chiangr/bingbong/firmware/bingbong_pcb/_bg95_pinout.png

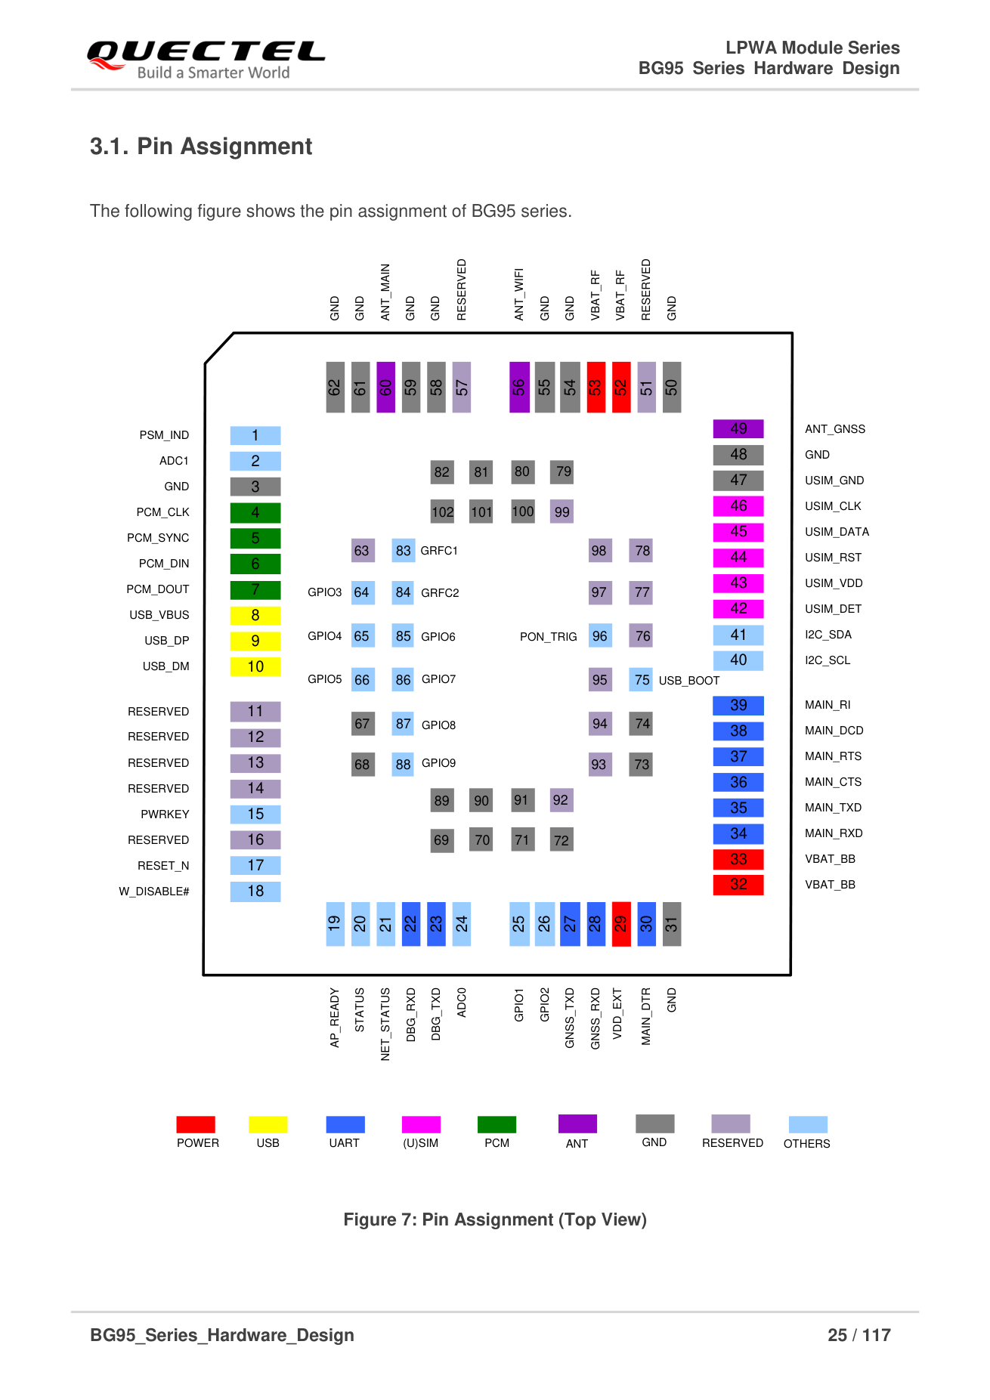
firmware/bingbong_pcb/_bg95_pinout.png
