chiangr/bingbong/firmware/bingbong_pcb/_dfe_land.png

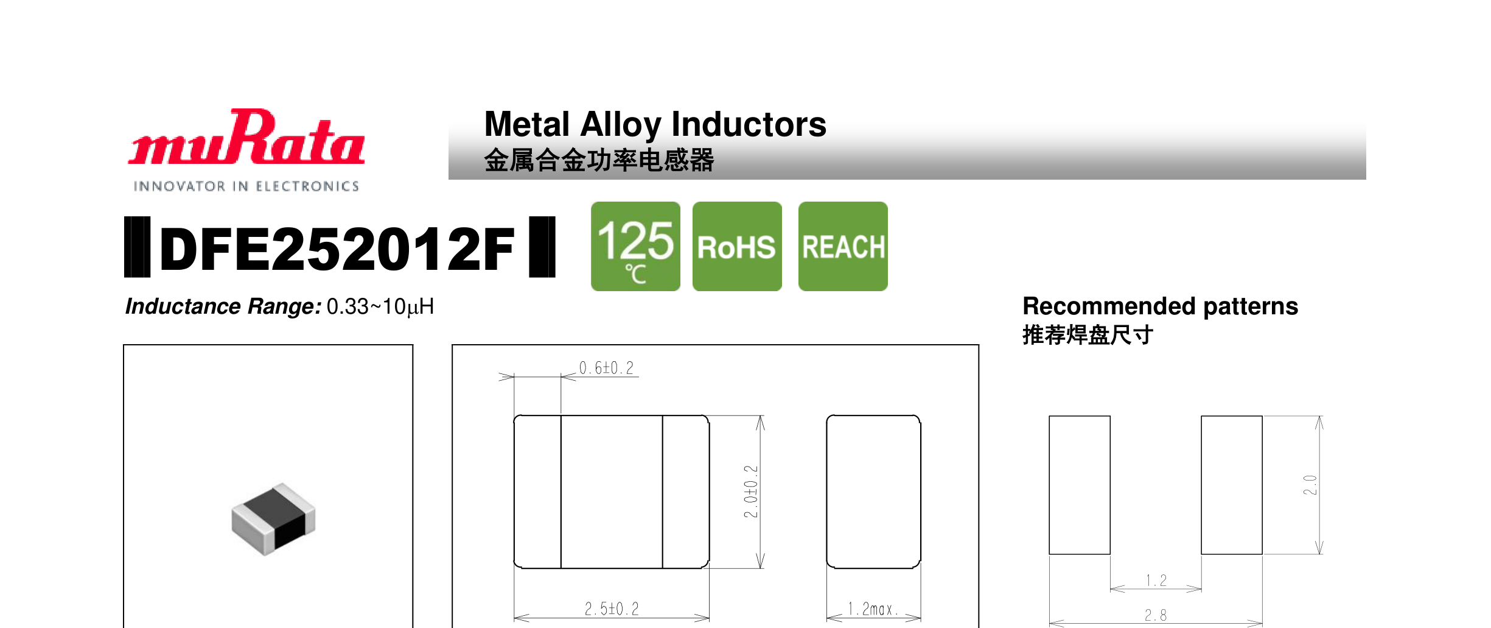
firmware/bingbong_pcb/_dfe_land.png
