chiangr/bingbong/firmware/bingbong_pcb/_esp_land.png

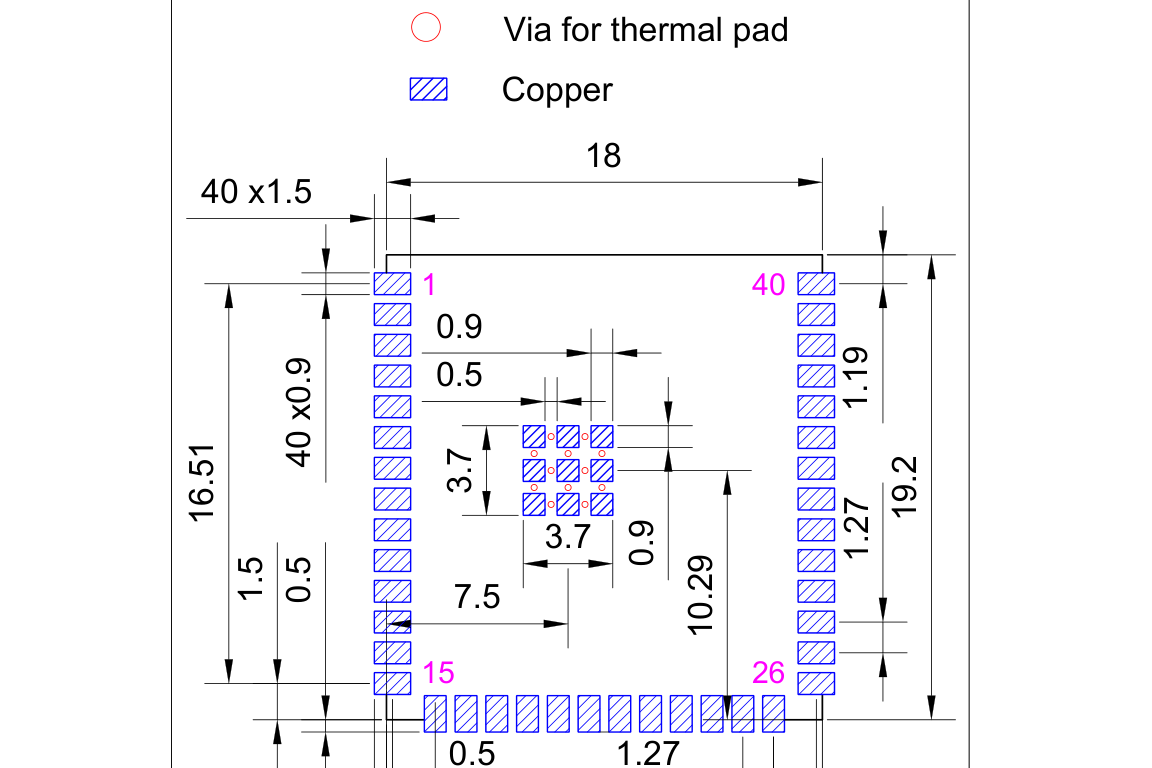
firmware/bingbong_pcb/_esp_land.png
