chiangr/bingbong/firmware/bingbong_pcb/_mech/a35s-07.png

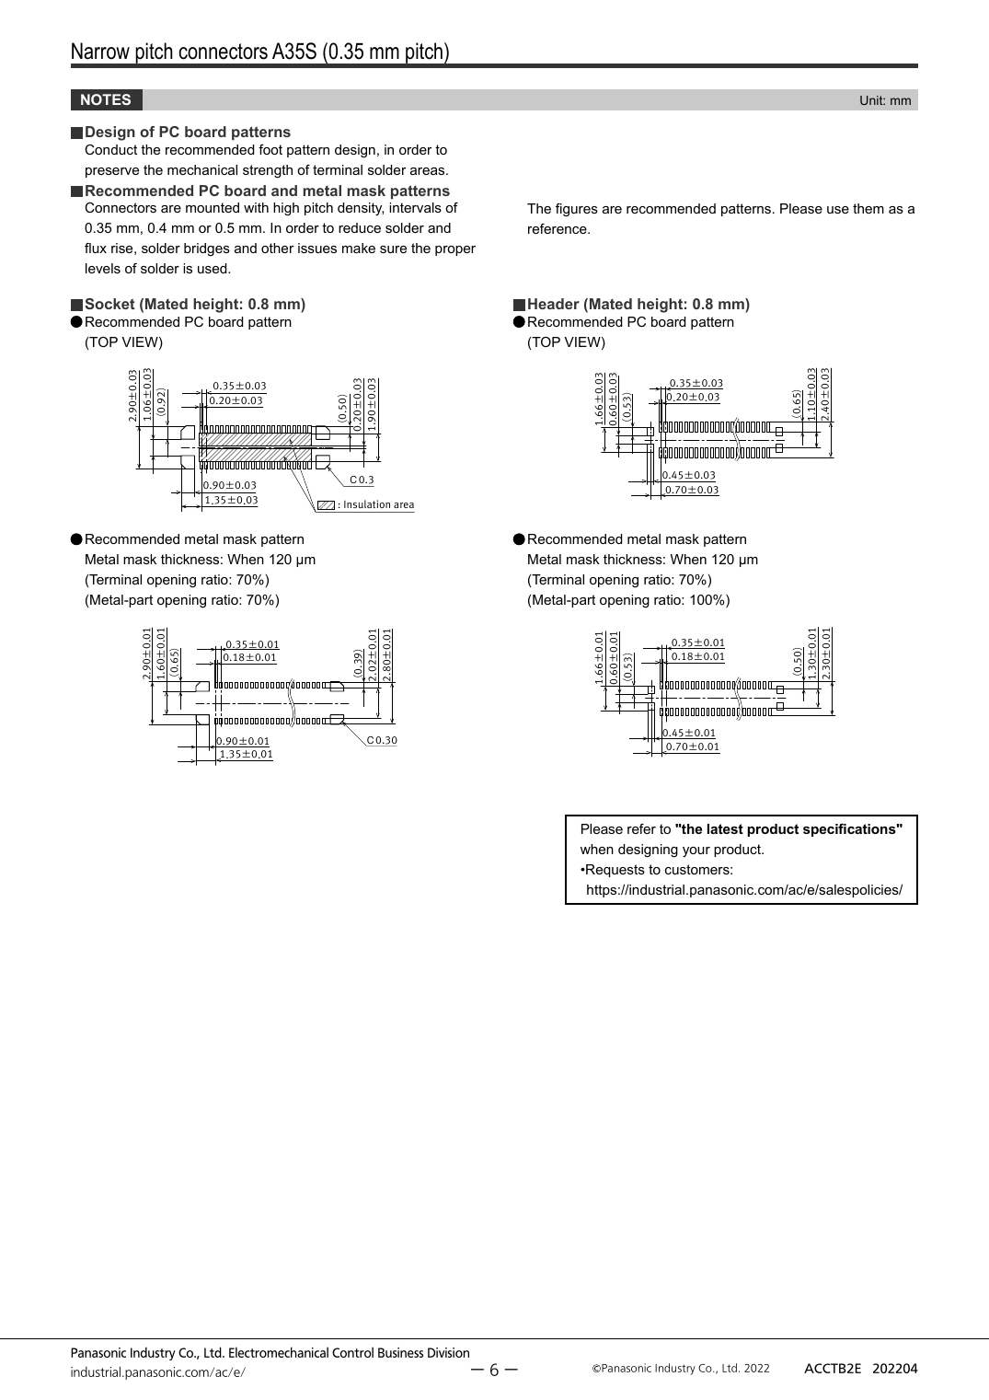
firmware/bingbong_pcb/_mech/a35s-07.png
