chiangr/bingbong/firmware/bingbong_pcb/_mech/bm28-04.png

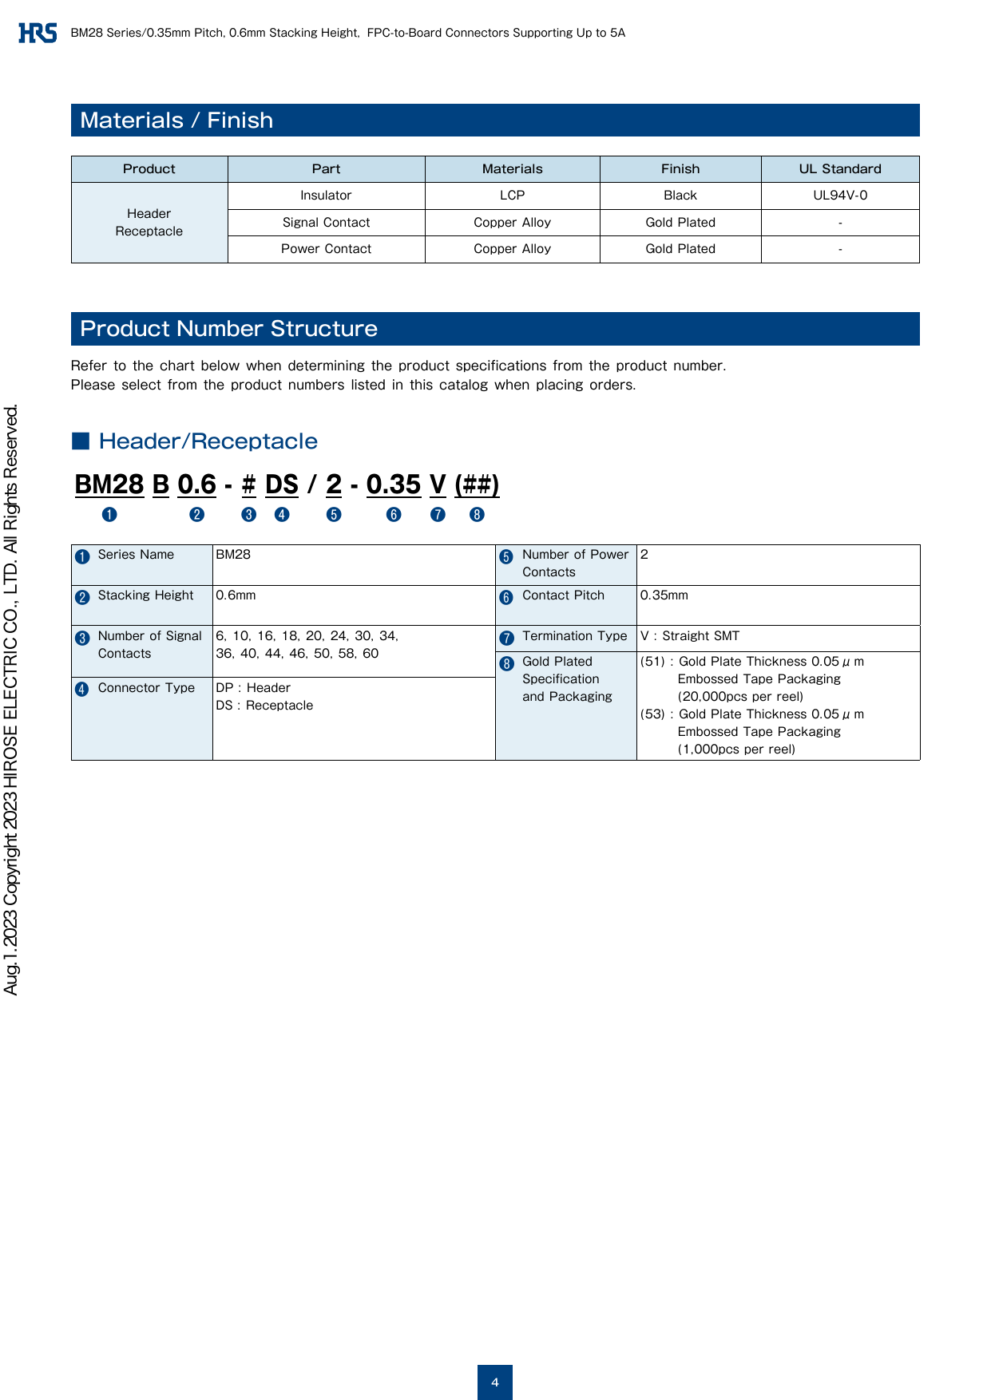
firmware/bingbong_pcb/_mech/bm28-04.png
