chiangr/bingbong/firmware/bingbong_pcb/_mech/bm28-05.png

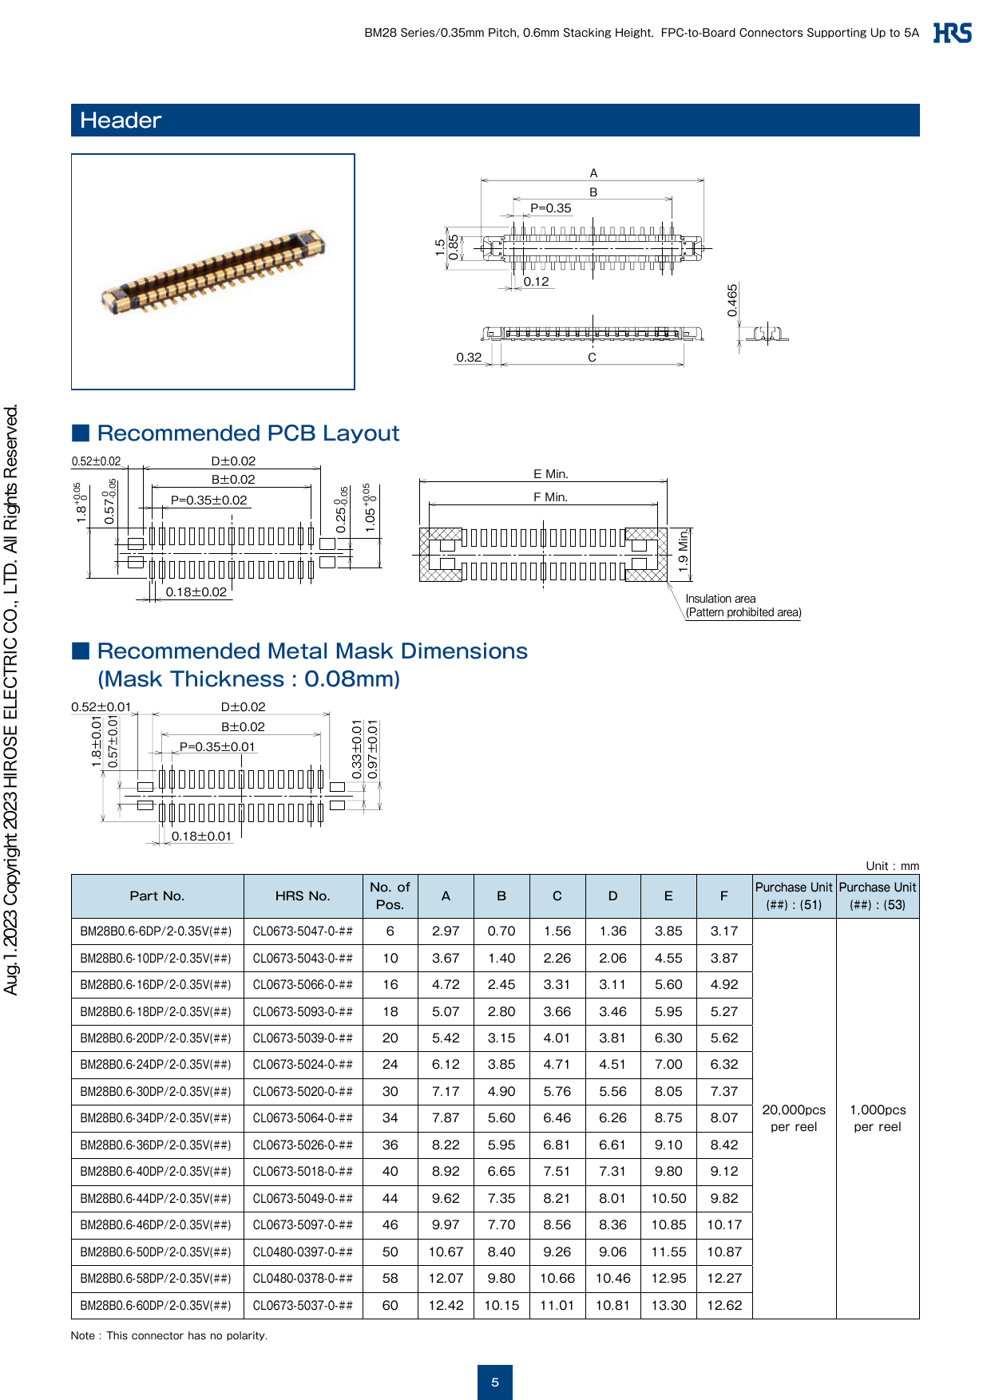
firmware/bingbong_pcb/_mech/bm28-05.png
