chiangr/bingbong/firmware/bingbong_pcb/_mech/ck/p4-4.png

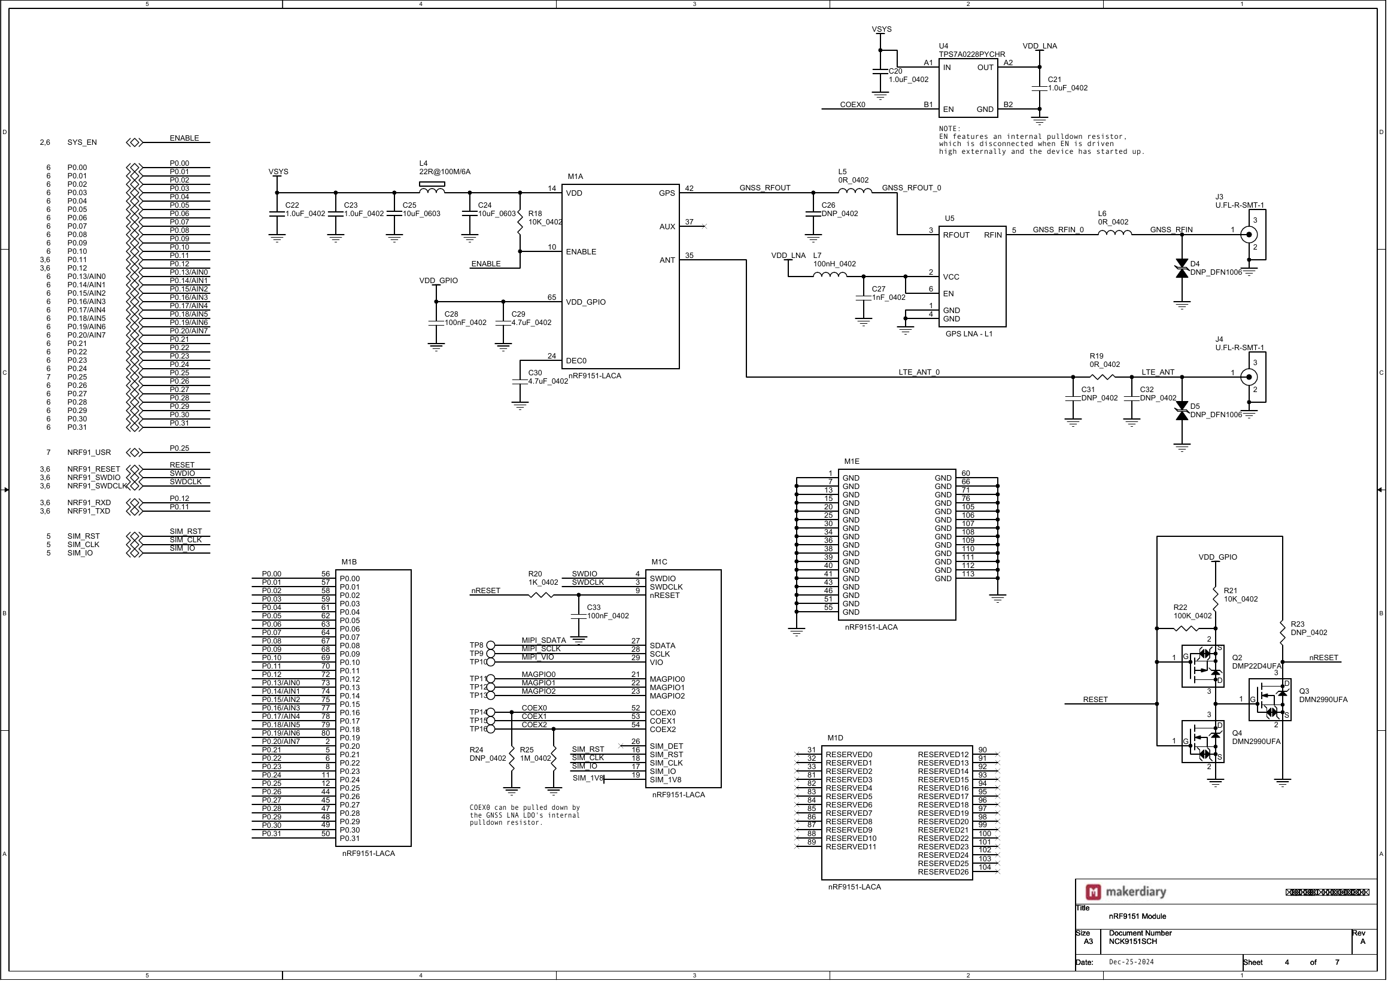
firmware/bingbong_pcb/_mech/ck/p4-4.png
