chiangr/bingbong/firmware/bingbong_pcb/_mech/etsi-mff2-16.png

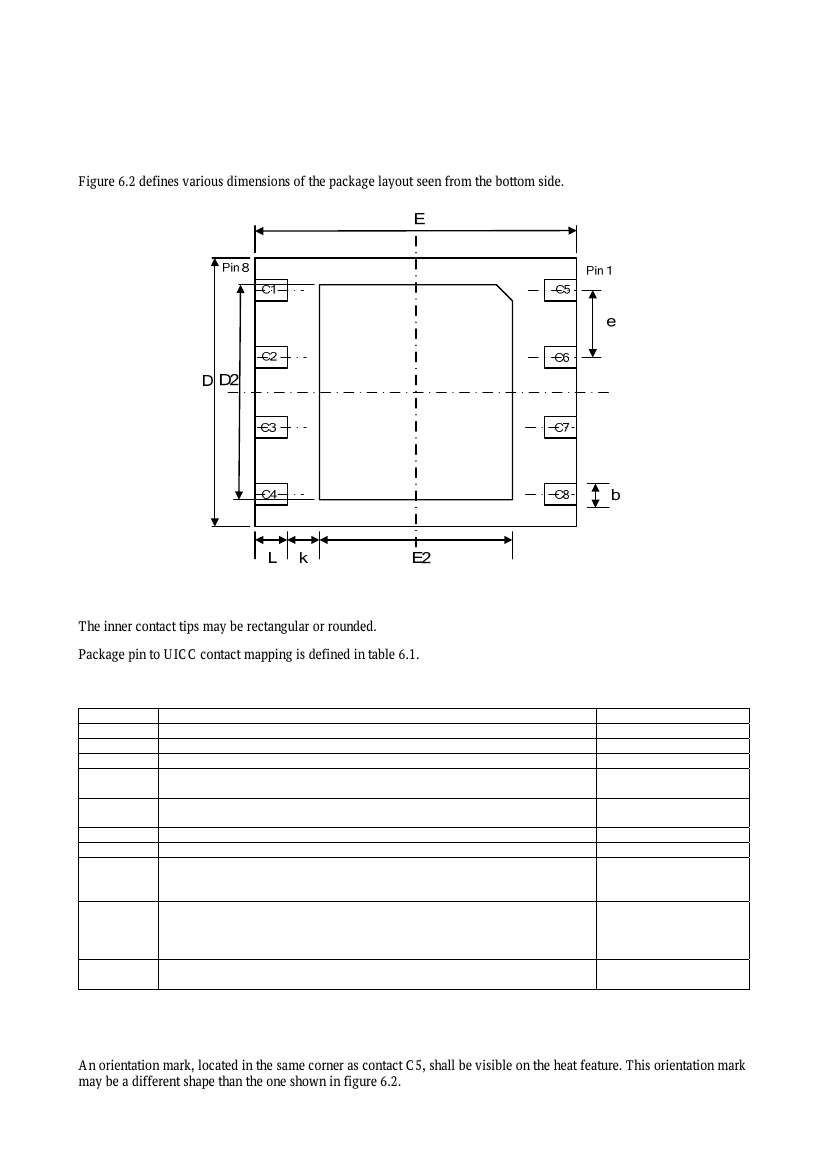
firmware/bingbong_pcb/_mech/etsi-mff2-16.png
