chiangr/bingbong/firmware/bingbong_pcb/_mech/etsi-mff2-19.png

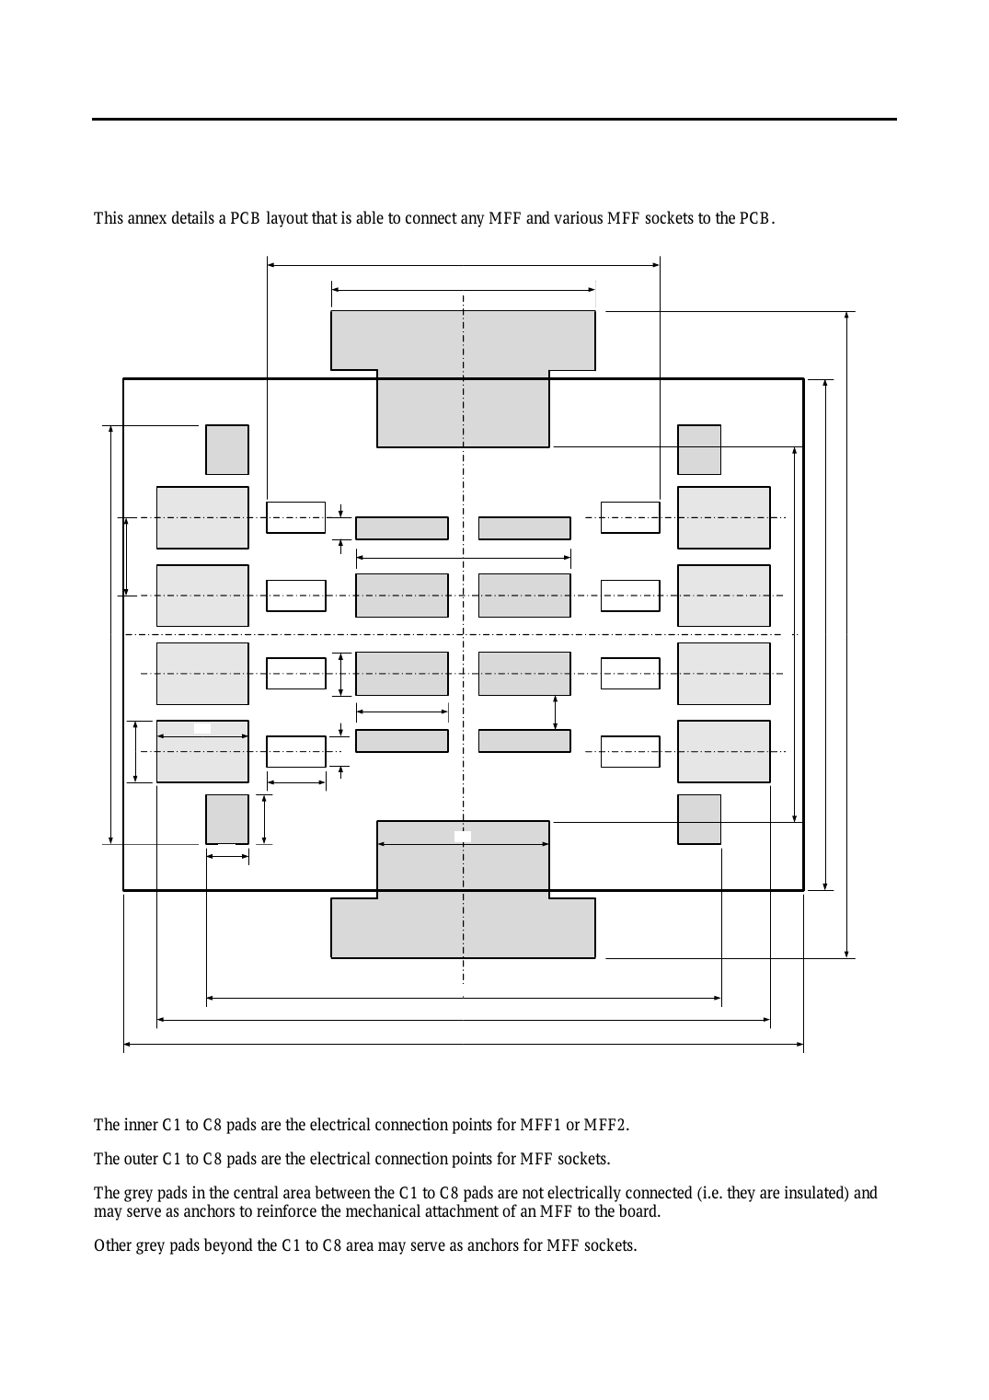
firmware/bingbong_pcb/_mech/etsi-mff2-19.png
