chiangr/bingbong/firmware/bingbong_pcb/_mech/fp/bq-51.png

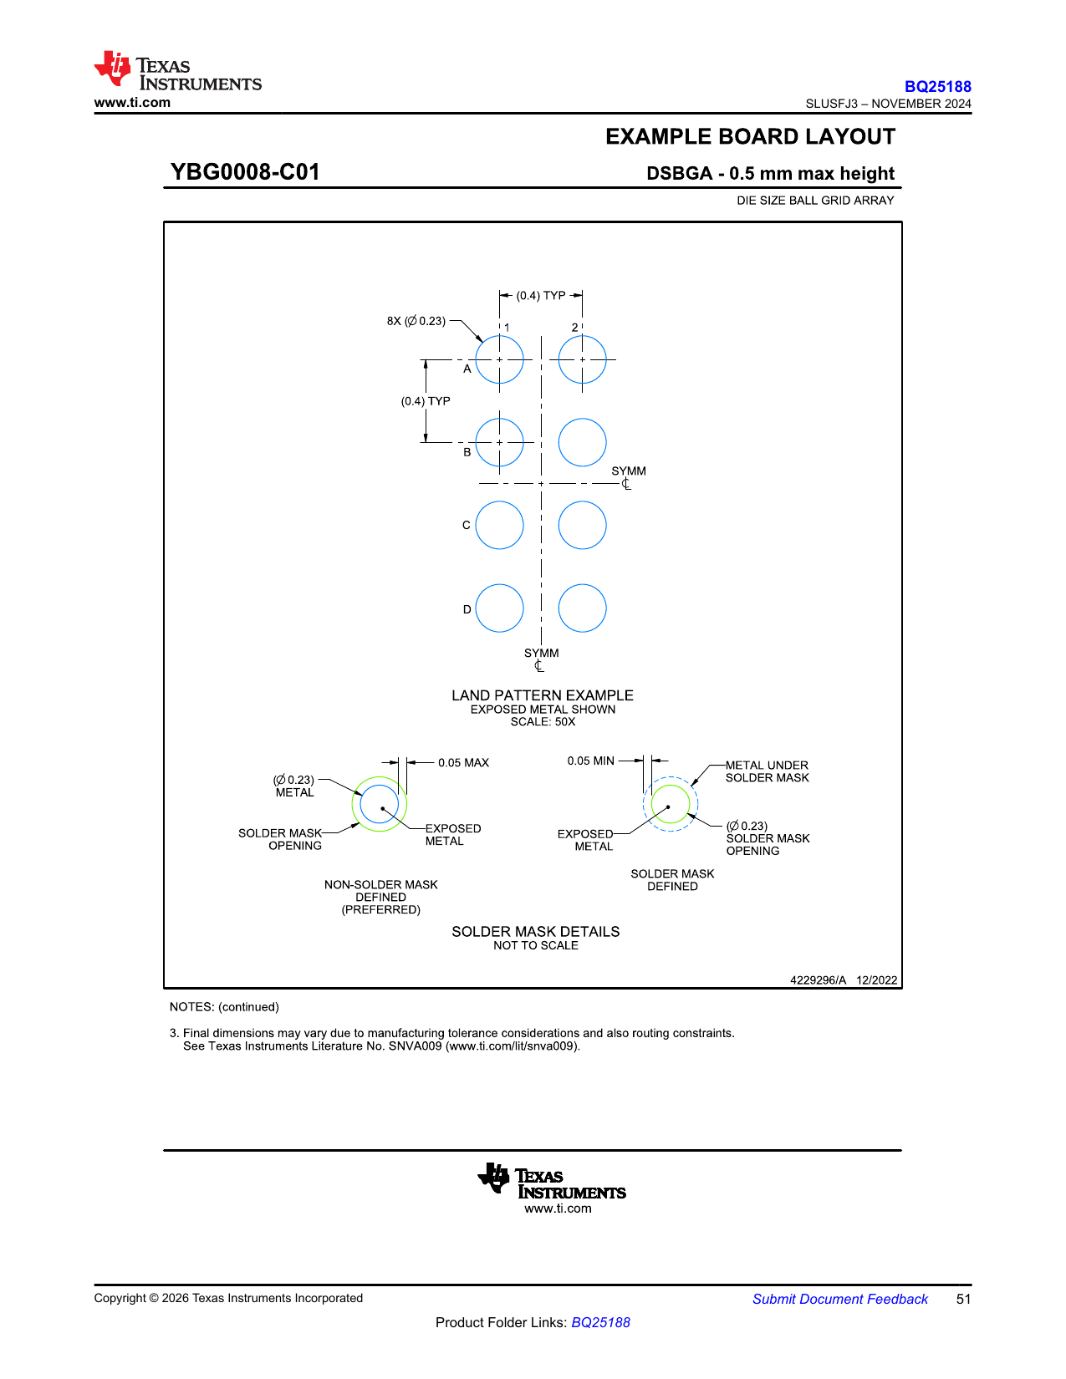
firmware/bingbong_pcb/_mech/fp/bq-51.png
