chiangr/bingbong/firmware/bingbong_pcb/_mech/fp/bq-52.png

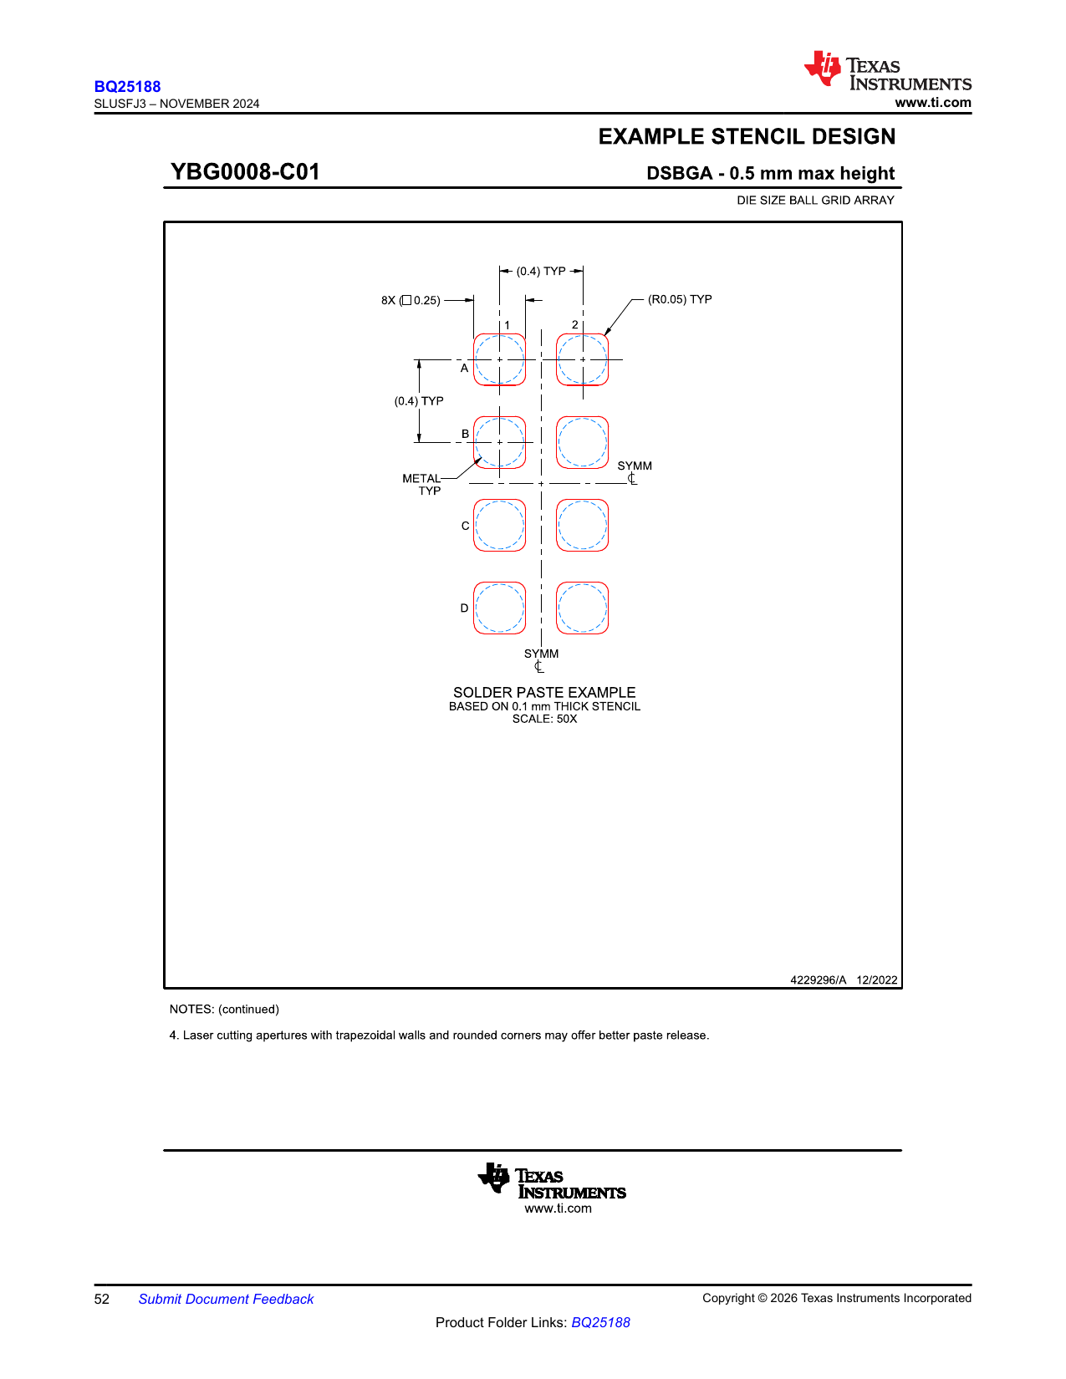
firmware/bingbong_pcb/_mech/fp/bq-52.png
