chiangr/bingbong/firmware/bingbong_pcb/_mech/fp/dmr-35.png

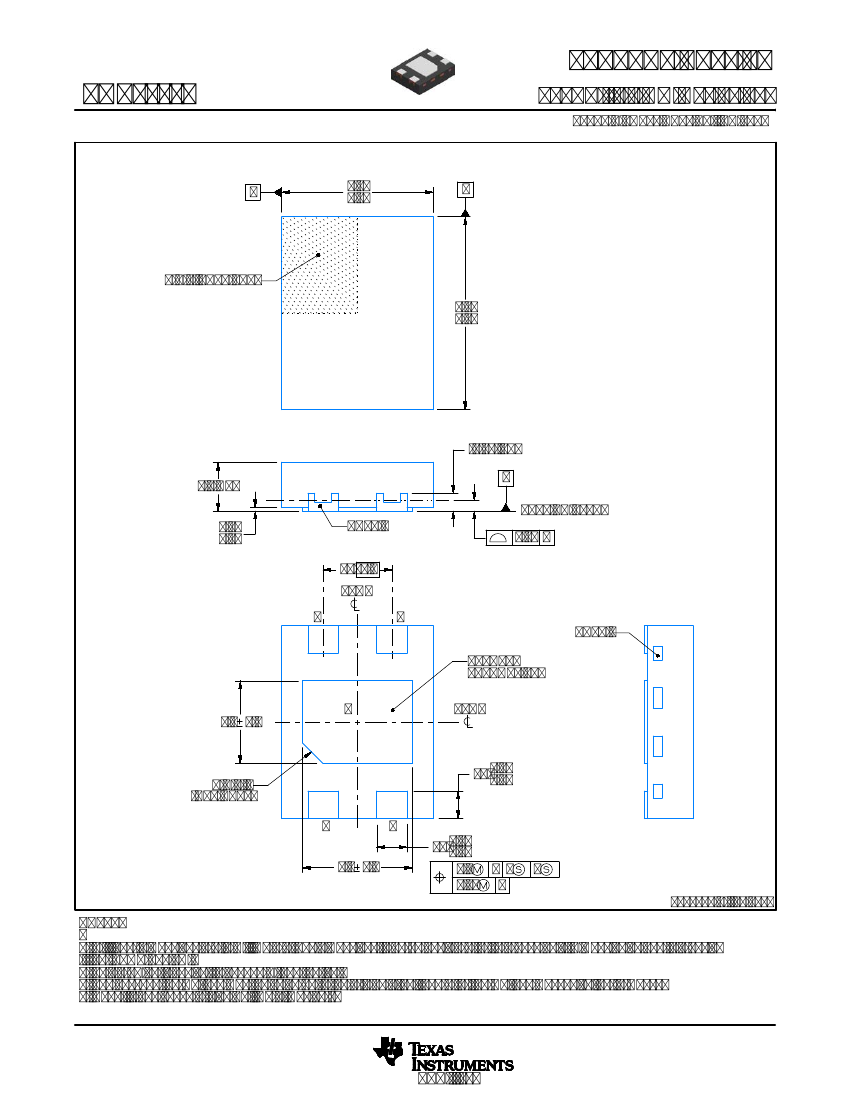
firmware/bingbong_pcb/_mech/fp/dmr-35.png
