chiangr/bingbong/firmware/bingbong_pcb/_mech/fp/dmr-38.png

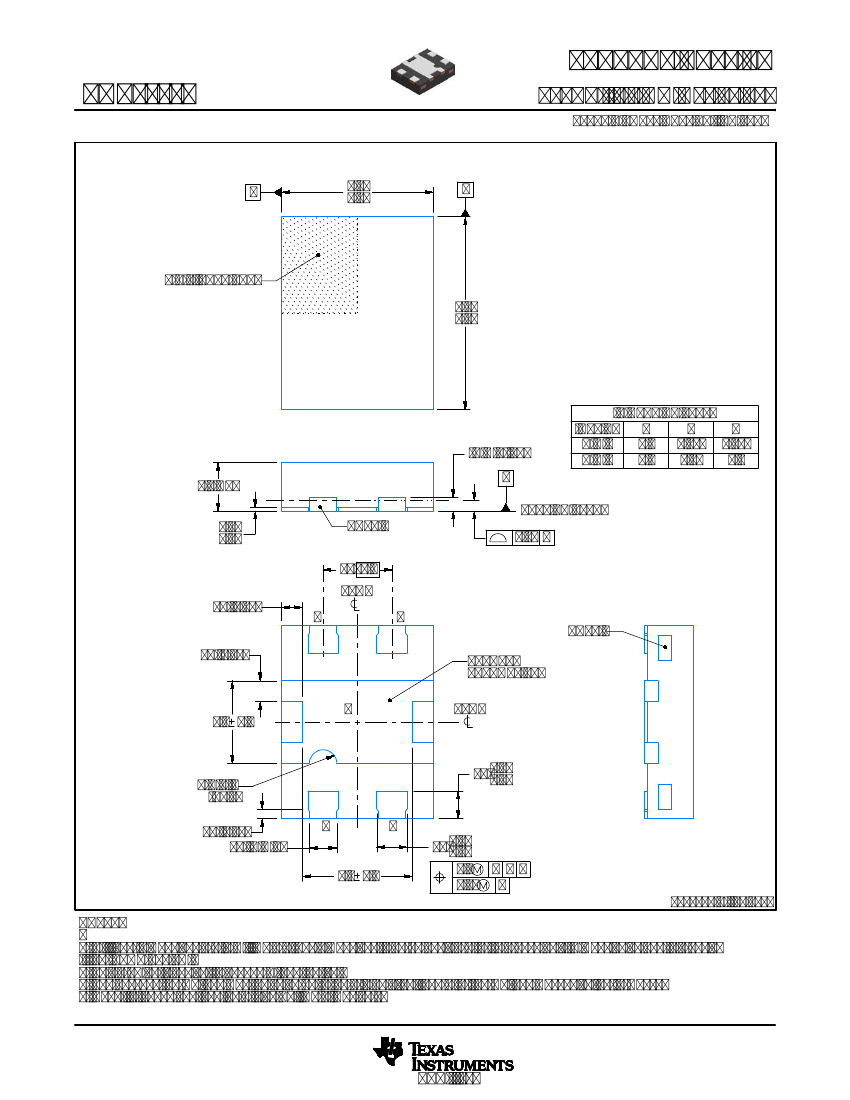
firmware/bingbong_pcb/_mech/fp/dmr-38.png
