chiangr/bingbong/firmware/bingbong_pcb/_mech/fp/dmr-40.png

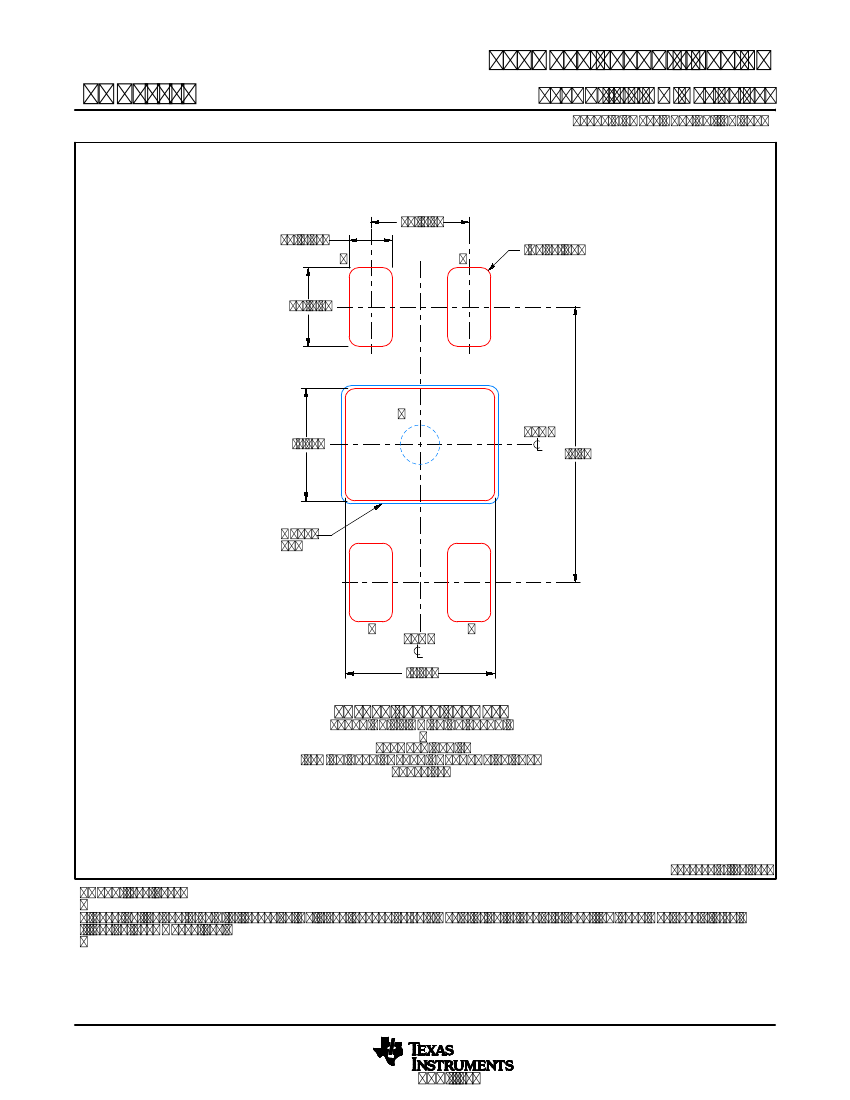
firmware/bingbong_pcb/_mech/fp/dmr-40.png
