chiangr/bingbong/firmware/bingbong_pcb/_mech/fp/dmr-41.png

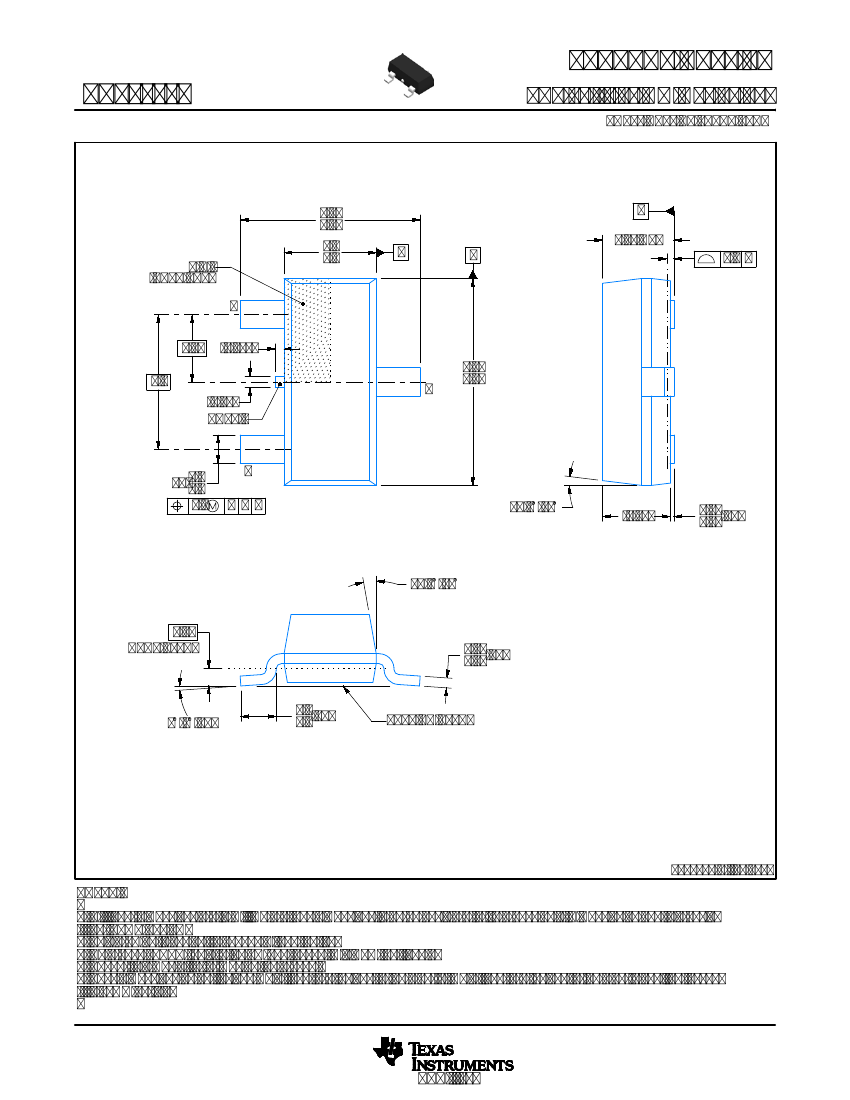
firmware/bingbong_pcb/_mech/fp/dmr-41.png
