chiangr/bingbong/firmware/bingbong_pcb/_mech/fp/drv-72.png

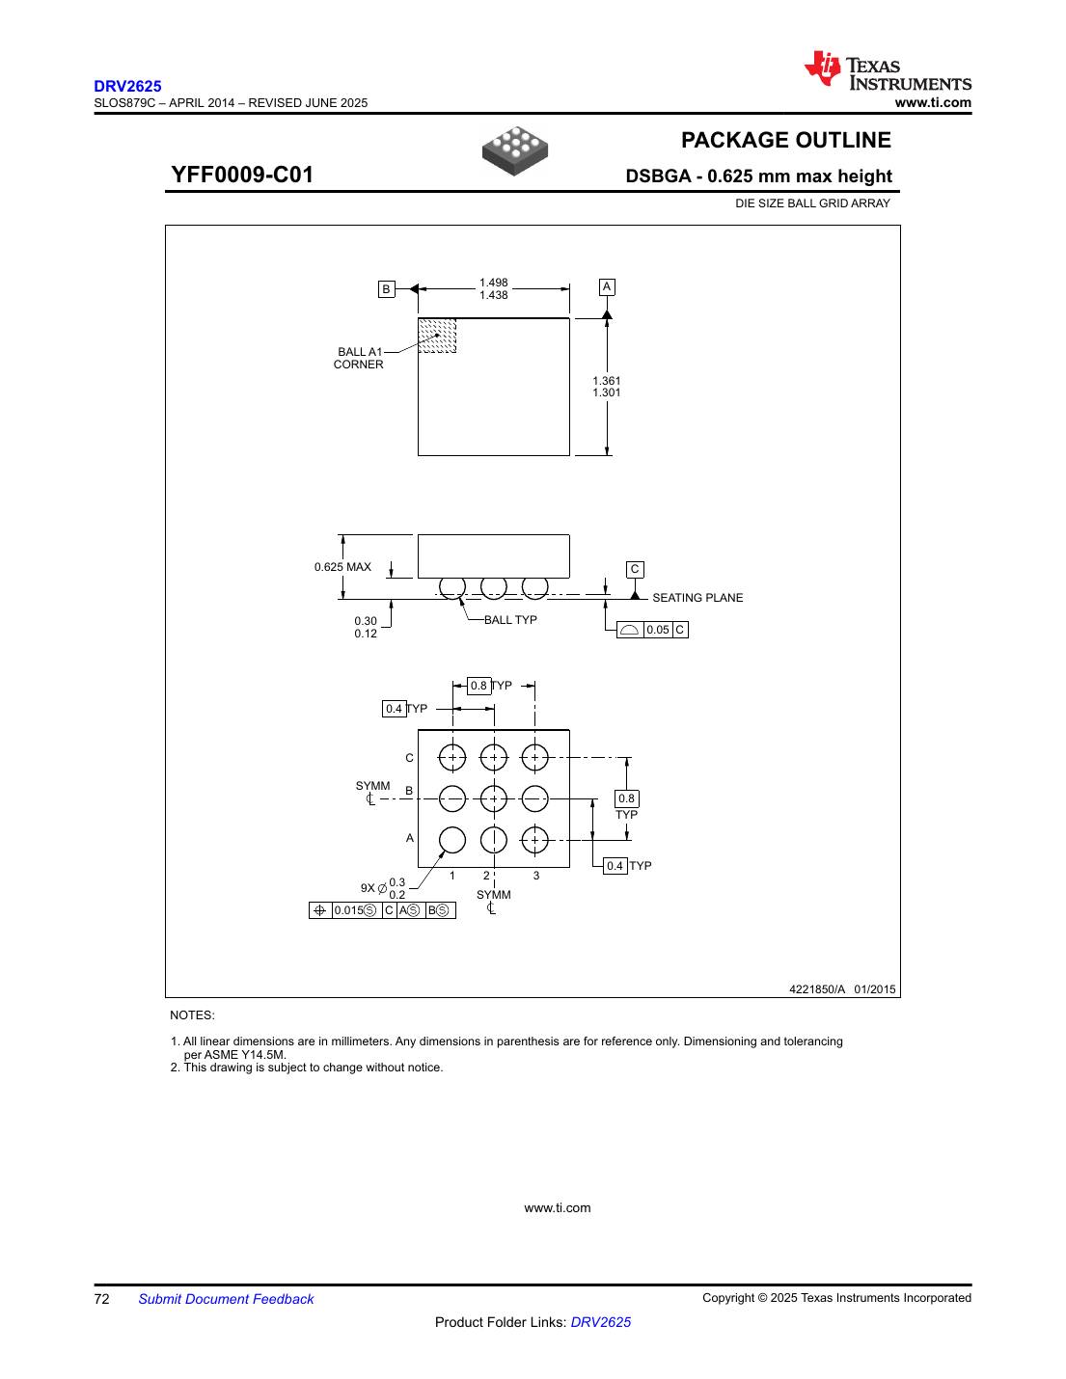
firmware/bingbong_pcb/_mech/fp/drv-72.png
