chiangr/bingbong/firmware/bingbong_pcb/_mech/fp/drv-73.png

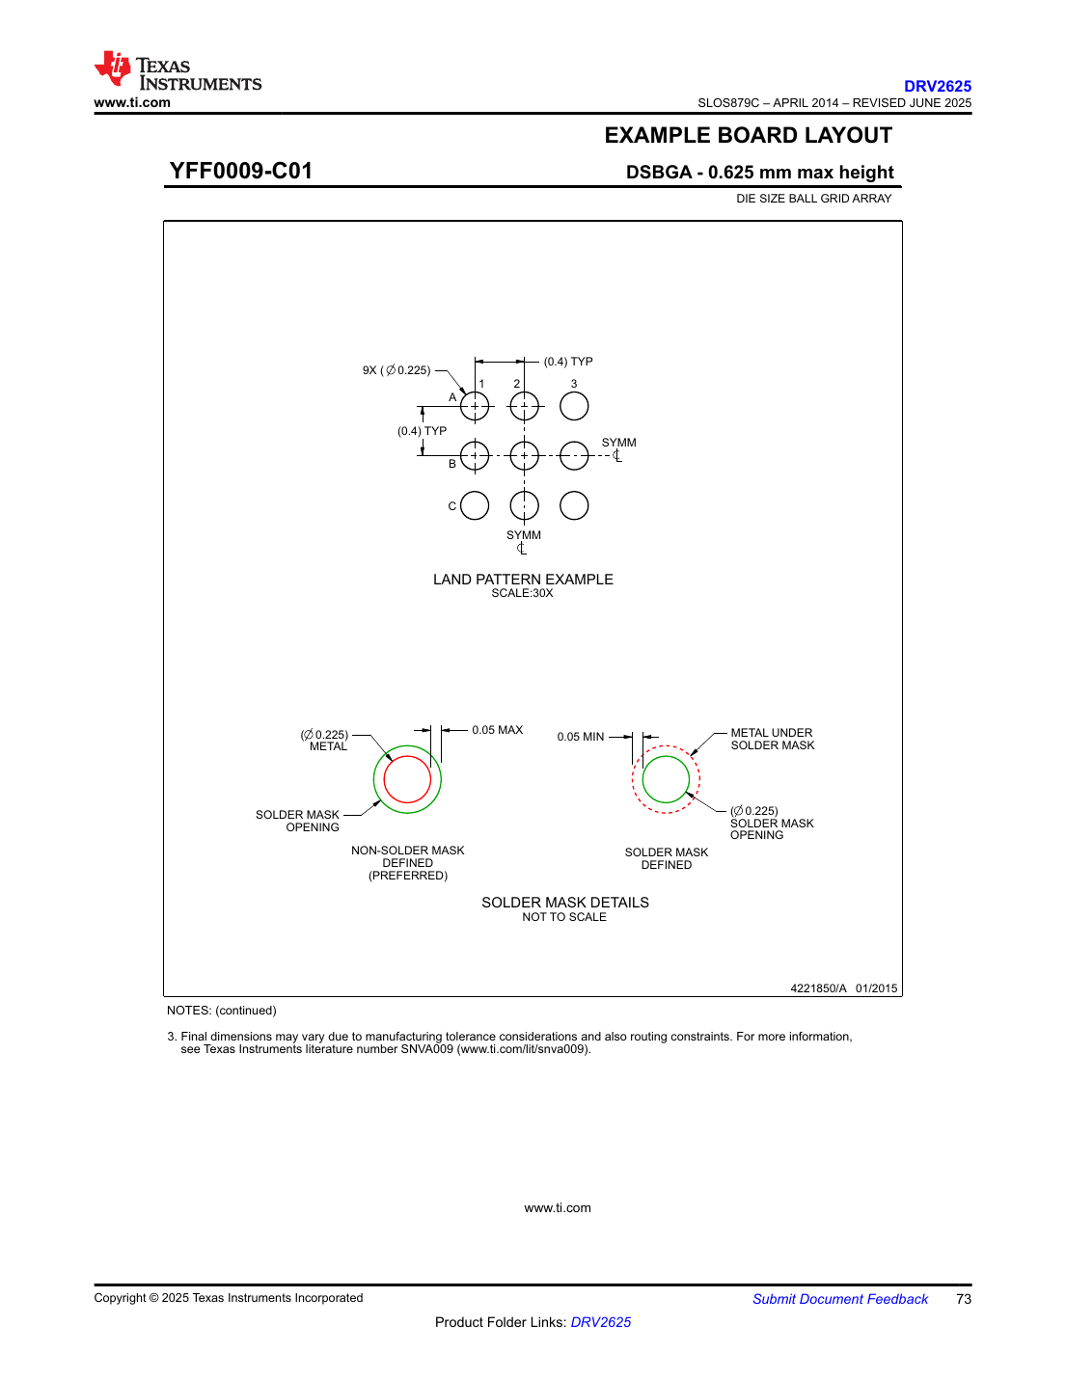
firmware/bingbong_pcb/_mech/fp/drv-73.png
