chiangr/bingbong/firmware/bingbong_pcb/_mech/fp/dya-24.png

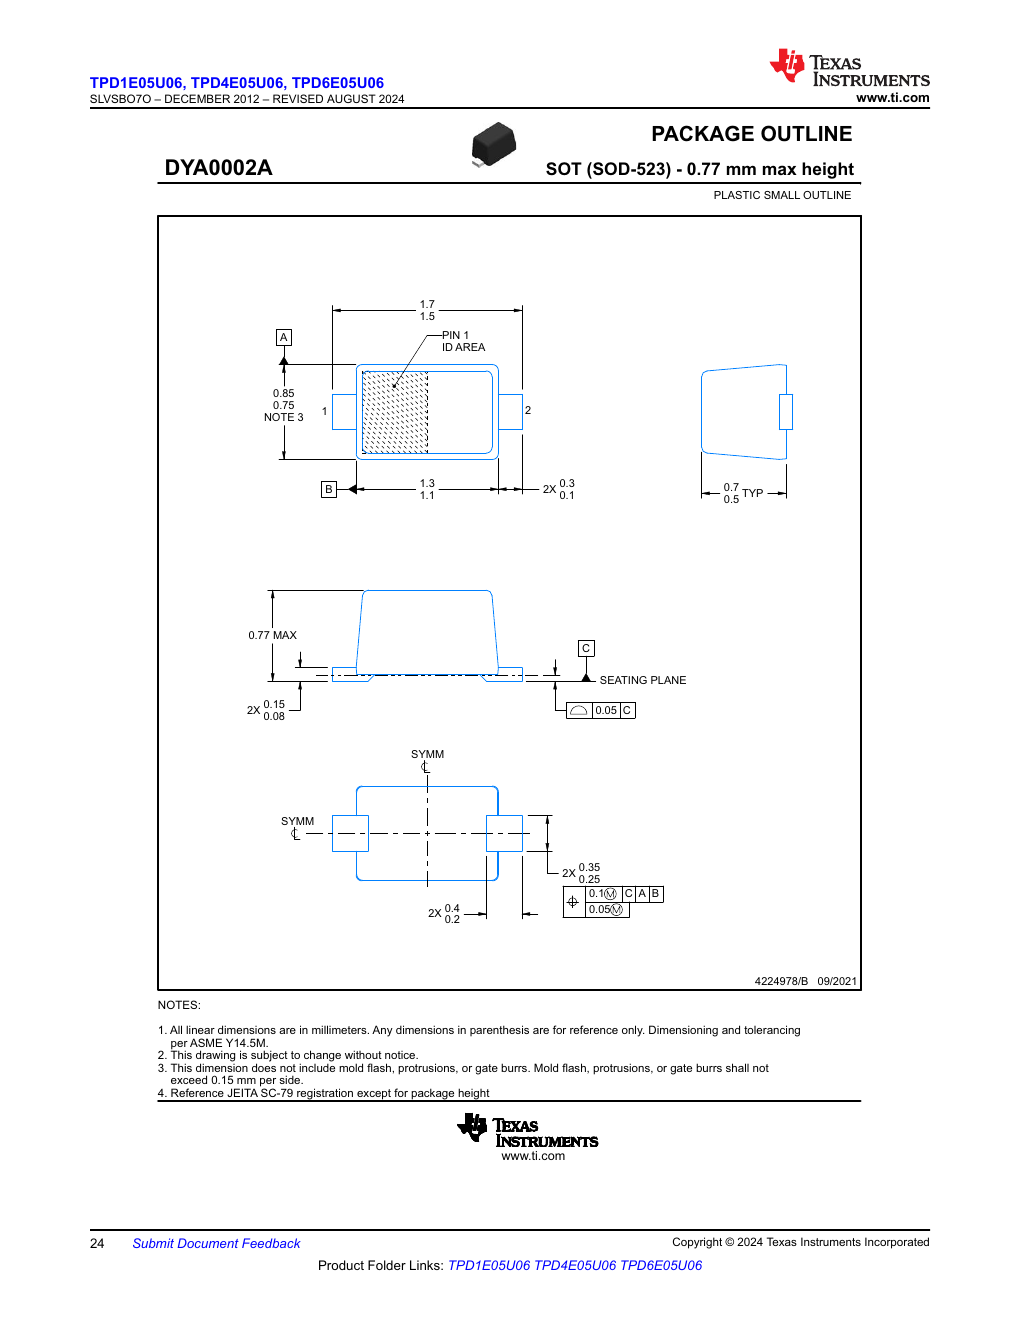
firmware/bingbong_pcb/_mech/fp/dya-24.png
