chiangr/bingbong/firmware/bingbong_pcb/_mech/fp/q/as_ball.png

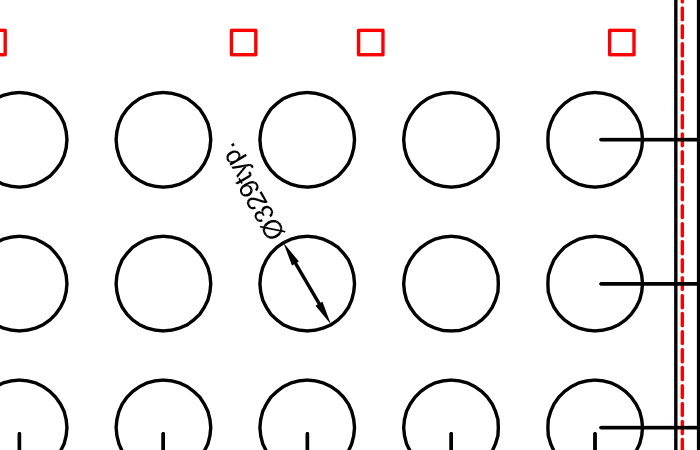
firmware/bingbong_pcb/_mech/fp/q/as_ball.png
