chiangr/bingbong/firmware/bingbong_pcb/_mech/fp/q/as_side.png

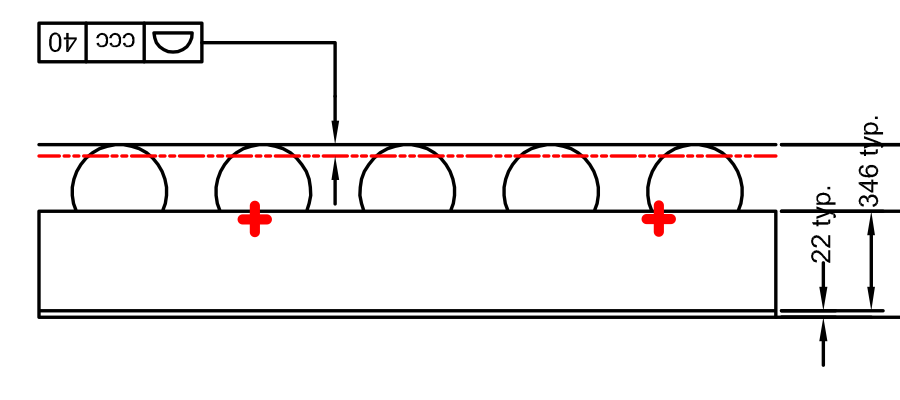
firmware/bingbong_pcb/_mech/fp/q/as_side.png
