chiangr/bingbong/firmware/bingbong_pcb/_mech/fp/q/drv5032_p36.pdf.png

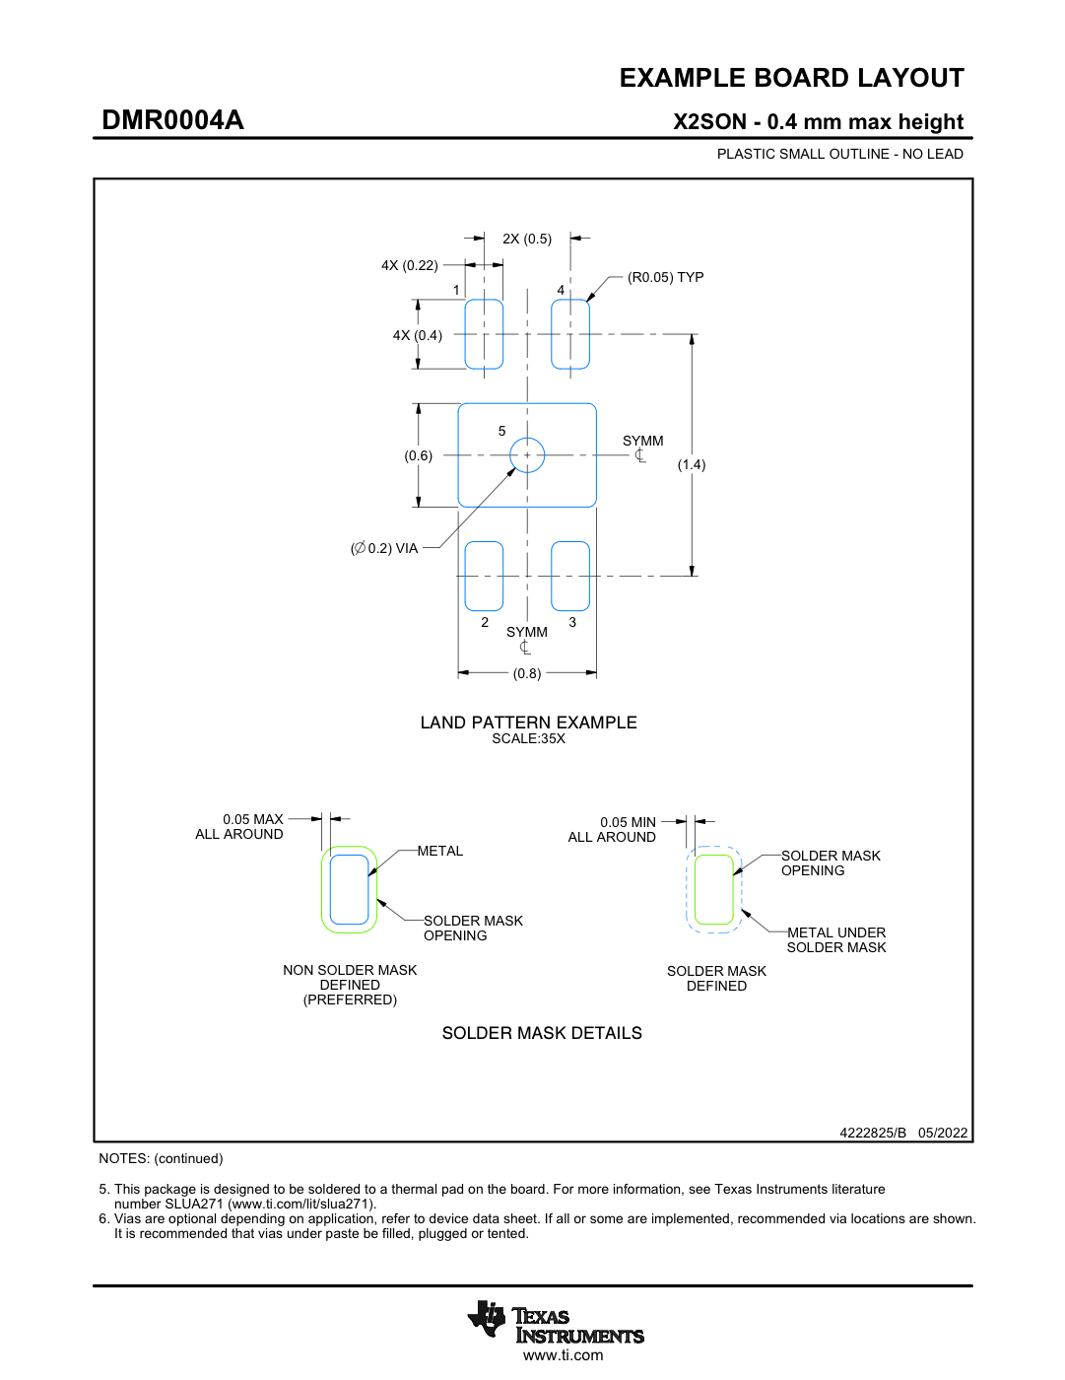
firmware/bingbong_pcb/_mech/fp/q/drv5032_p36.pdf.png
