chiangr/bingbong/firmware/bingbong_pcb/_mech/fp/q/mt_p33.pdf.png

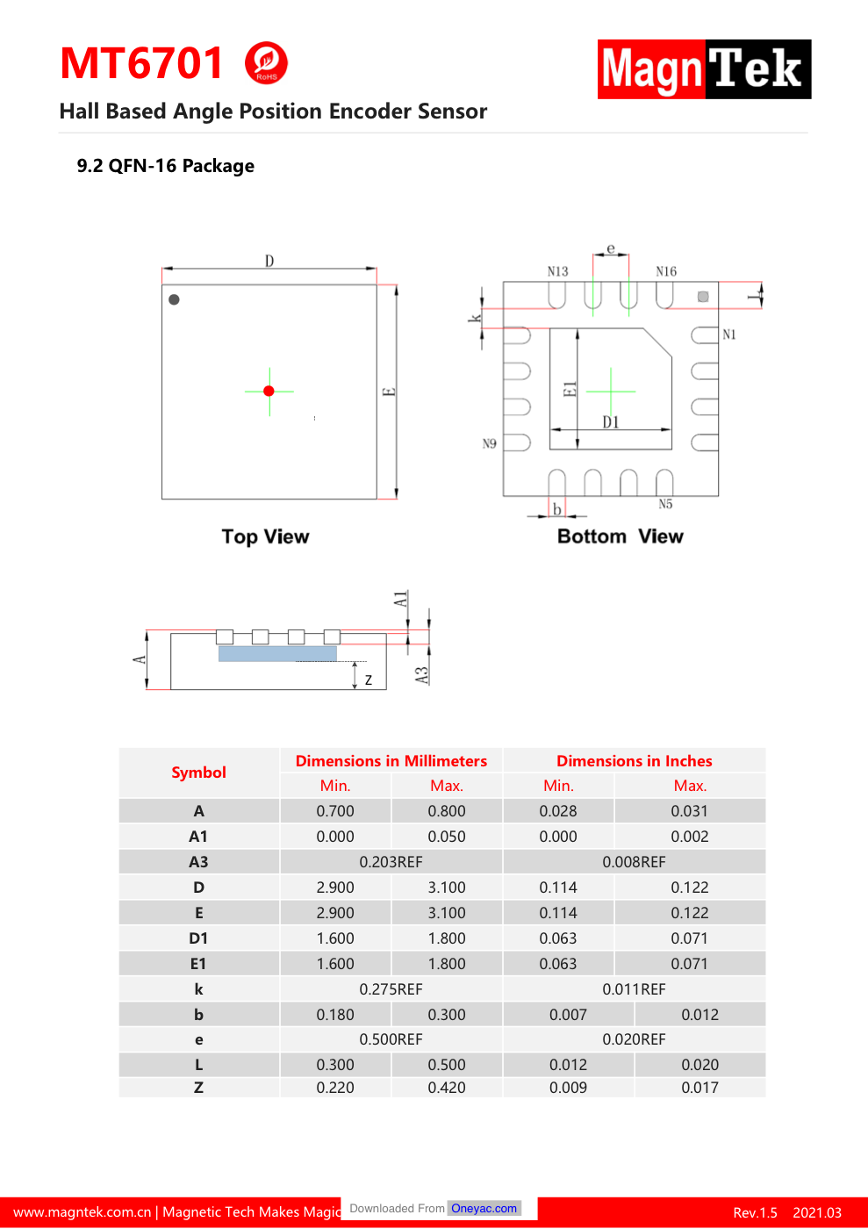
firmware/bingbong_pcb/_mech/fp/q/mt_p33.pdf.png
