chiangr/bingbong/firmware/bingbong_pcb/_mech/fp/q/mx_p81.pdf.png

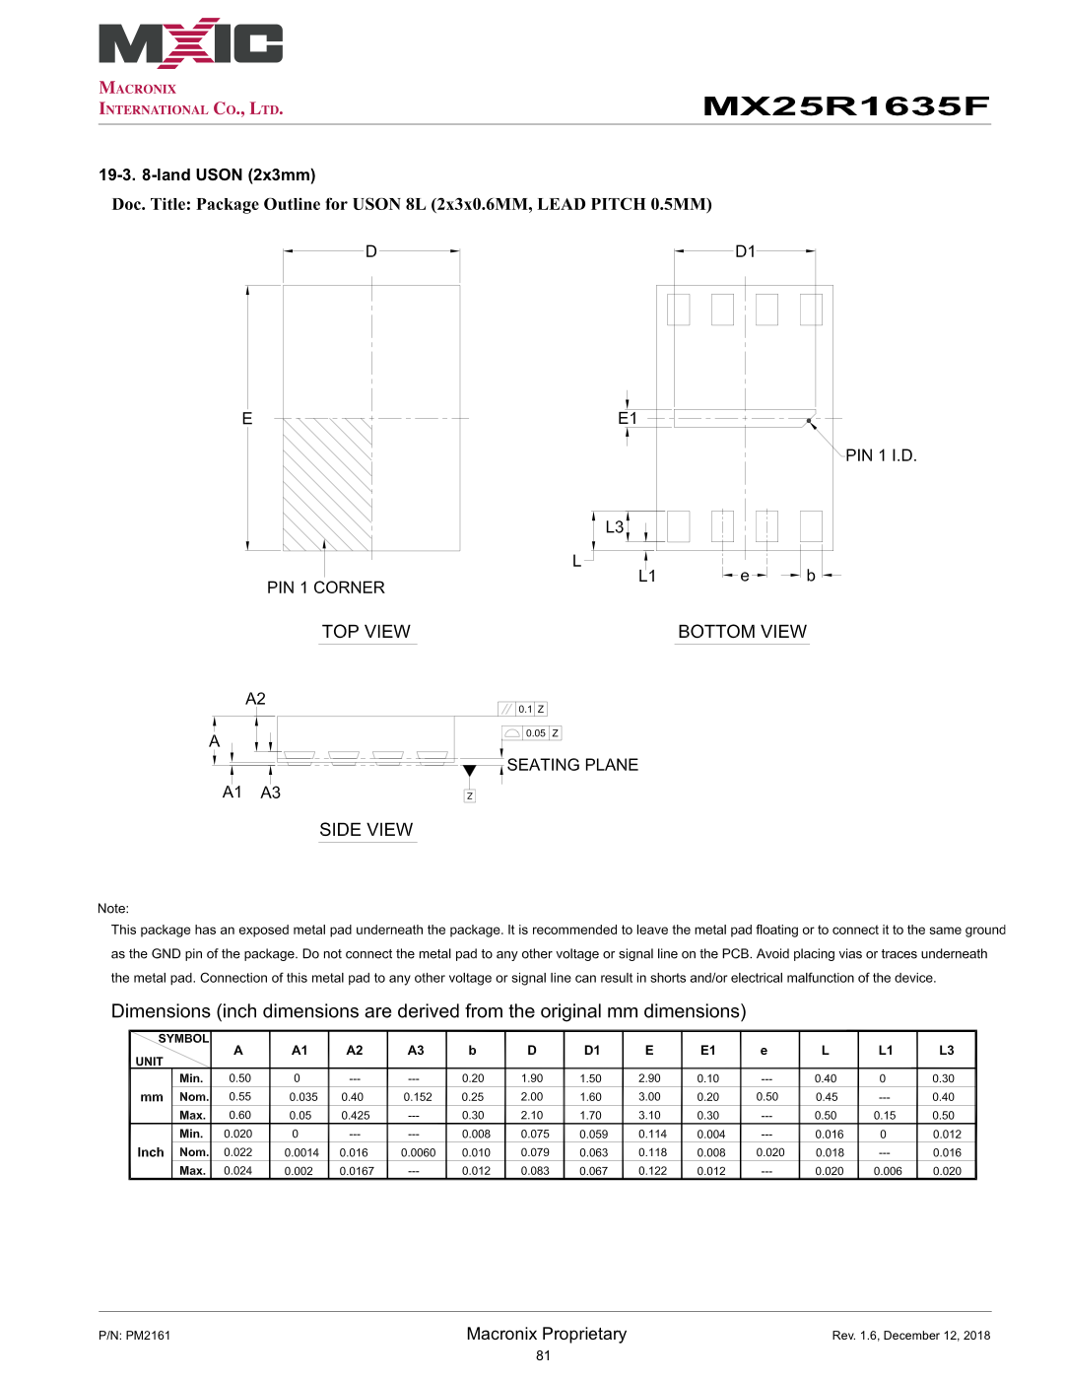
firmware/bingbong_pcb/_mech/fp/q/mx_p81.pdf.png
