chiangr/bingbong/firmware/bingbong_pcb/_mech/fp/q/w25_p67.pdf.png

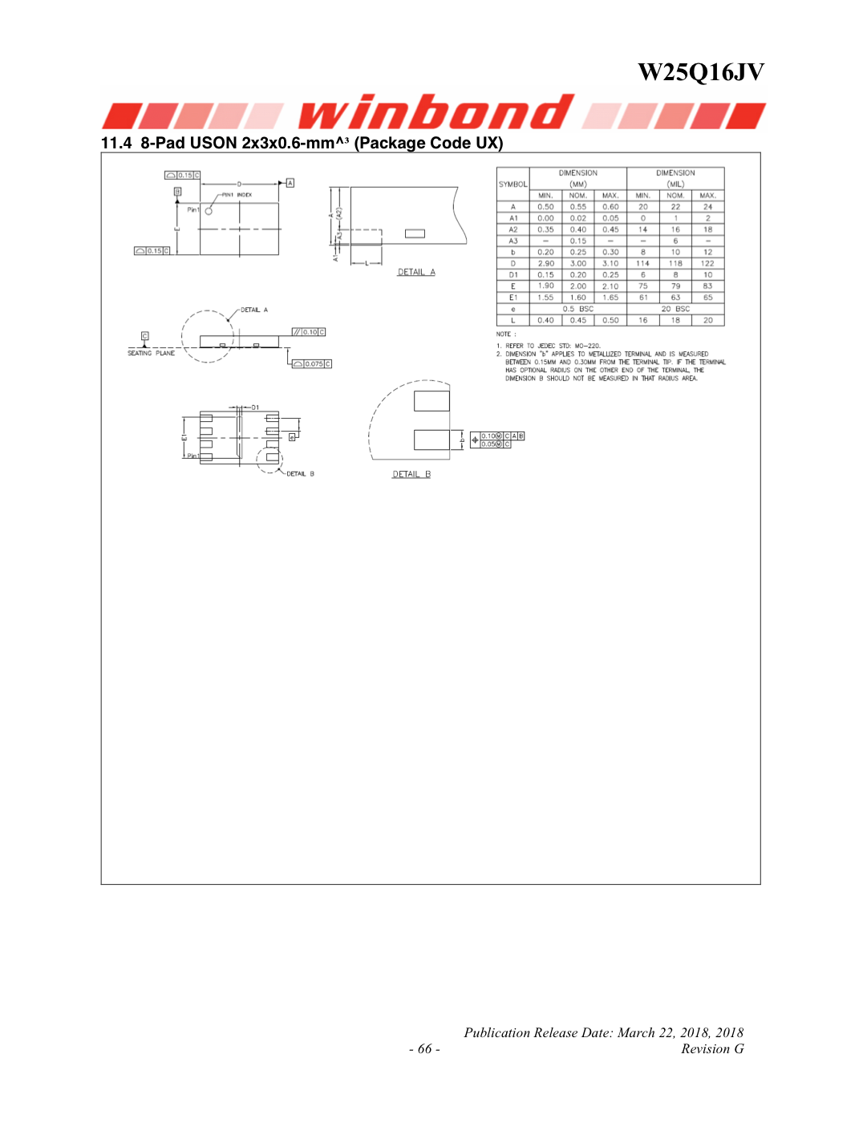
firmware/bingbong_pcb/_mech/fp/q/w25_p67.pdf.png
