chiangr/bingbong/firmware/bingbong_pcb/_mech/fp/t16-24.png

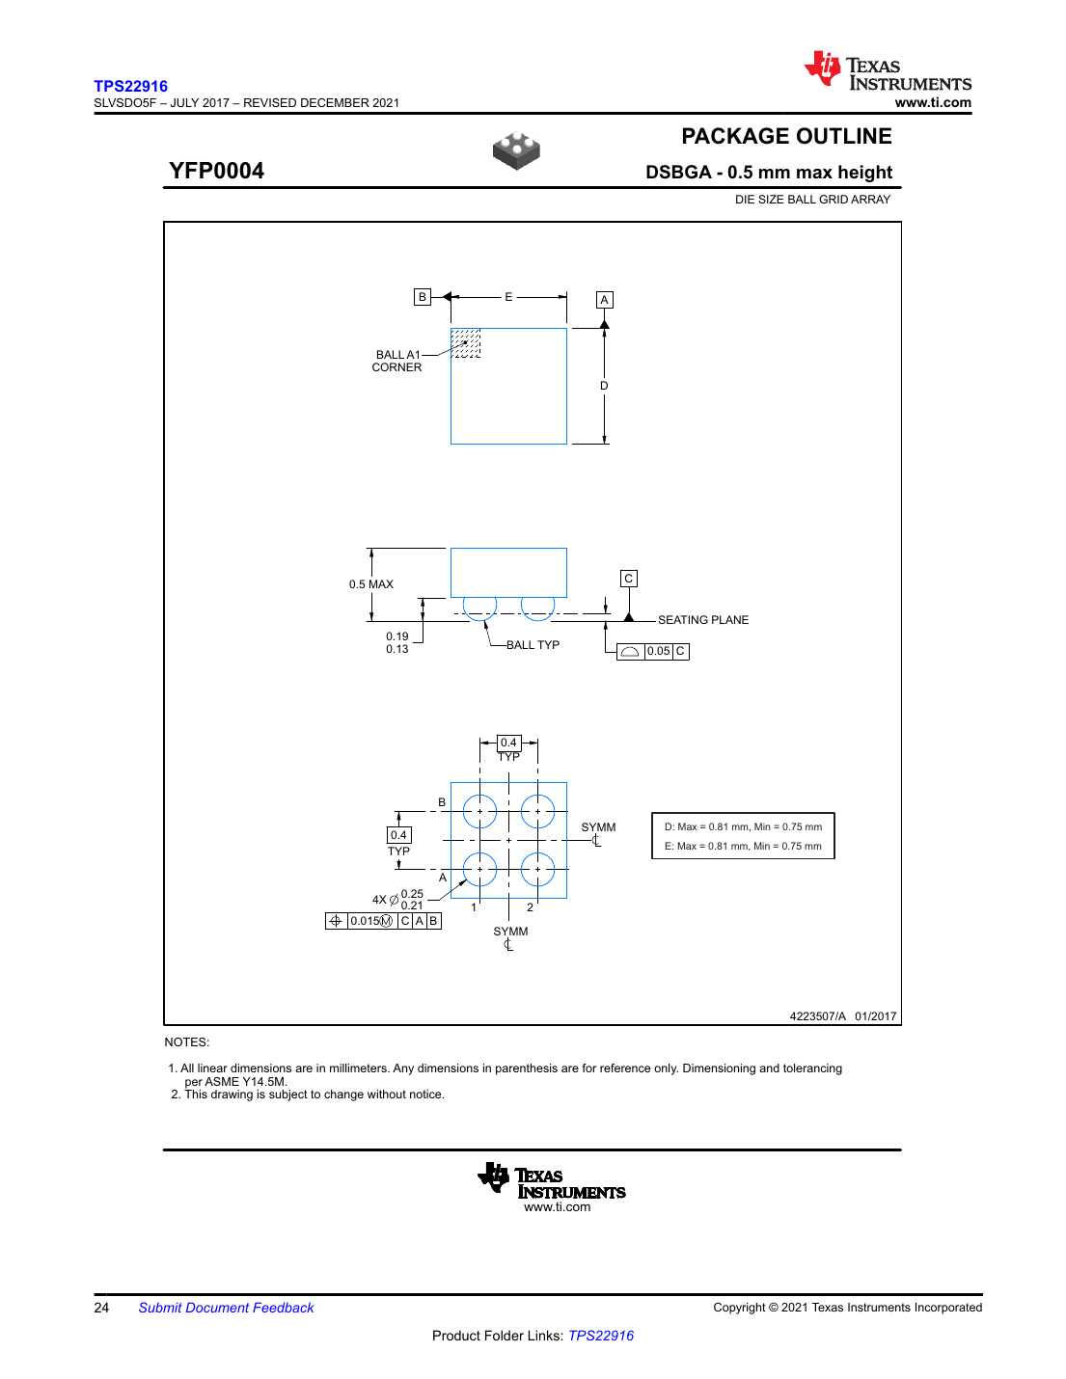
firmware/bingbong_pcb/_mech/fp/t16-24.png
