chiangr/bingbong/firmware/bingbong_pcb/_mech/fp/t16s-26.png

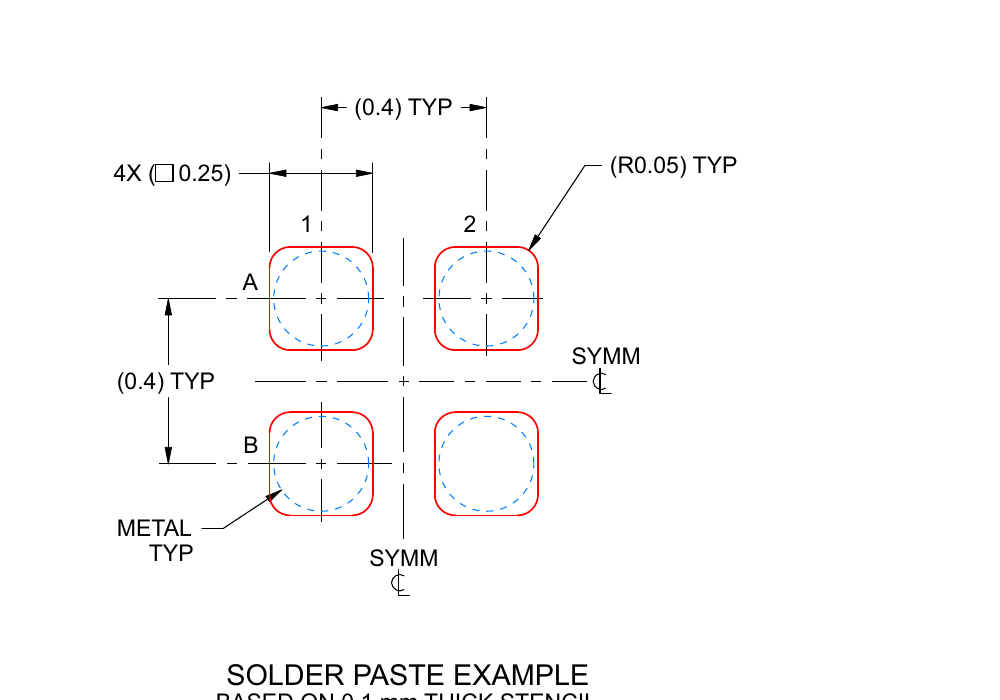
firmware/bingbong_pcb/_mech/fp/t16s-26.png
