chiangr/bingbong/firmware/bingbong_pcb/_mech/fp/tpd-32.png

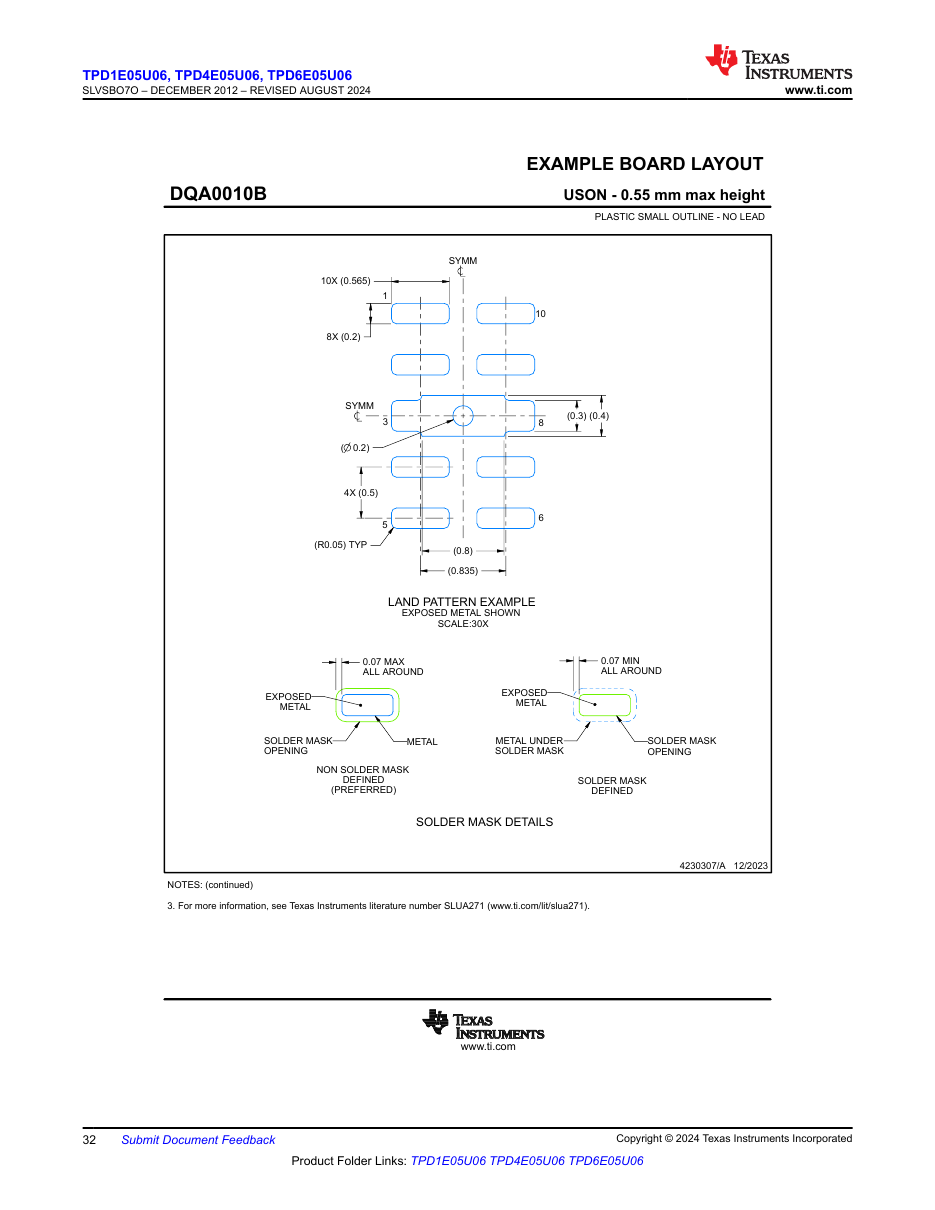
firmware/bingbong_pcb/_mech/fp/tpd-32.png
