chiangr/bingbong/firmware/bingbong_pcb/_mech/fp/tps62840-36.png

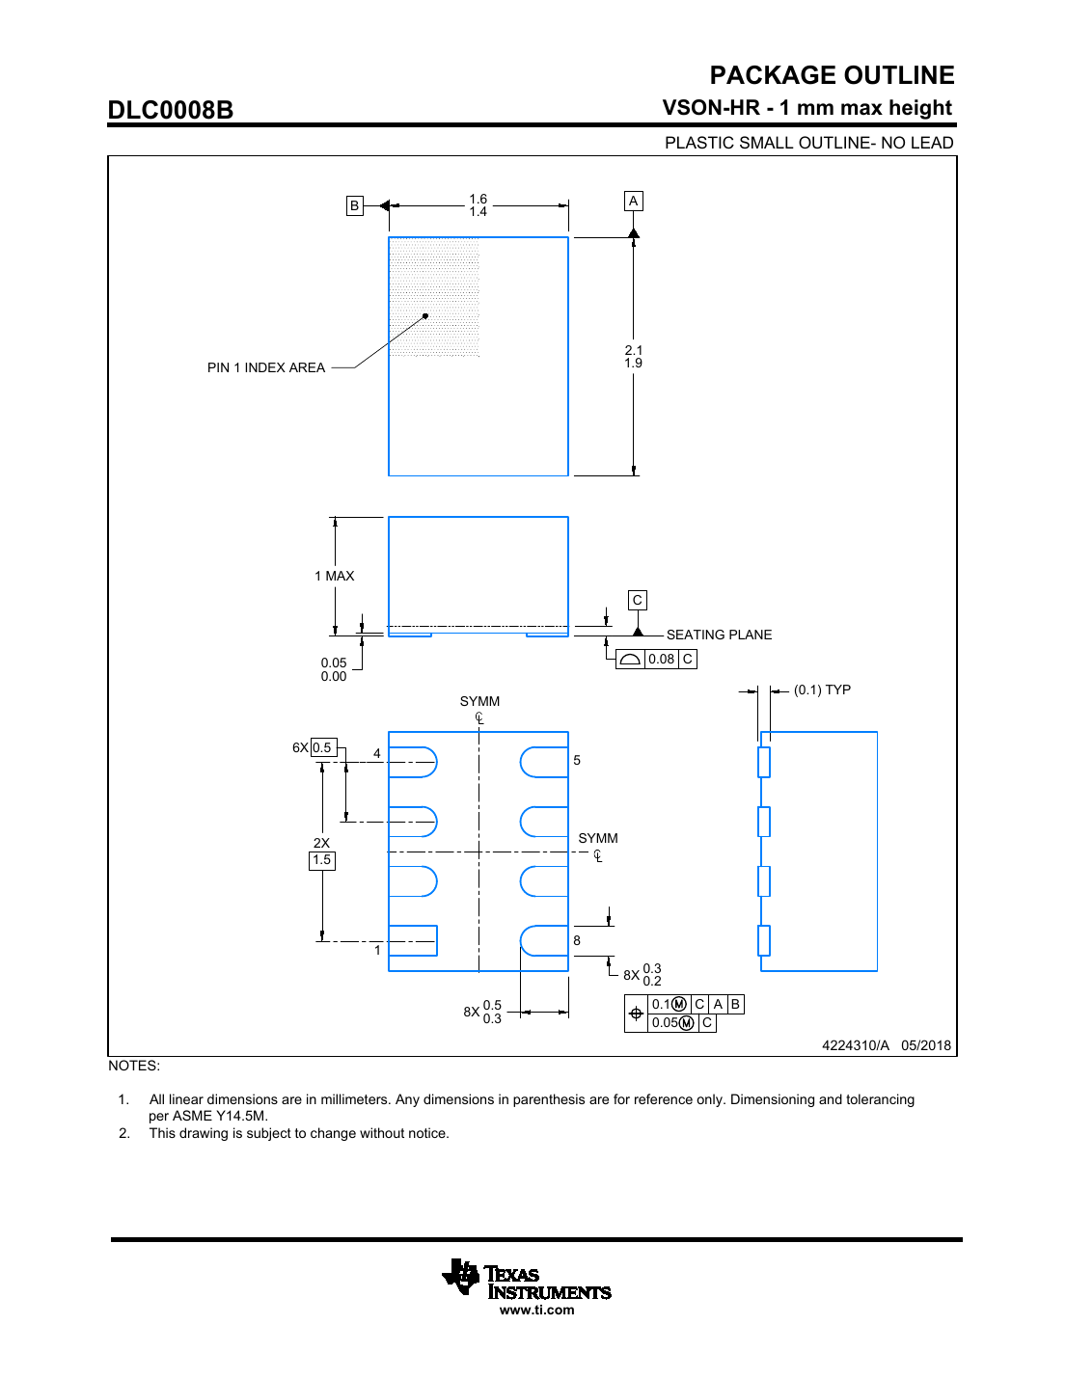
firmware/bingbong_pcb/_mech/fp/tps62840-36.png
