chiangr/bingbong/firmware/bingbong_pcb/_mech/harwin_S7131-45R_DRG-02327.png

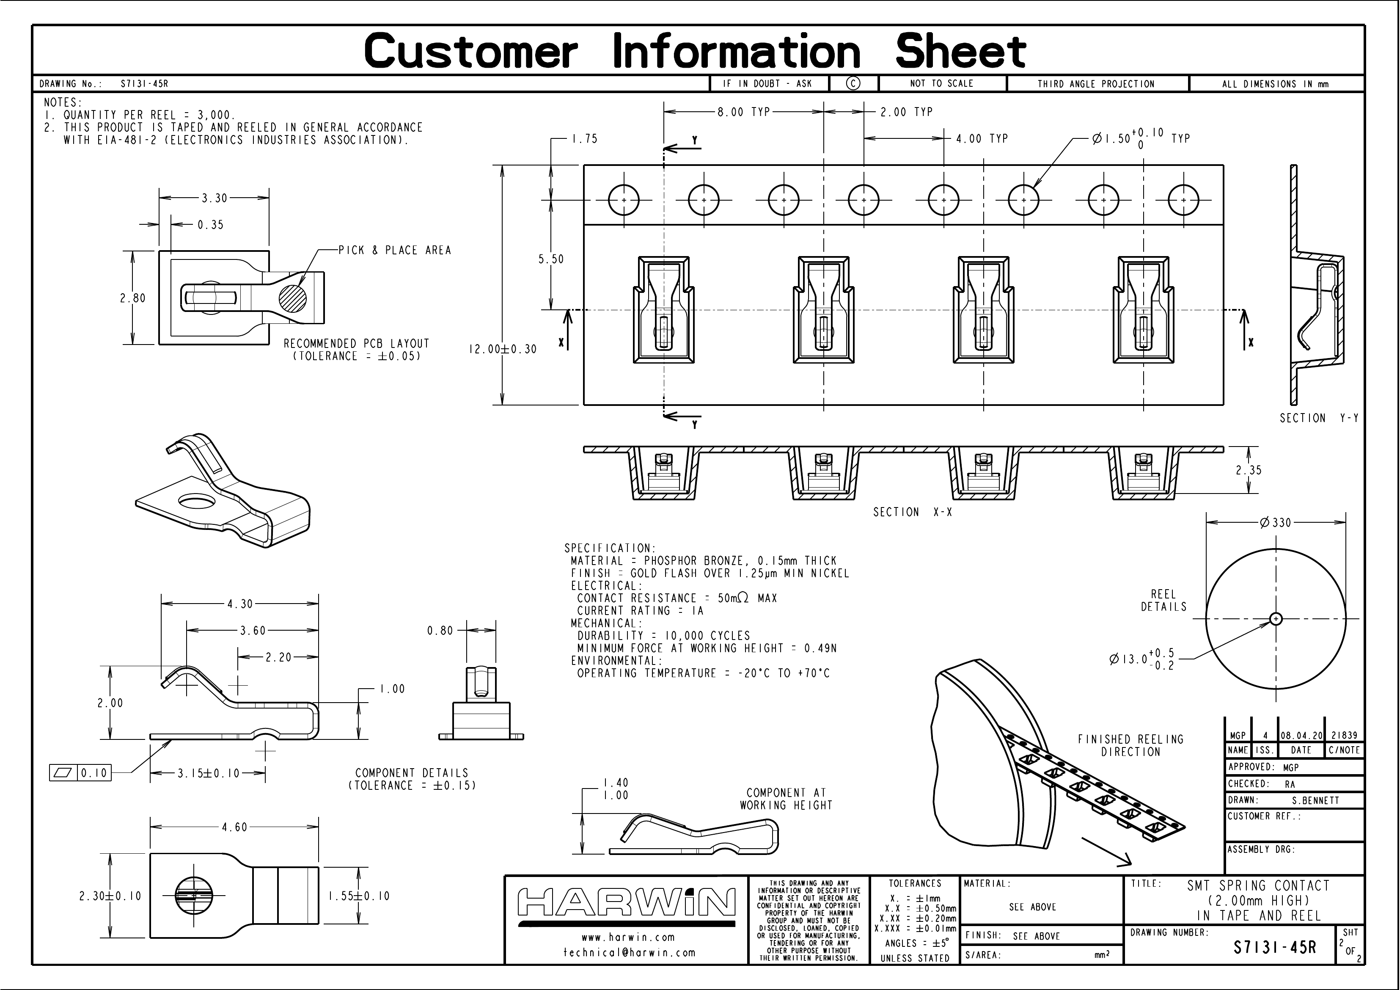
firmware/bingbong_pcb/_mech/harwin_S7131-45R_DRG-02327.png
