chiangr/bingbong/firmware/bingbong_pcb/_mech/harwin_S7141-45R_DRG-02328.png

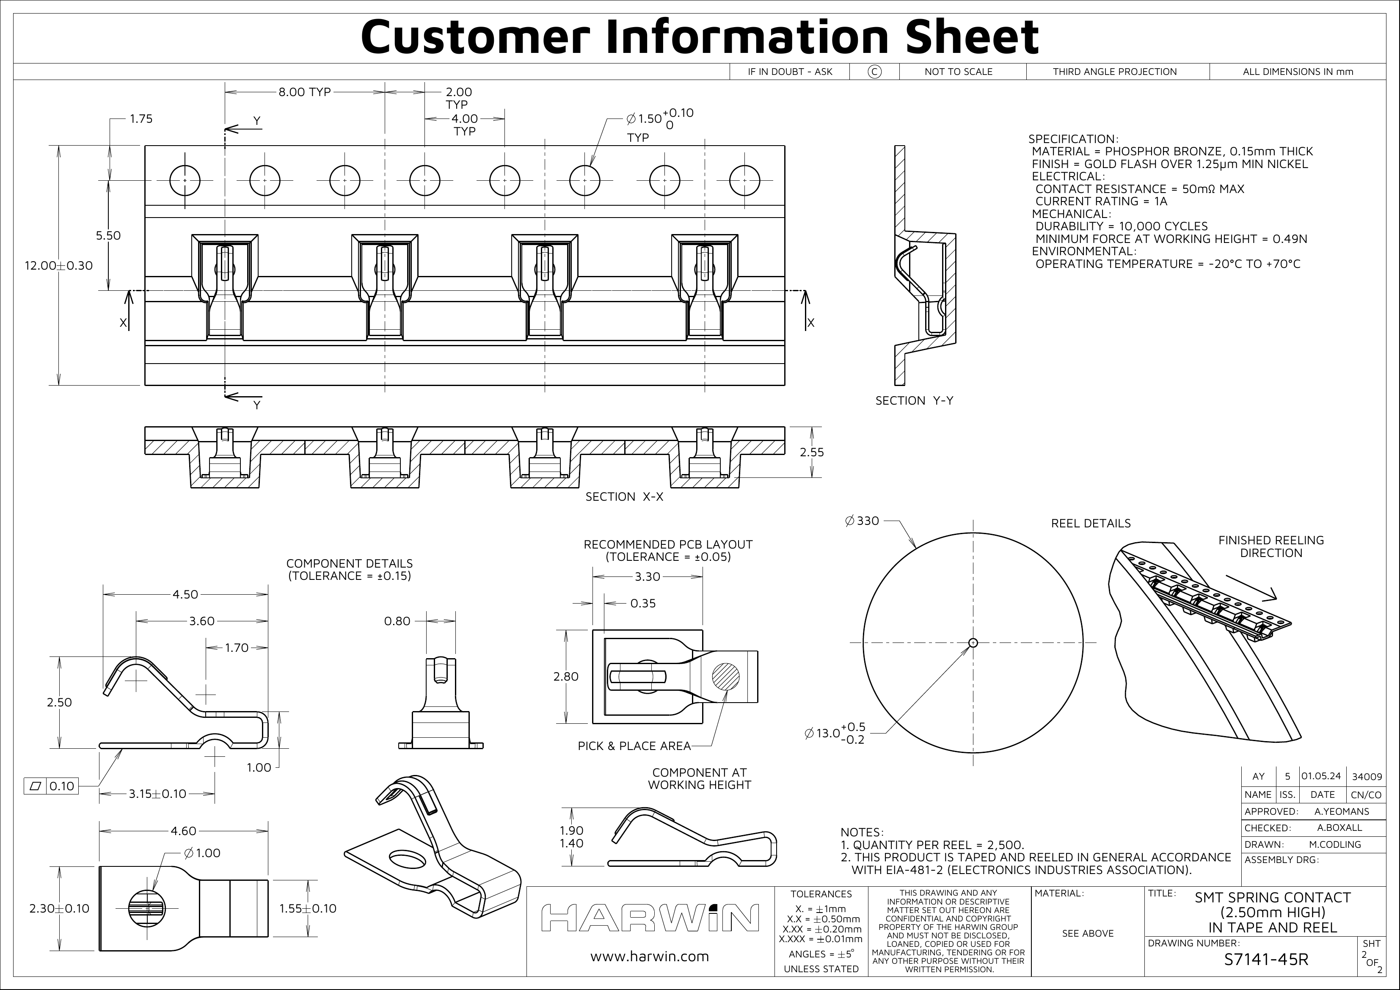
firmware/bingbong_pcb/_mech/harwin_S7141-45R_DRG-02328.png
