chiangr/bingbong/firmware/bingbong_pcb/_mech/iqs-06.png

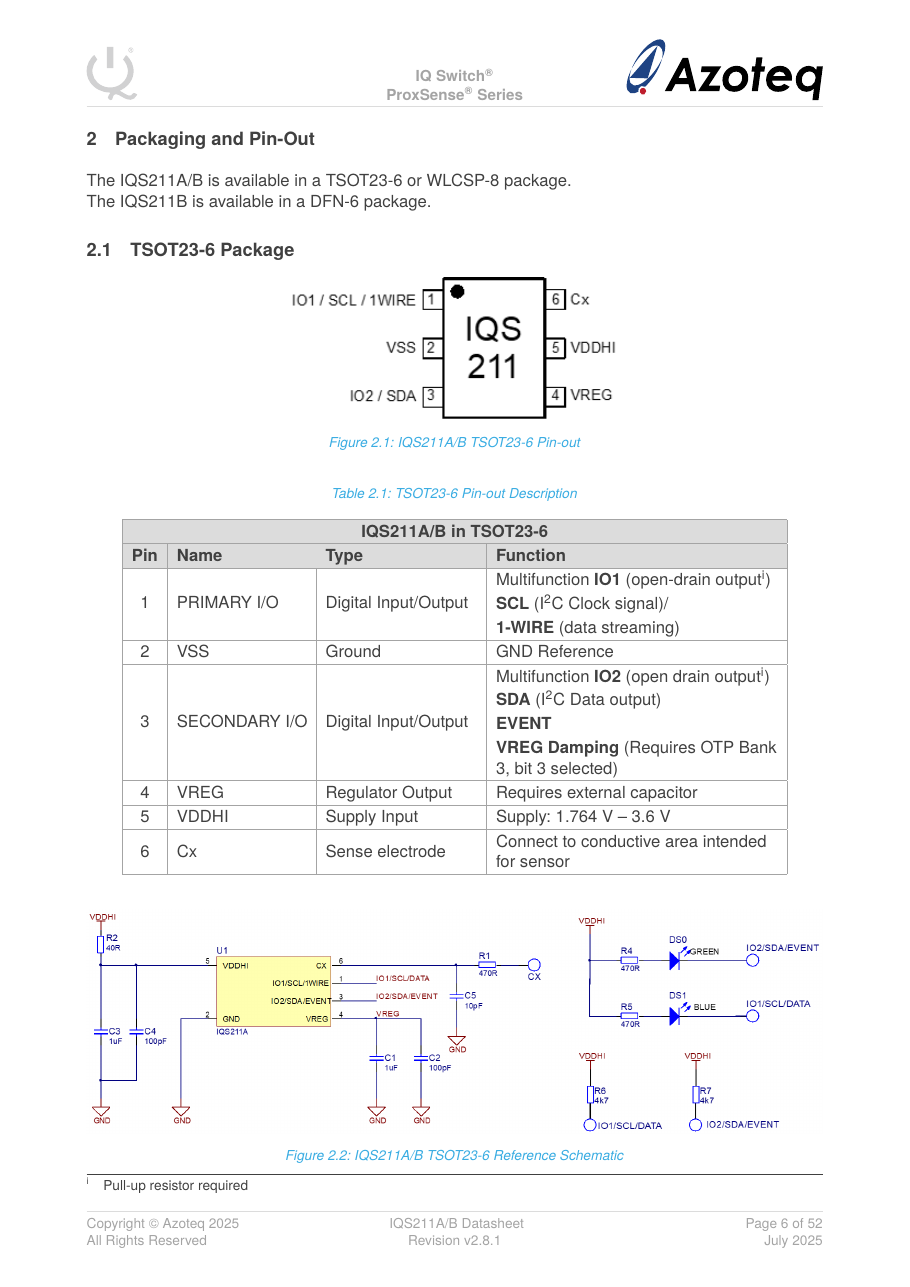
firmware/bingbong_pcb/_mech/iqs-06.png
