chiangr/bingbong/firmware/bingbong_pcb/_mech/iqs-07.png

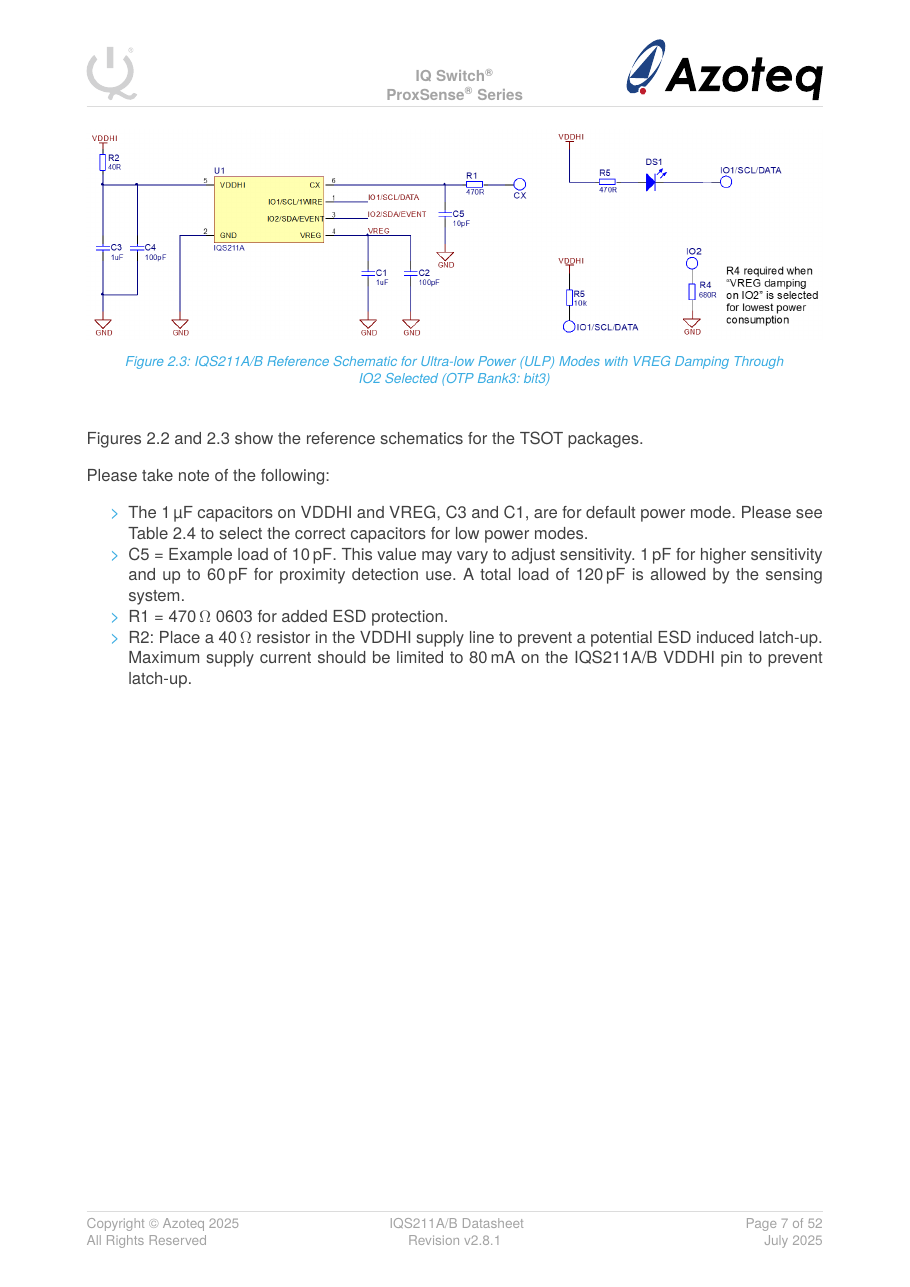
firmware/bingbong_pcb/_mech/iqs-07.png
