chiangr/bingbong/firmware/bingbong_pcb/_mech/mm-1.png

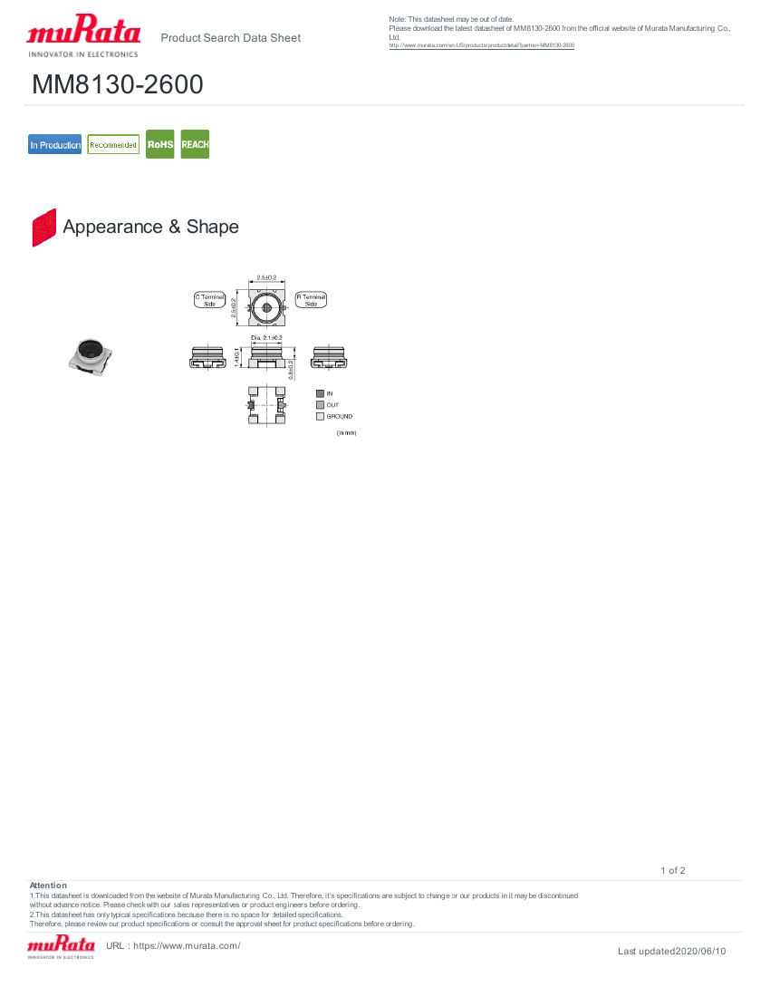
firmware/bingbong_pcb/_mech/mm-1.png
