chiangr/bingbong/firmware/bingbong_pcb/_mech/mm-2.png

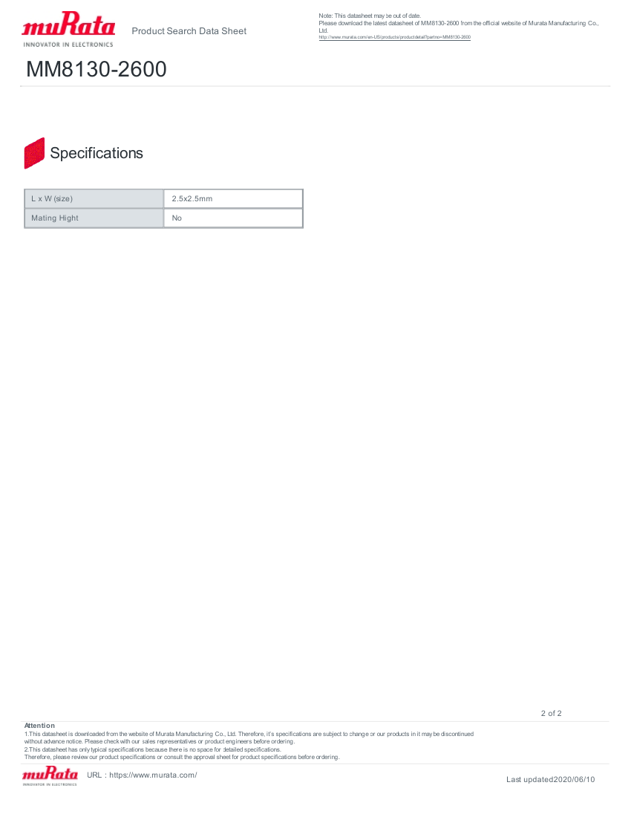
firmware/bingbong_pcb/_mech/mm-2.png
