chiangr/bingbong/firmware/bingbong_pcb/_mech/mtfig-18.png

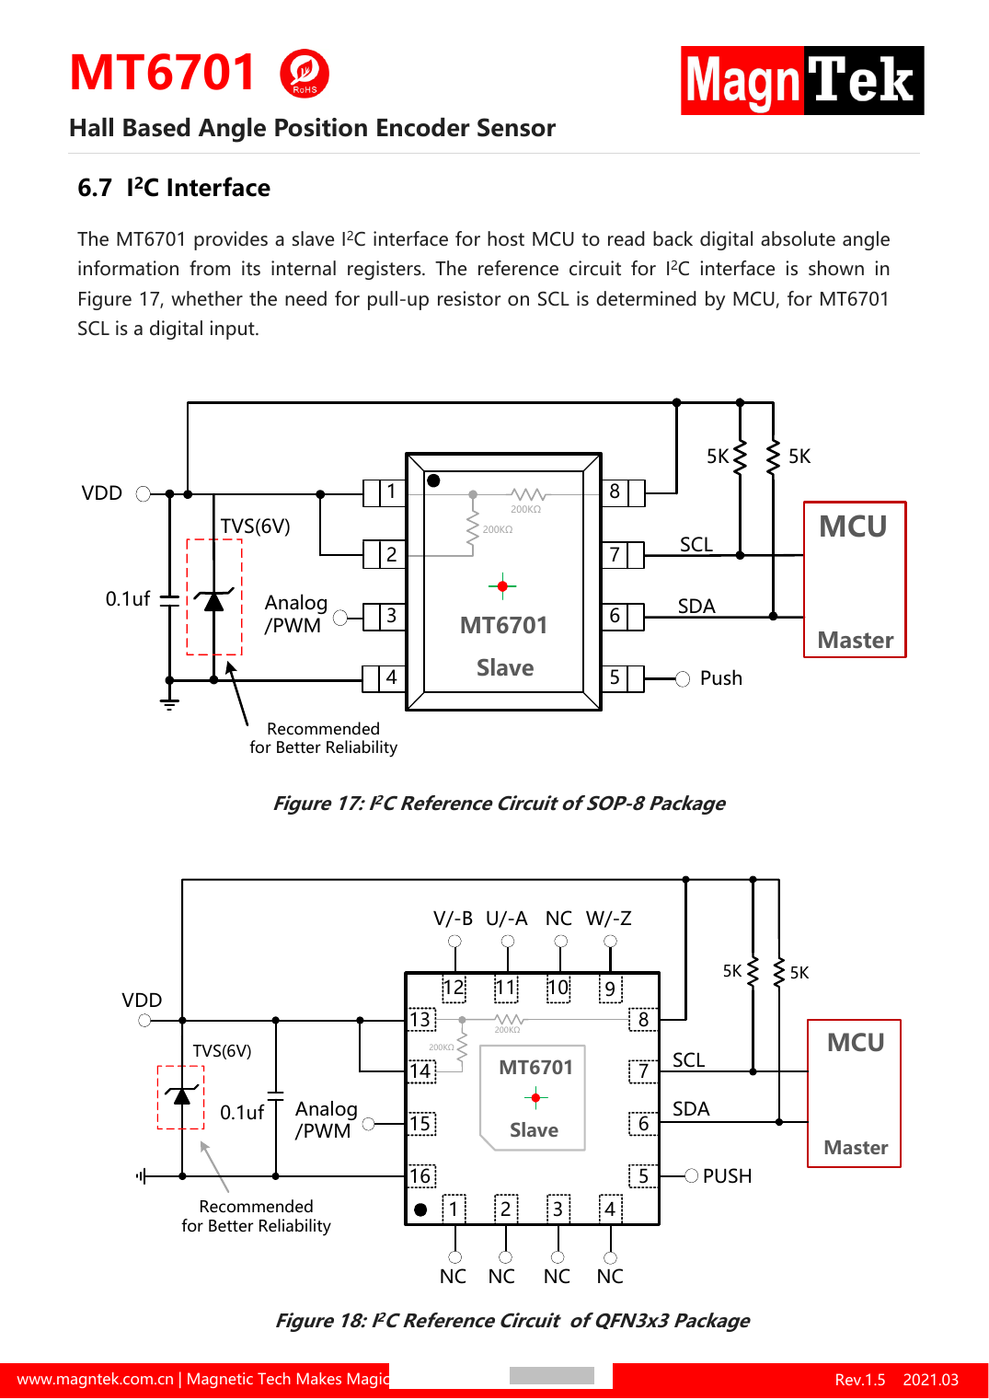
firmware/bingbong_pcb/_mech/mtfig-18.png
