chiangr/bingbong/firmware/bingbong_pcb/_mech/mtp-04.png

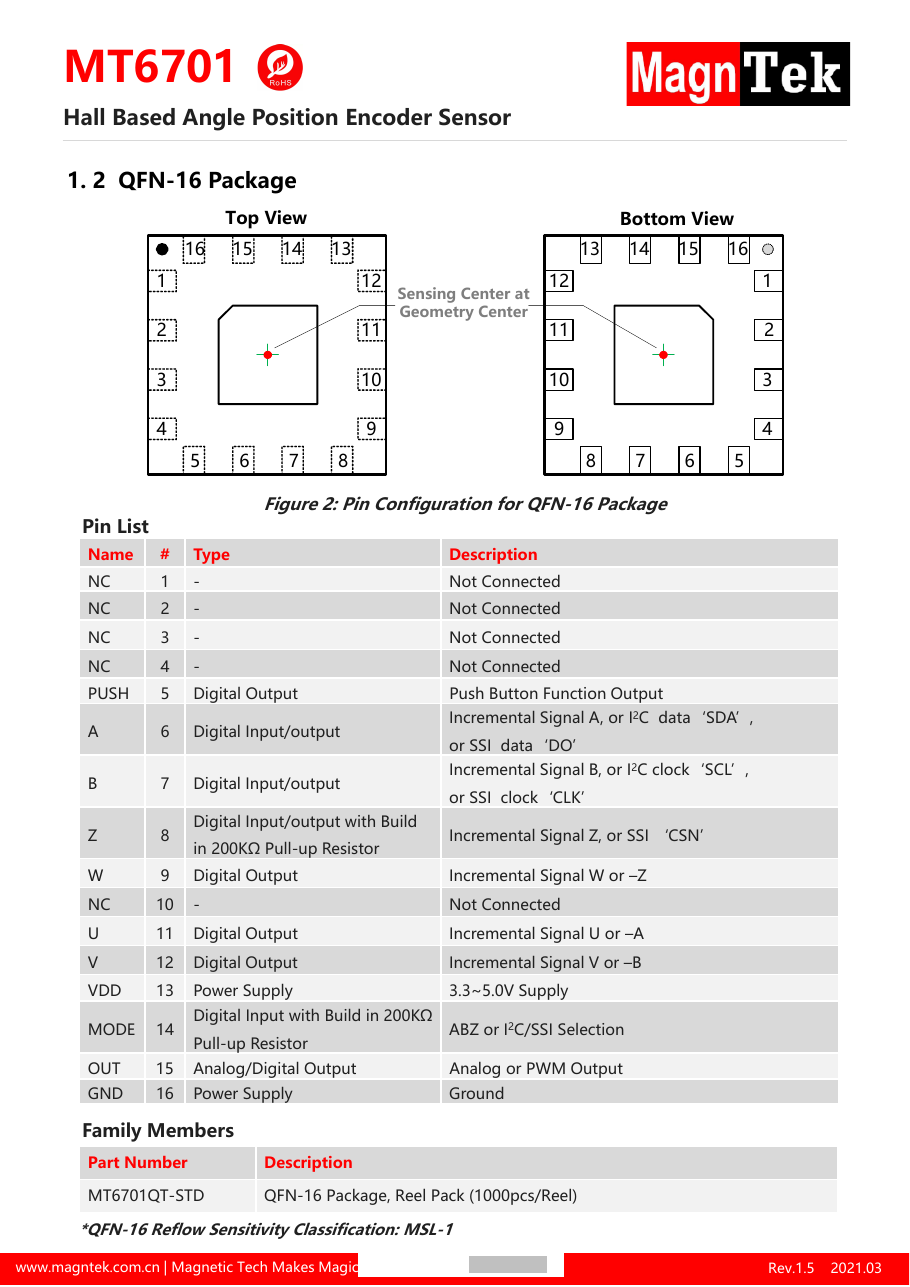
firmware/bingbong_pcb/_mech/mtp-04.png
