chiangr/bingbong/firmware/bingbong_pcb/_mech/murata_MM8130_O30E_p7_outline.png

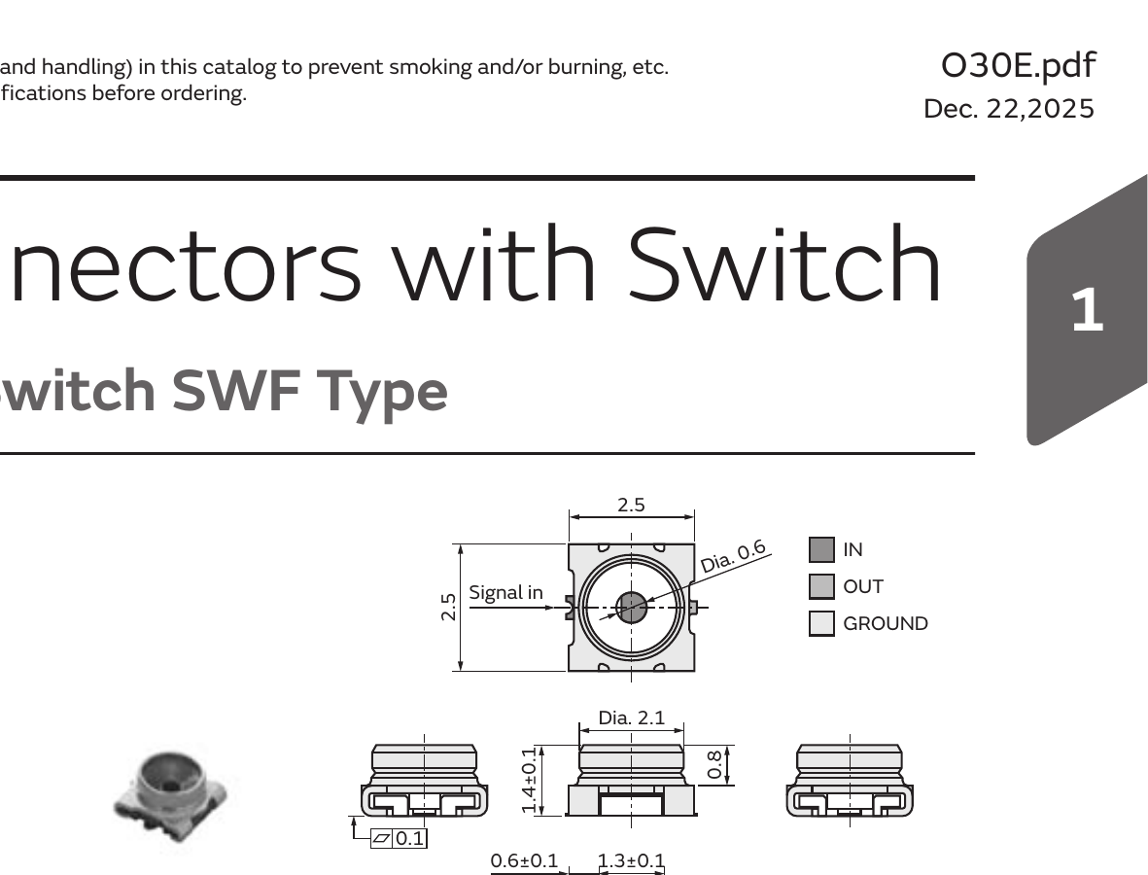
firmware/bingbong_pcb/_mech/murata_MM8130_O30E_p7_outline.png
