chiangr/bingbong/firmware/bingbong_pcb/_mech/mx-08.png

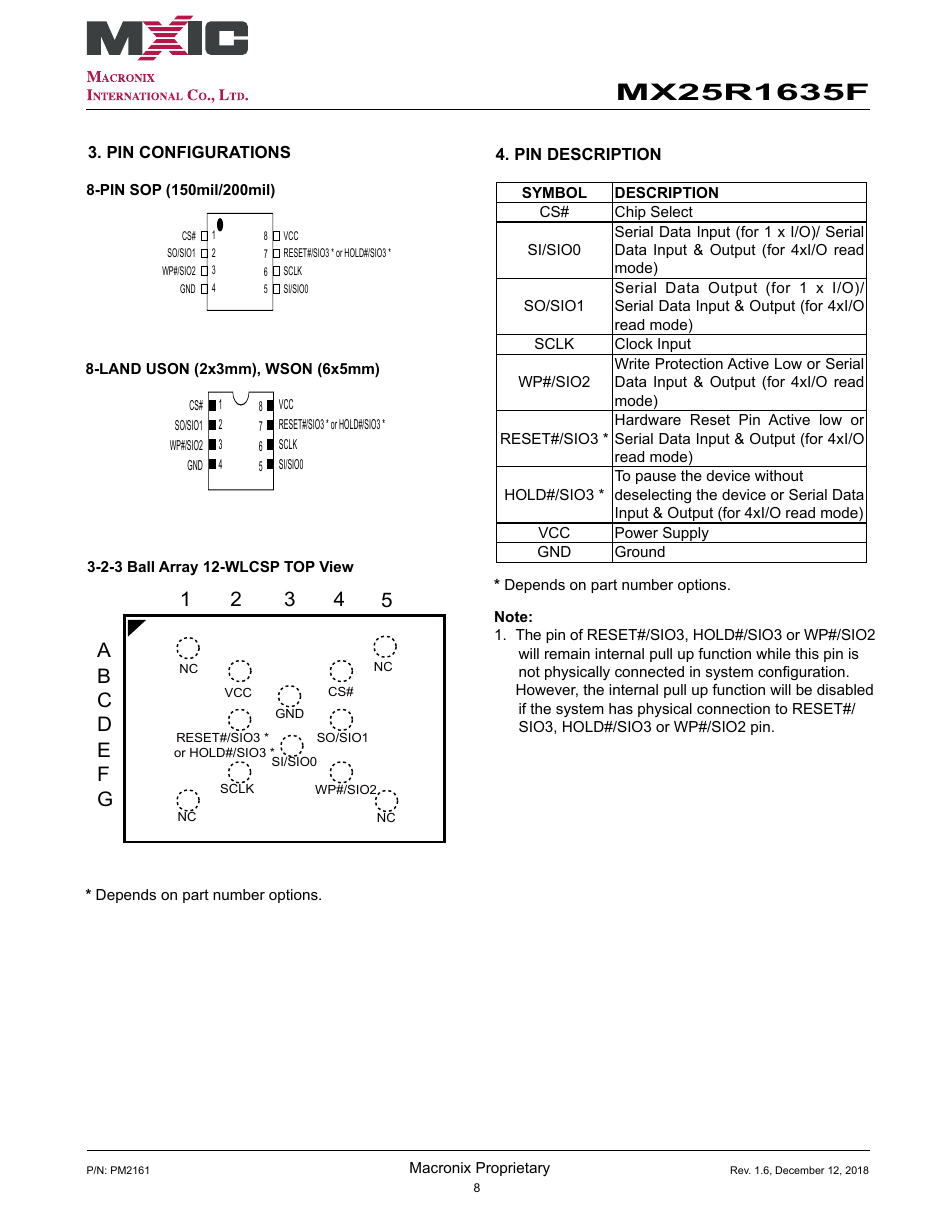
firmware/bingbong_pcb/_mech/mx-08.png
