chiangr/bingbong/firmware/bingbong_pcb/_mech/nrf9151_ps_screens/7.png

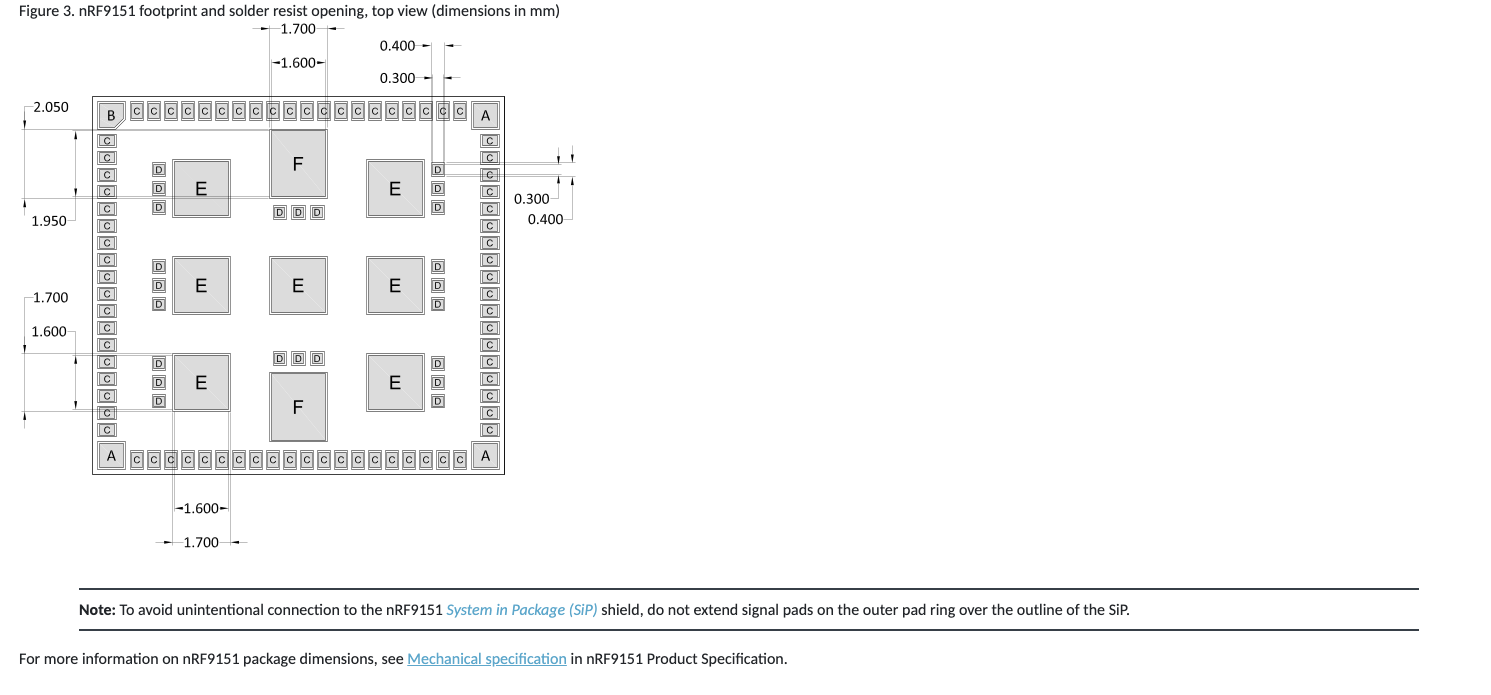
firmware/bingbong_pcb/_mech/nrf9151_ps_screens/7.png
