chiangr/bingbong/firmware/bingbong_pcb/_mech/viot-mff2-4.png

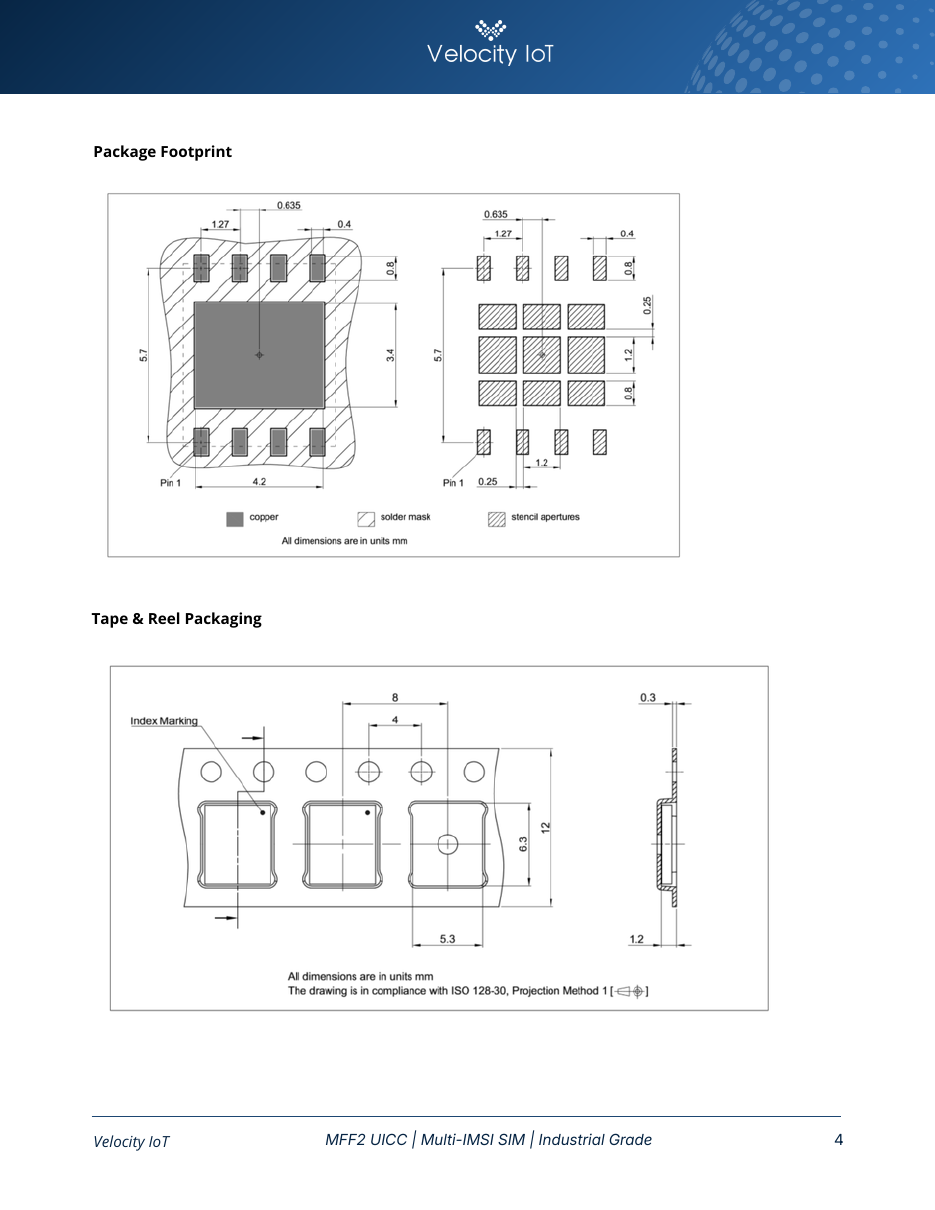
firmware/bingbong_pcb/_mech/viot-mff2-4.png
