chiangr/bingbong/firmware/bingbong_pcb/_mech/wurth_WE-SECF_331031271520_p1.png

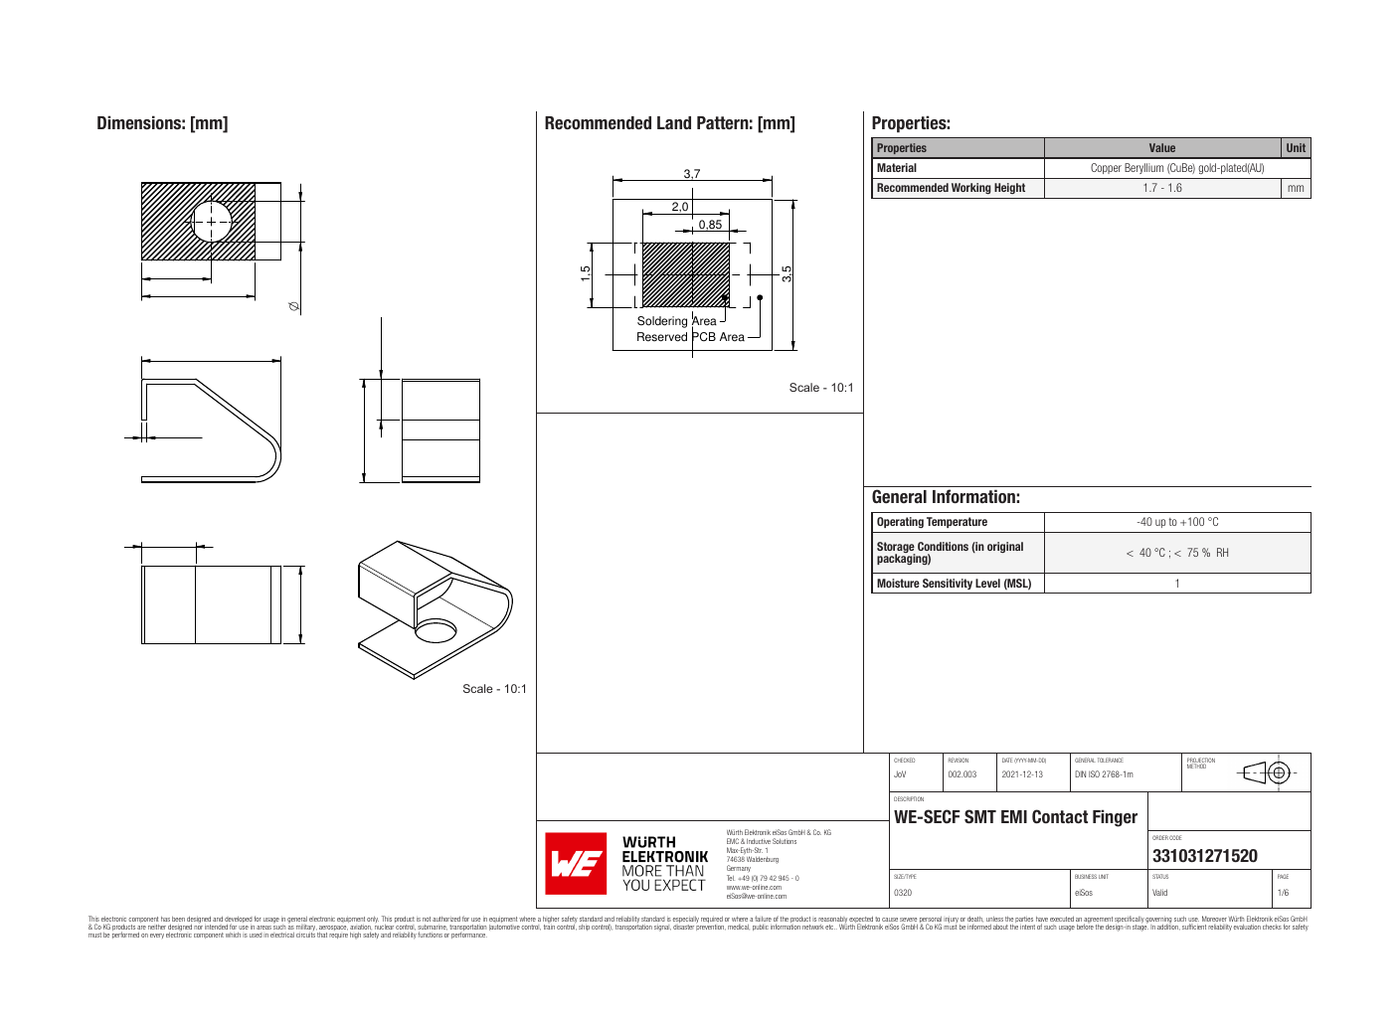
firmware/bingbong_pcb/_mech/wurth_WE-SECF_331031271520_p1.png
