chiangr/bingbong/firmware/bingbong_pcb/_ts04_mech2.png

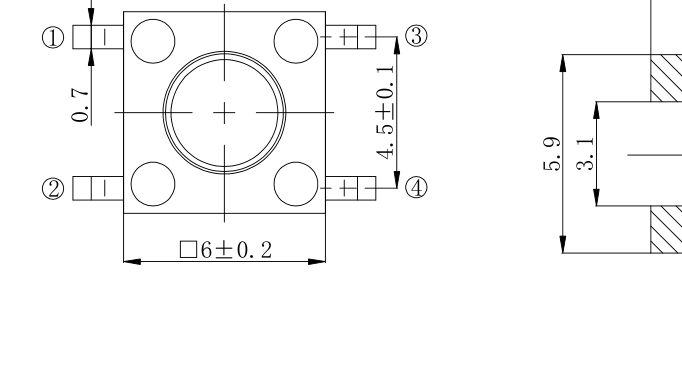
firmware/bingbong_pcb/_ts04_mech2.png
