chiangr/bingbong/firmware/bingbong_pcb/_ts04_pcb2.png

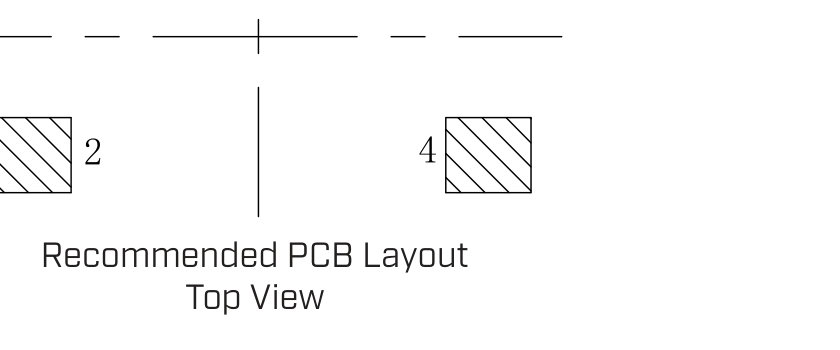
firmware/bingbong_pcb/_ts04_pcb2.png
