chiangr/bingbong/firmware/bingbong_pcb/_ts04_pcb3.png

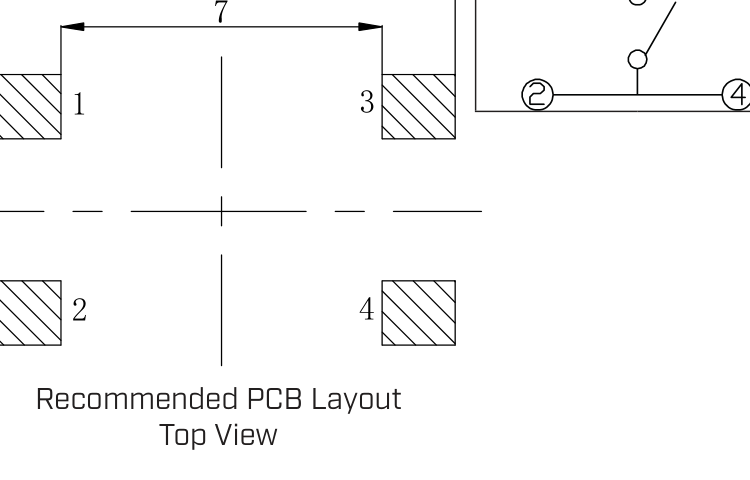
firmware/bingbong_pcb/_ts04_pcb3.png
