chiangr/bingbong/firmware/bingbong_pcb/_ts04_pcb.png

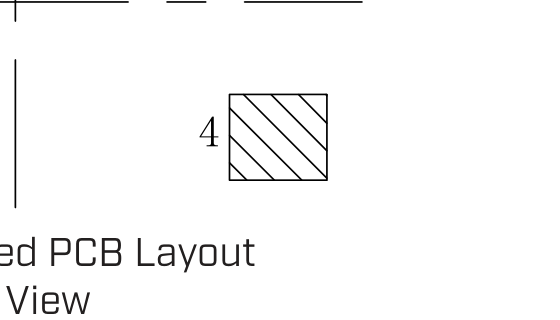
firmware/bingbong_pcb/_ts04_pcb.png
