chiangr/bingbong/firmware/bingbong_pcb/_ts04_sch2.png

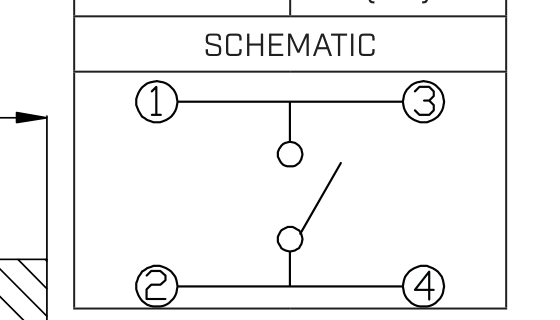
firmware/bingbong_pcb/_ts04_sch2.png
