chiangr/bingbong/firmware/bingbong_pcb/_ts04_sch.png

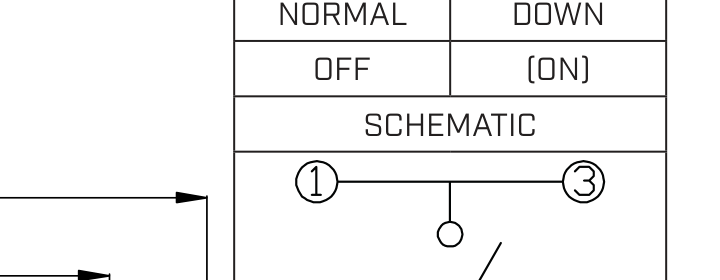
firmware/bingbong_pcb/_ts04_sch.png
