chiangr/bingbong/site/qa/assembly/overview-390.png

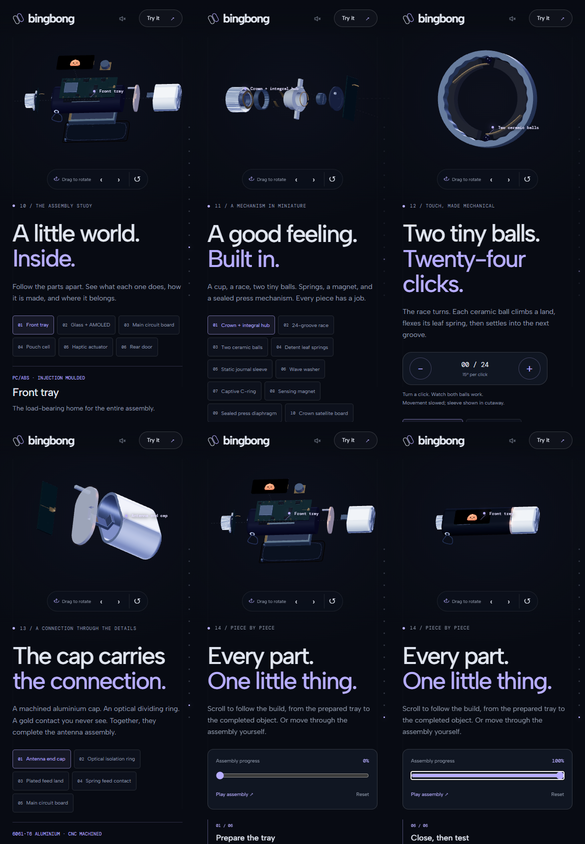
site/qa/assembly/overview-390.png
