chiangr/bingbong/site/qa/assembly/overview-1440.png

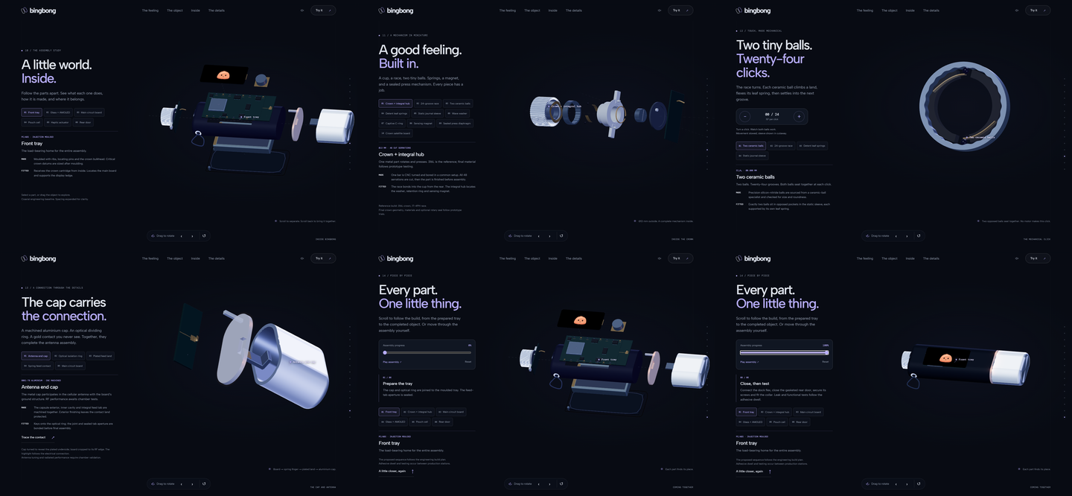
site/qa/assembly/overview-1440.png
