chiangr/bingbong/site/qa/redesign/390-boop.png

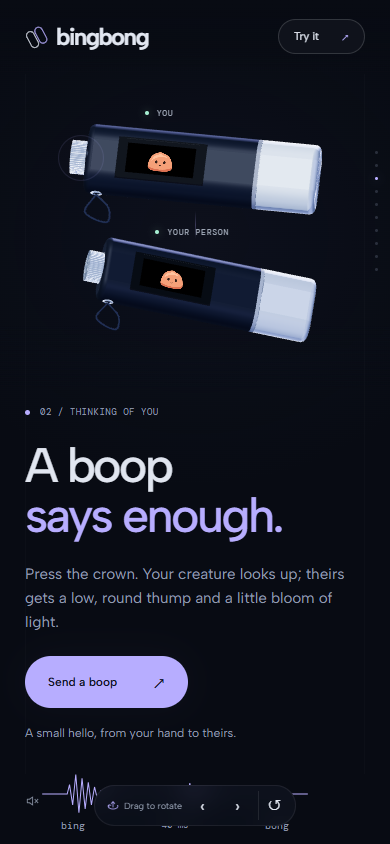
site/qa/redesign/390-boop.png
