chiangr/bingbong/site/qa/redesign/390-creature.png

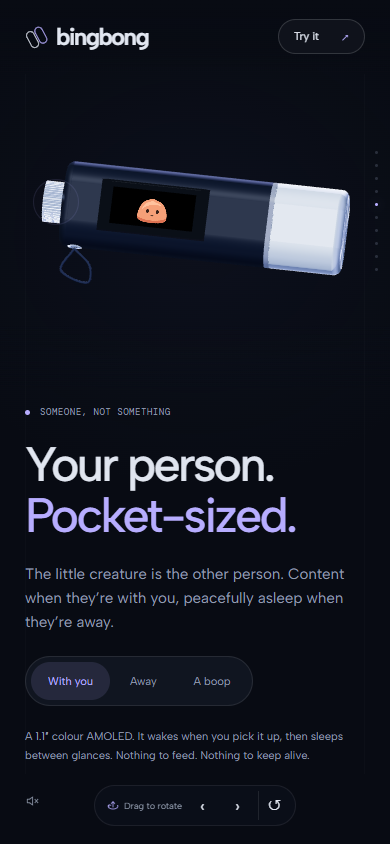
site/qa/redesign/390-creature.png
