chiangr/bingbong/site/qa/redesign/390-details.png

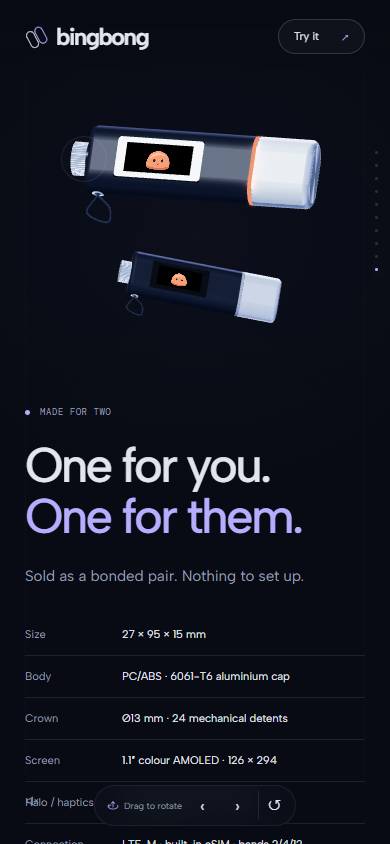
site/qa/redesign/390-details.png
