chiangr/bingbong/site/qa/redesign/390-halo.png

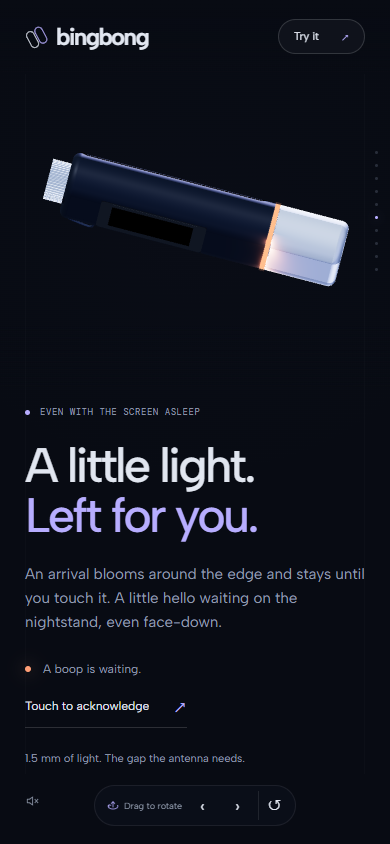
site/qa/redesign/390-halo.png
