chiangr/bingbong/site/qa/redesign/390-hello.png

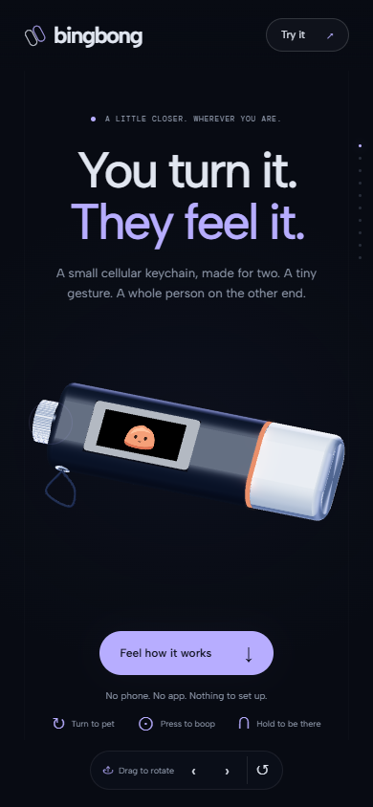
site/qa/redesign/390-hello.png
