chiangr/bingbong/site/qa/redesign/390-hold.png

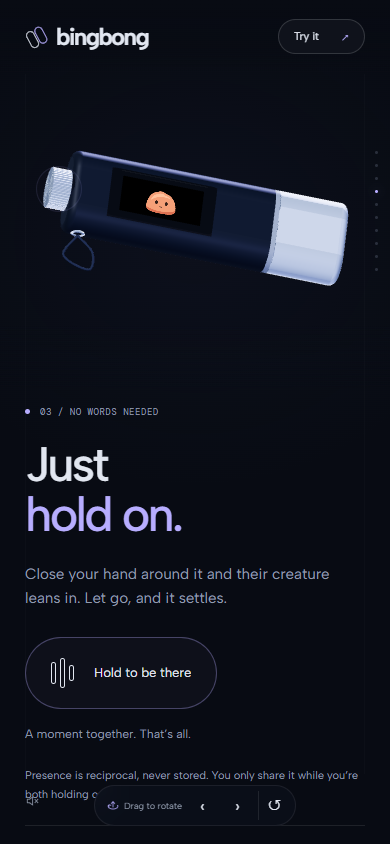
site/qa/redesign/390-hold.png
