chiangr/bingbong/site/qa/redesign/390-object.png

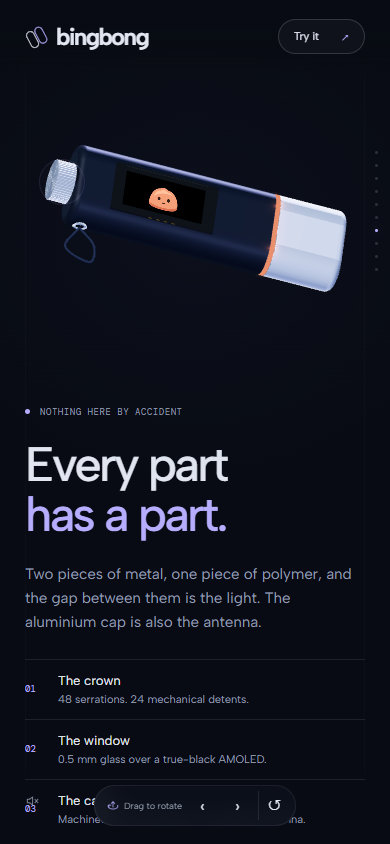
site/qa/redesign/390-object.png
