chiangr/bingbong/site/qa/redesign/390-pet.png

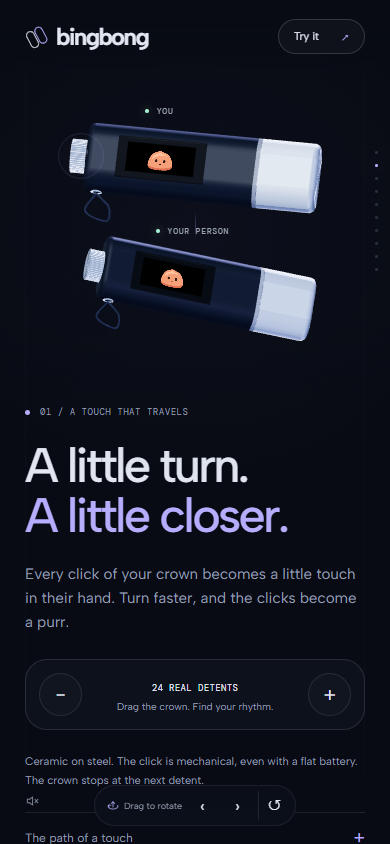
site/qa/redesign/390-pet.png
