chiangr/bingbong/site/qa/redesign/390-quiet.png

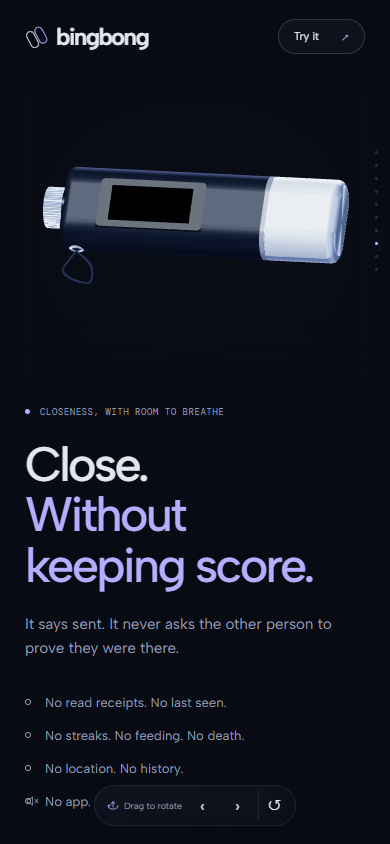
site/qa/redesign/390-quiet.png
