chiangr/bingbong/site/qa/redesign/390-size.png

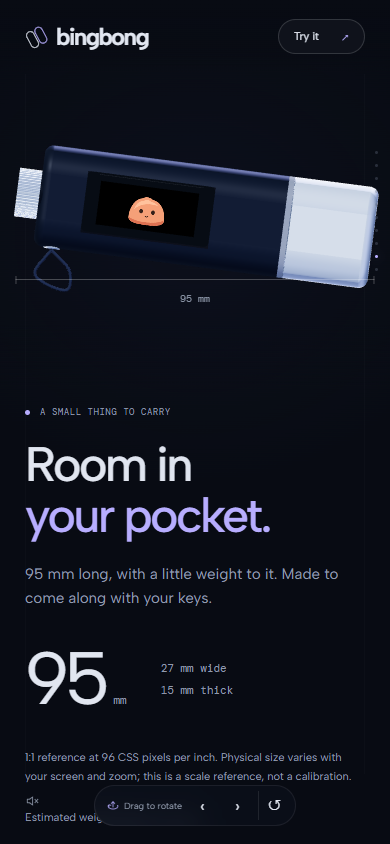
site/qa/redesign/390-size.png
