chiangr/bingbong/site/qa/redesign/820-creature.png

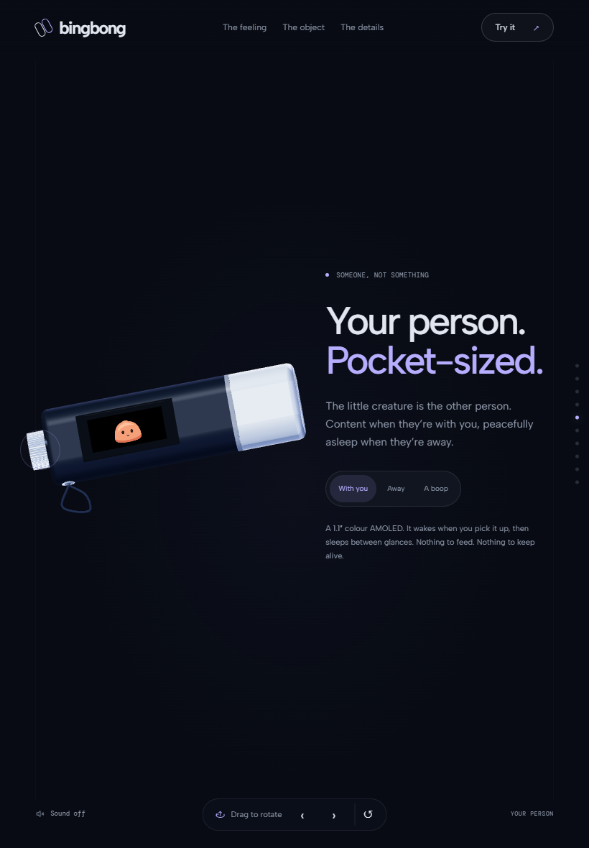
site/qa/redesign/820-creature.png
