chiangr/bingbong/site/qa/redesign/820-details.png

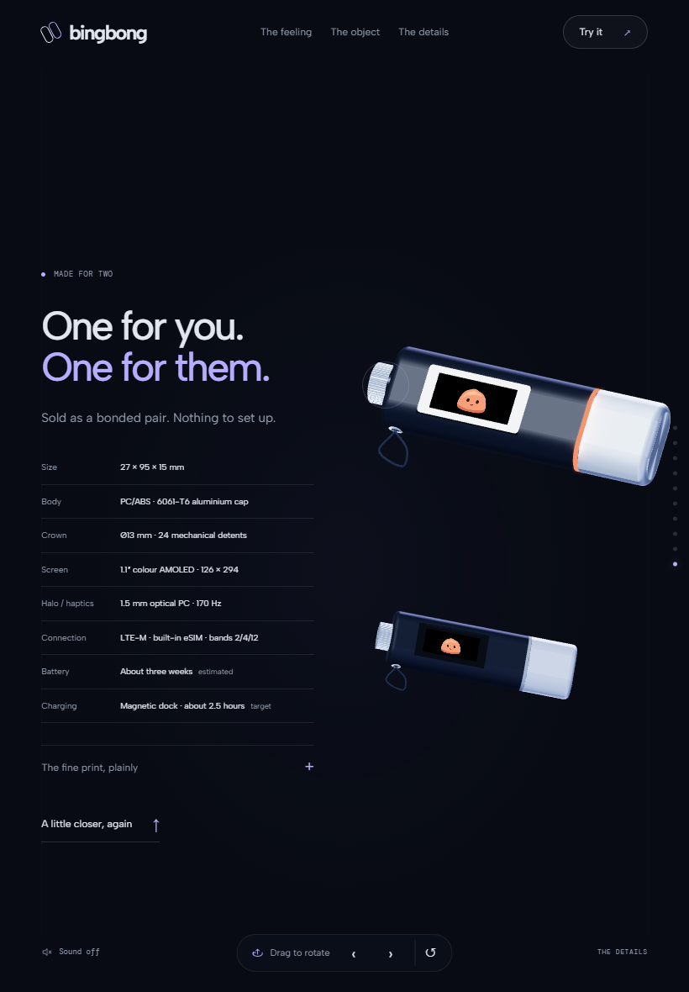
site/qa/redesign/820-details.png
