chiangr/bingbong/site/qa/redesign/820-halo.png

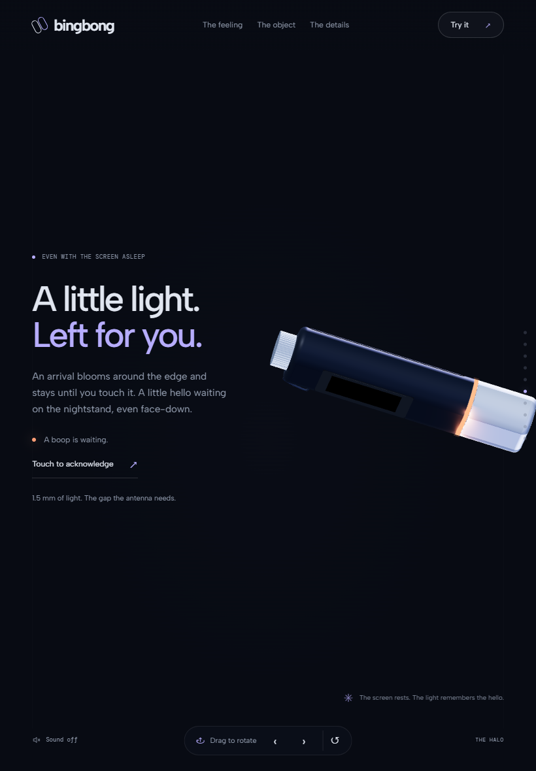
site/qa/redesign/820-halo.png
