chiangr/bingbong/site/qa/redesign/820-hello.png

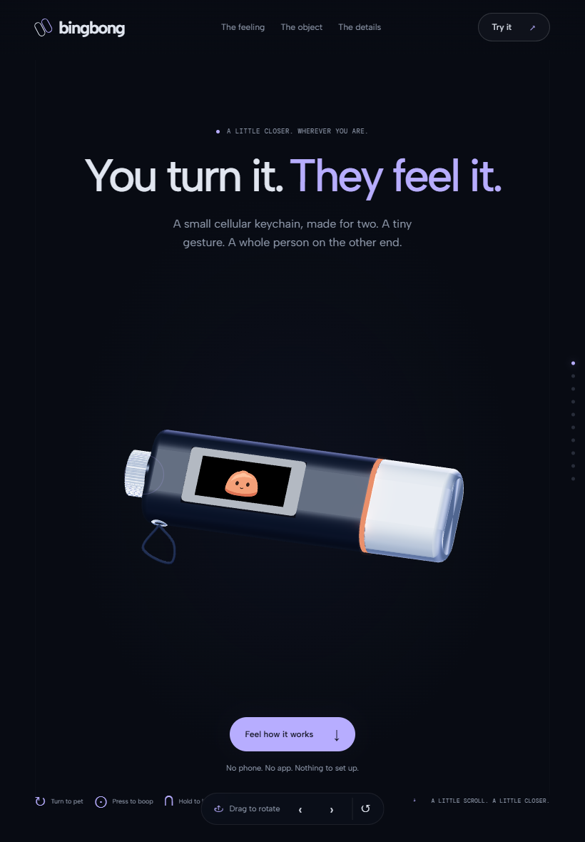
site/qa/redesign/820-hello.png
