chiangr/bingbong/site/qa/redesign/820-hold.png

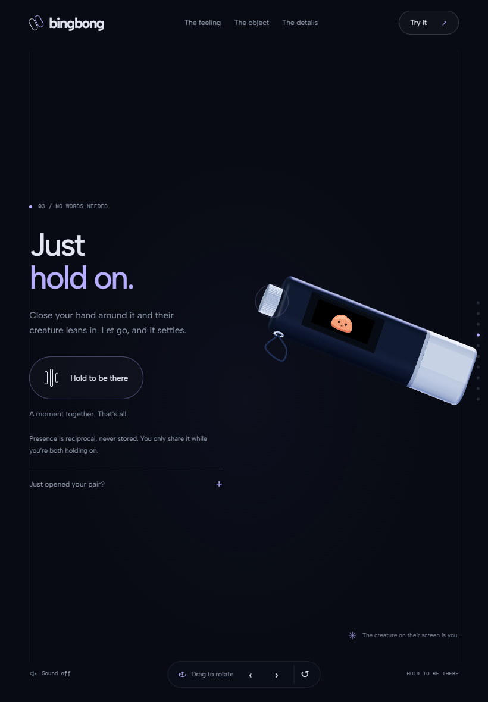
site/qa/redesign/820-hold.png
