chiangr/bingbong/site/qa/redesign/820-object.png

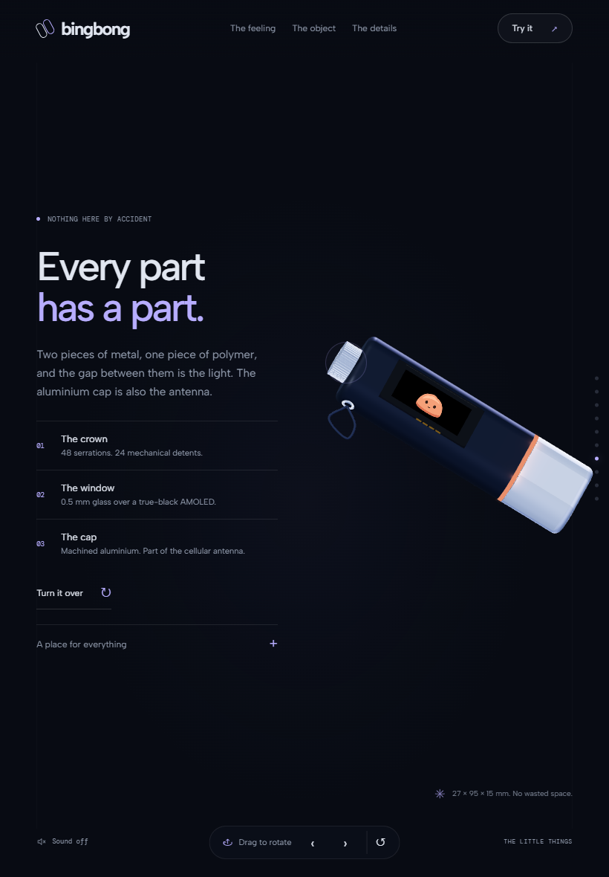
site/qa/redesign/820-object.png
