chiangr/bingbong/site/qa/redesign/820-quiet.png

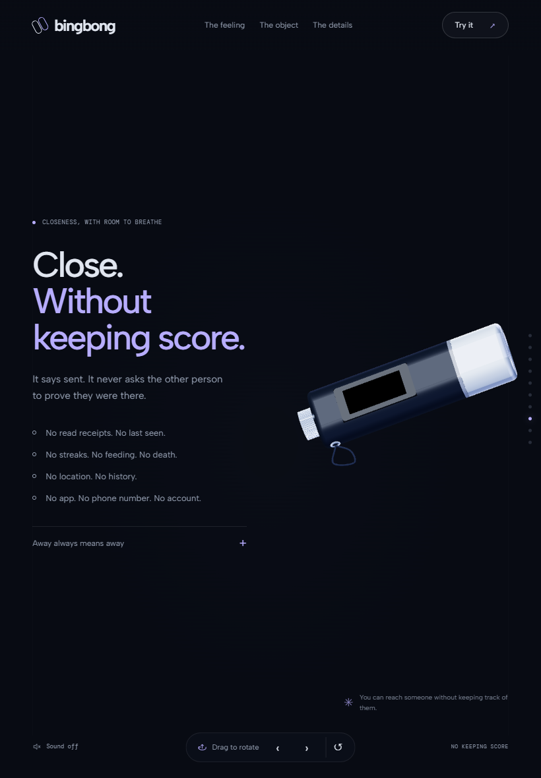
site/qa/redesign/820-quiet.png
