chiangr/bingbong/site/qa/redesign/820-size.png

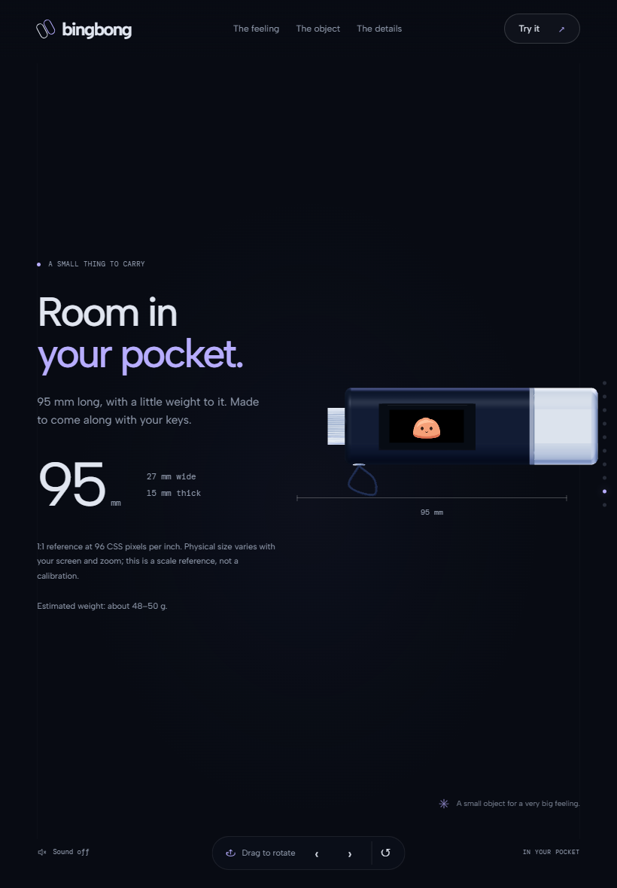
site/qa/redesign/820-size.png
