chiangr/bingbong/site/qa/redesign/1440-boop.png

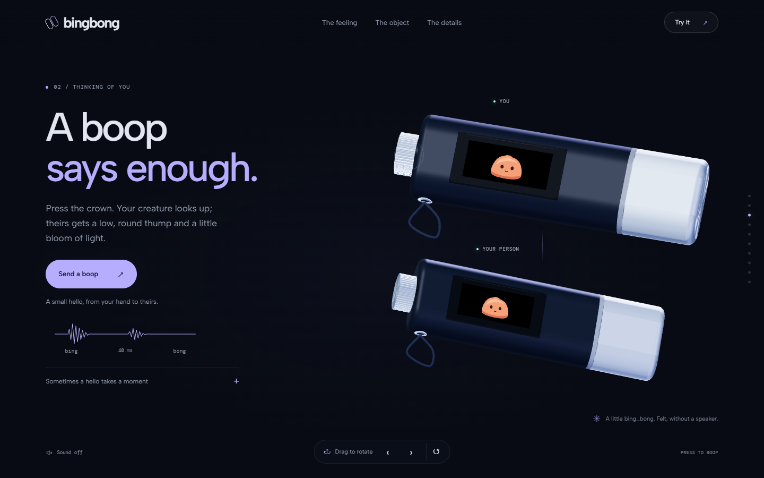
site/qa/redesign/1440-boop.png
