chiangr/bingbong/site/qa/redesign/1440-creature.png

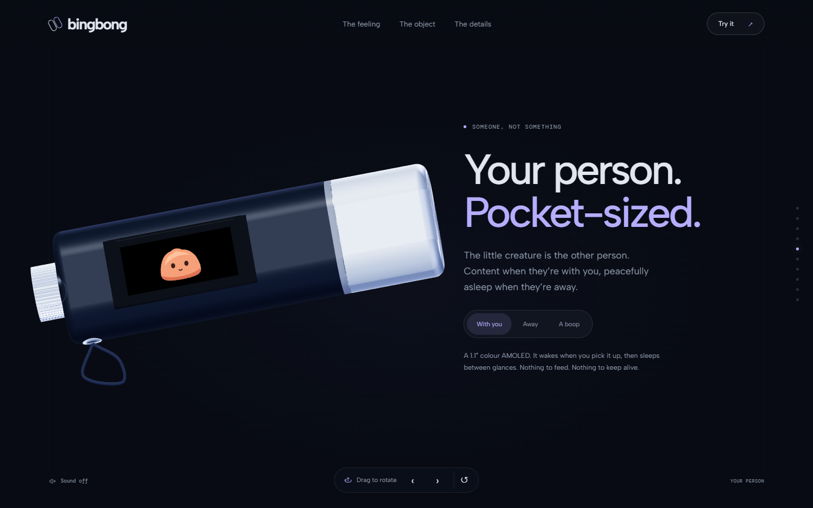
site/qa/redesign/1440-creature.png
