chiangr/bingbong/site/qa/redesign/1440-details.png

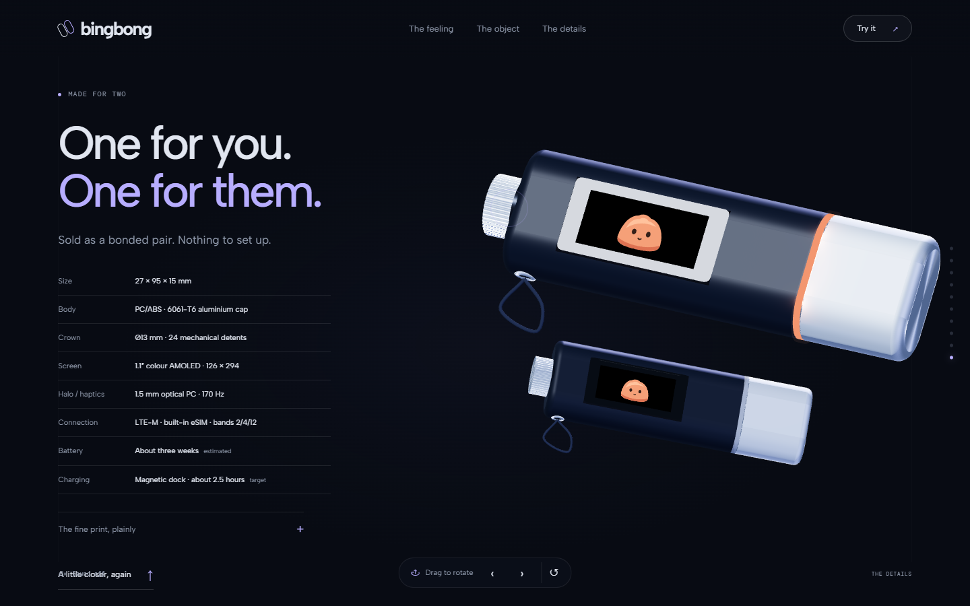
site/qa/redesign/1440-details.png
