chiangr/bingbong/site/qa/redesign/1440-halo.png

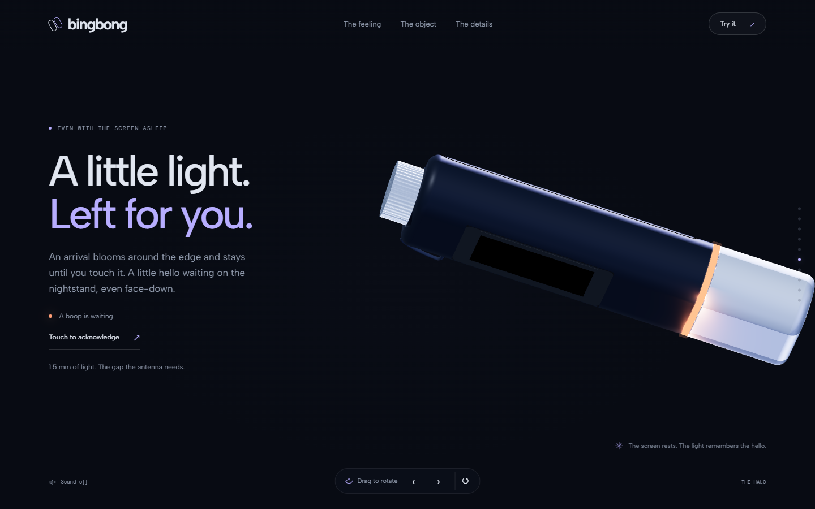
site/qa/redesign/1440-halo.png
