chiangr/bingbong/site/qa/redesign/1440-hello.png

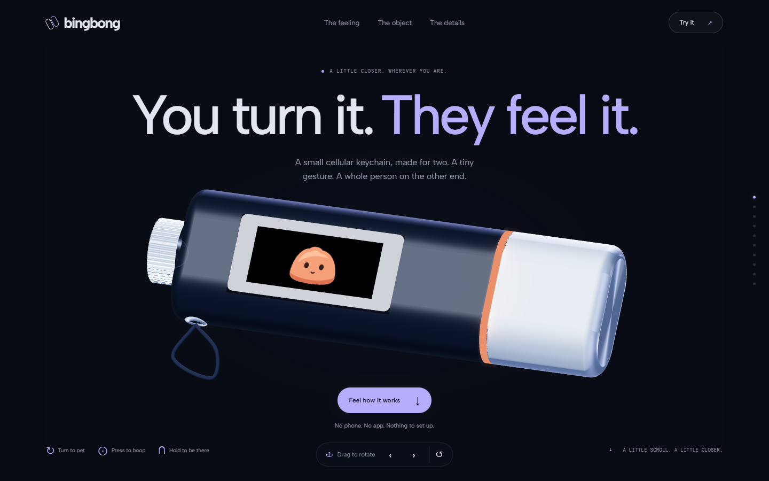
site/qa/redesign/1440-hello.png
