chiangr/bingbong/site/qa/redesign/1440-hold.png

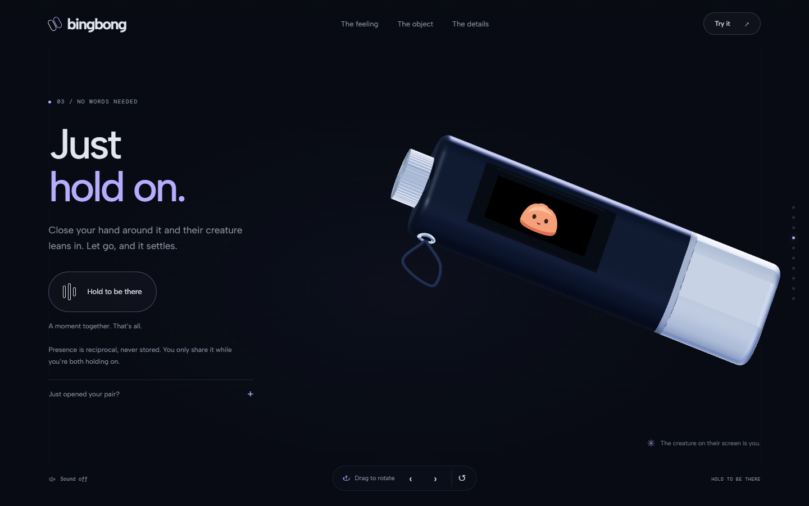
site/qa/redesign/1440-hold.png
