chiangr/bingbong/site/qa/redesign/1440-object.png

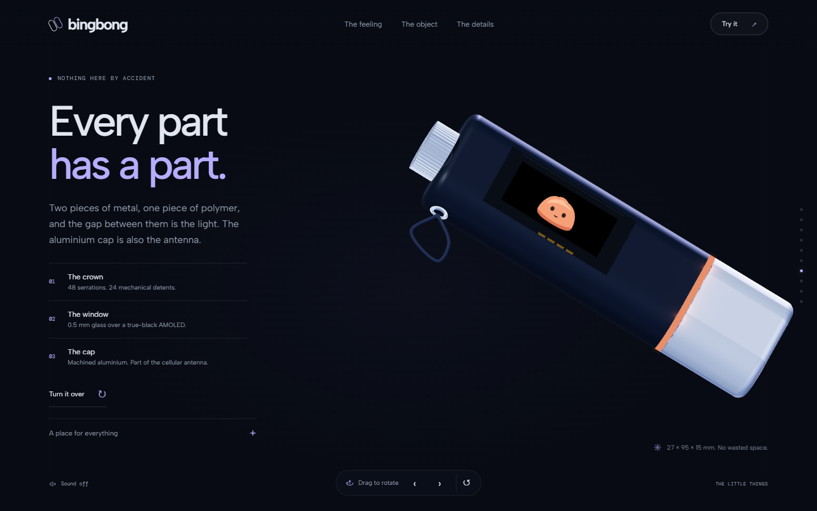
site/qa/redesign/1440-object.png
