chiangr/bingbong/site/qa/redesign/1440-pet.png

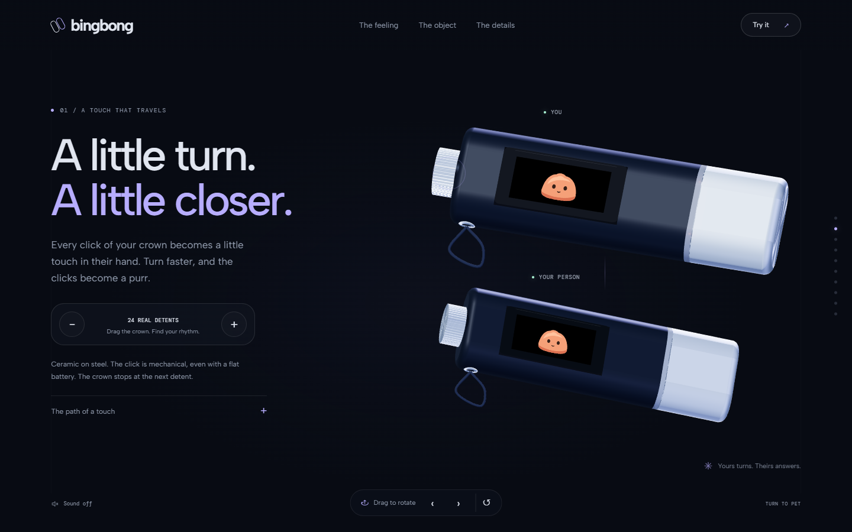
site/qa/redesign/1440-pet.png
