chiangr/bingbong/site/qa/redesign/1440-quiet.png

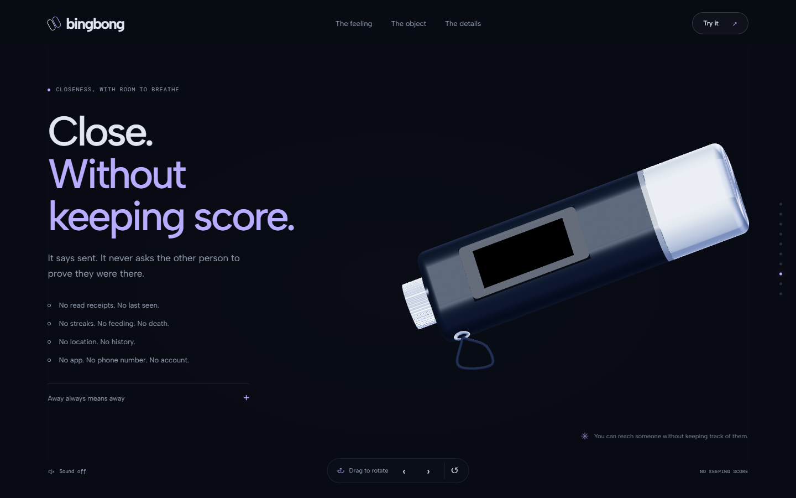
site/qa/redesign/1440-quiet.png
