chiangr/bingbong/site/qa/redesign/1440-size.png

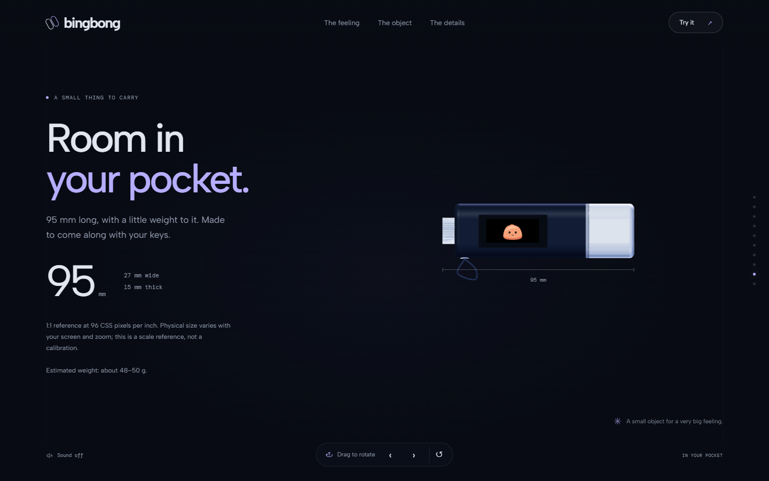
site/qa/redesign/1440-size.png
