chiangr/bingbong/site/qa/redesign/context-recovered.png

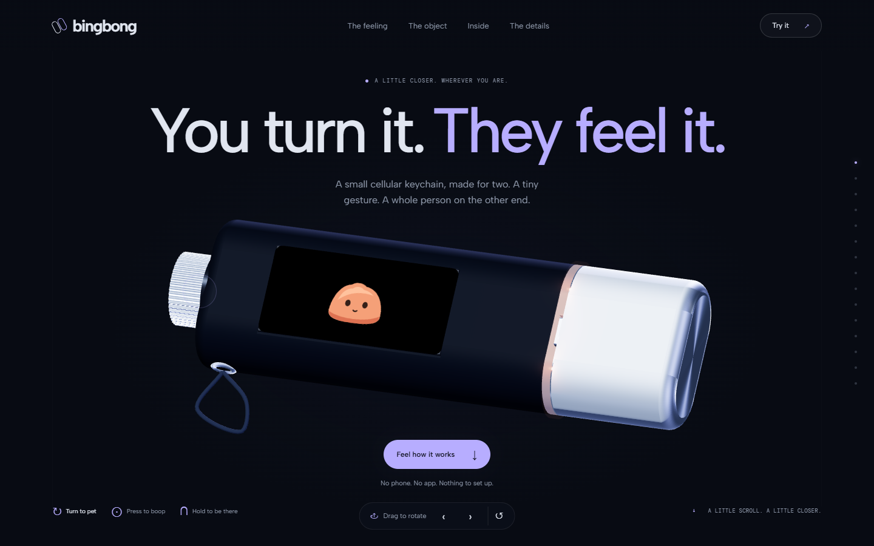
site/qa/redesign/context-recovered.png
