chiangr/bingbong/site/qa/redesign/overview-390.png

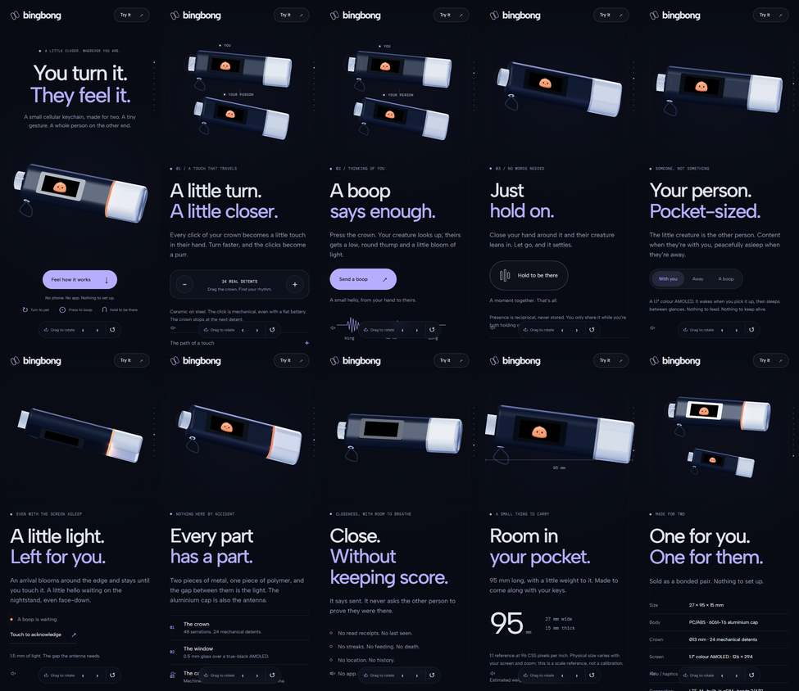
site/qa/redesign/overview-390.png
