chiangr/bingbong/site/qa/redesign/overview-820.png

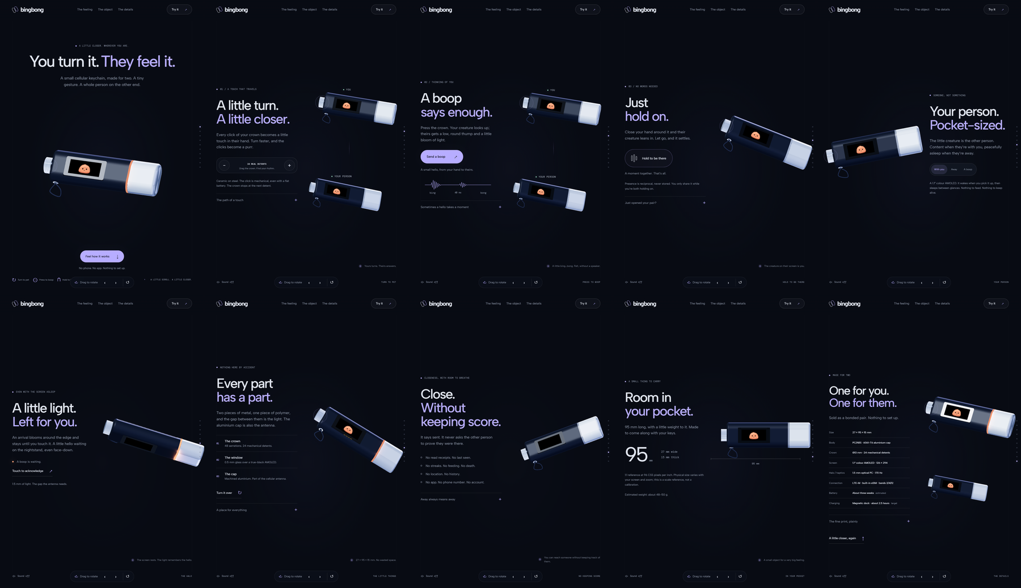
site/qa/redesign/overview-820.png
