chiangr/bingbong/site/qa/redesign/overview-1440.png

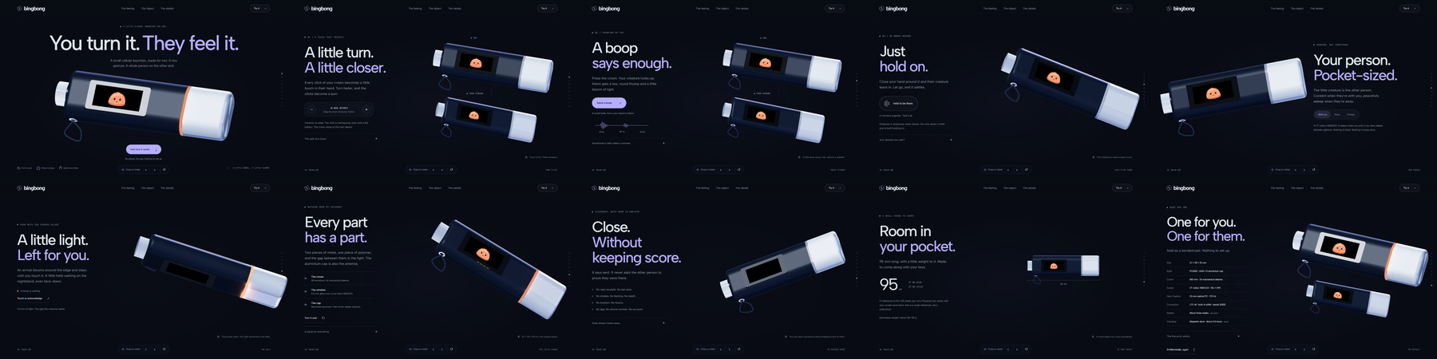
site/qa/redesign/overview-1440.png
