chiangr/bingbong/site/qa/redesign/reviewer/boop-1440.png

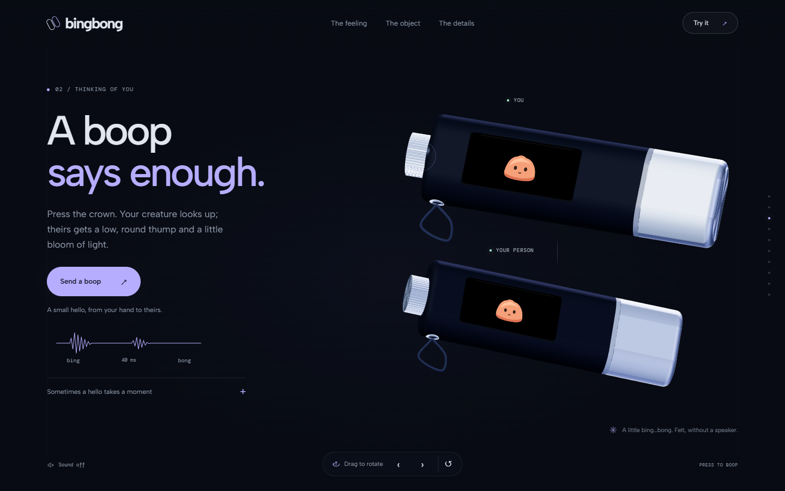
site/qa/redesign/reviewer/boop-1440.png
