chiangr/bingbong/site/qa/redesign/reviewer/boop-1920.png

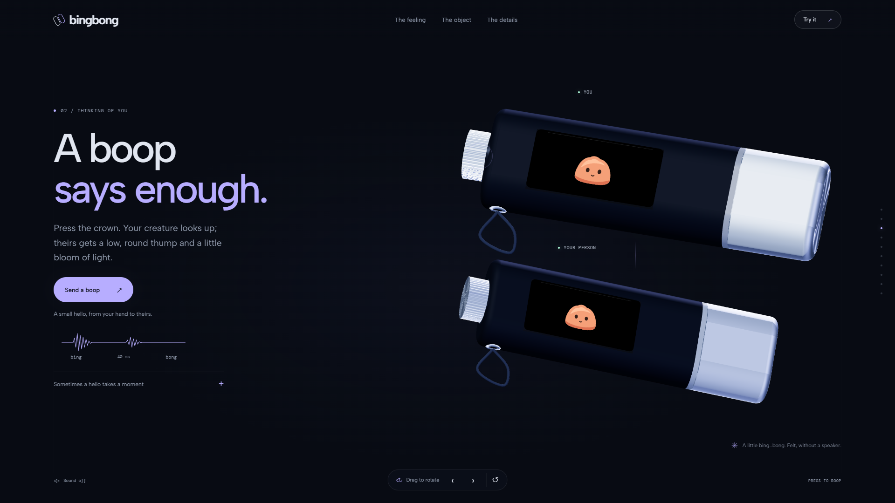
site/qa/redesign/reviewer/boop-1920.png
