chiangr/bingbong/site/qa/redesign/reviewer/creature-1920.png

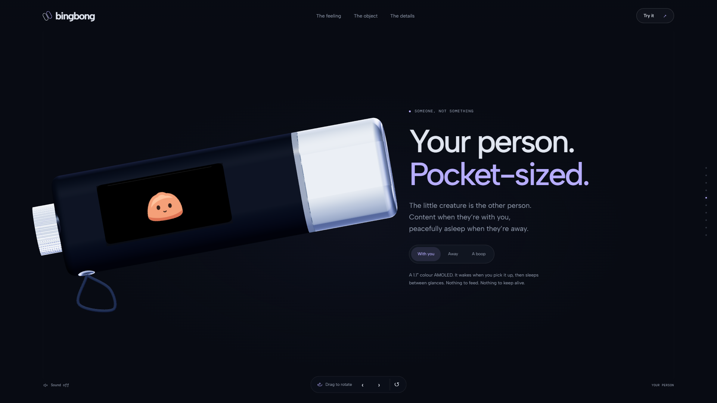
site/qa/redesign/reviewer/creature-1920.png
