chiangr/bingbong/site/qa/redesign/reviewer/details-390.png

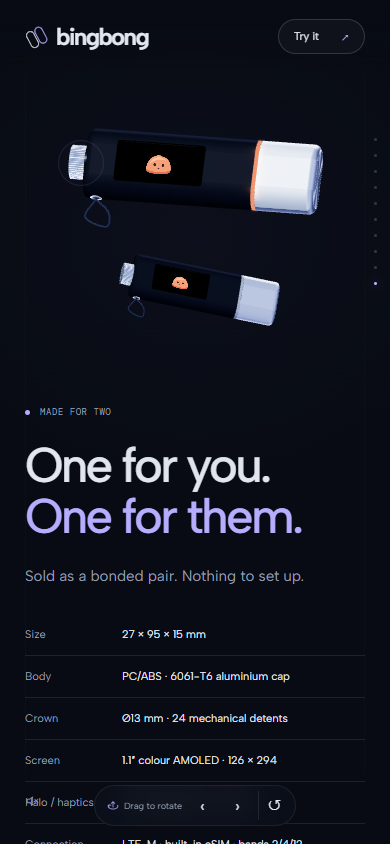
site/qa/redesign/reviewer/details-390.png
