chiangr/bingbong/site/qa/redesign/reviewer/details-1440.png

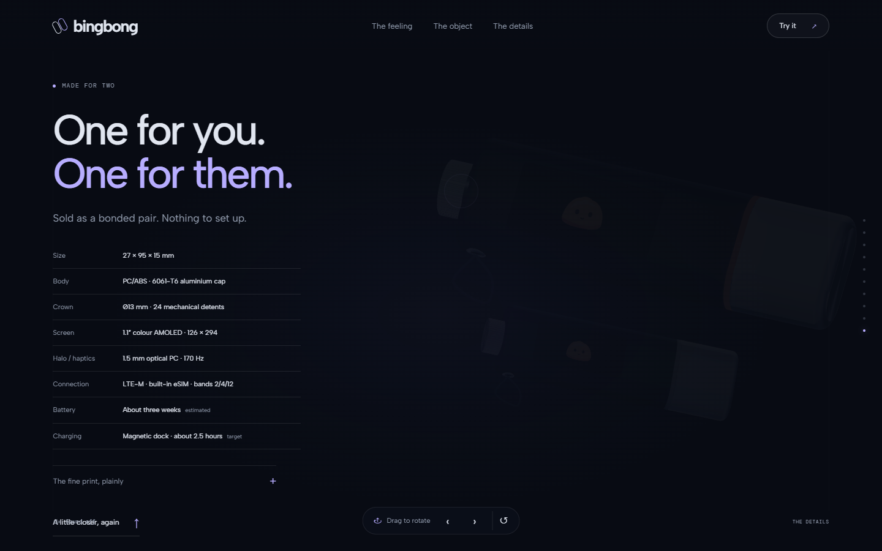
site/qa/redesign/reviewer/details-1440.png
