chiangr/bingbong/site/qa/redesign/reviewer/details-1920.png

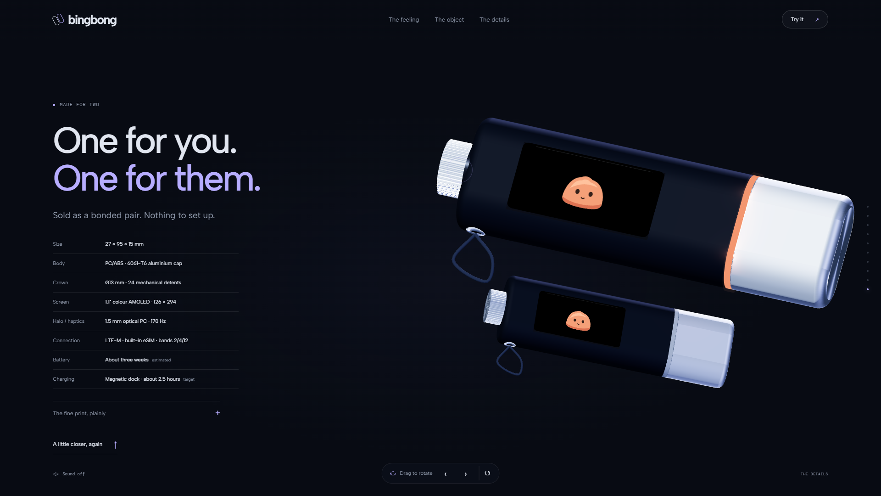
site/qa/redesign/reviewer/details-1920.png
