chiangr/bingbong/site/qa/redesign/reviewer/details-settled-1440.png

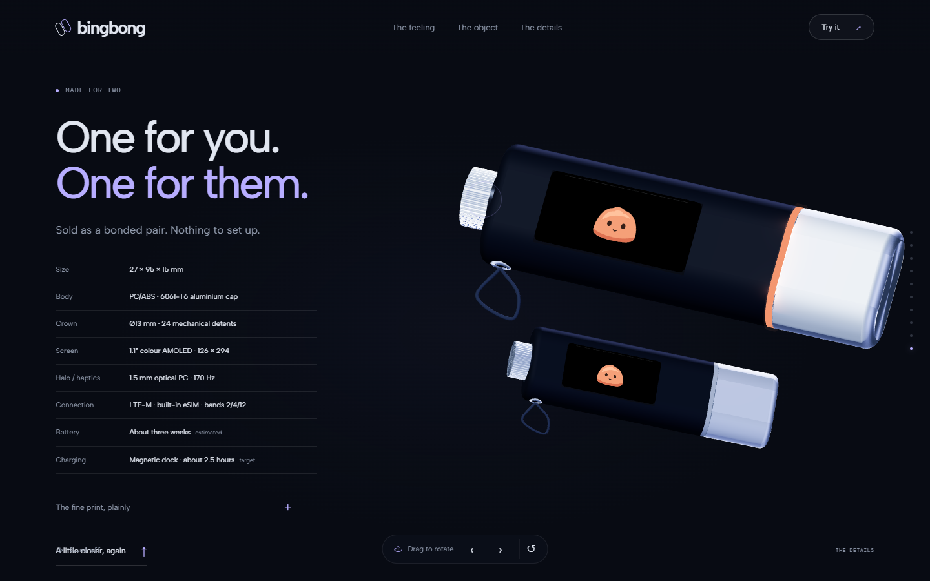
site/qa/redesign/reviewer/details-settled-1440.png
