chiangr/bingbong/site/qa/redesign/reviewer/fixed-boop-390.png

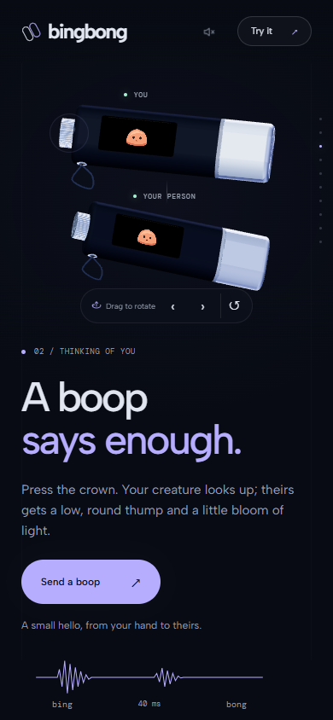
site/qa/redesign/reviewer/fixed-boop-390.png
