chiangr/bingbong/site/qa/redesign/reviewer/halo-390.png

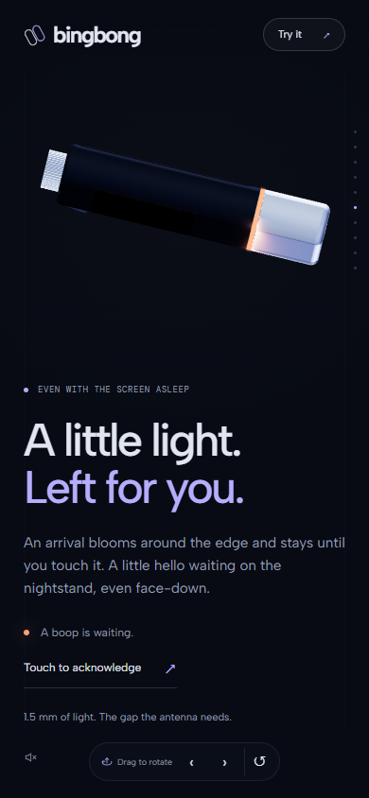
site/qa/redesign/reviewer/halo-390.png
