chiangr/bingbong/site/qa/redesign/reviewer/halo-820.png

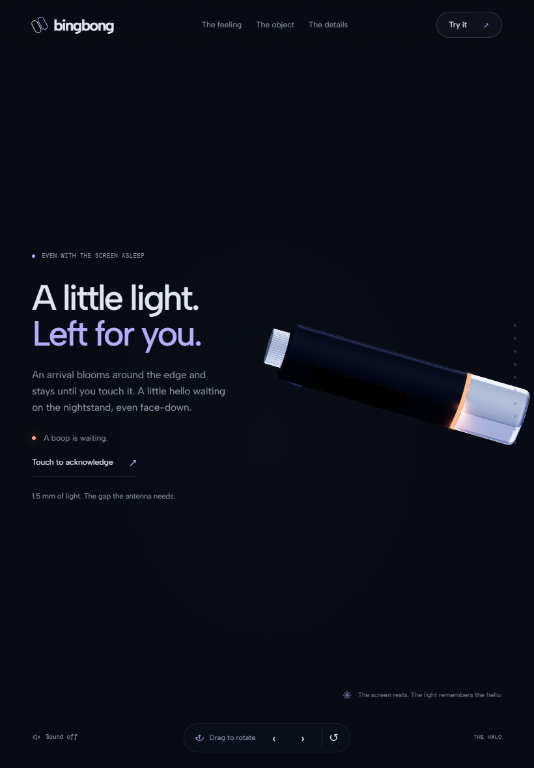
site/qa/redesign/reviewer/halo-820.png
