chiangr/bingbong/site/qa/redesign/reviewer/halo-1440.png

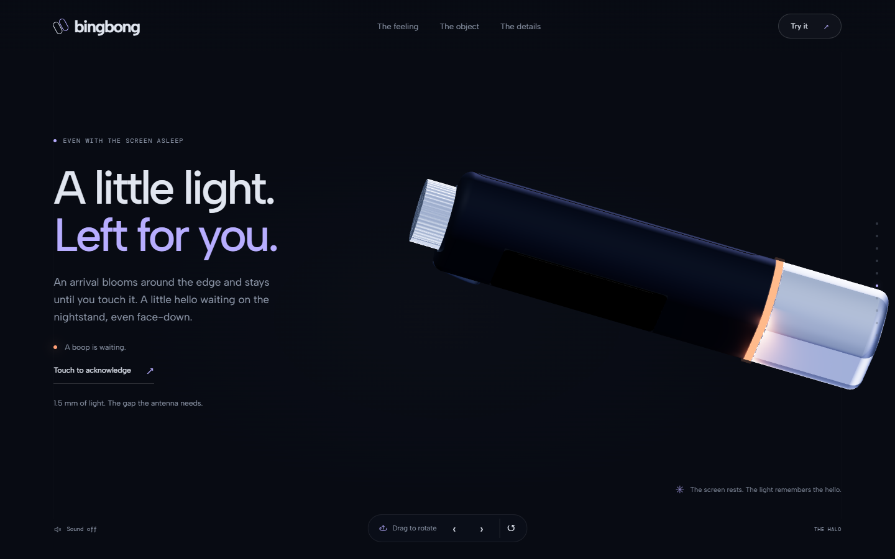
site/qa/redesign/reviewer/halo-1440.png
