chiangr/bingbong/site/qa/redesign/reviewer/halo-1920.png

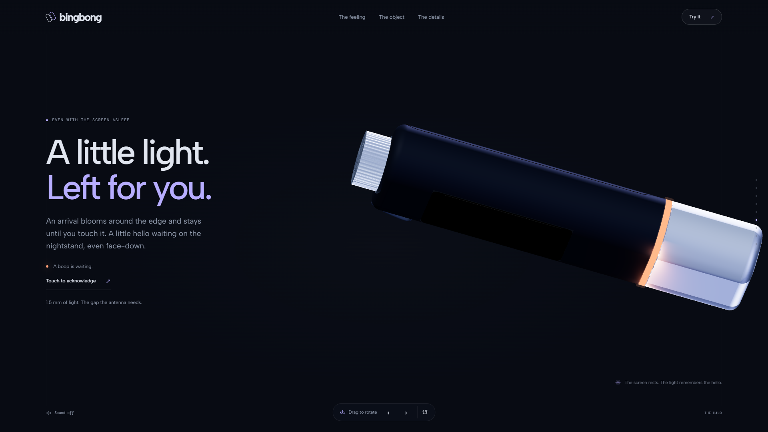
site/qa/redesign/reviewer/halo-1920.png
