chiangr/bingbong/site/qa/redesign/reviewer/hello-1920.png

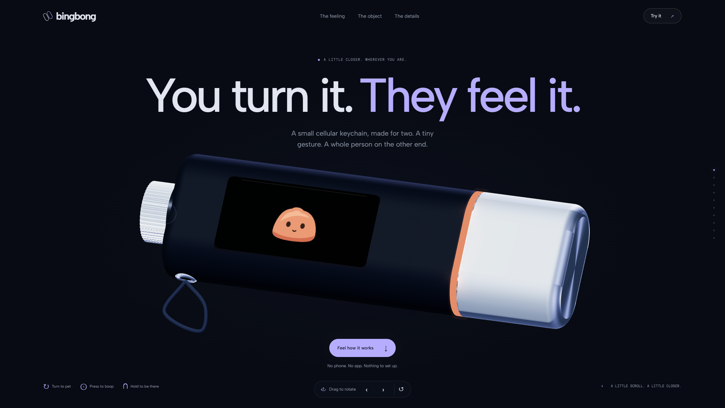
site/qa/redesign/reviewer/hello-1920.png
