chiangr/bingbong/site/qa/redesign/reviewer/hold-820.png

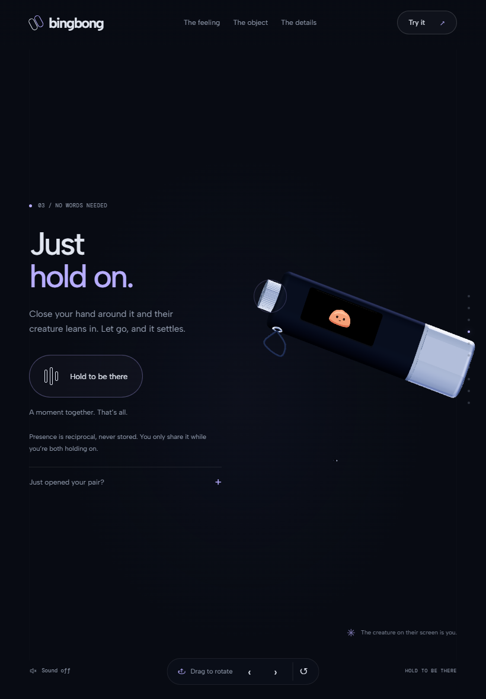
site/qa/redesign/reviewer/hold-820.png
