chiangr/bingbong/site/qa/redesign/reviewer/hold-1920.png

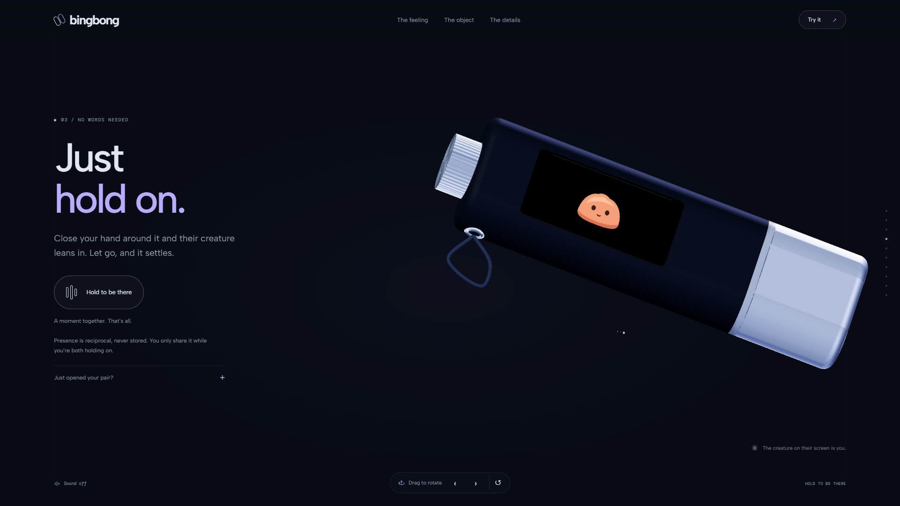
site/qa/redesign/reviewer/hold-1920.png
