chiangr/bingbong/site/qa/redesign/reviewer/object-1440.png

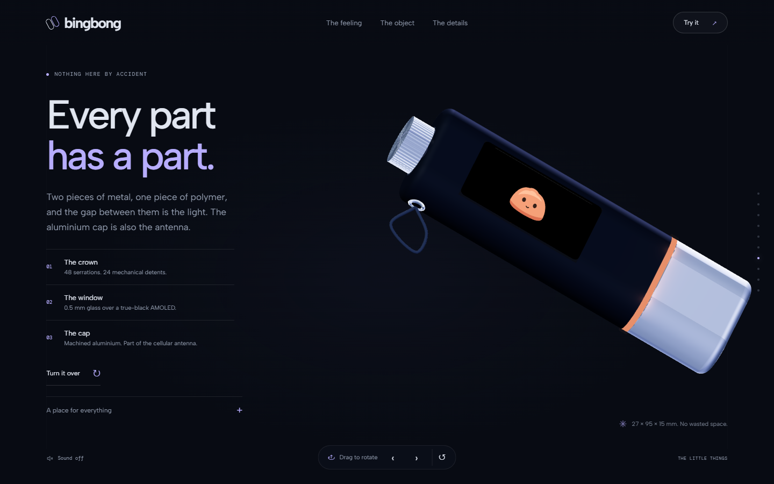
site/qa/redesign/reviewer/object-1440.png
