chiangr/bingbong/site/qa/redesign/reviewer/object-1920.png

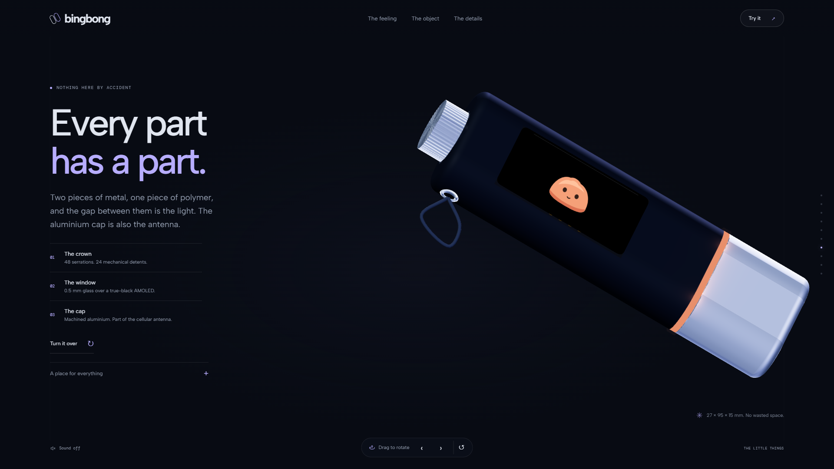
site/qa/redesign/reviewer/object-1920.png
