chiangr/bingbong/site/qa/redesign/reviewer/pet-390.png

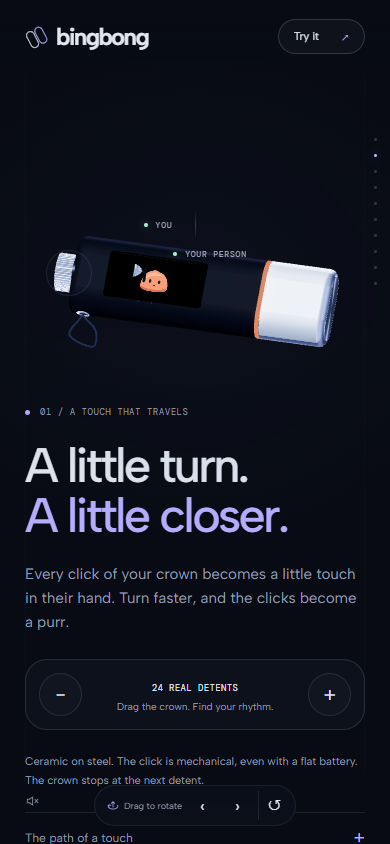
site/qa/redesign/reviewer/pet-390.png
