chiangr/bingbong/site/qa/redesign/reviewer/pet-820.png

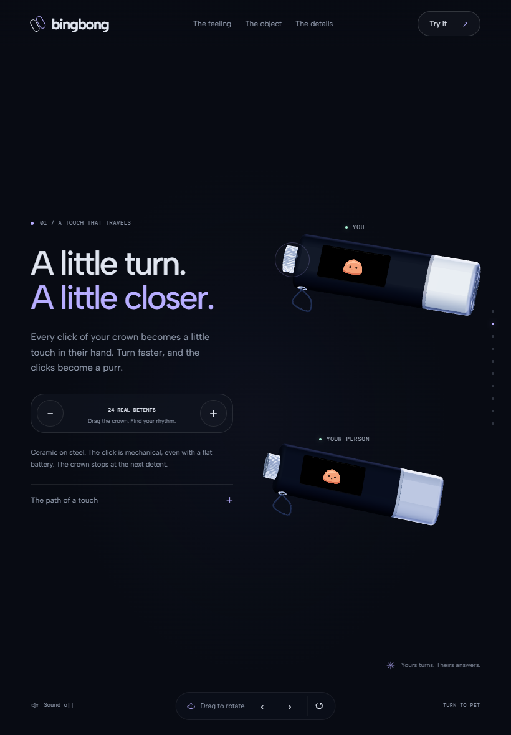
site/qa/redesign/reviewer/pet-820.png
