chiangr/bingbong/site/qa/redesign/reviewer/pet-1440.png

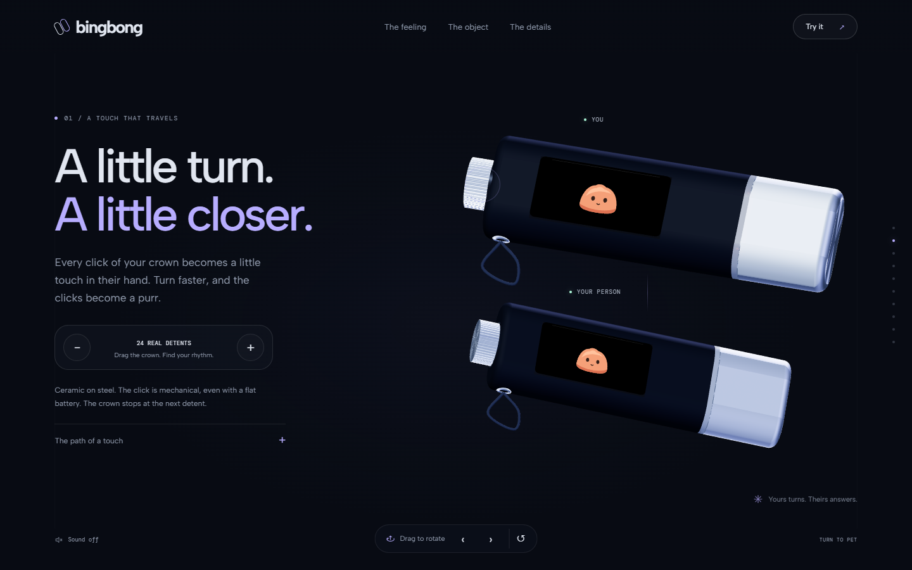
site/qa/redesign/reviewer/pet-1440.png
