chiangr/bingbong/site/qa/redesign/reviewer/pet-1920.png

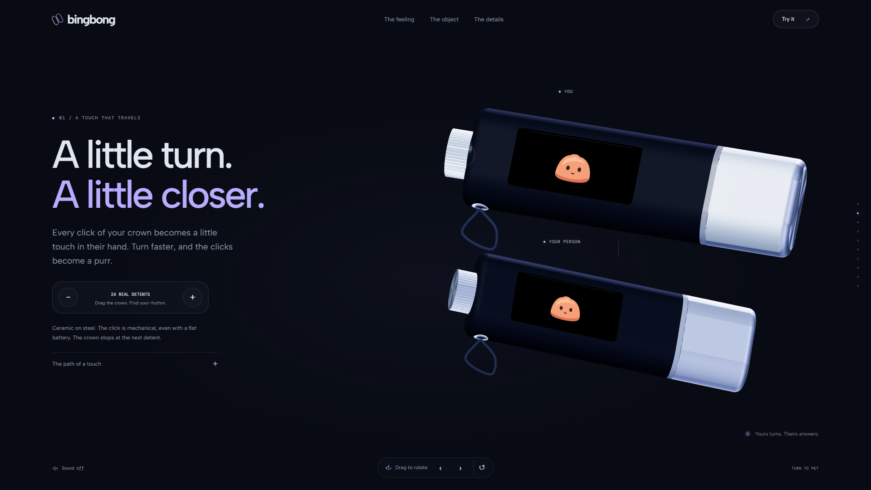
site/qa/redesign/reviewer/pet-1920.png
