chiangr/bingbong/site/qa/redesign/reviewer/quiet-820.png

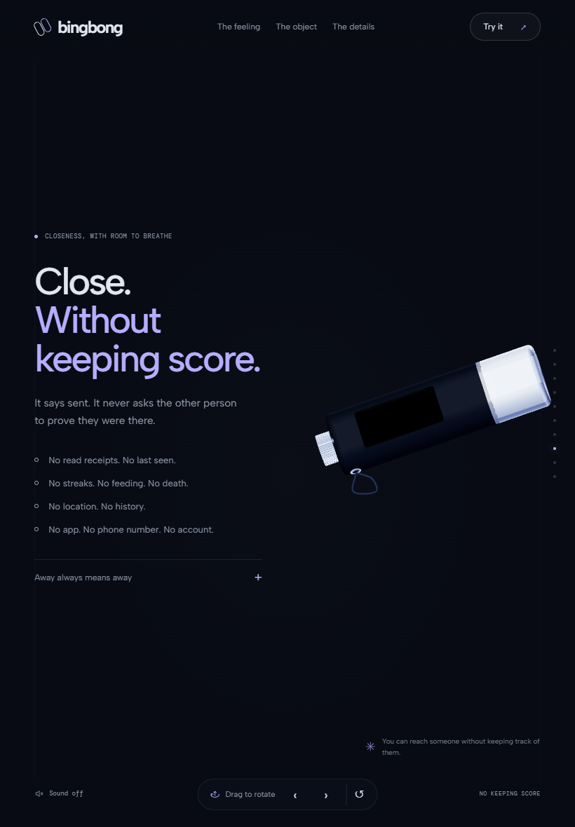
site/qa/redesign/reviewer/quiet-820.png
