chiangr/bingbong/site/qa/redesign/reviewer/quiet-1440.png

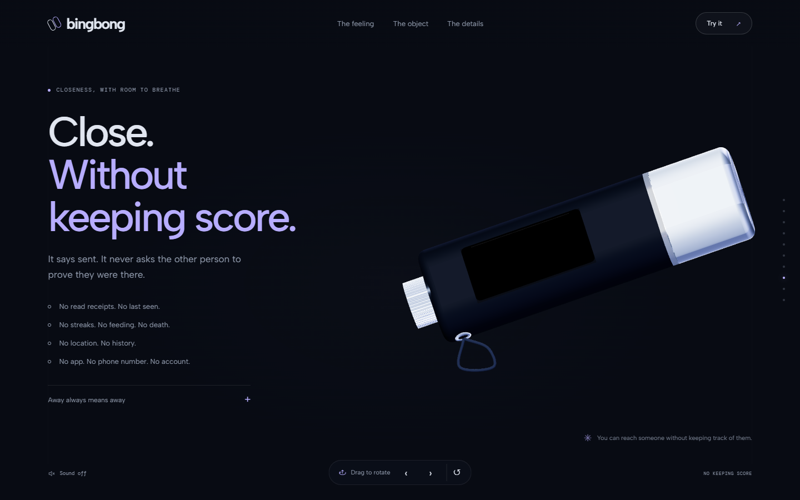
site/qa/redesign/reviewer/quiet-1440.png
