chiangr/bingbong/site/qa/redesign/reviewer/quiet-1920.png

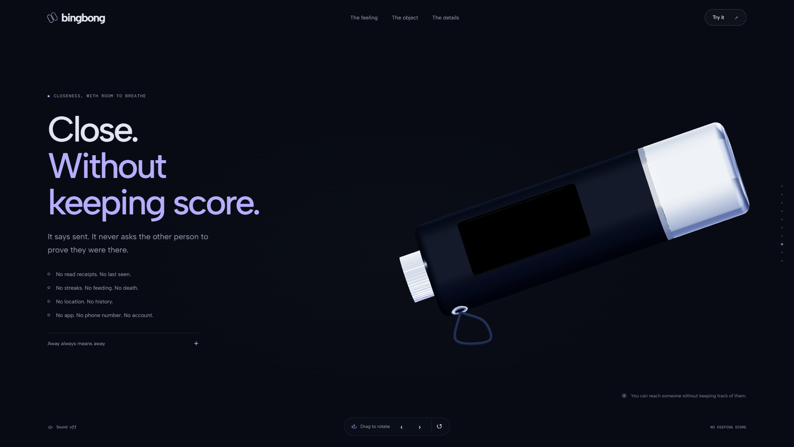
site/qa/redesign/reviewer/quiet-1920.png
