chiangr/bingbong/site/qa/redesign/reviewer/size-1920.png

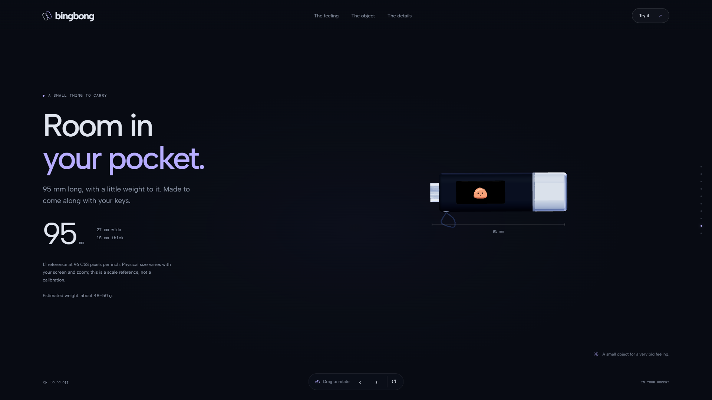
site/qa/redesign/reviewer/size-1920.png
