chiangr/bingbong/site/qa/references/active-theory-390.png

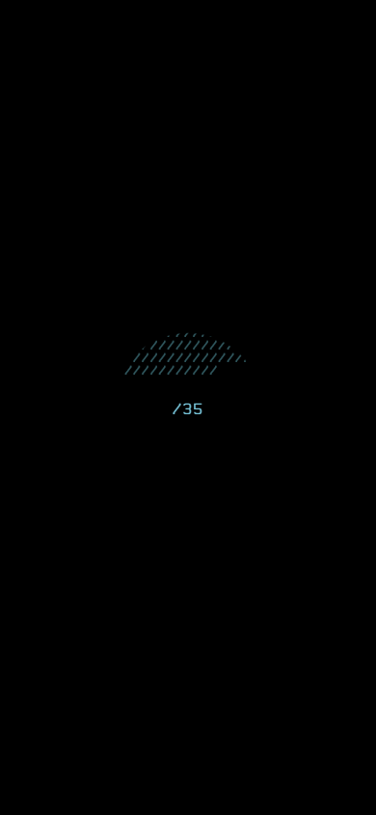
site/qa/references/active-theory-390.png
