chiangr/bingbong/site/qa/scroll/overview-390.png

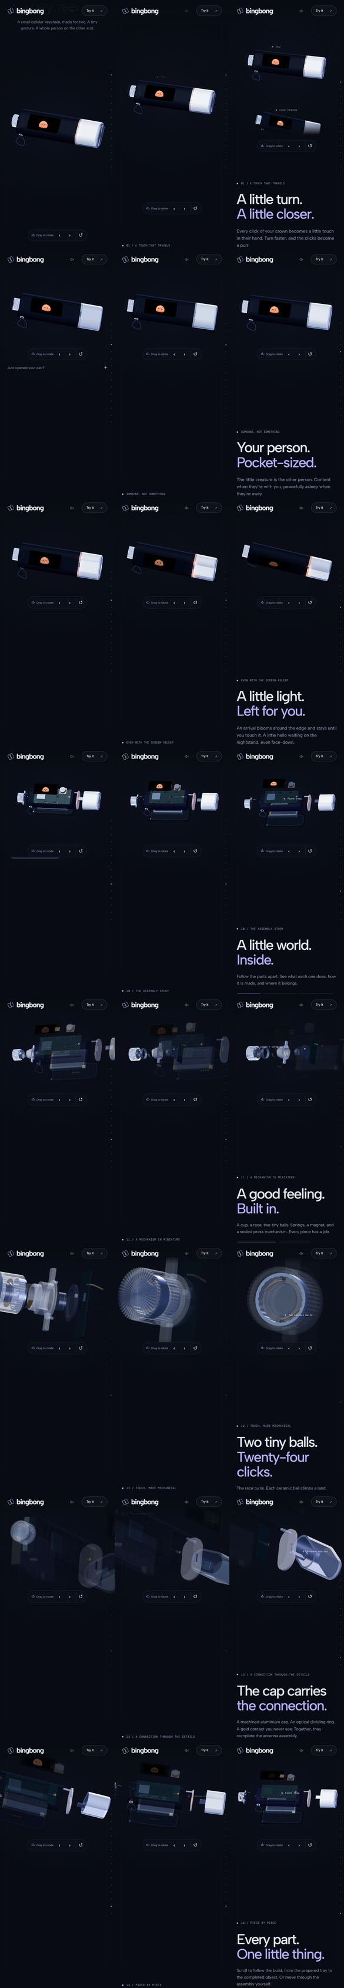
site/qa/scroll/overview-390.png
