chiangr/bingbong/site/qa/scroll/overview-1440.png

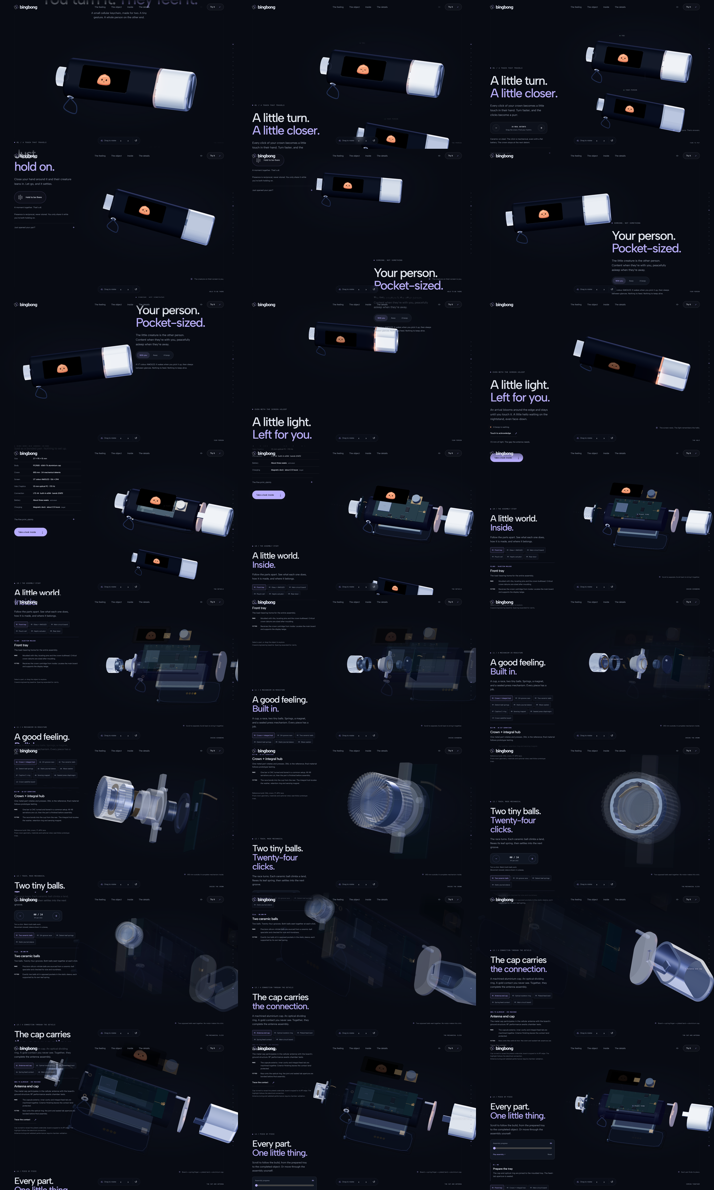
site/qa/scroll/overview-1440.png
