chiangr/bingbong/bom-scratch/fh12_p4.png

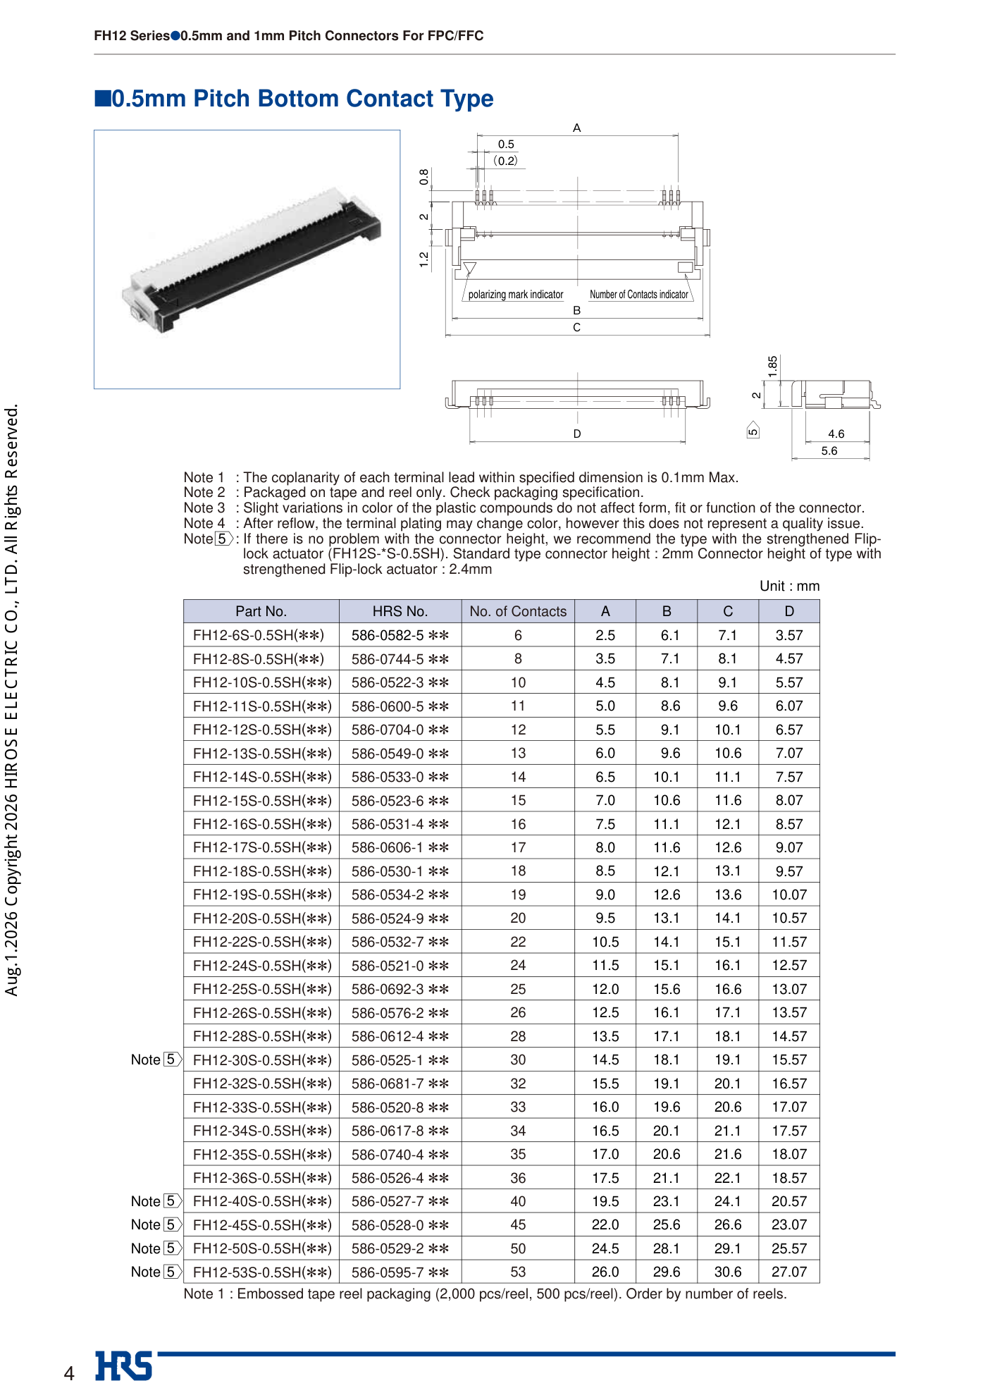
bom-scratch/fh12_p4.png
