chiangr/bingbong/bom-scratch/fh12_p6.png

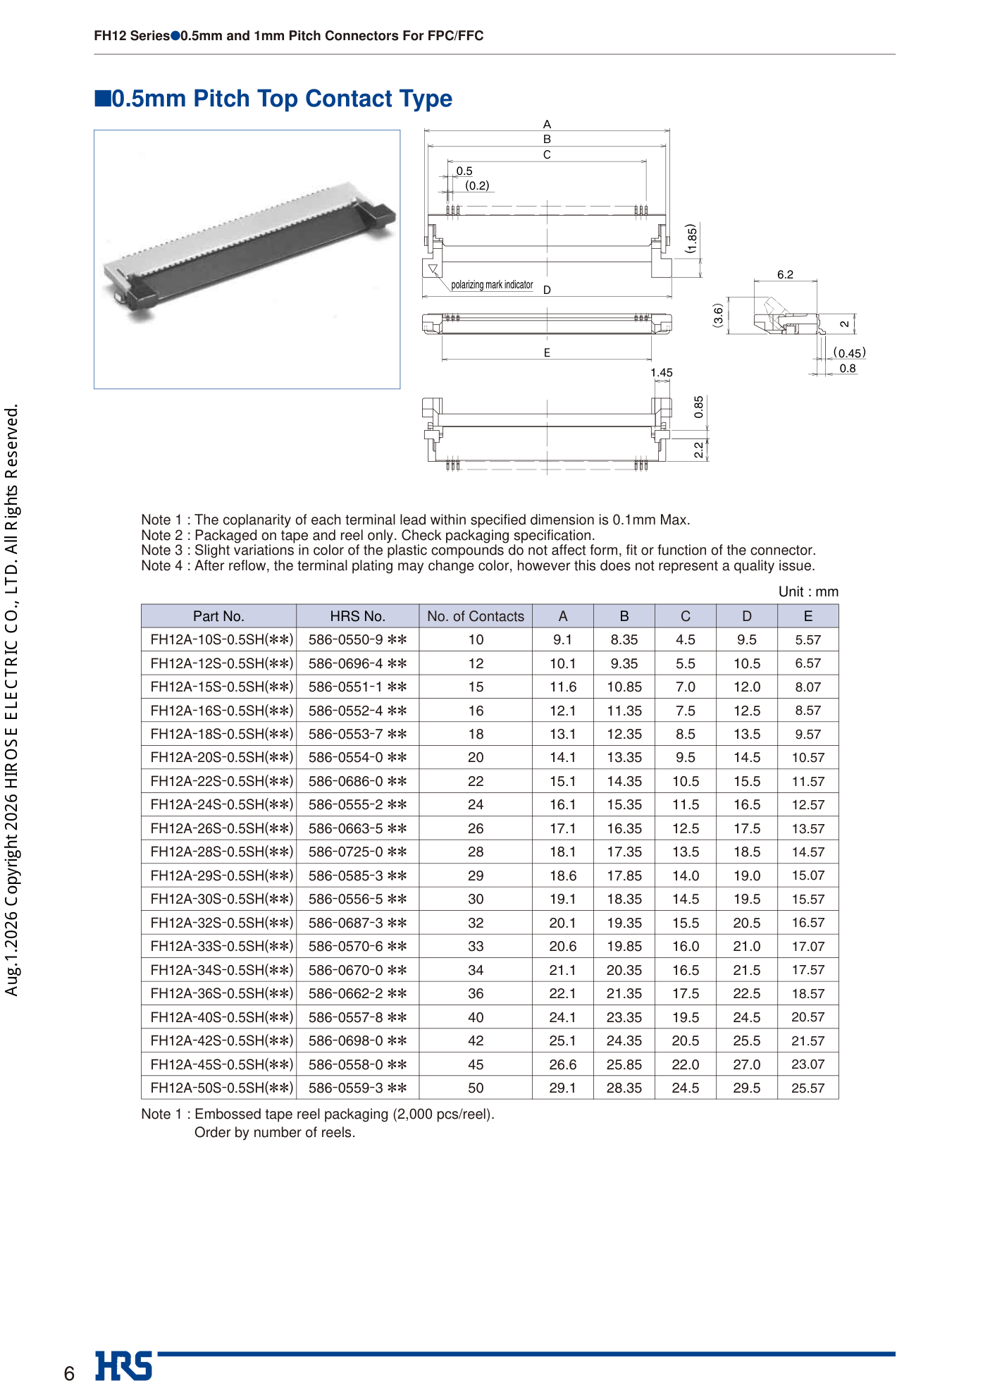
bom-scratch/fh12_p6.png
