chiangr/bingbong/bom-scratch/ntc_pg.png

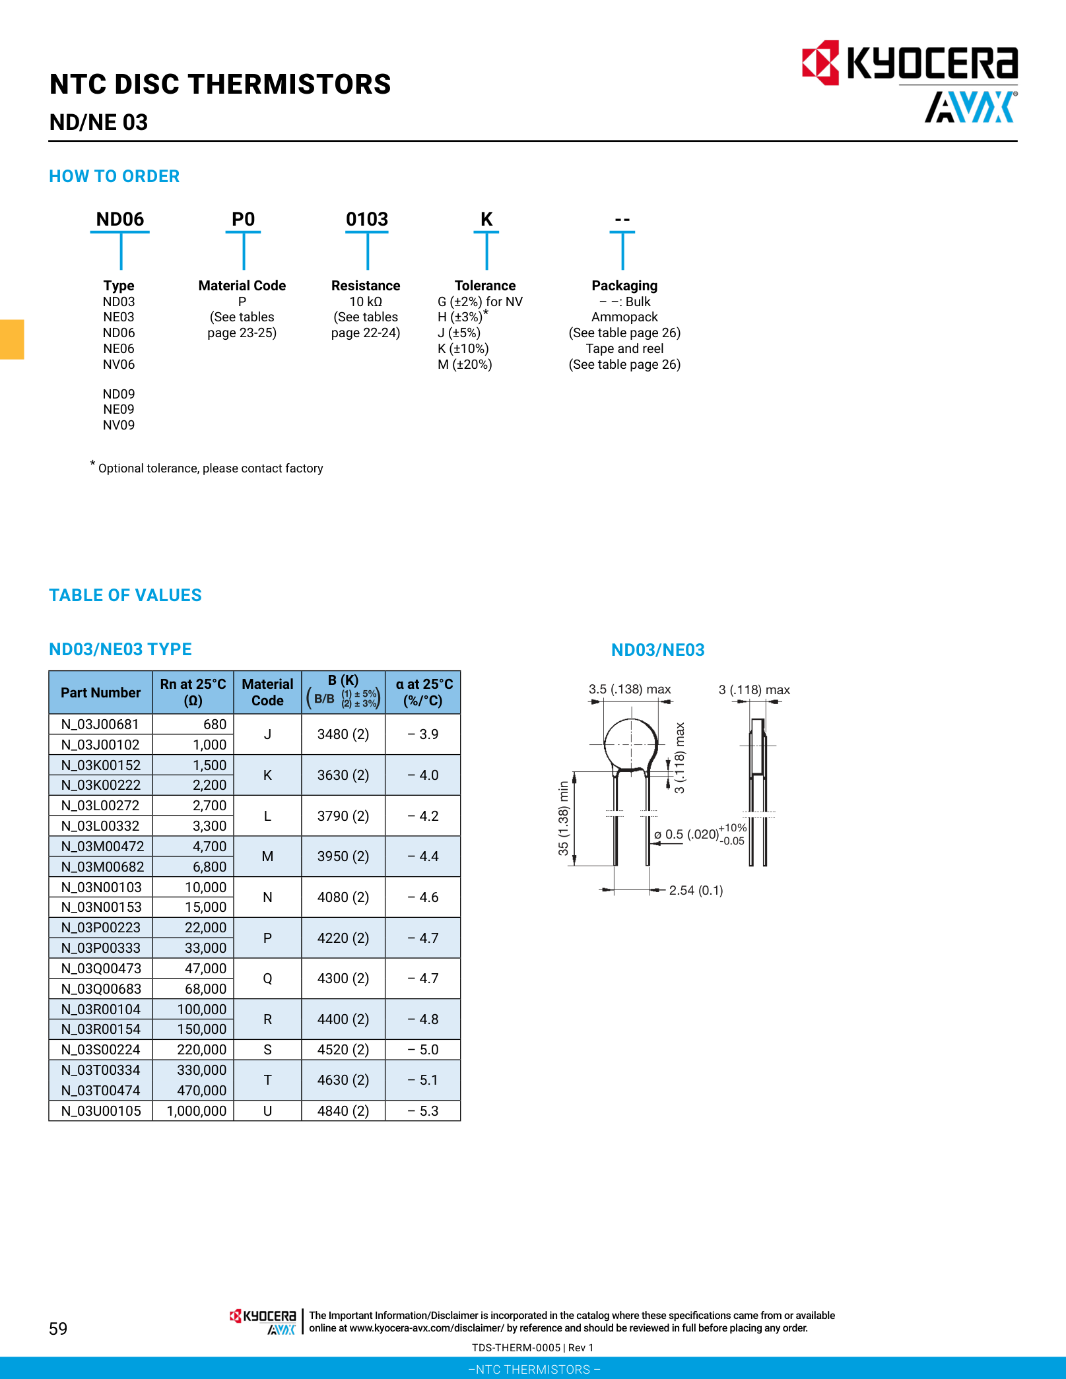
bom-scratch/ntc_pg.png
