chiangr/bingbong/bom-scratch/sim_p1.png

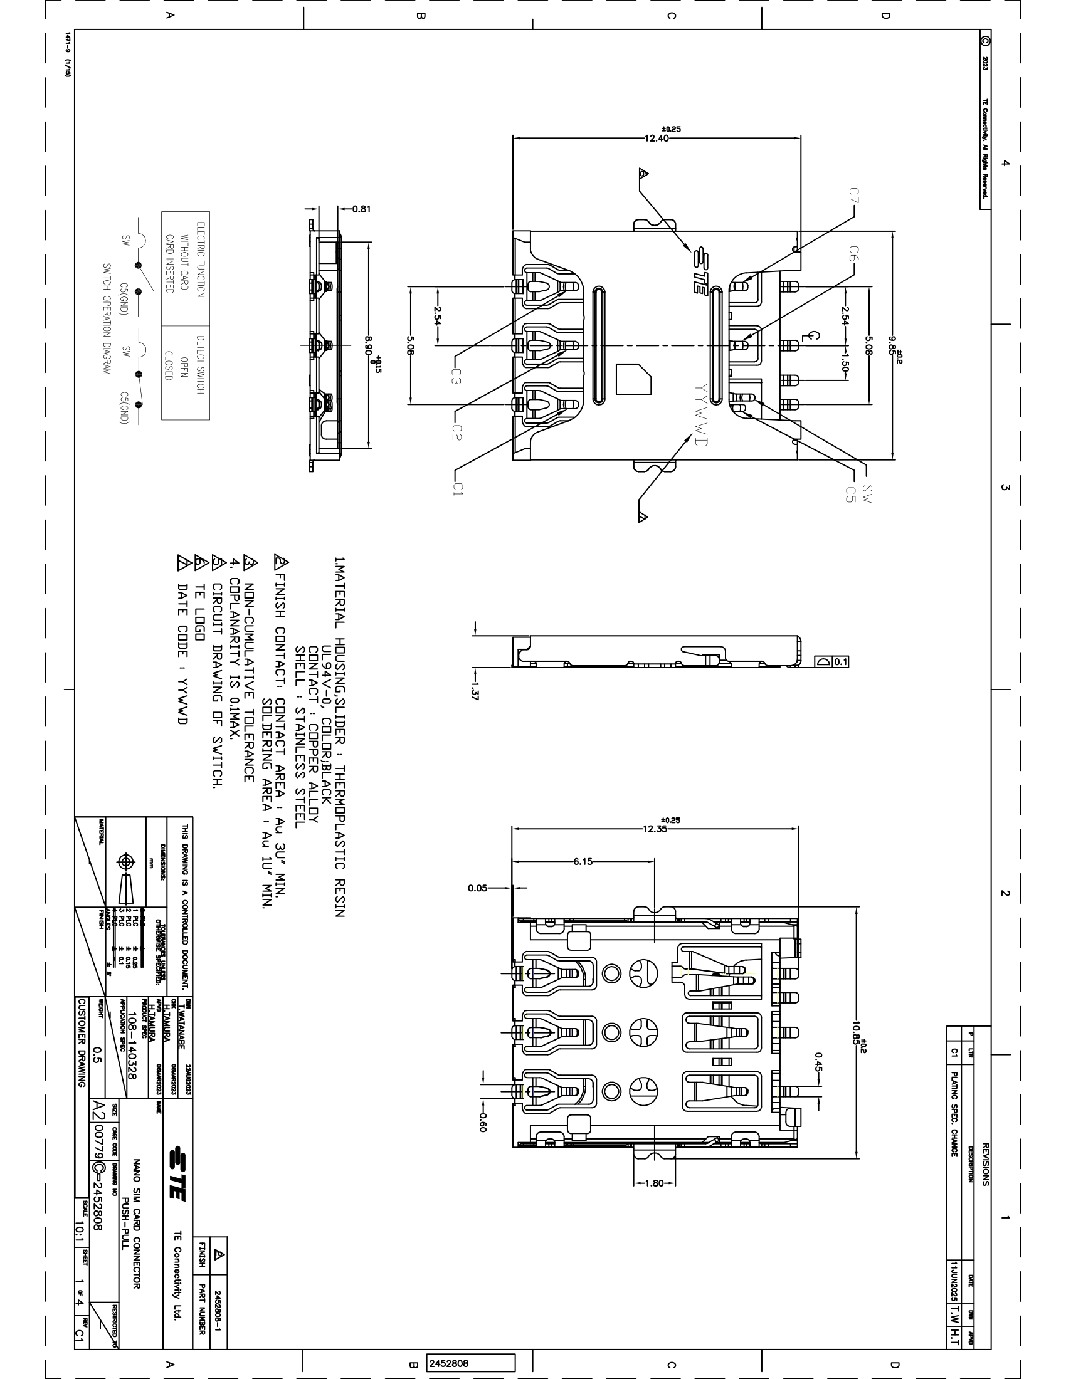
bom-scratch/sim_p1.png
