chiangr/bingbong/bom-scratch/sim_p2.png

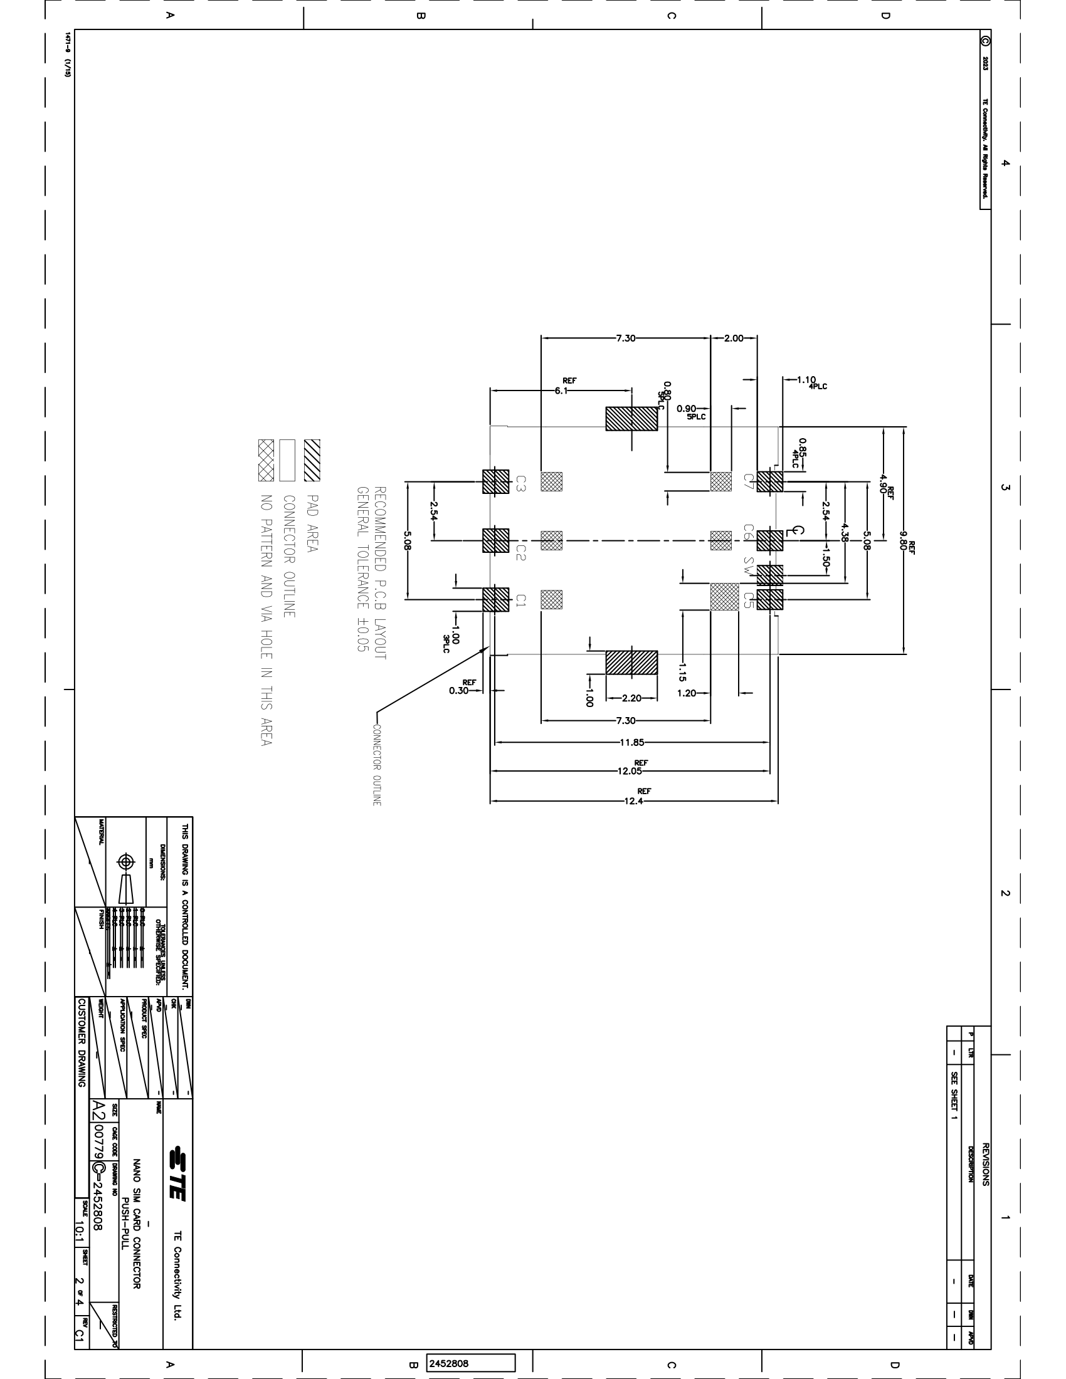
bom-scratch/sim_p2.png
