chiangr/bingbong/bom-scratch/sim_p3.png

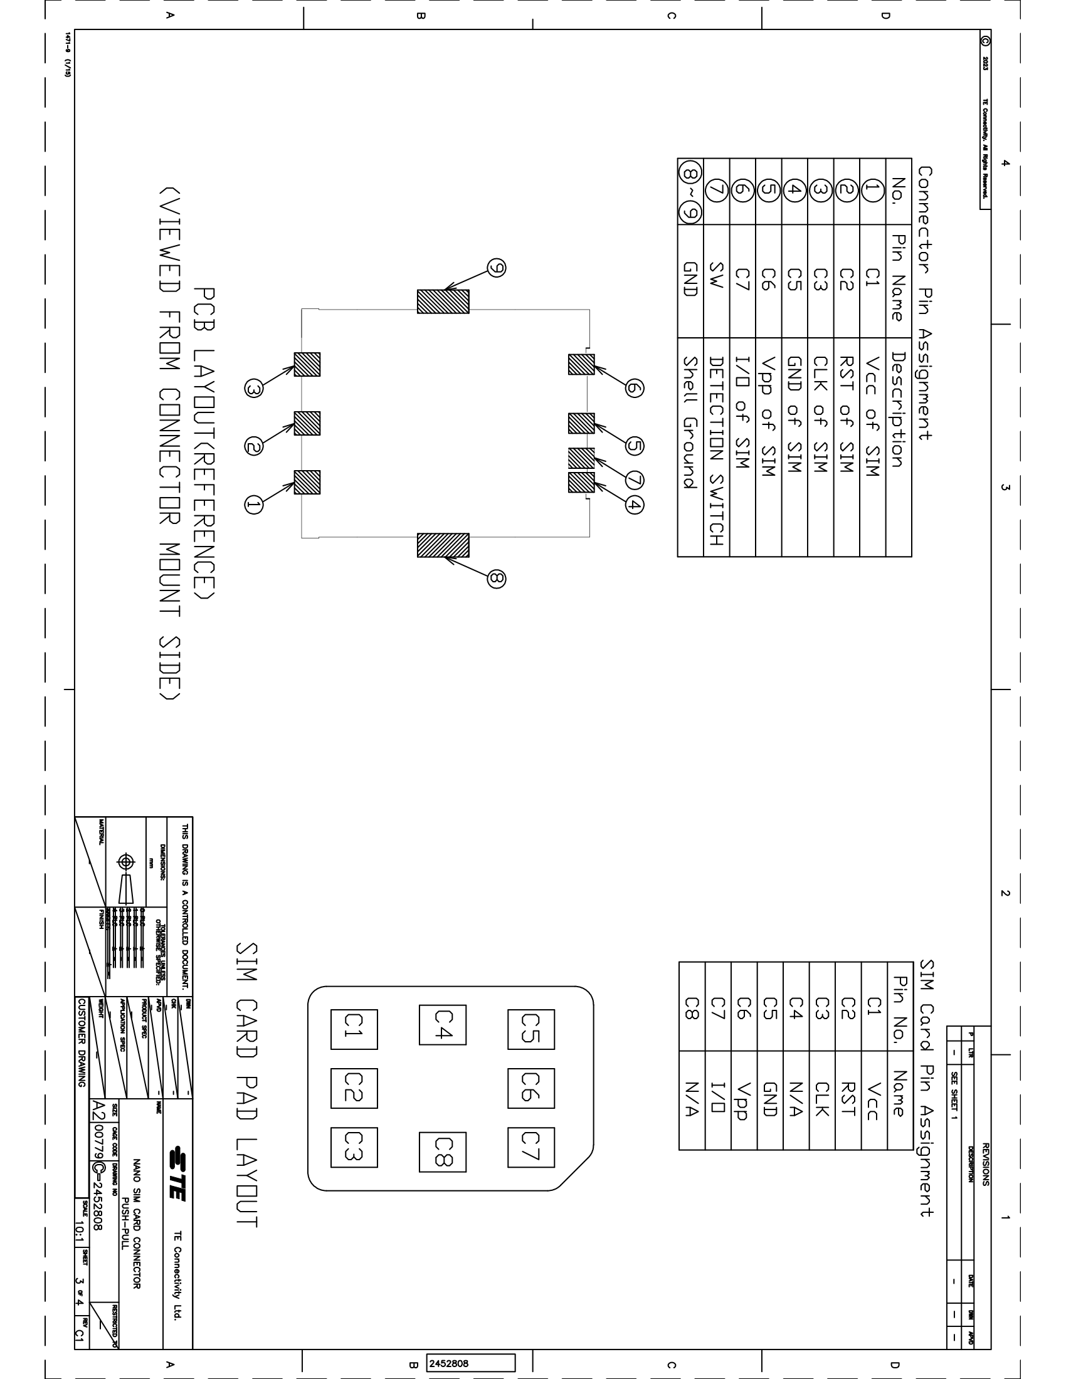
bom-scratch/sim_p3.png
