chiangr/bingbong/bom-scratch/sim_p4.png

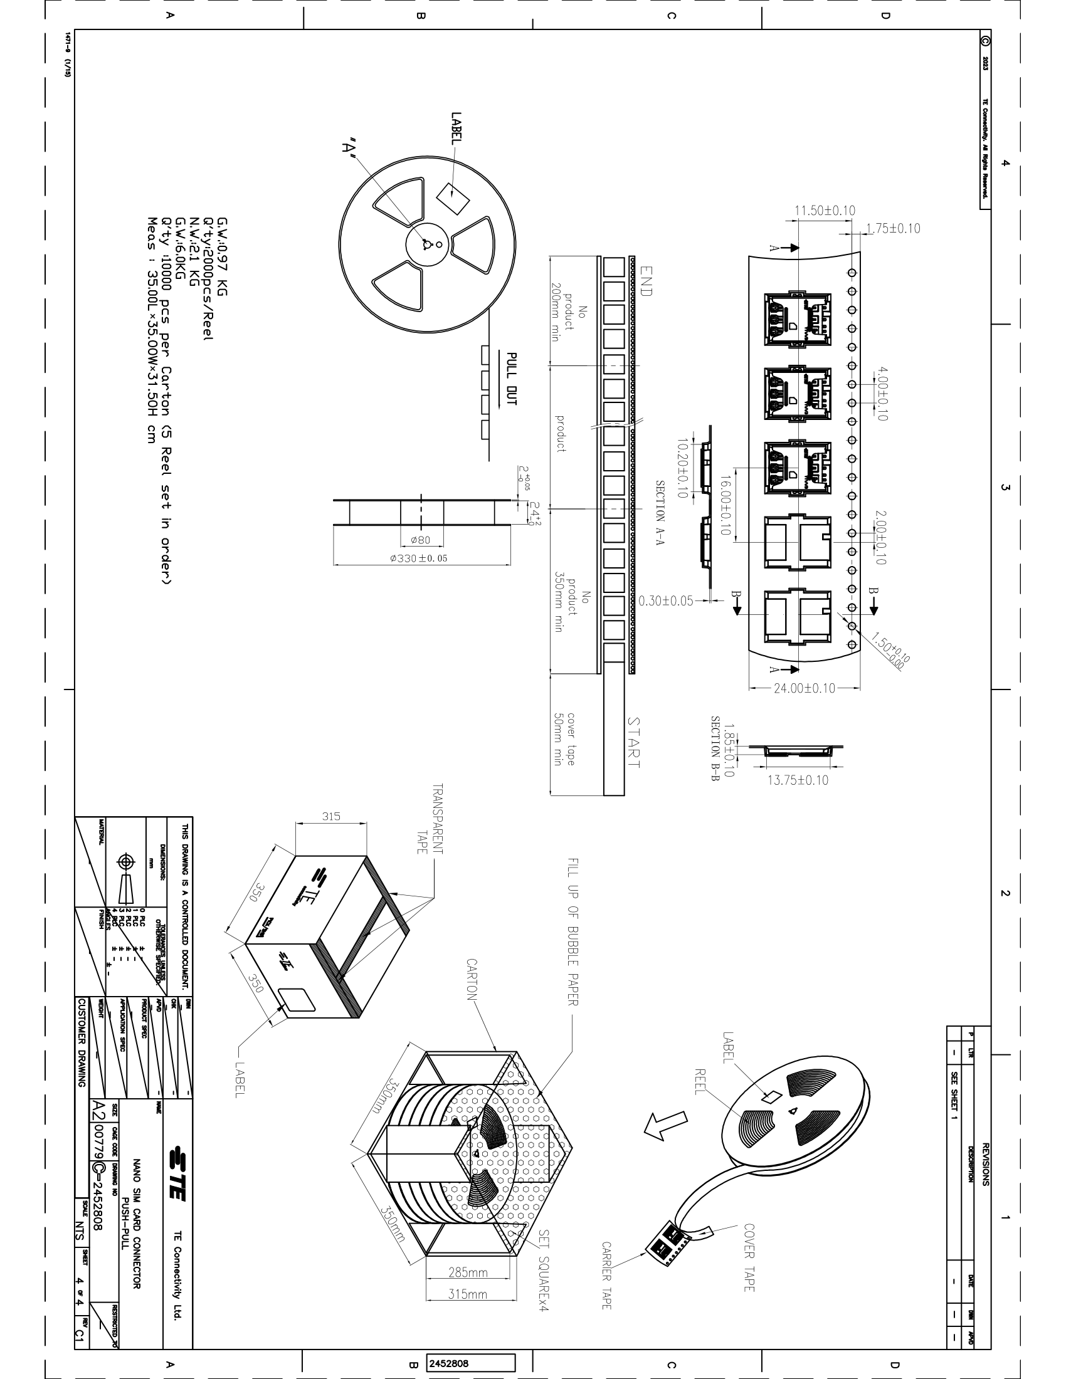
bom-scratch/sim_p4.png
