chiangr/bingbong/site/qa/rf/deep/390-component.png

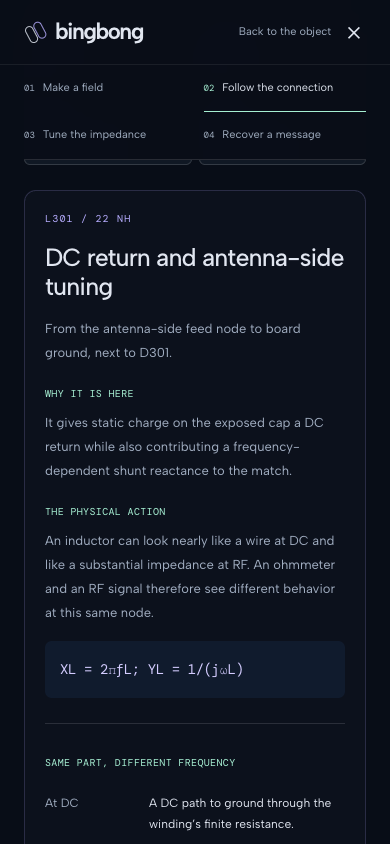
site/qa/rf/deep/390-component.png
