chiangr/bingbong/site/qa/assembly/390-antenna.png

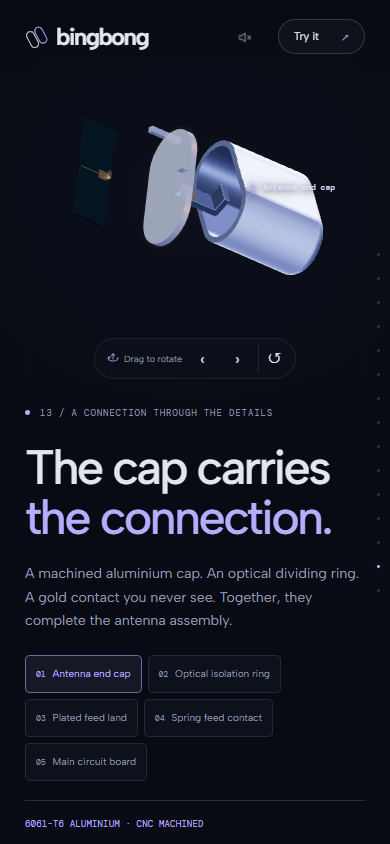
site/qa/assembly/390-antenna.png
