chiangr/bingbong/site/qa/assembly/390-assembled.png

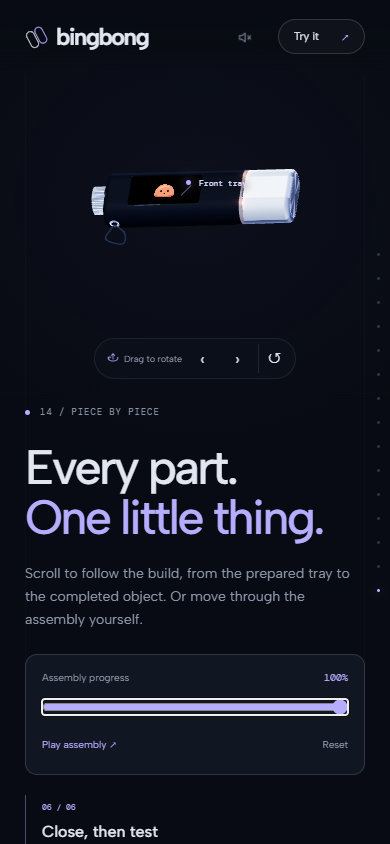
site/qa/assembly/390-assembled.png
