chiangr/bingbong/site/qa/assembly/390-assembly.png

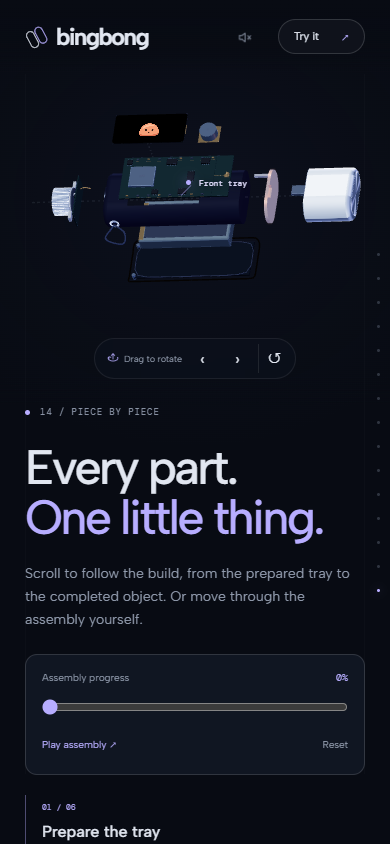
site/qa/assembly/390-assembly.png
