chiangr/bingbong/site/qa/assembly/390-crown.png

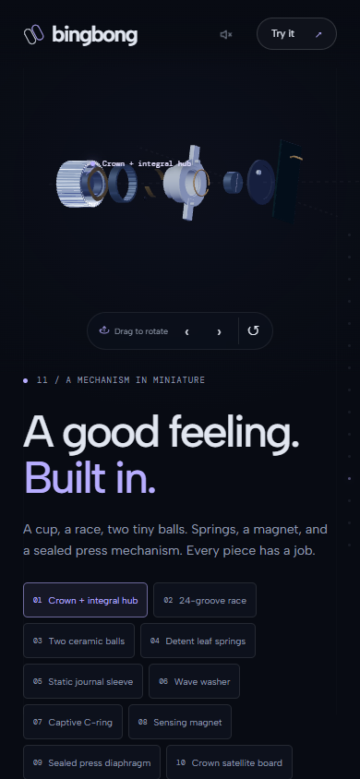
site/qa/assembly/390-crown.png
