chiangr/bingbong/site/qa/assembly/390-detents.png

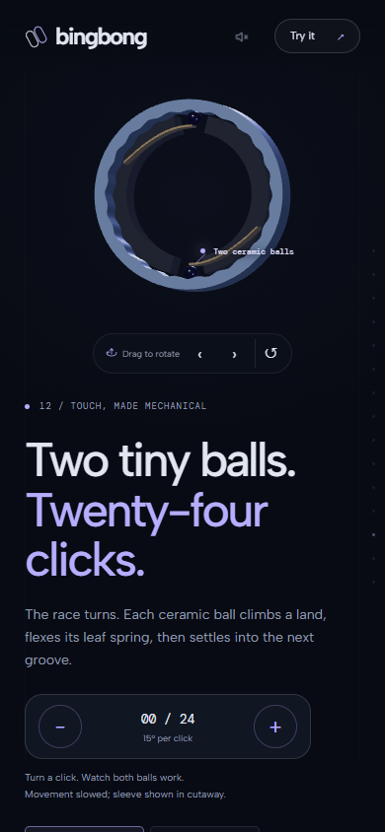
site/qa/assembly/390-detents.png
