chiangr/bingbong/site/qa/assembly/390-hello.png

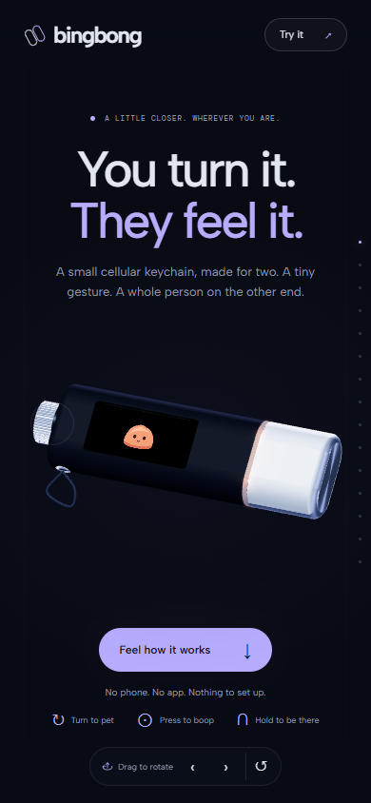
site/qa/assembly/390-hello.png
