chiangr/bingbong/site/qa/assembly/390-inside.png

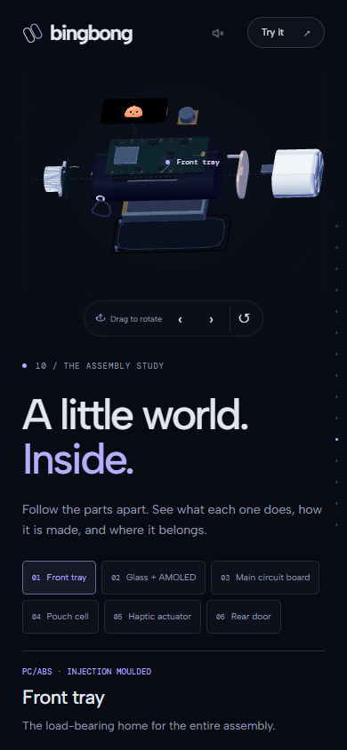
site/qa/assembly/390-inside.png
