chiangr/bingbong/site/qa/assembly/1440-antenna.png

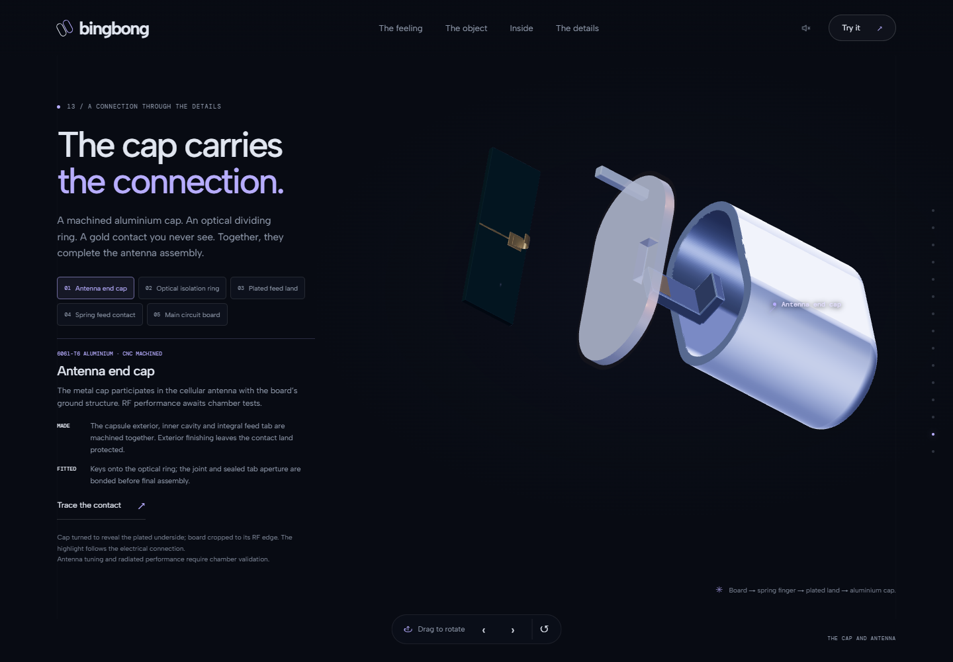
site/qa/assembly/1440-antenna.png
