chiangr/bingbong/site/qa/assembly/1440-assembled.png

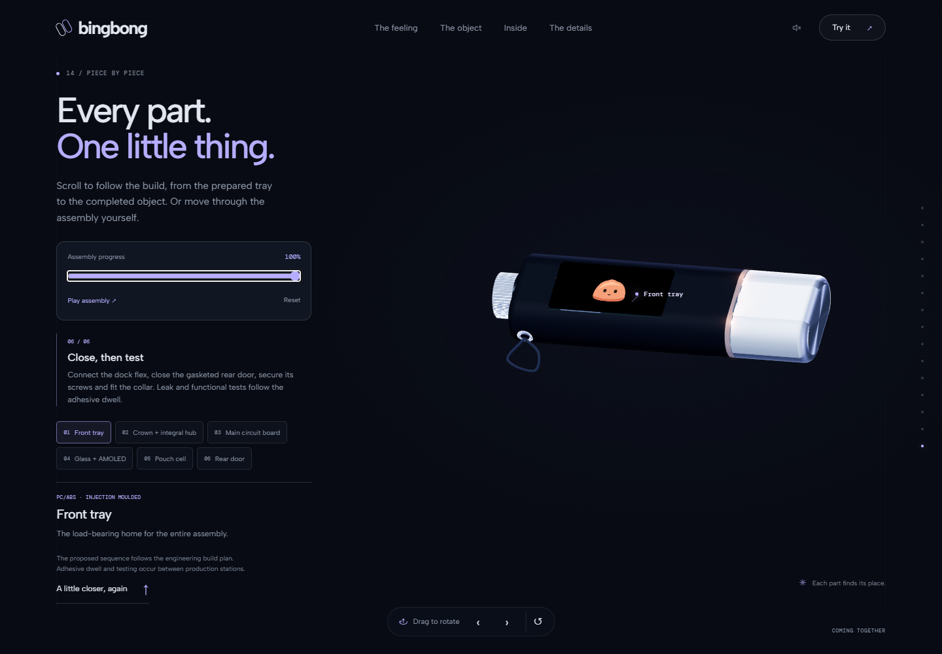
site/qa/assembly/1440-assembled.png
