chiangr/bingbong/site/qa/assembly/1440-assembly.png

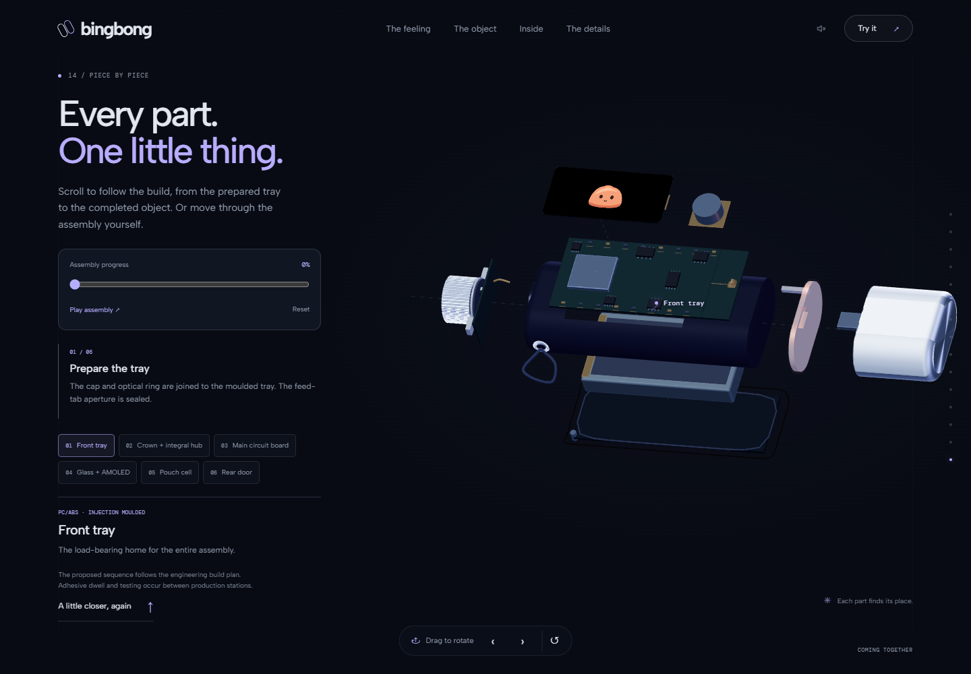
site/qa/assembly/1440-assembly.png
