chiangr/bingbong/site/qa/assembly/1440-crown.png

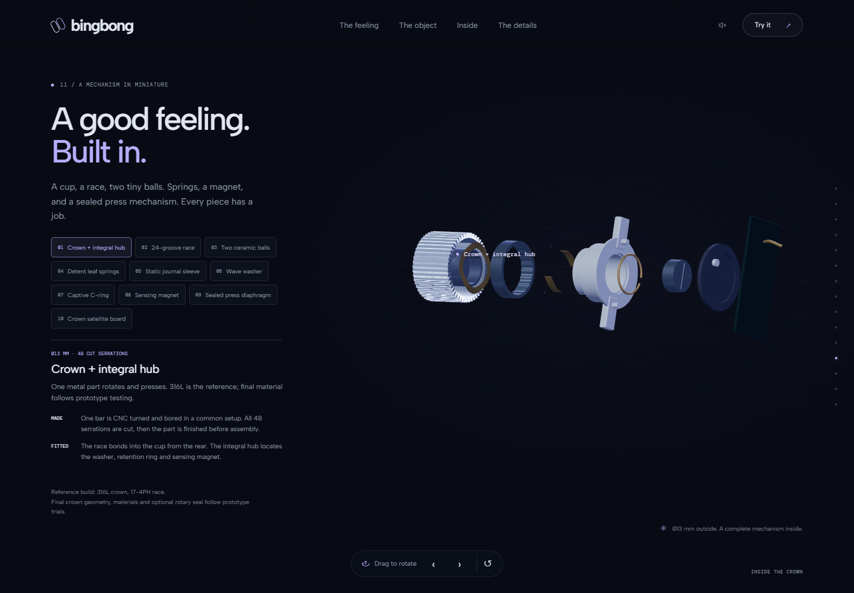
site/qa/assembly/1440-crown.png
