chiangr/bingbong/site/qa/assembly/1440-detents.png

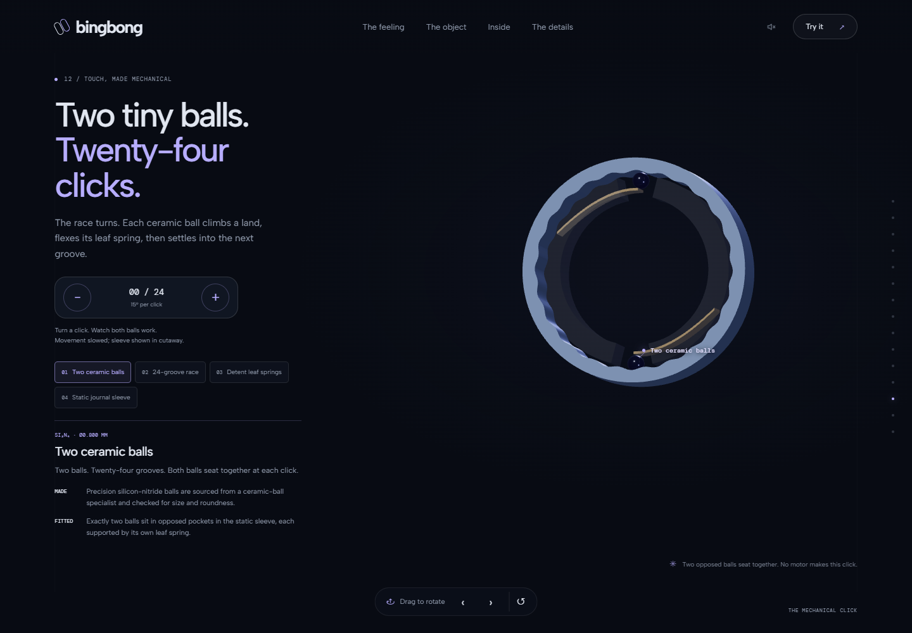
site/qa/assembly/1440-detents.png
