chiangr/bingbong/site/qa/assembly/1440-inside.png

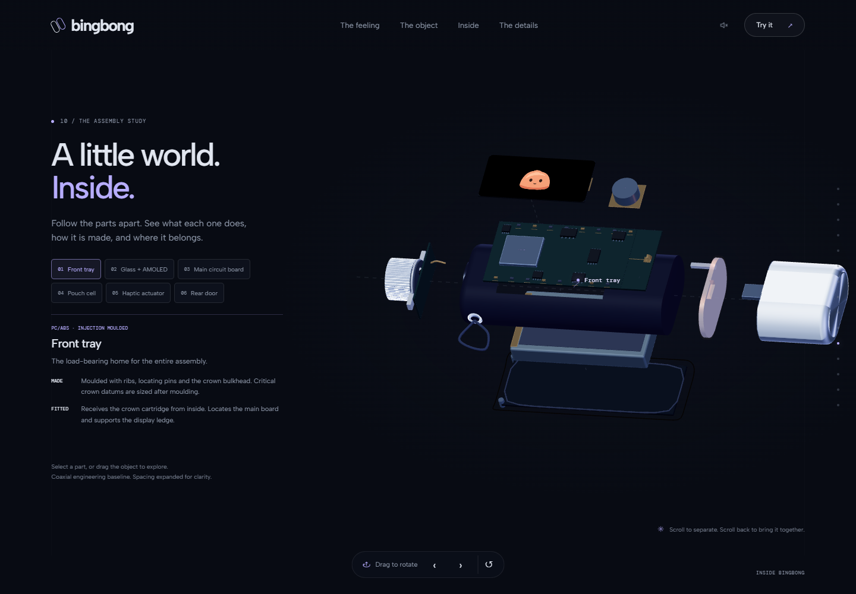
site/qa/assembly/1440-inside.png
