chiangr/bingbong/site/qa/assembly/reviewer-390-antenna-scroll400.png

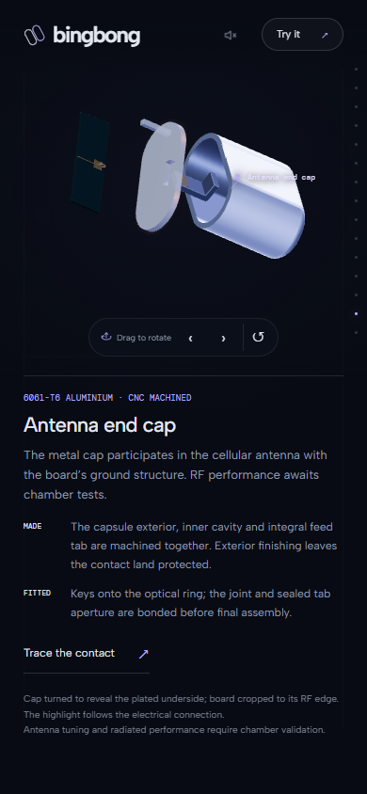
site/qa/assembly/reviewer-390-antenna-scroll400.png
