chiangr/bingbong/site/qa/assembly/reviewer-390-assembly-scroll500.png

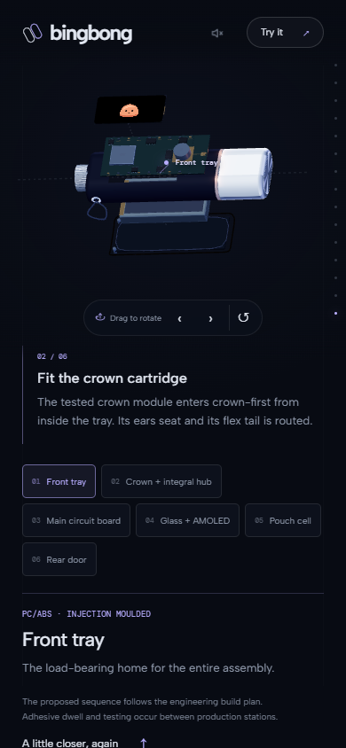
site/qa/assembly/reviewer-390-assembly-scroll500.png
