chiangr/bingbong/site/qa/assembly/reviewer-390-crown-scroll500.png

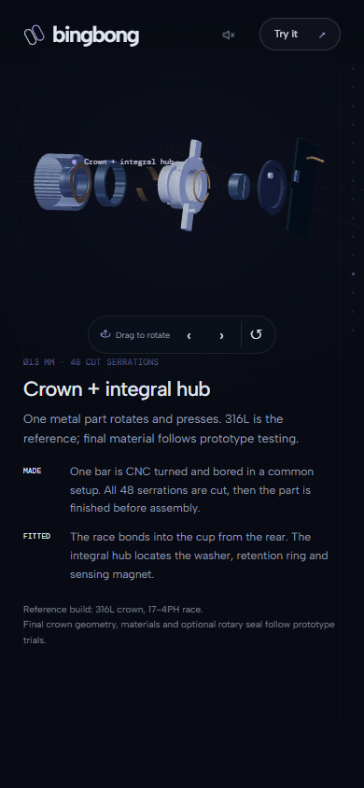
site/qa/assembly/reviewer-390-crown-scroll500.png
