chiangr/bingbong/site/qa/assembly/reviewer-390-detents-scroll390.png

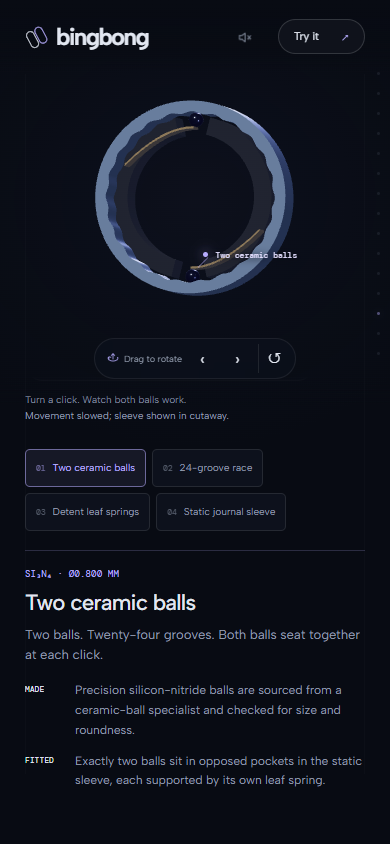
site/qa/assembly/reviewer-390-detents-scroll390.png
