chiangr/bingbong/site/qa/assembly/reviewer-390-inside.png

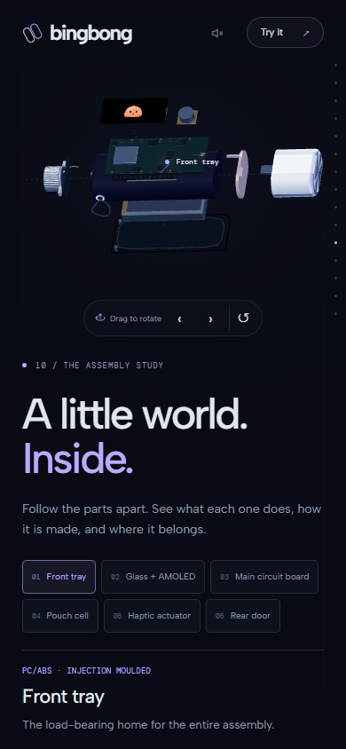
site/qa/assembly/reviewer-390-inside.png
