chiangr/bingbong/site/qa/assembly/reviewer-820-antenna.png

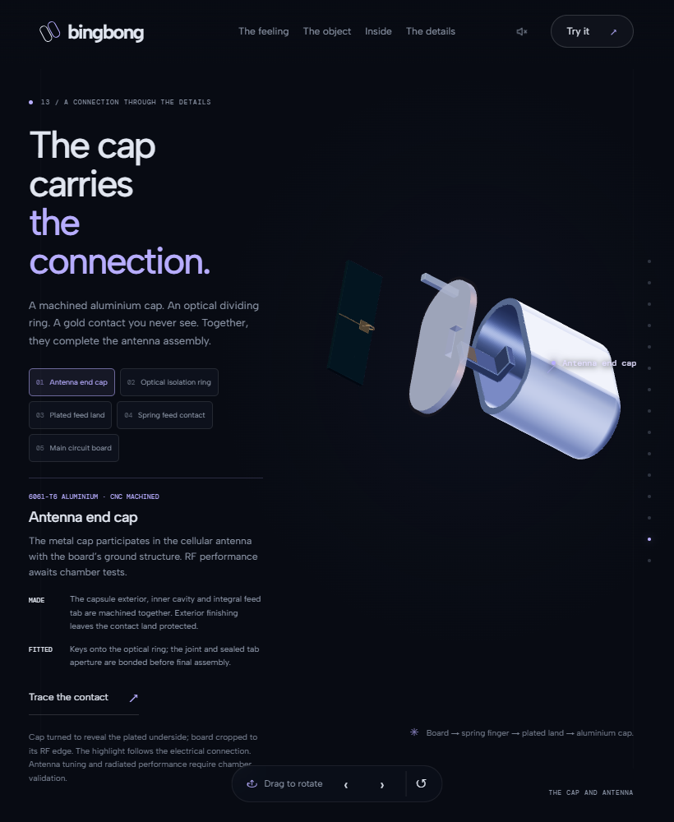
site/qa/assembly/reviewer-820-antenna.png
