chiangr/bingbong/site/qa/assembly/reviewer-820-assembly.png

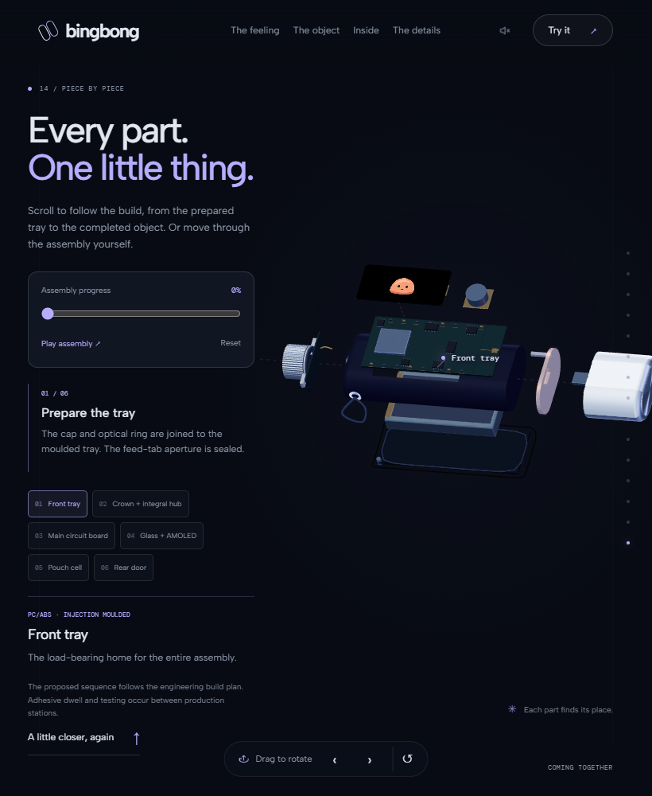
site/qa/assembly/reviewer-820-assembly.png
