chiangr/bingbong/site/qa/assembly/reviewer-820-crown.png

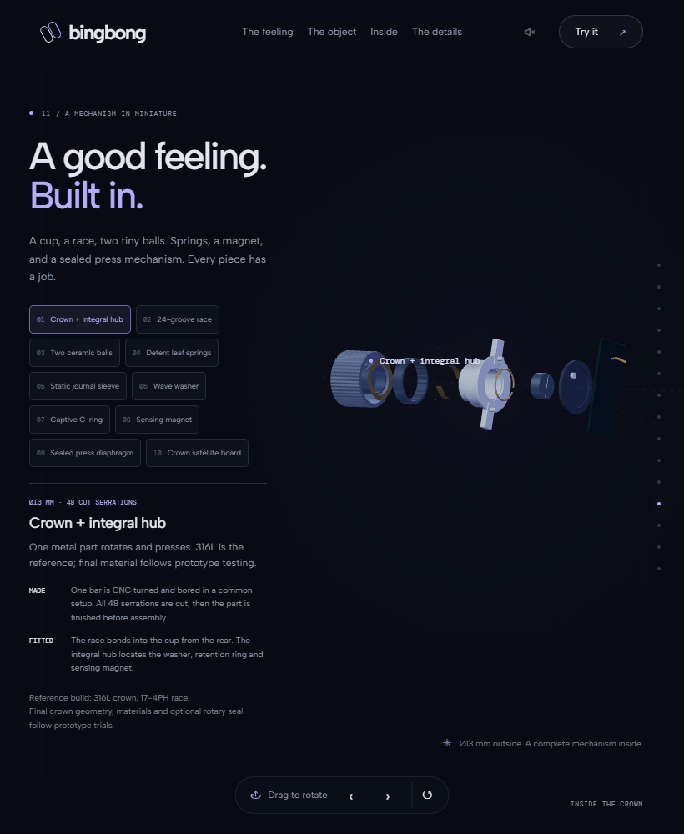
site/qa/assembly/reviewer-820-crown.png
