chiangr/bingbong/site/qa/assembly/reviewer-820-detents.png

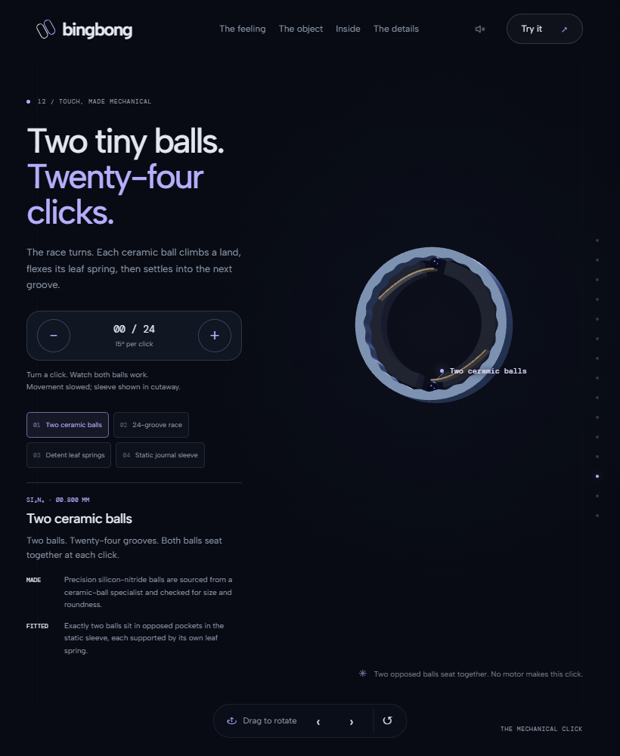
site/qa/assembly/reviewer-820-detents.png
