chiangr/bingbong/site/qa/assembly/reviewer-820-inside.png

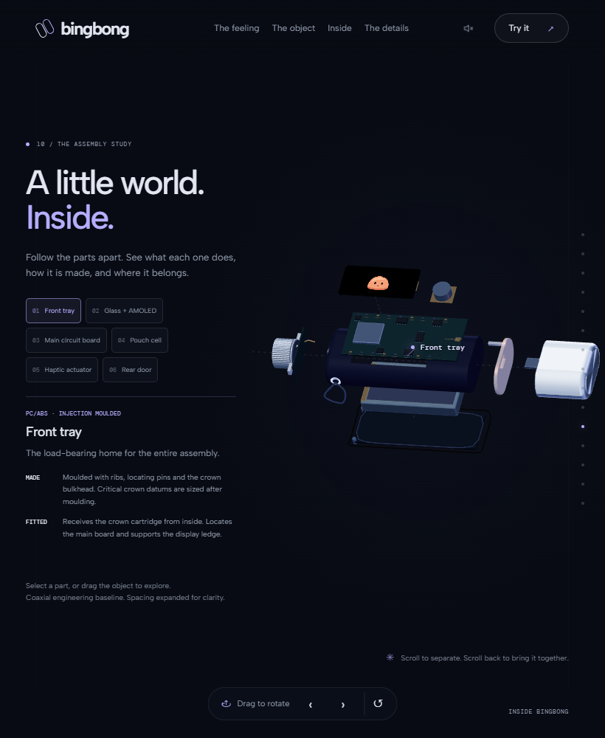
site/qa/assembly/reviewer-820-inside.png
