chiangr/bingbong/site/qa/assembly/reviewer-1440-assembly.png

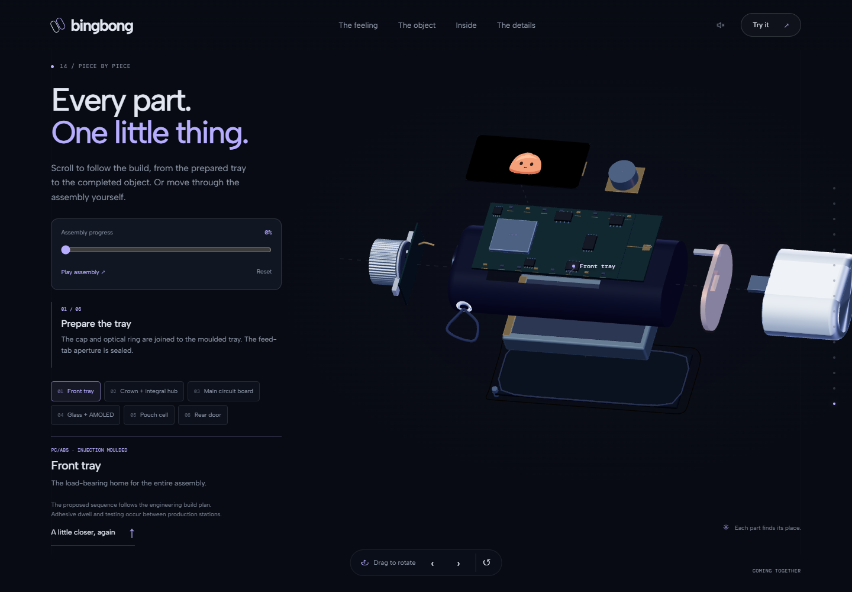
site/qa/assembly/reviewer-1440-assembly.png
