chiangr/bingbong/site/qa/assembly/reviewer-1920-antenna.png

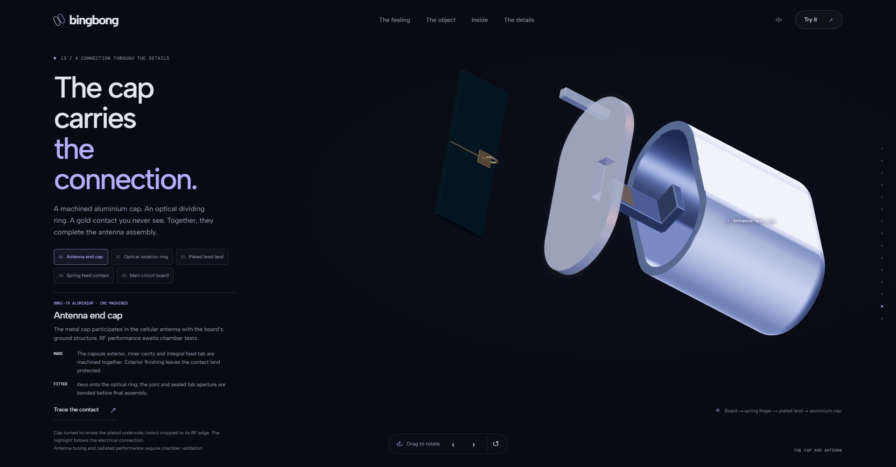
site/qa/assembly/reviewer-1920-antenna.png
