chiangr/bingbong/site/qa/assembly/reviewer-1920-assembly.png

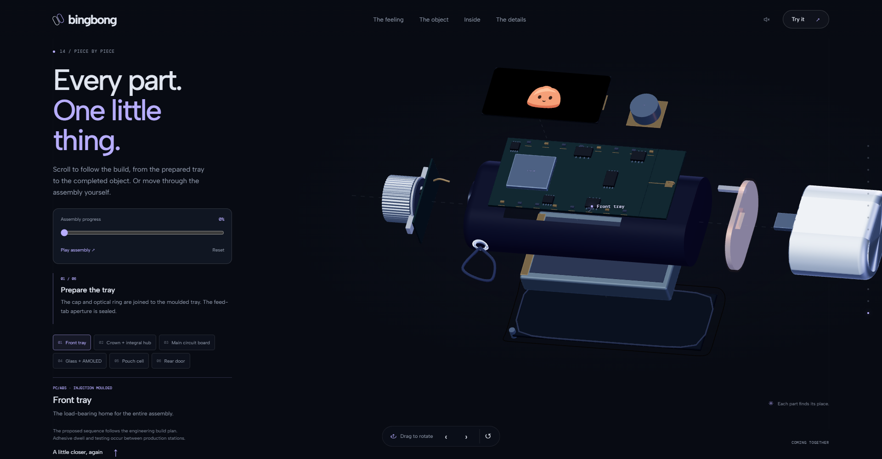
site/qa/assembly/reviewer-1920-assembly.png
