chiangr/bingbong/site/qa/assembly/reviewer-1920-crown.png

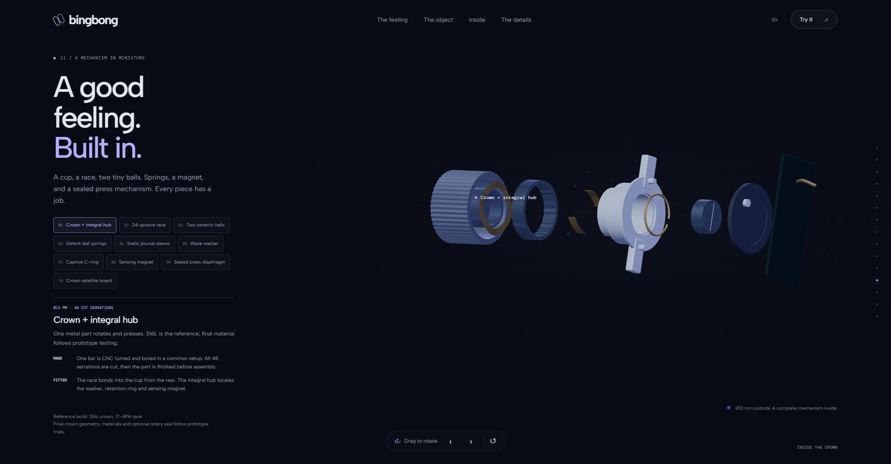
site/qa/assembly/reviewer-1920-crown.png
