chiangr/bingbong/site/qa/assembly/reviewer-1920-detents.png

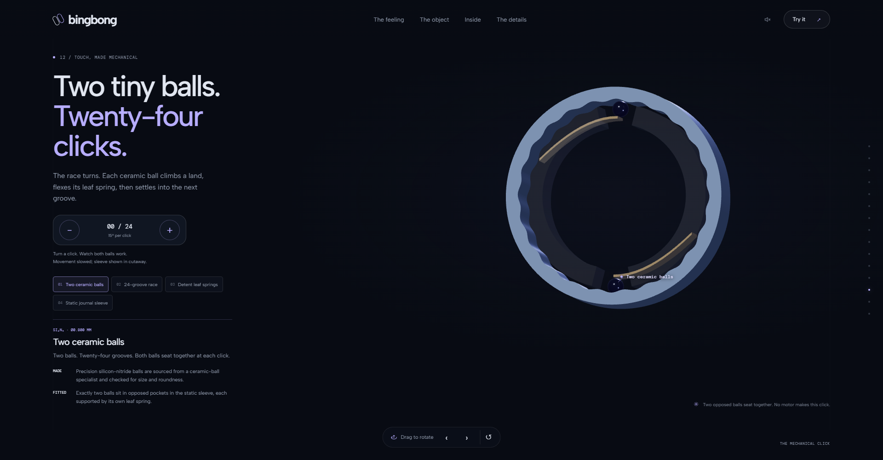
site/qa/assembly/reviewer-1920-detents.png
