chiangr/bingbong/site/qa/assembly/reviewer-1920-inside.png

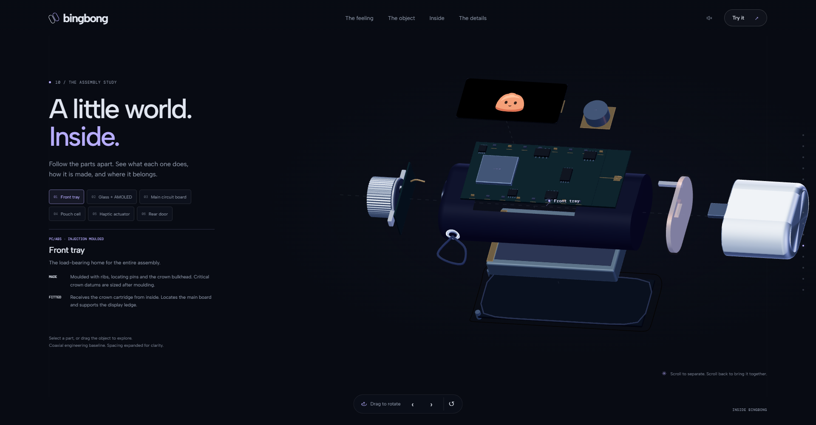
site/qa/assembly/reviewer-1920-inside.png
