chiangr/bingbong/site/qa/assembly/reviewer-recheck-390-500.png

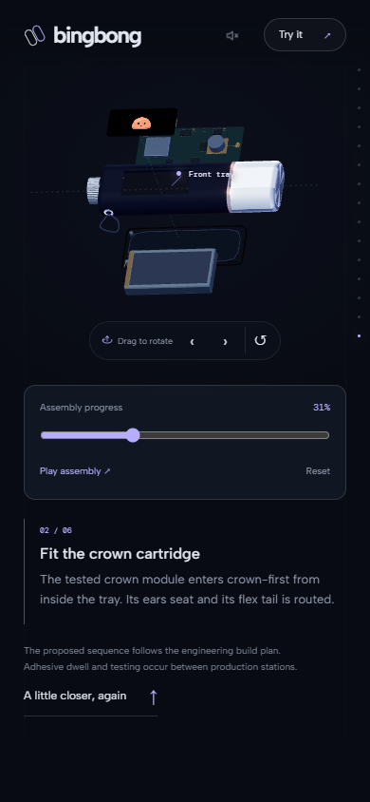
site/qa/assembly/reviewer-recheck-390-500.png
