chiangr/bingbong/site/qa/assembly/reviewer-recheck-390-end.png

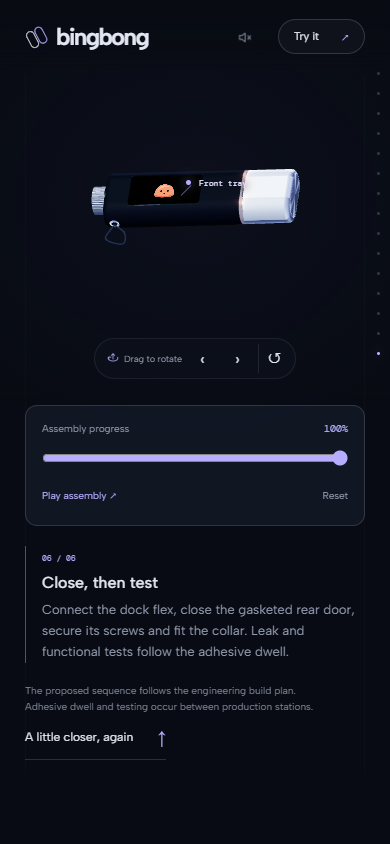
site/qa/assembly/reviewer-recheck-390-end.png
