chiangr/bingbong/site/qa/assembly/reviewer-recheck-1920-assembly.png

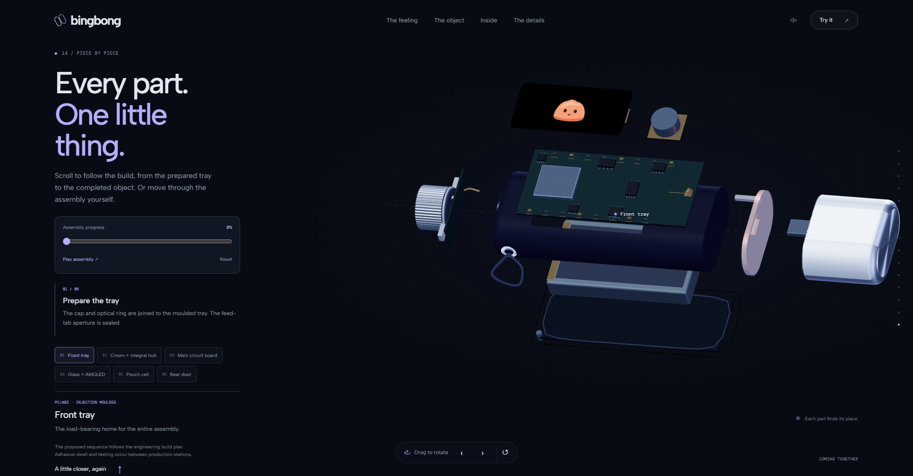
site/qa/assembly/reviewer-recheck-1920-assembly.png
