chiangr/bingbong/site/qa/scroll/390-assembly-0.5.png

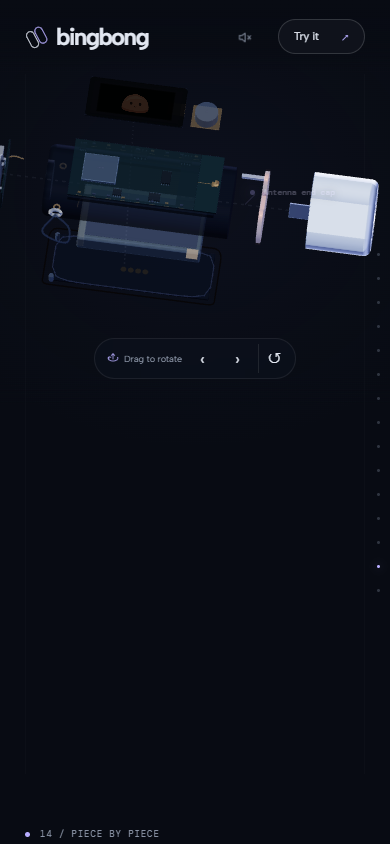
site/qa/scroll/390-assembly-0.5.png
