chiangr/bingbong/site/qa/scroll/390-assembly-0.25.png

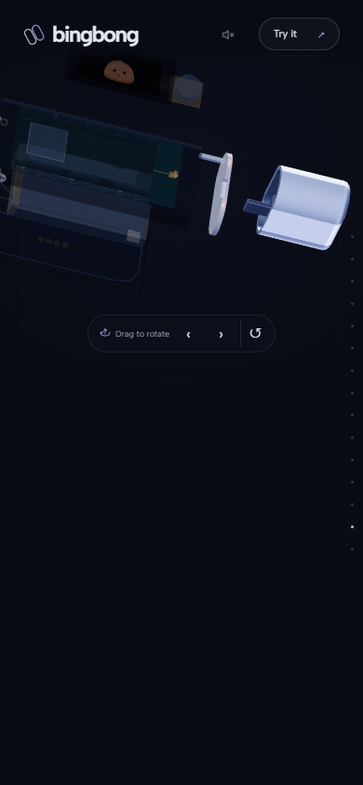
site/qa/scroll/390-assembly-0.25.png
