chiangr/bingbong/site/qa/scroll/390-assembly-0.75.png

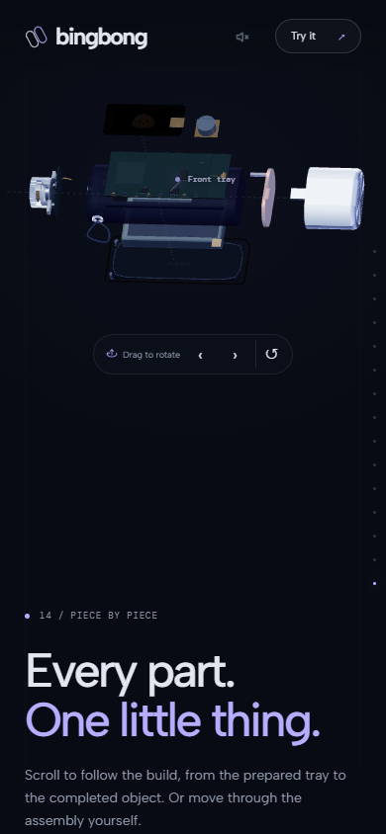
site/qa/scroll/390-assembly-0.75.png
