chiangr/bingbong/site/qa/scroll/1440-assembly-0.5.png

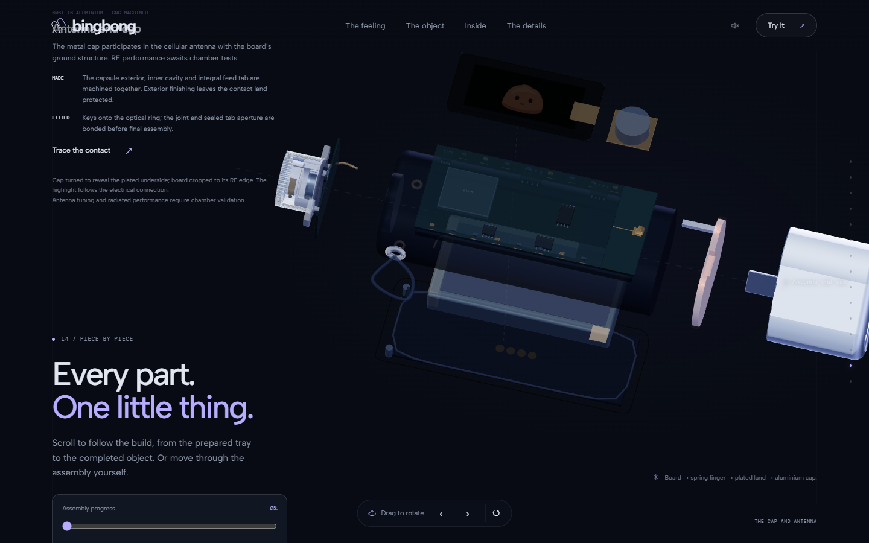
site/qa/scroll/1440-assembly-0.5.png
