chiangr/bingbong/site/qa/scroll/1440-assembly-0.25.png

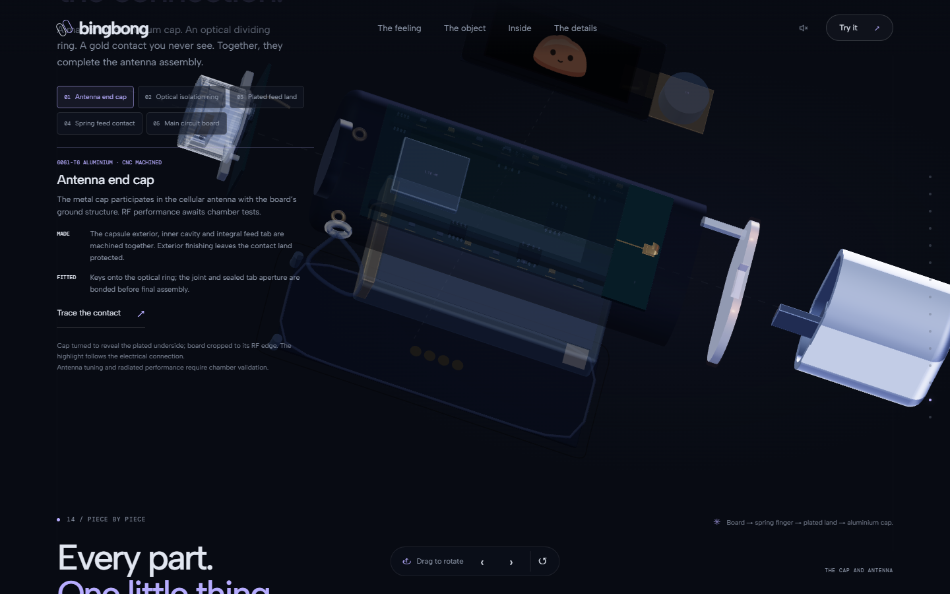
site/qa/scroll/1440-assembly-0.25.png
