chiangr/bingbong/site/qa/first-paint-mobile.png

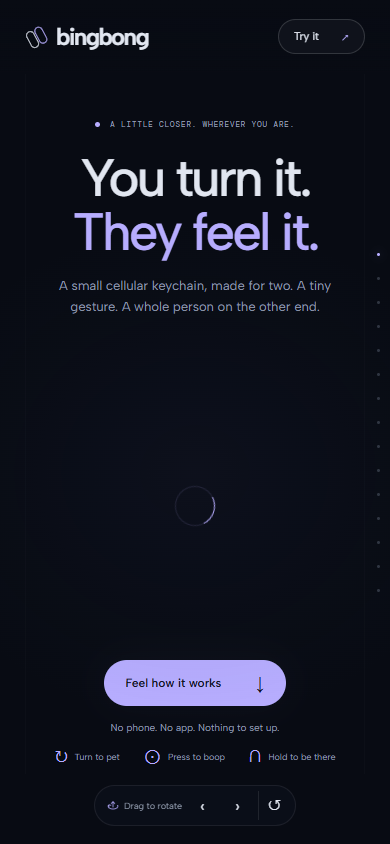
site/qa/first-paint-mobile.png
