chiangr/bingbong/site/qa/passes/01-render/390.png

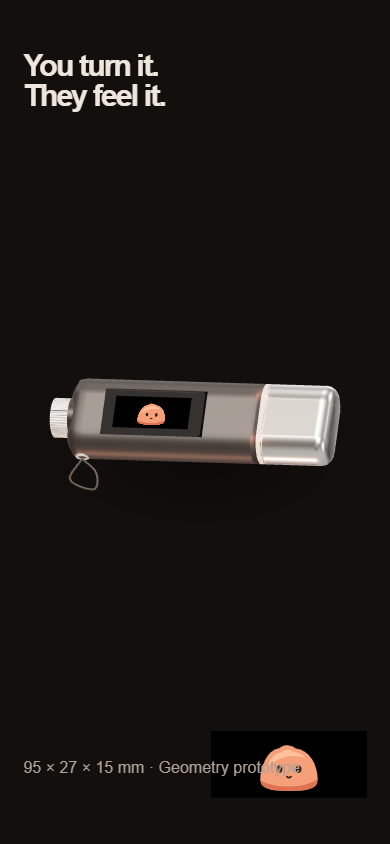
site/qa/passes/01-render/390.png
