chiangr/bingbong/site/qa/passes/01-render/820.png

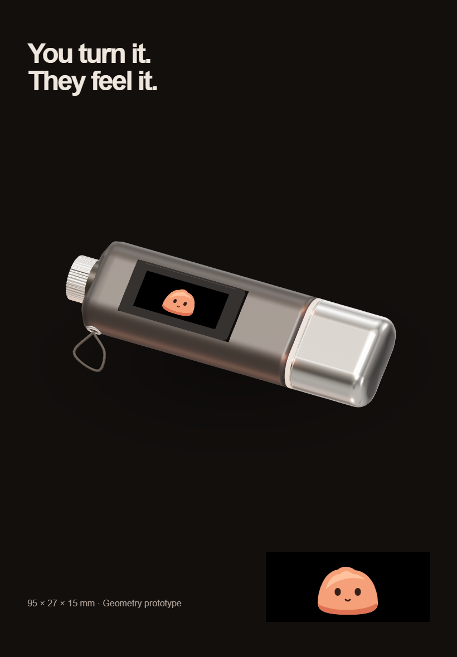
site/qa/passes/01-render/820.png
