chiangr/bingbong/site/qa/passes/01-render/1440.png

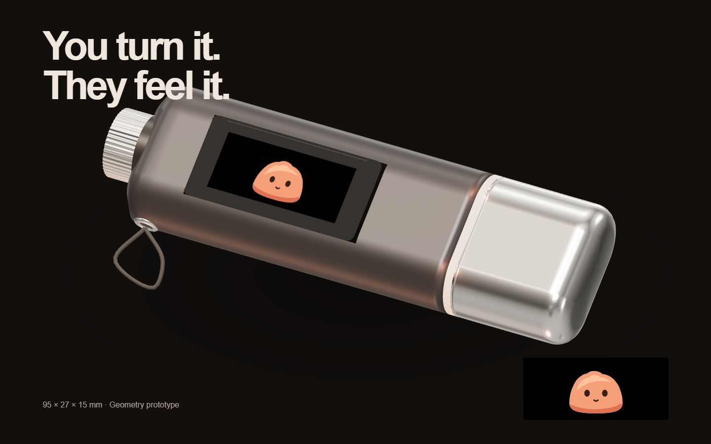
site/qa/passes/01-render/1440.png
