chiangr/bingbong/site/qa/passes/02-scroll/390.png

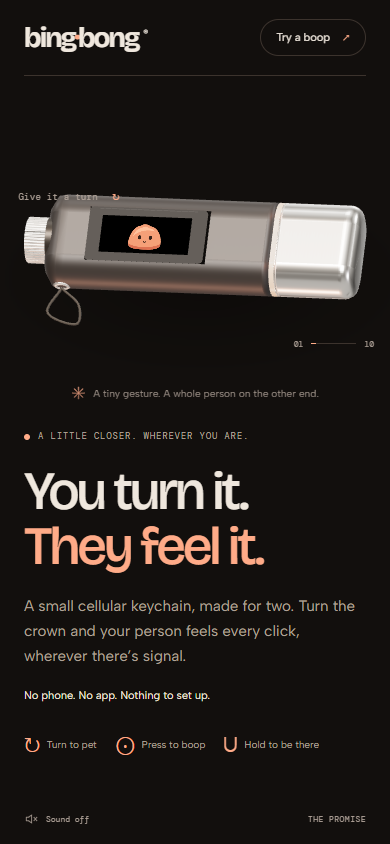
site/qa/passes/02-scroll/390.png
