chiangr/bingbong/site/qa/passes/02-scroll/820.png

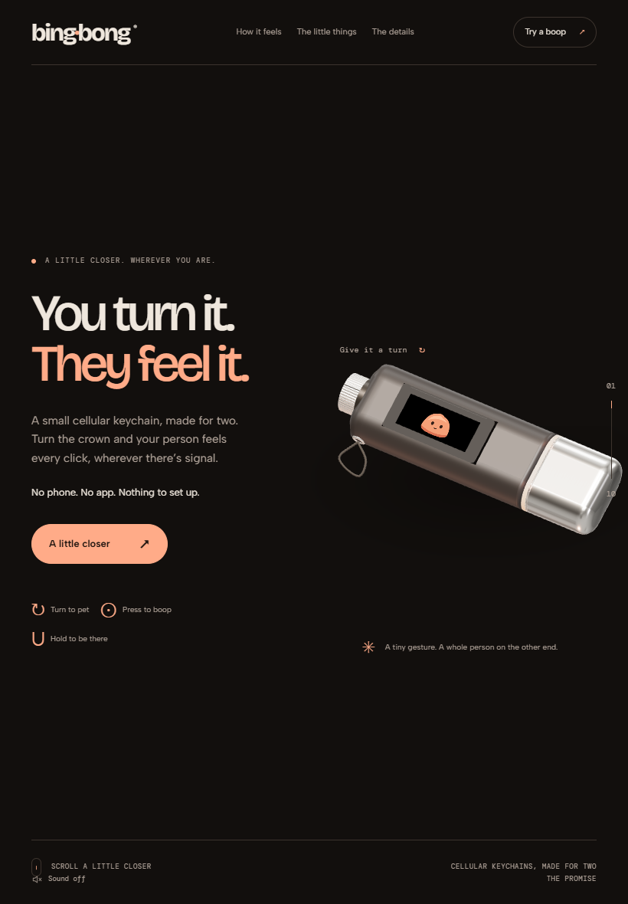
site/qa/passes/02-scroll/820.png
