chiangr/bingbong/site/qa/passes/02-scroll/1440.png

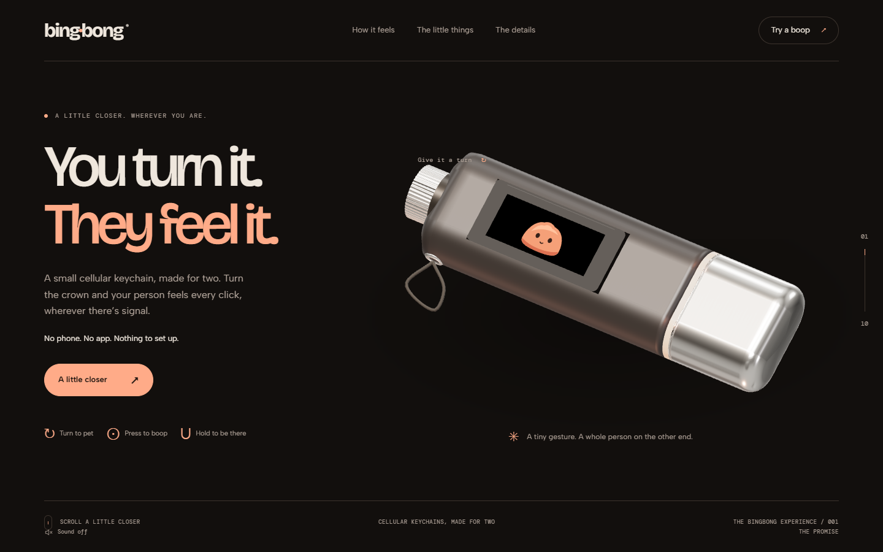
site/qa/passes/02-scroll/1440.png
