chiangr/bingbong/site/qa/passes/04-content/390.png

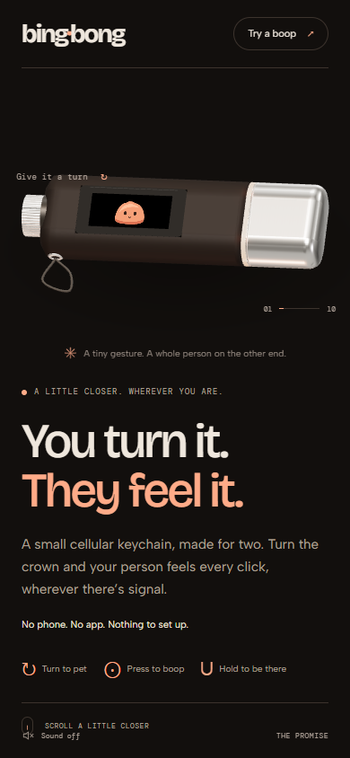
site/qa/passes/04-content/390.png
