chiangr/bingbong/site/qa/passes/06-qa/390.png

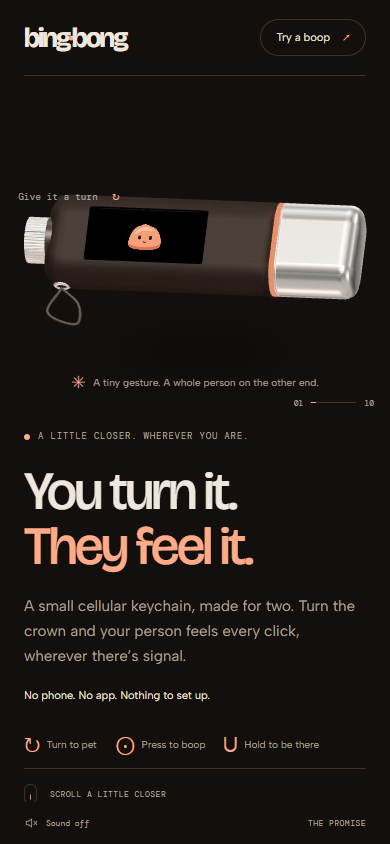
site/qa/passes/06-qa/390.png
