chiangr/bingbong/site/qa/references/approved-390.png

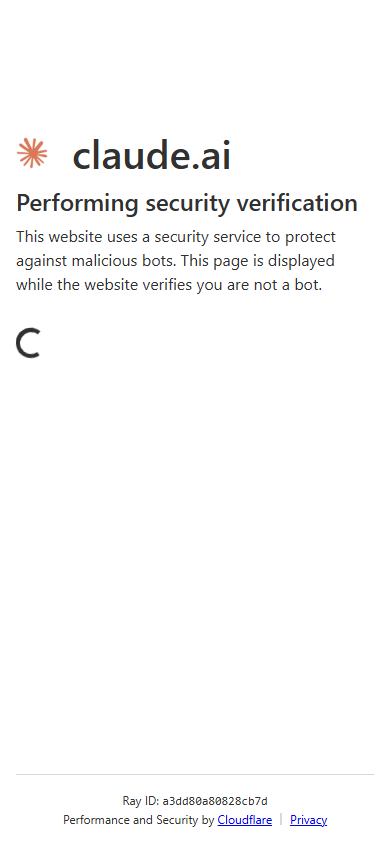
site/qa/references/approved-390.png
