chiangr/bingbong/site/qa/references/approved-1440.png

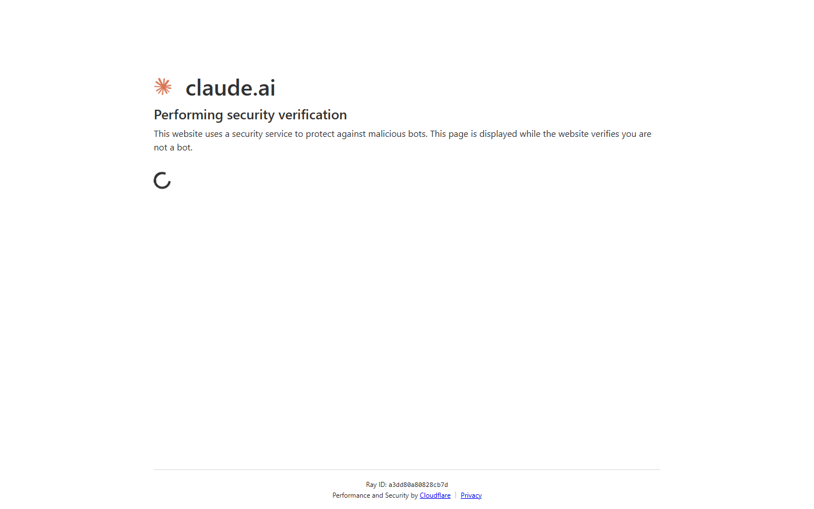
site/qa/references/approved-1440.png
