chiangr/bingbong/site/qa/references/playdate-390.png

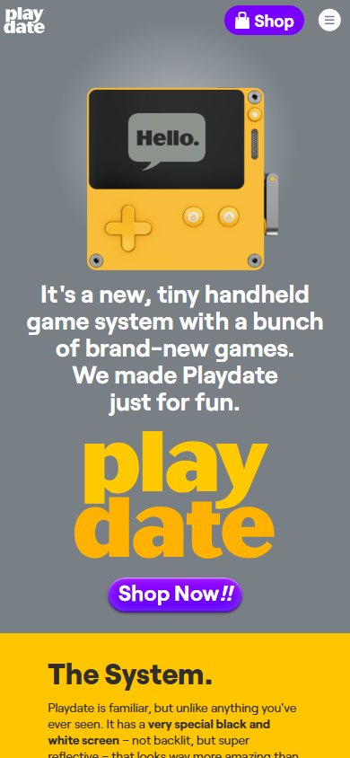
site/qa/references/playdate-390.png
