chiangr/bingbong/site/qa/references/playdate-1440.png

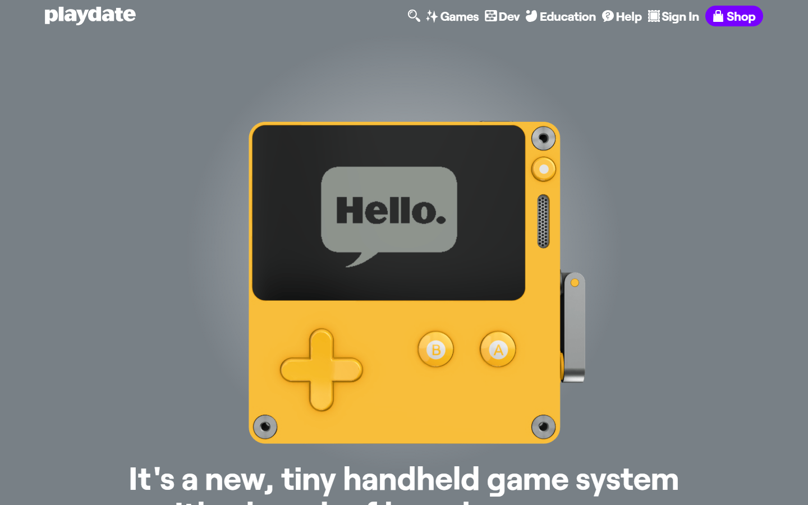
site/qa/references/playdate-1440.png
