chiangr/bingbong/site/qa/render-final.png

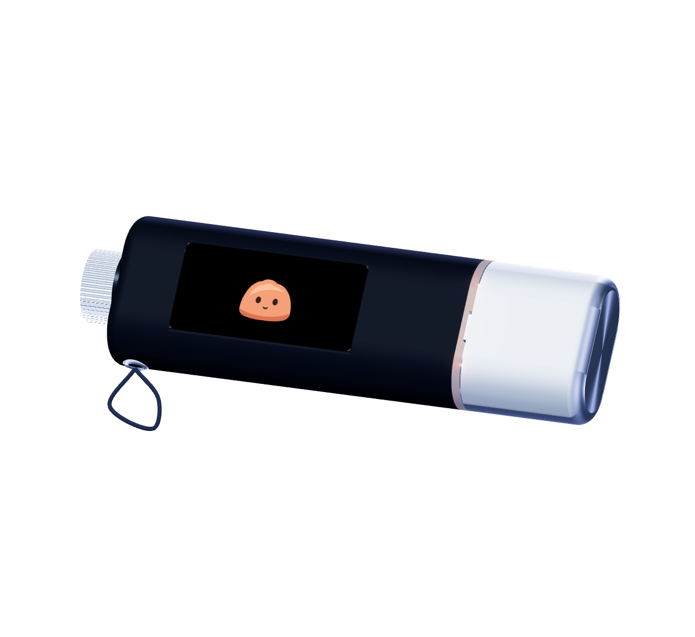
site/qa/render-final.png
