chiangr/bingbong/site/qa/rf/360-mobile-tuning.png

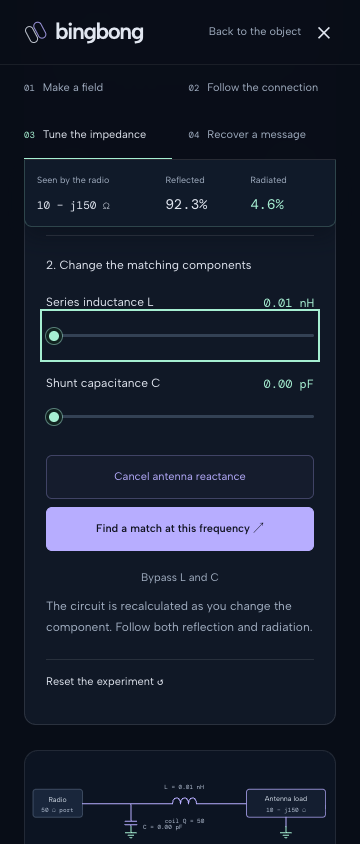
site/qa/rf/360-mobile-tuning.png
