chiangr/bingbong/site/qa/rf/390-chapter-1.png

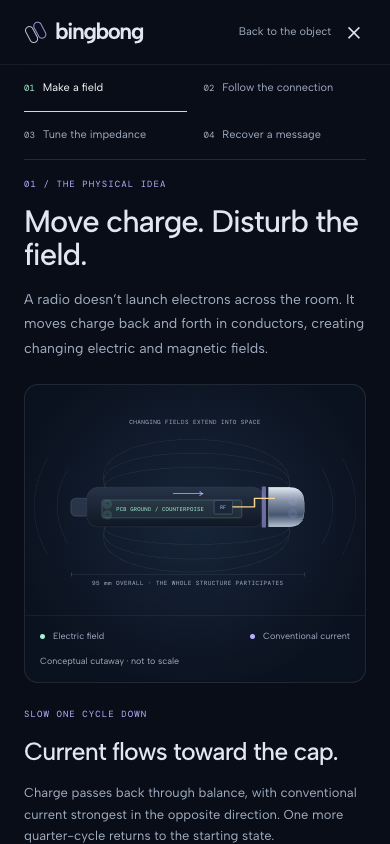
site/qa/rf/390-chapter-1.png
