chiangr/bingbong/site/qa/rf/390-chapter-2.png

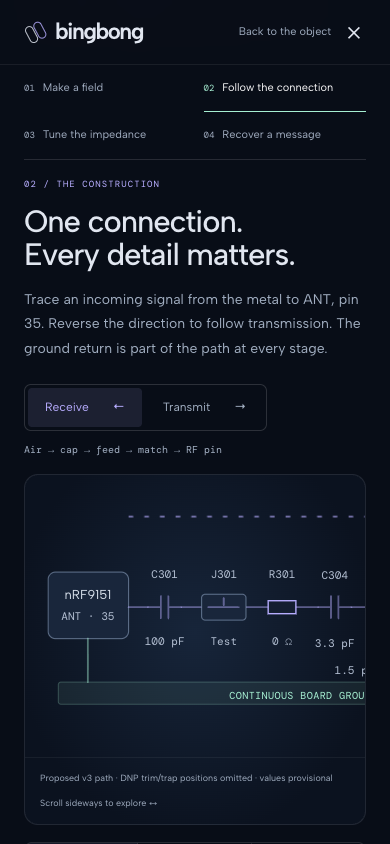
site/qa/rf/390-chapter-2.png
