chiangr/bingbong/site/qa/rf/390-chapter-3.png

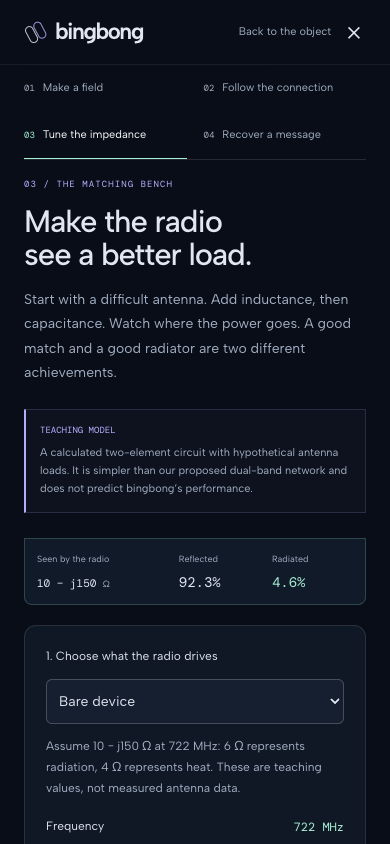
site/qa/rf/390-chapter-3.png
