chiangr/bingbong/site/qa/rf/390-chapter-4.png

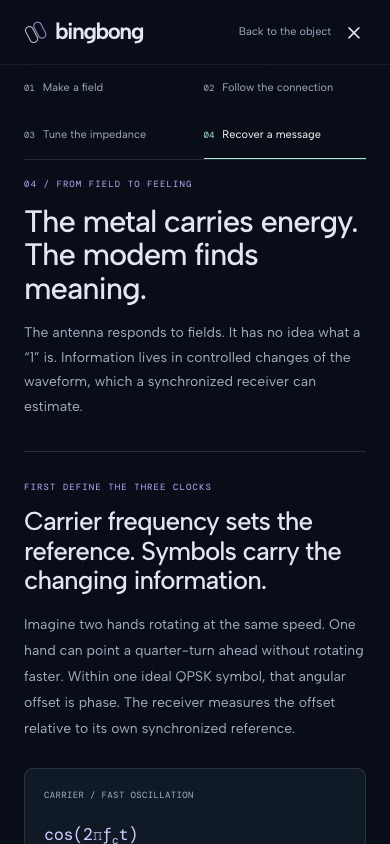
site/qa/rf/390-chapter-4.png
