chiangr/bingbong/site/qa/rf/1440-chapter-1.png

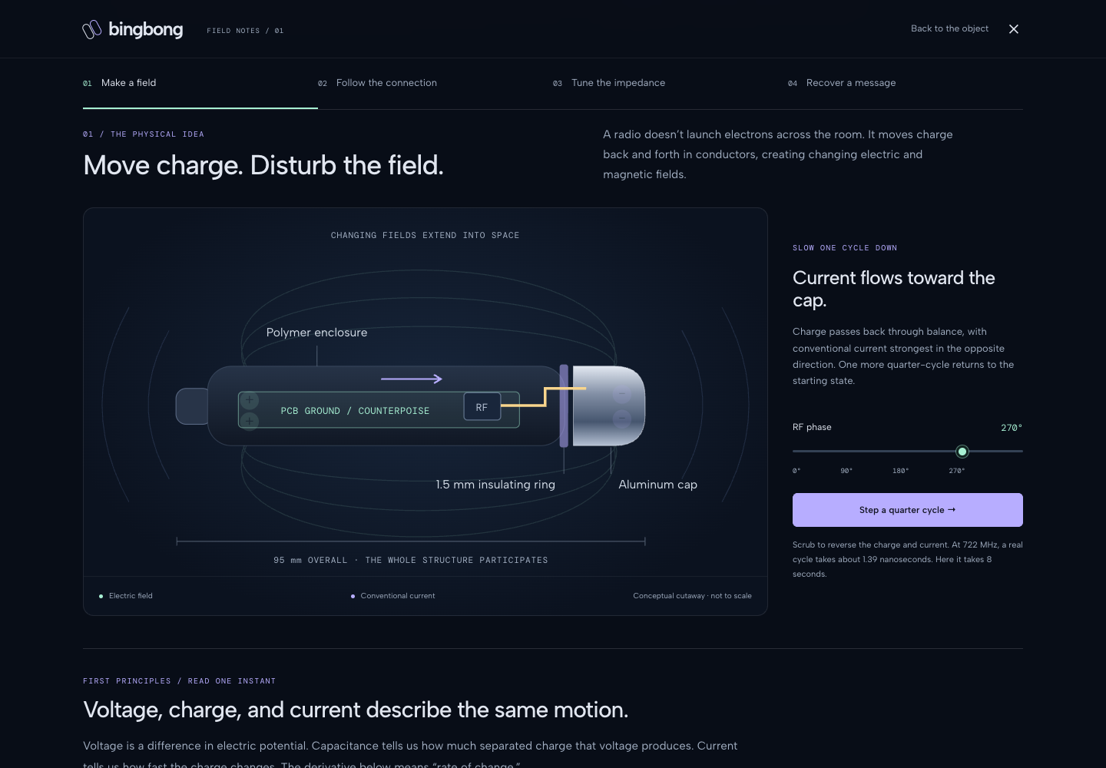
site/qa/rf/1440-chapter-1.png
