chiangr/bingbong/site/qa/rf/1440-chapter-2.png

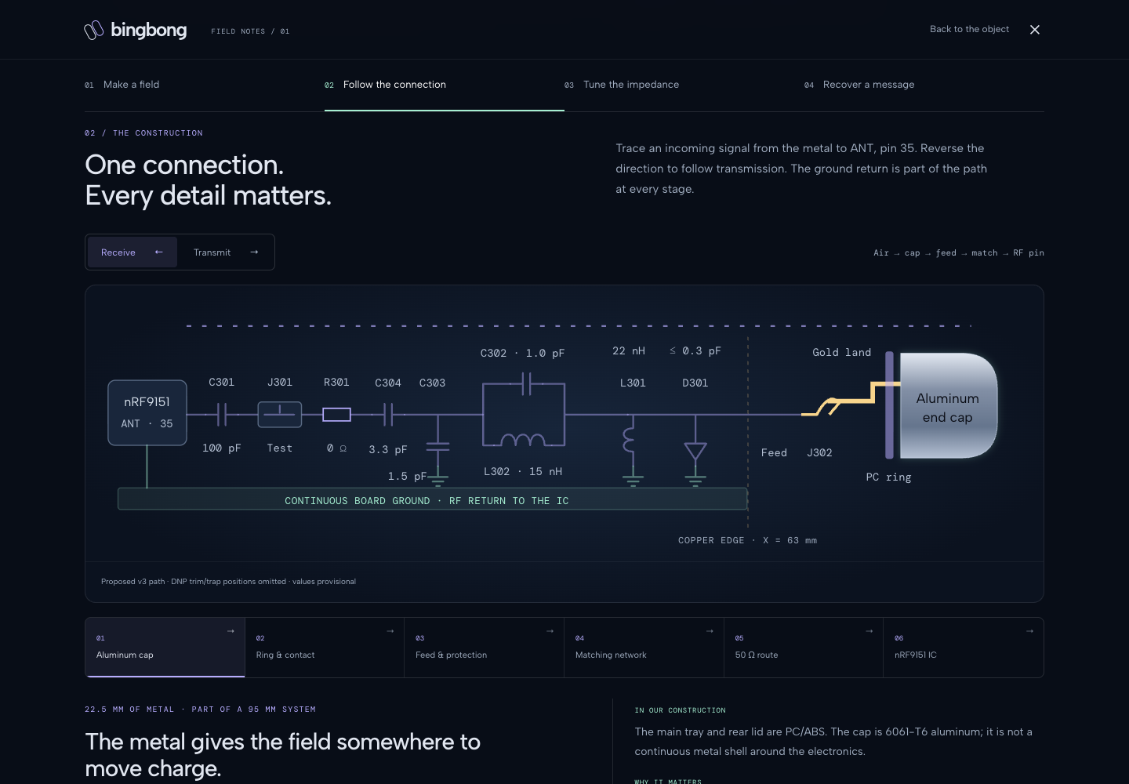
site/qa/rf/1440-chapter-2.png
