chiangr/bingbong/site/qa/rf/1440-chapter-3.png

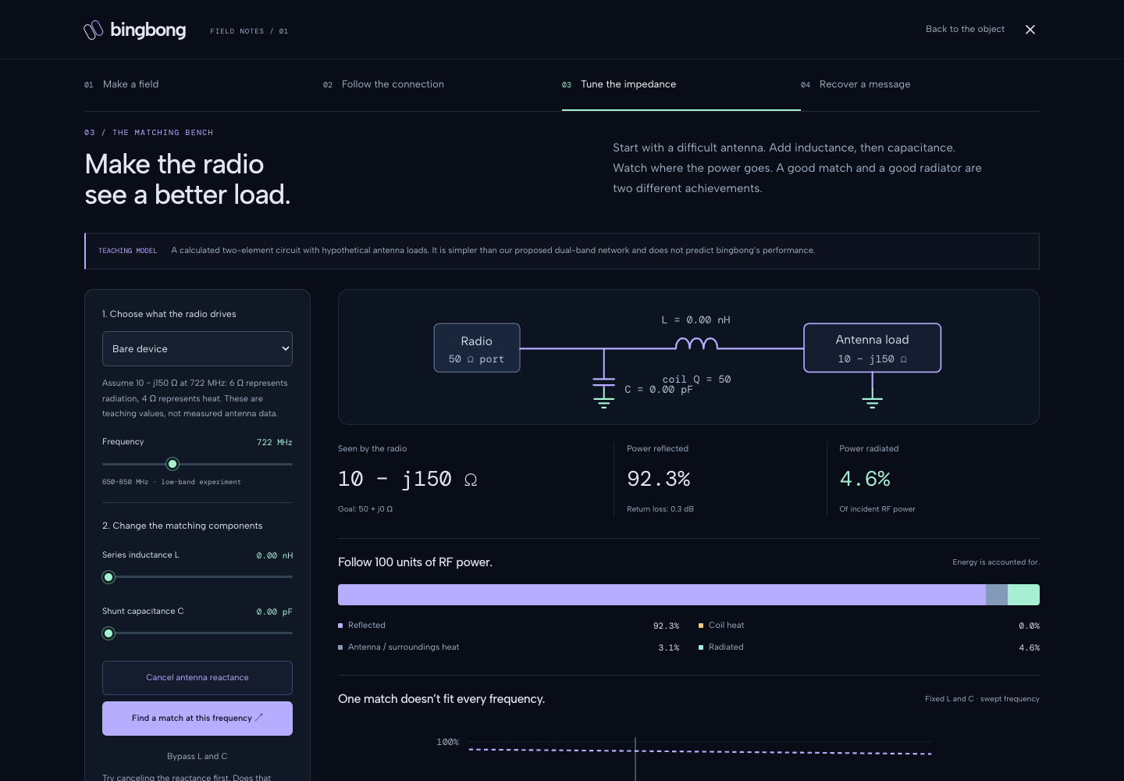
site/qa/rf/1440-chapter-3.png
