chiangr/bingbong/site/qa/rf/1440-chapter-4.png

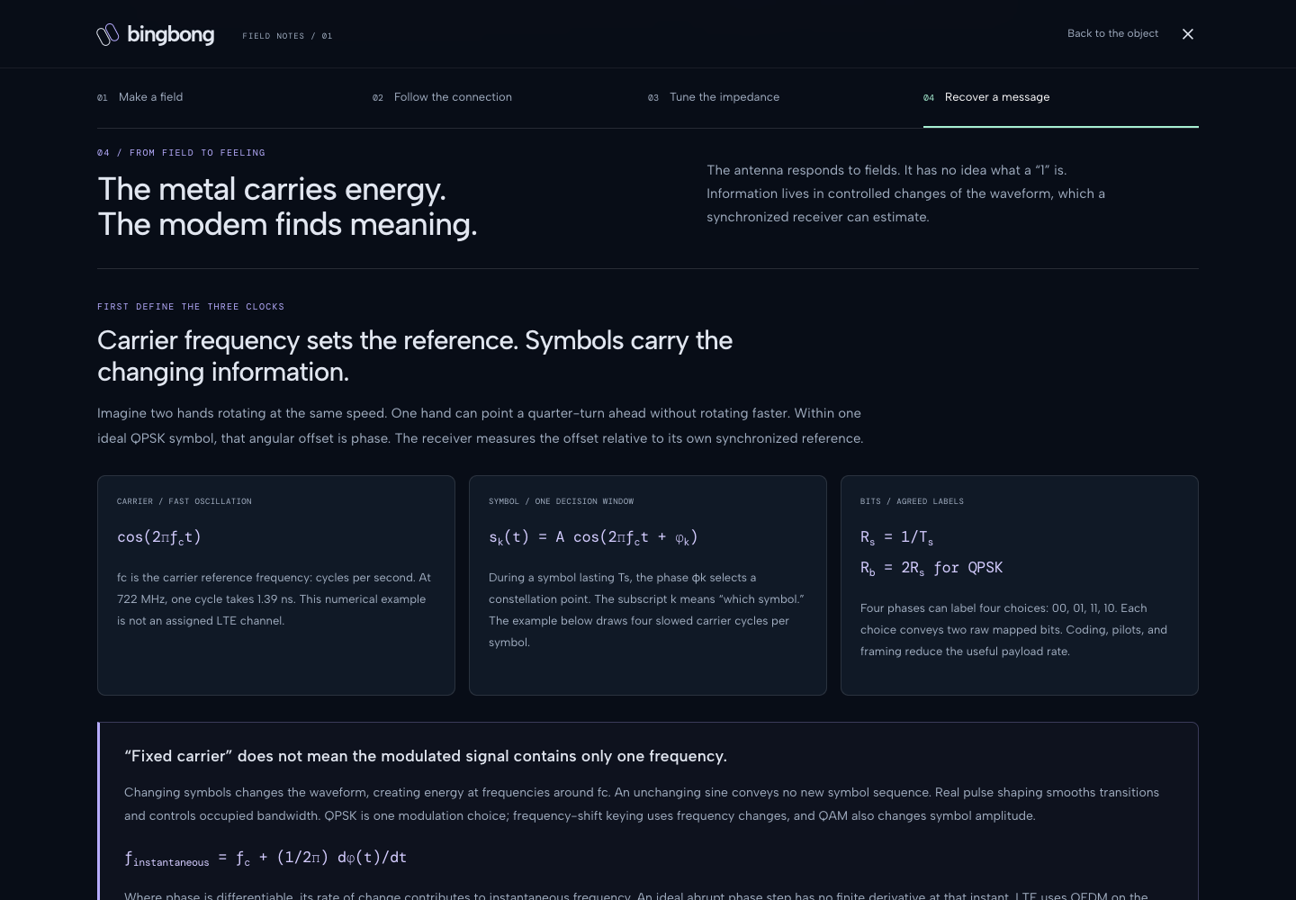
site/qa/rf/1440-chapter-4.png
