chiangr/bingbong/site/qa/rf/deep/360-parallel-lc.png

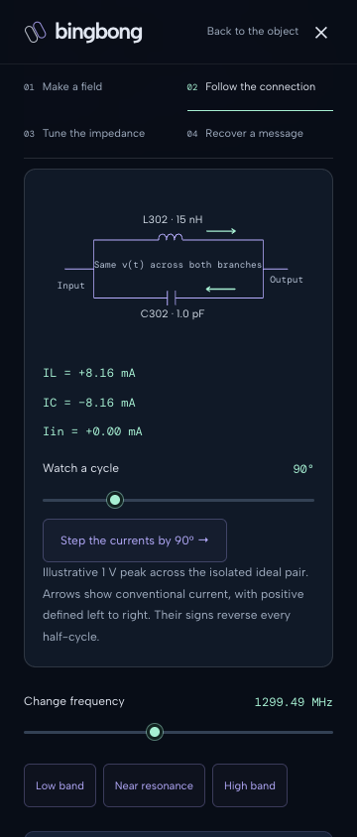
site/qa/rf/deep/360-parallel-lc.png
