chiangr/bingbong/site/qa/rf/deep/360-reflections.png

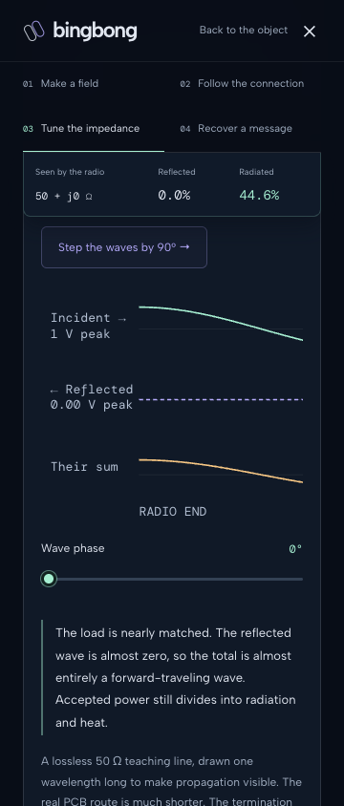
site/qa/rf/deep/360-reflections.png
