chiangr/bingbong/site/qa/rf/deep/390-channel.png

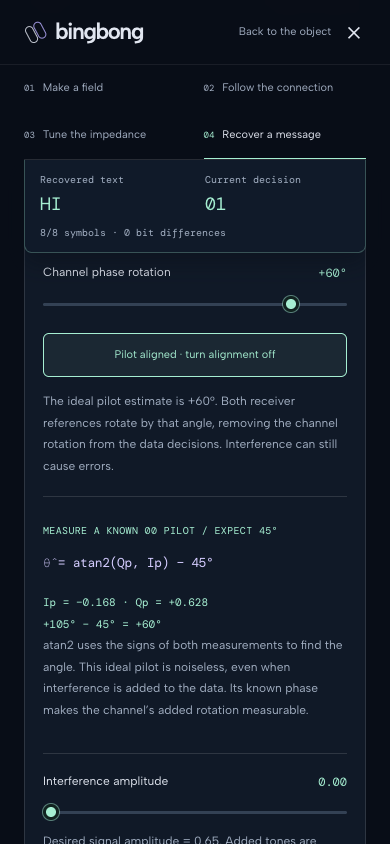
site/qa/rf/deep/390-channel.png
