chiangr/bingbong/site/qa/rf/deep/390-fields.png

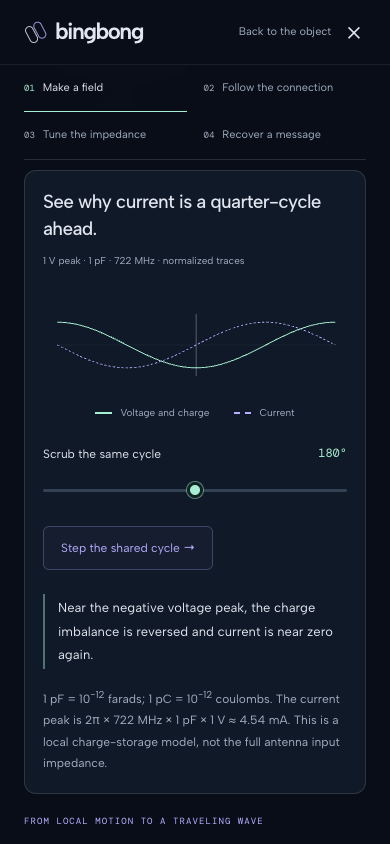
site/qa/rf/deep/390-fields.png
