chiangr/bingbong/site/qa/rf/deep/390-parallel-lc.png

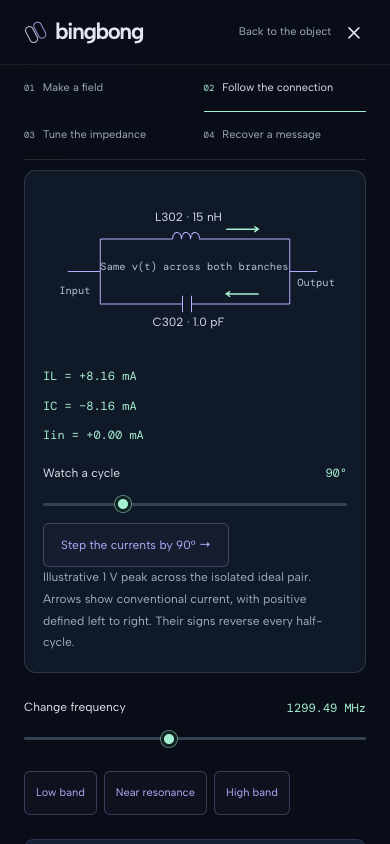
site/qa/rf/deep/390-parallel-lc.png
