chiangr/bingbong/site/qa/rf/deep/390-receiver.png

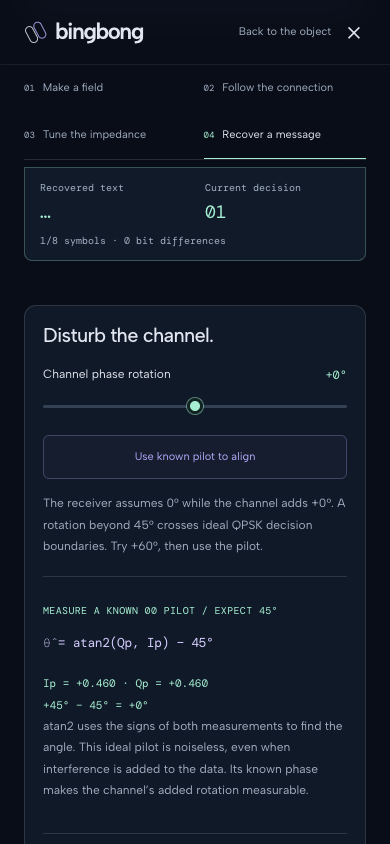
site/qa/rf/deep/390-receiver.png
