chiangr/bingbong/site/qa/rf/deep/390-reflections.png

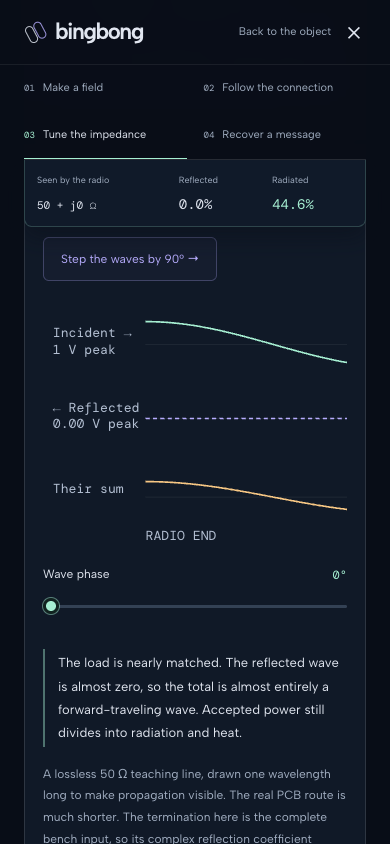
site/qa/rf/deep/390-reflections.png
