chiangr/bingbong/site/qa/rf/deep/390-whole-message.png

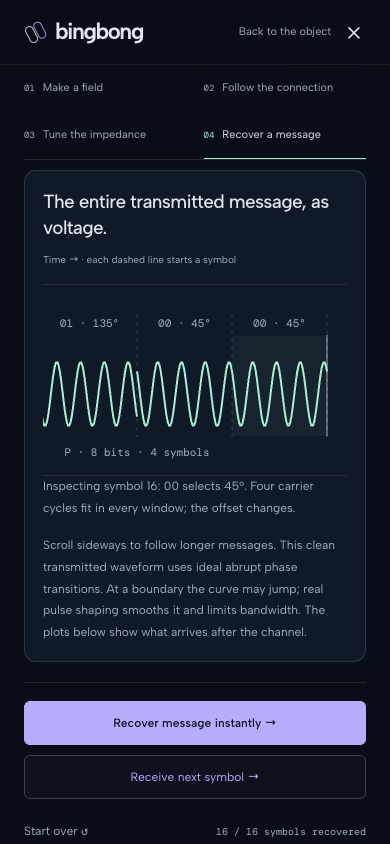
site/qa/rf/deep/390-whole-message.png
