chiangr/bingbong/site/qa/rf/deep/1440-fields.png

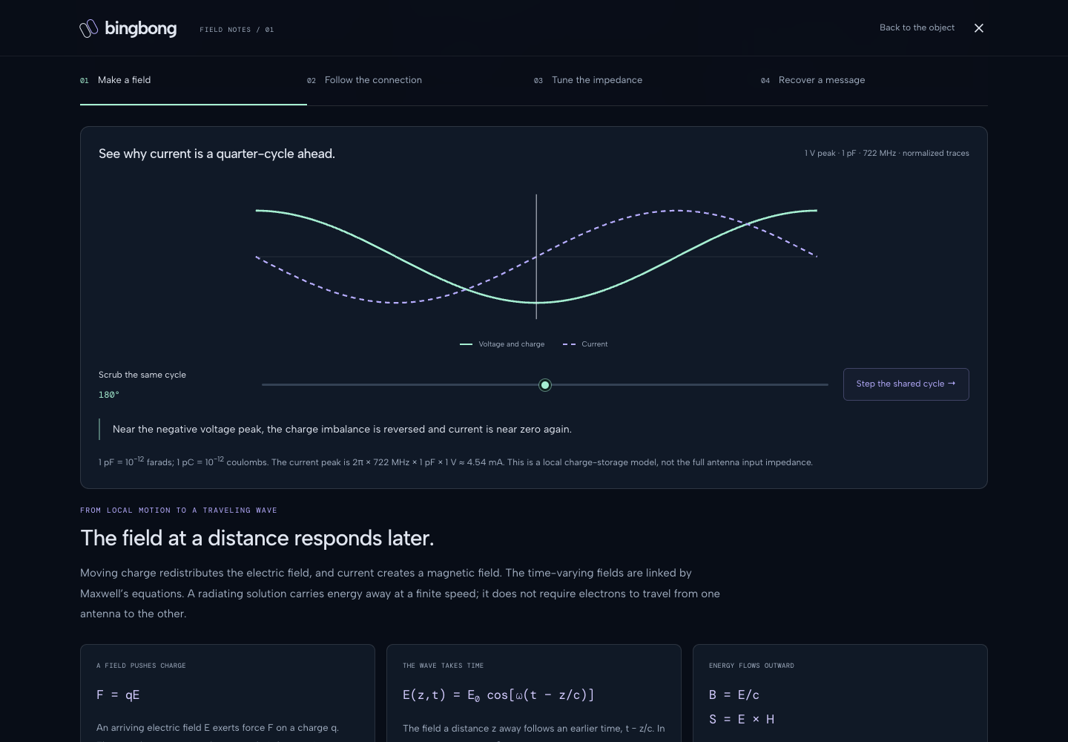
site/qa/rf/deep/1440-fields.png
