chiangr/bingbong/site/qa/rf/deep/1440-parallel-lc.png

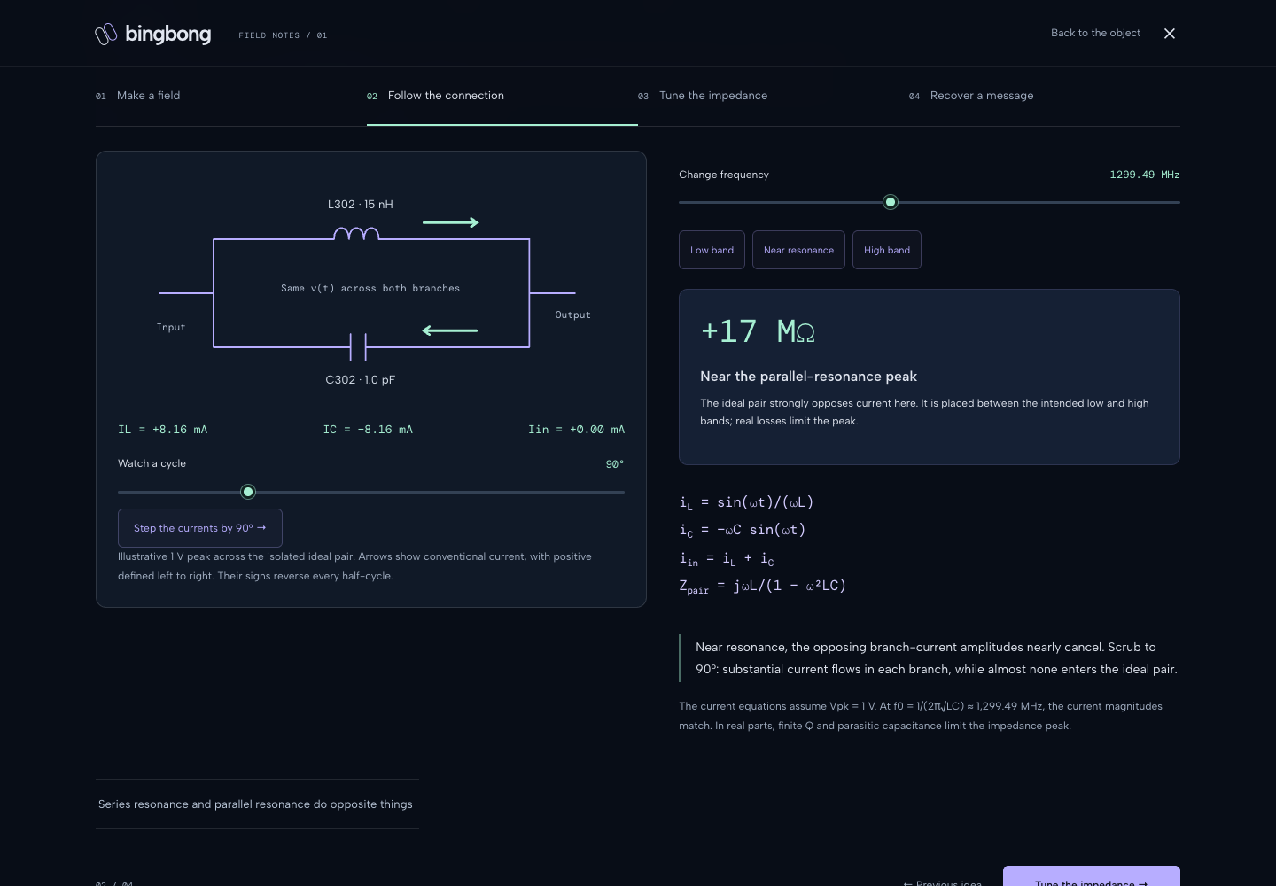
site/qa/rf/deep/1440-parallel-lc.png
