chiangr/bingbong/site/qa/rf/deep/1440-receiver.png

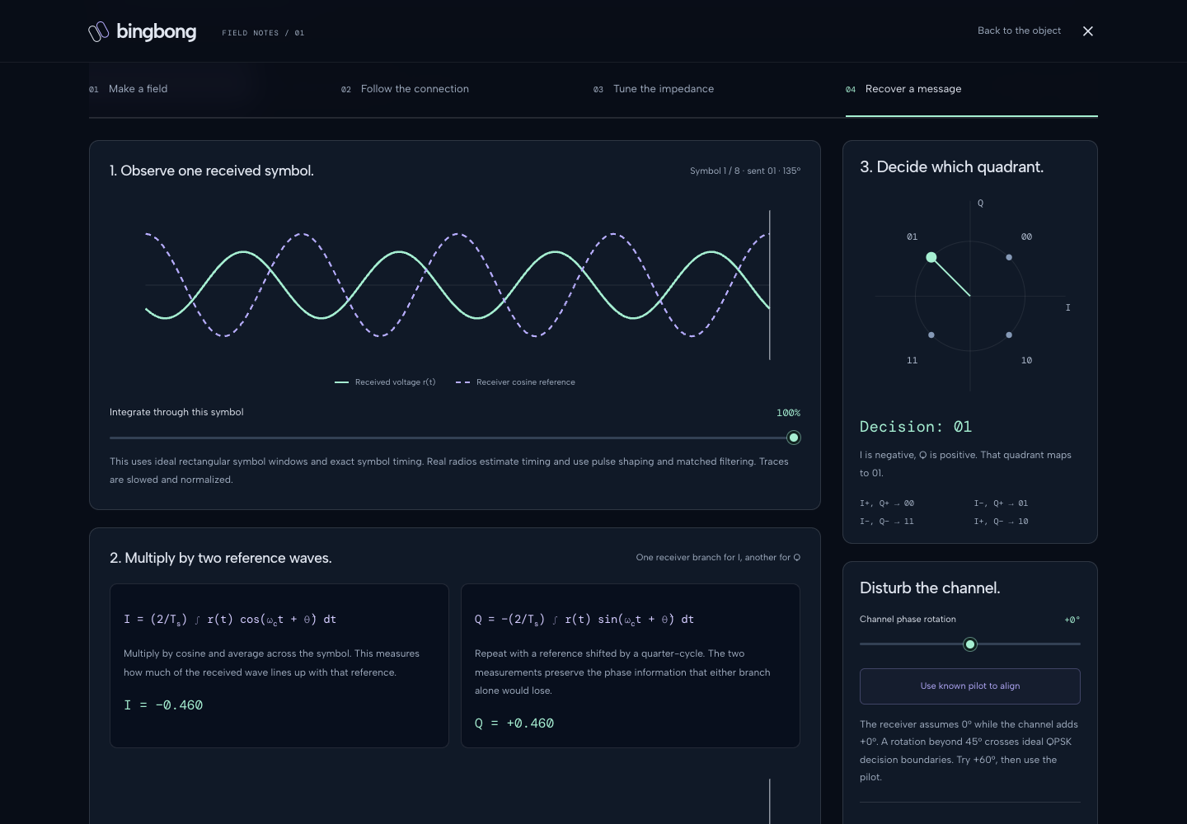
site/qa/rf/deep/1440-receiver.png
