chiangr/bingbong/site/qa/rf/deep/1440-reflections.png

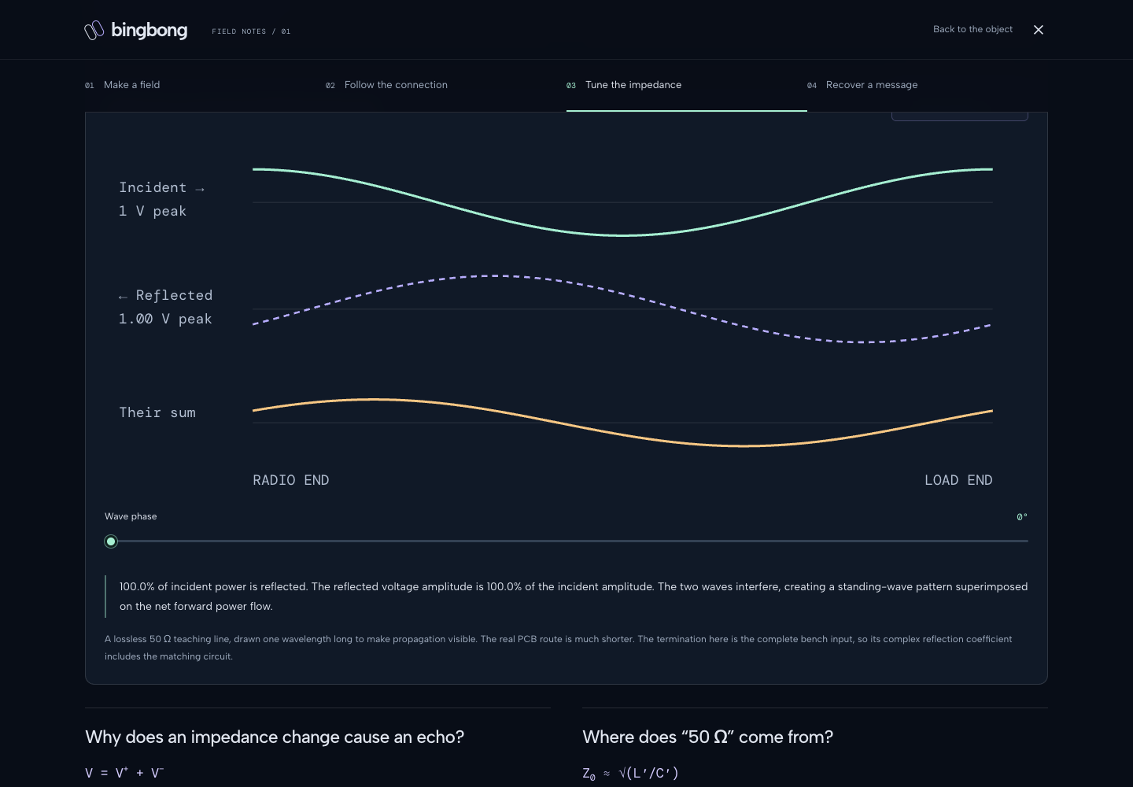
site/qa/rf/deep/1440-reflections.png
