chiangr/bingbong/site/qa/rf/deep/1440-whole-message.png

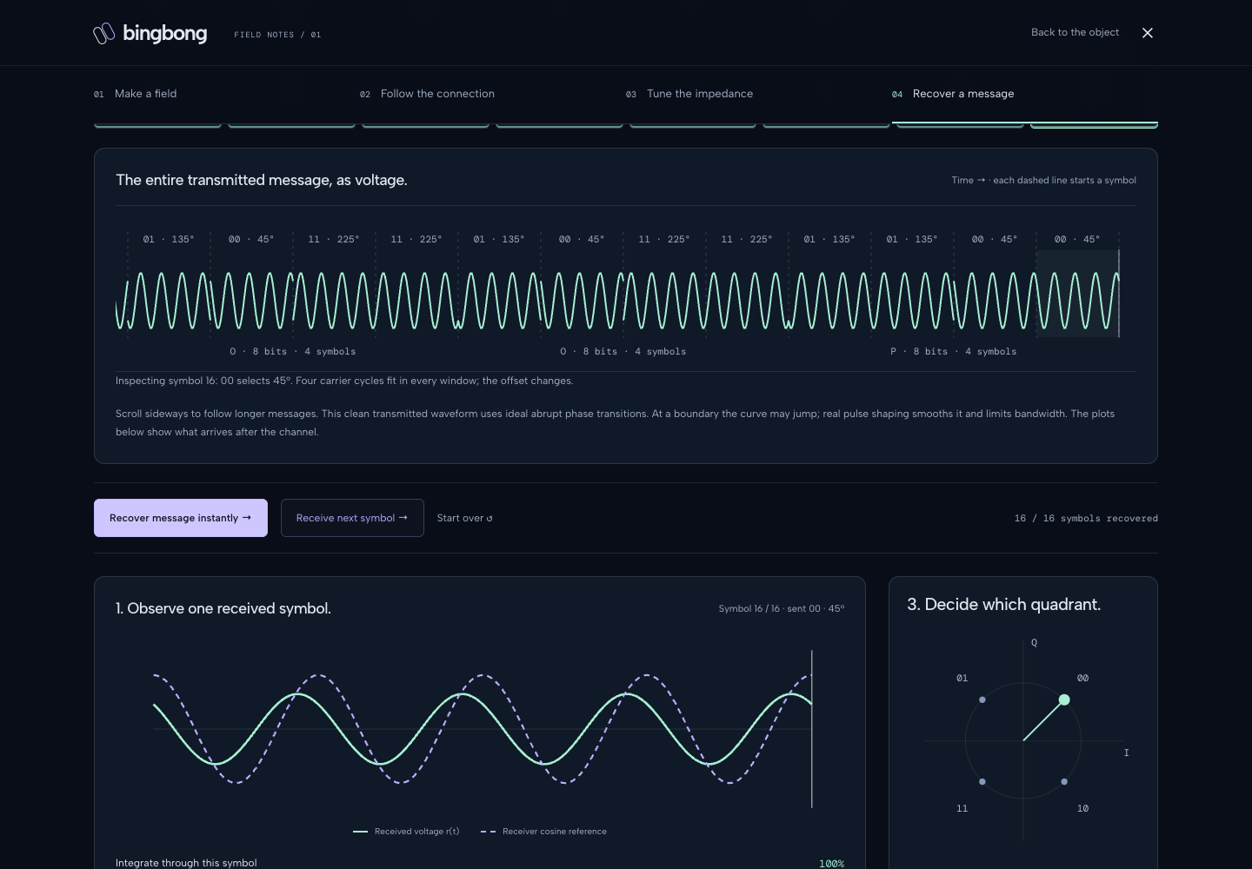
site/qa/rf/deep/1440-whole-message.png
