chiangr/bingbong/site/qa/scroll/390-antenna-0.5.png

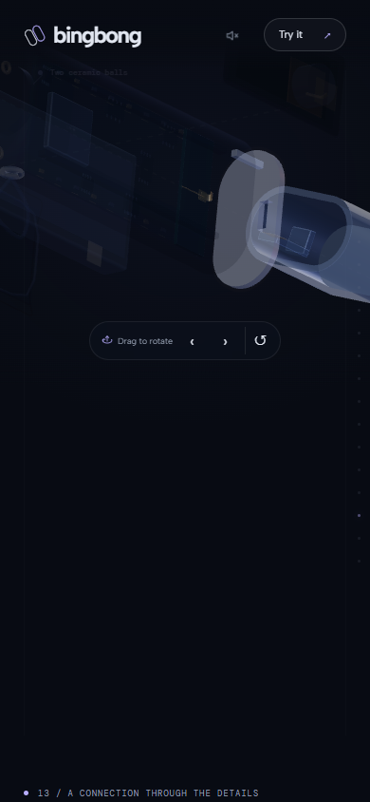
site/qa/scroll/390-antenna-0.5.png
