chiangr/bingbong/site/qa/scroll/390-antenna-0.25.png

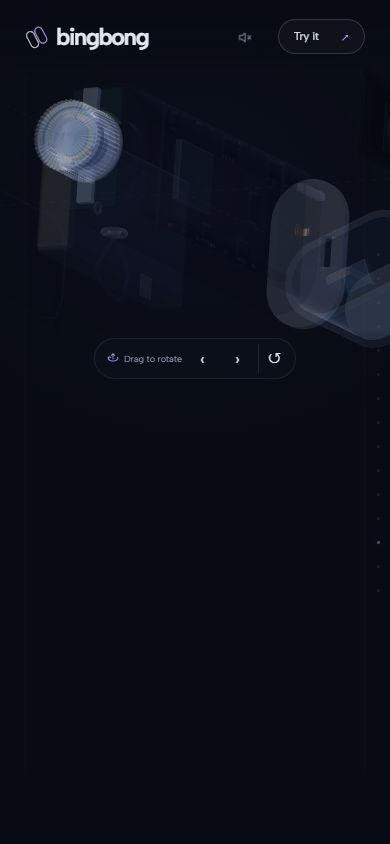
site/qa/scroll/390-antenna-0.25.png
