chiangr/bingbong/site/qa/scroll/390-antenna-0.75.png

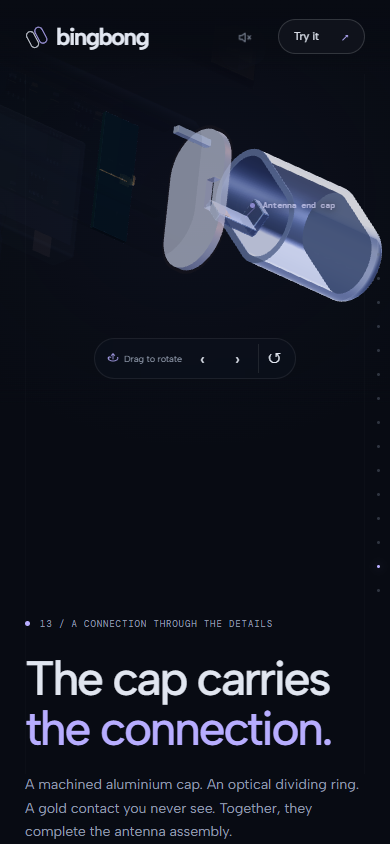
site/qa/scroll/390-antenna-0.75.png
