chiangr/bingbong/site/qa/scroll/390-creature-0.5.png

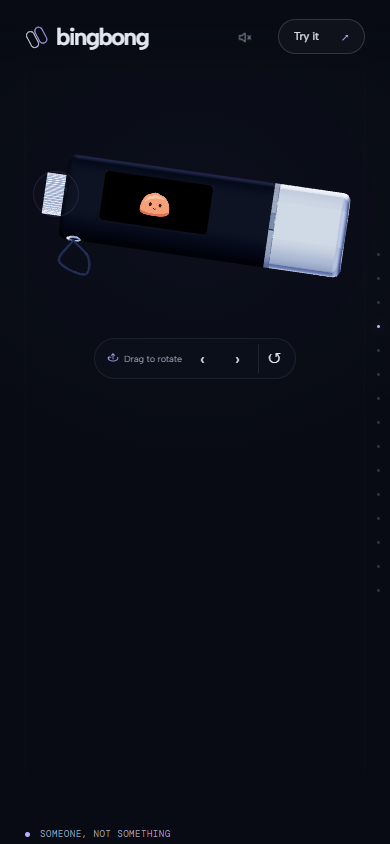
site/qa/scroll/390-creature-0.5.png
