chiangr/bingbong/site/qa/scroll/390-creature-0.25.png

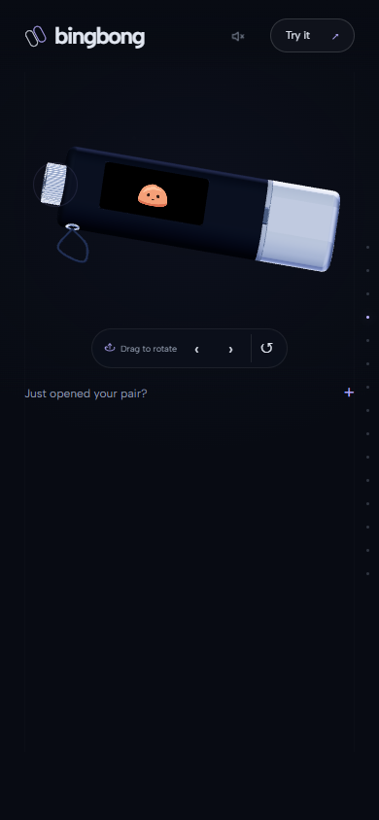
site/qa/scroll/390-creature-0.25.png
