chiangr/bingbong/site/qa/scroll/390-creature-0.75.png

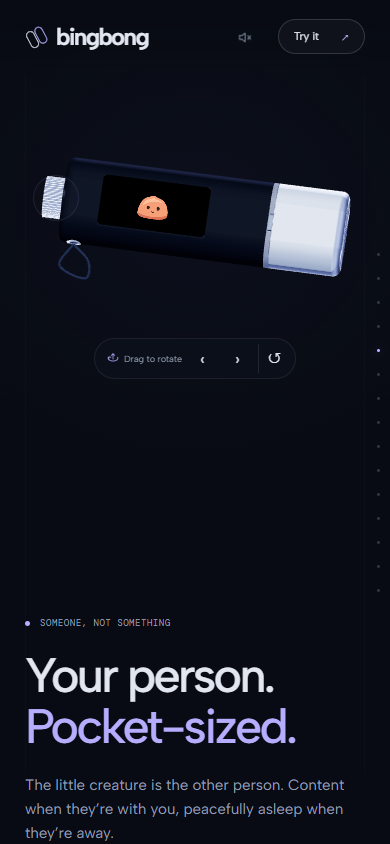
site/qa/scroll/390-creature-0.75.png
