chiangr/bingbong/site/qa/scroll/390-crown-0.5.png

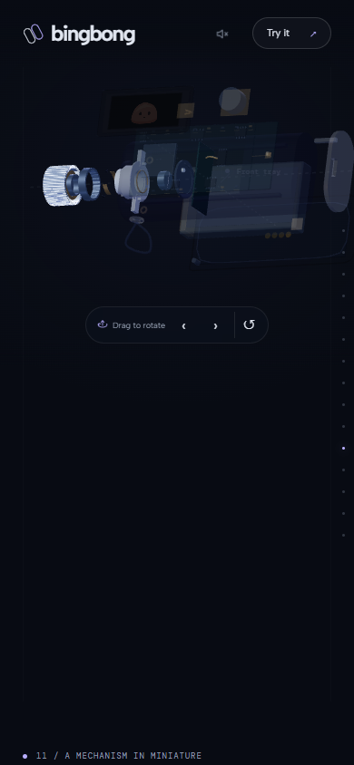
site/qa/scroll/390-crown-0.5.png
