chiangr/bingbong/site/qa/scroll/390-crown-0.25.png

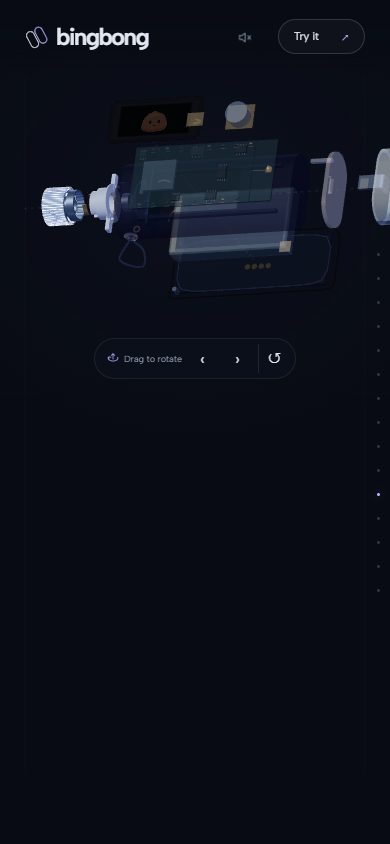
site/qa/scroll/390-crown-0.25.png
