chiangr/bingbong/site/qa/scroll/390-crown-0.75.png

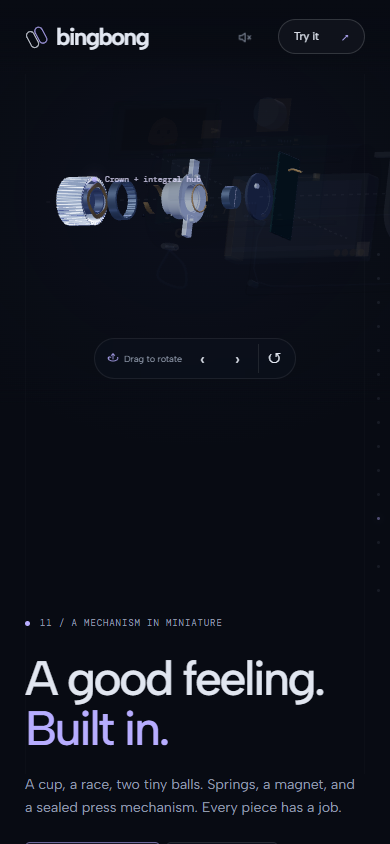
site/qa/scroll/390-crown-0.75.png
