chiangr/bingbong/site/qa/scroll/390-detents-0.5.png

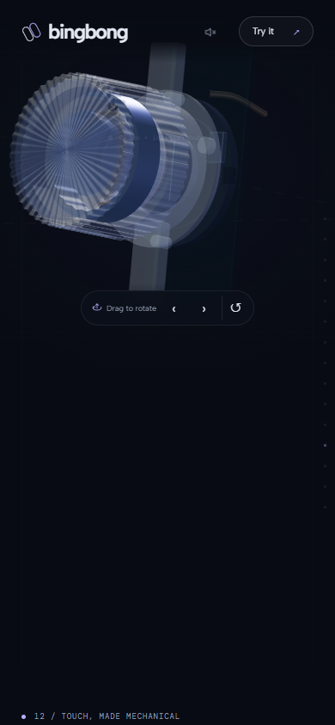
site/qa/scroll/390-detents-0.5.png
