chiangr/bingbong/site/qa/scroll/390-detents-0.25.png

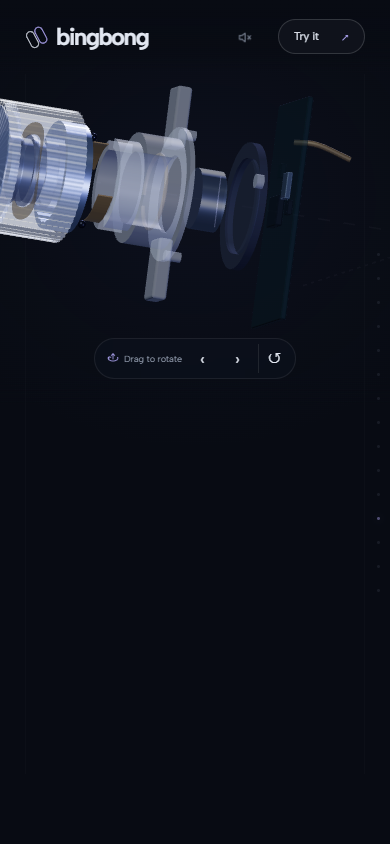
site/qa/scroll/390-detents-0.25.png
