chiangr/bingbong/site/qa/scroll/390-detents-0.75.png

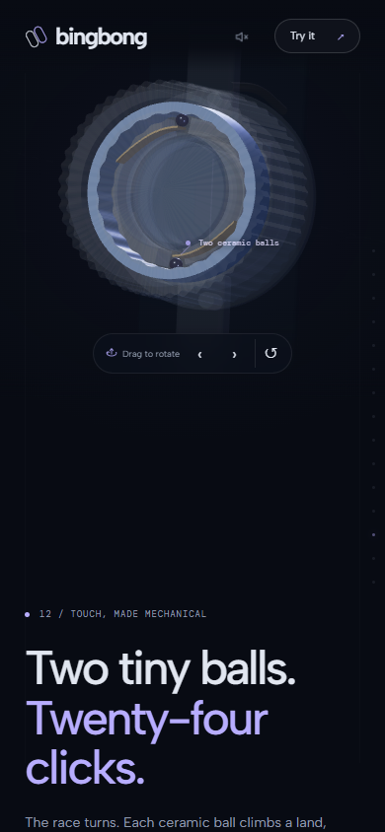
site/qa/scroll/390-detents-0.75.png
