chiangr/bingbong/site/qa/scroll/390-halo-0.75.png

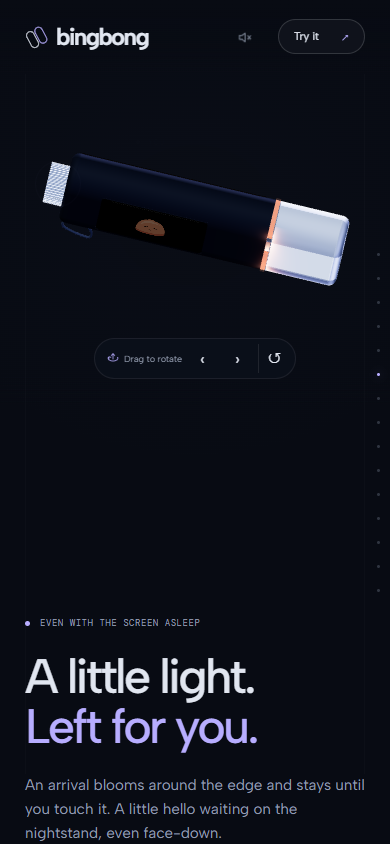
site/qa/scroll/390-halo-0.75.png
