chiangr/bingbong/site/qa/scroll/390-hero-0.5.png

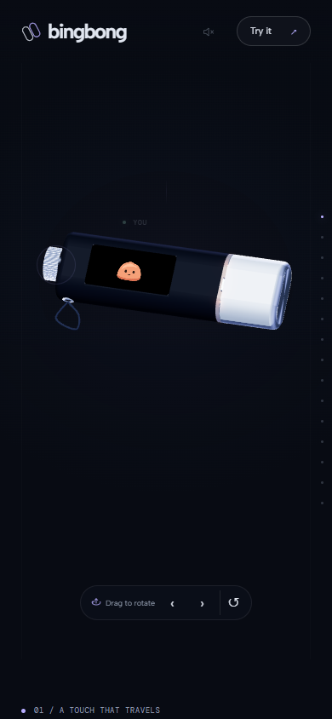
site/qa/scroll/390-hero-0.5.png
