chiangr/bingbong/site/qa/scroll/390-hero-0.25.png

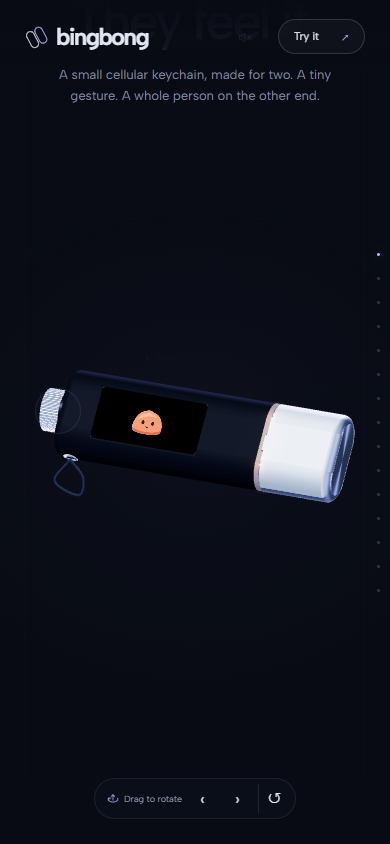
site/qa/scroll/390-hero-0.25.png
