chiangr/bingbong/site/qa/scroll/390-hero-0.75.png

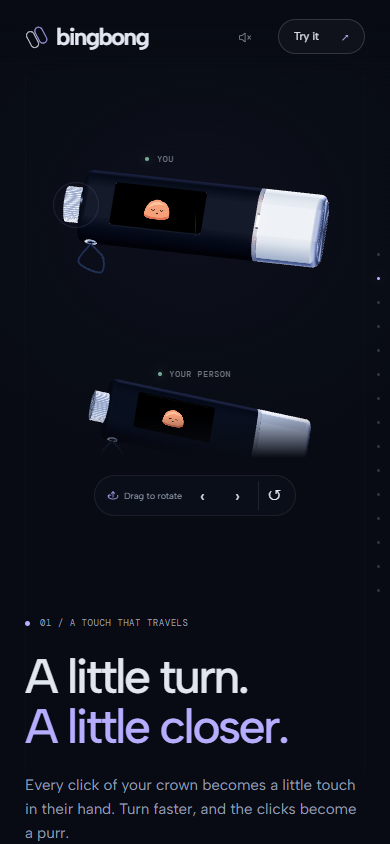
site/qa/scroll/390-hero-0.75.png
