chiangr/bingbong/site/qa/scroll/390-hero-1.png

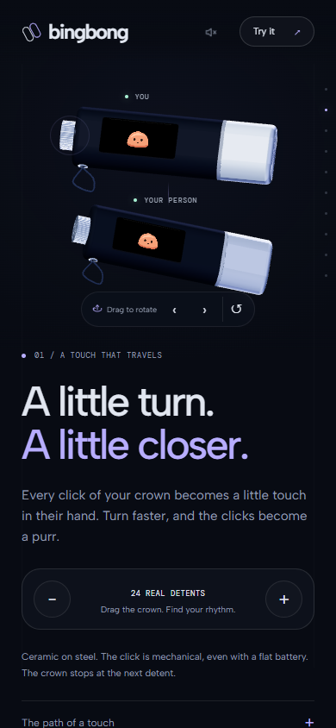
site/qa/scroll/390-hero-1.png
