chiangr/bingbong/site/qa/scroll/390-inside-0.5.png

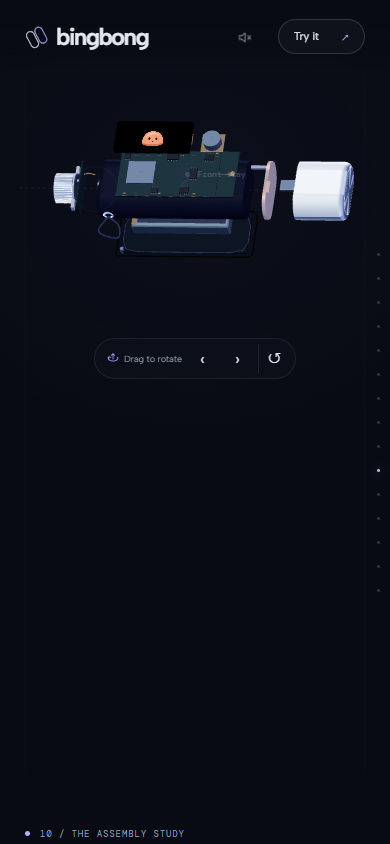
site/qa/scroll/390-inside-0.5.png
