chiangr/bingbong/site/qa/scroll/390-inside-0.75.png

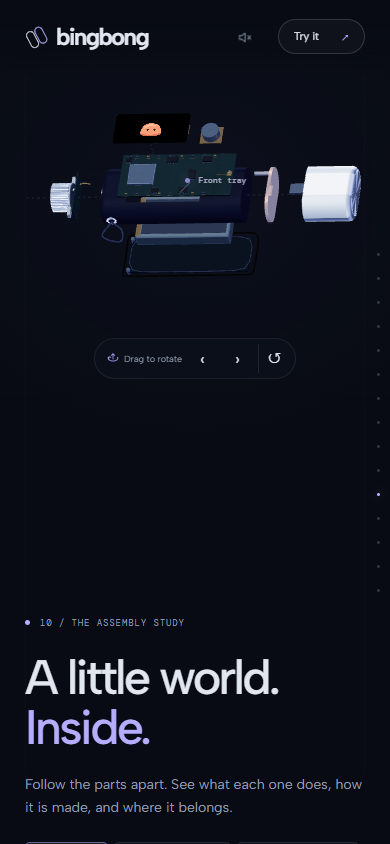
site/qa/scroll/390-inside-0.75.png
