chiangr/bingbong/site/qa/scroll/1440-antenna-0.75.png

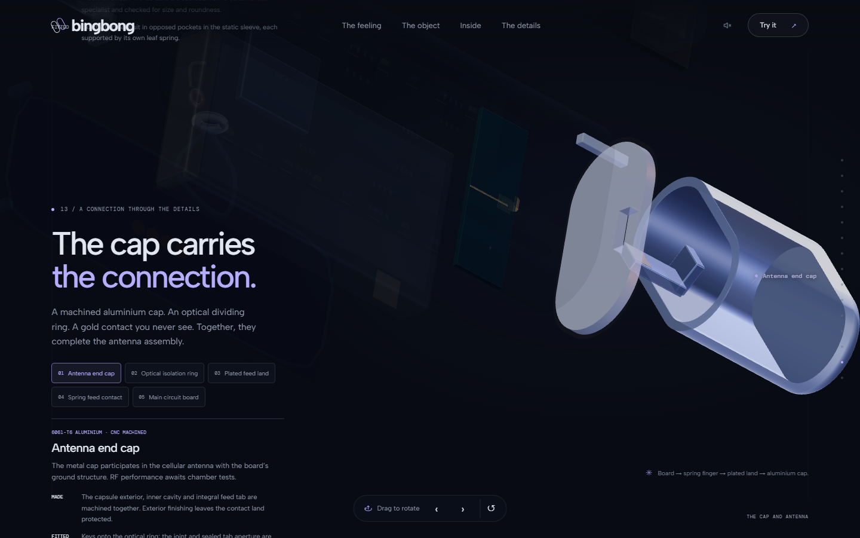
site/qa/scroll/1440-antenna-0.75.png
