chiangr/bingbong/site/qa/scroll/1440-crown-0.25.png

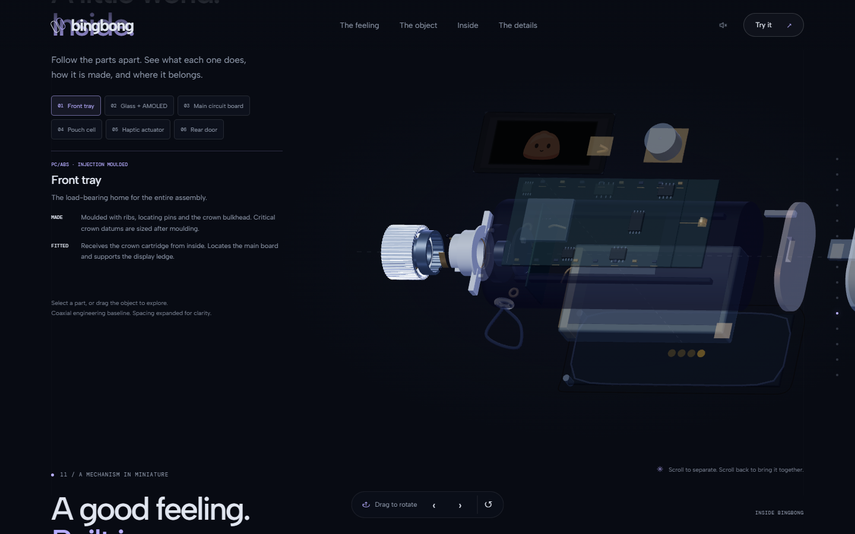
site/qa/scroll/1440-crown-0.25.png
