chiangr/bingbong/site/qa/scroll/1440-hero-1.png

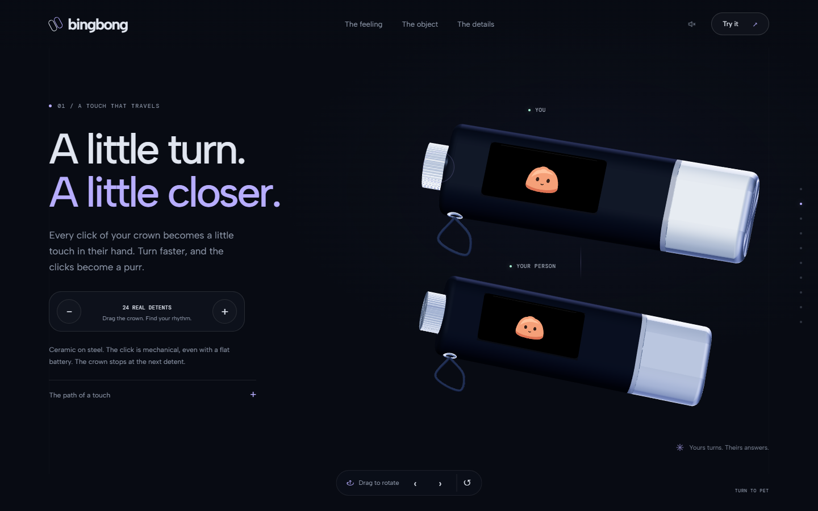
site/qa/scroll/1440-hero-1.png
