chiangr/bingbong/site/qa/scroll/1440-inside-0.5.png

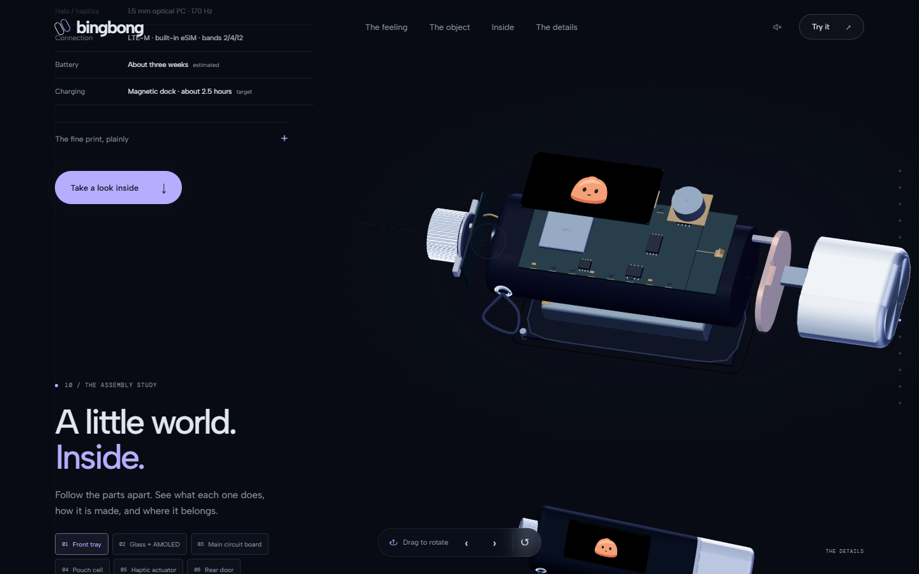
site/qa/scroll/1440-inside-0.5.png
