chiangr/bingbong/site/qa/storyboard.png

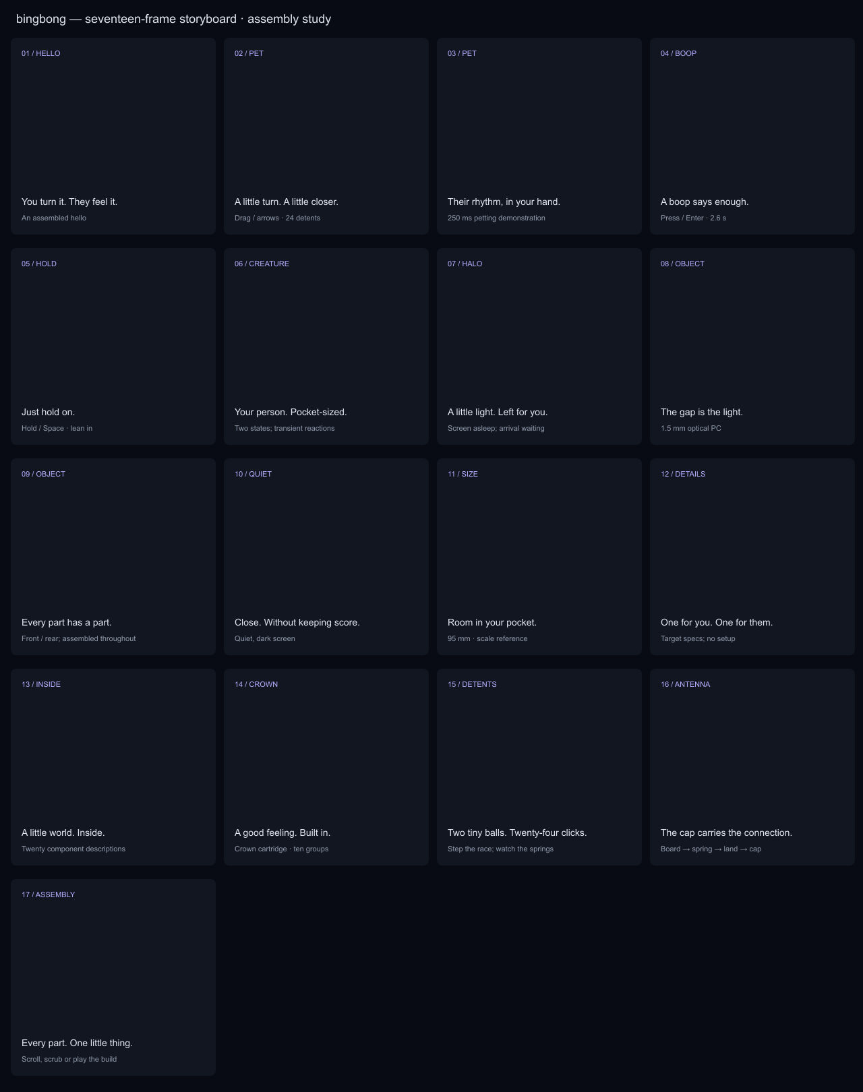
site/qa/storyboard.png
