chiangr/bingbong/firmware/bingbong_pcb/_mech/harwin_S7121R_DRG-02326.pdf

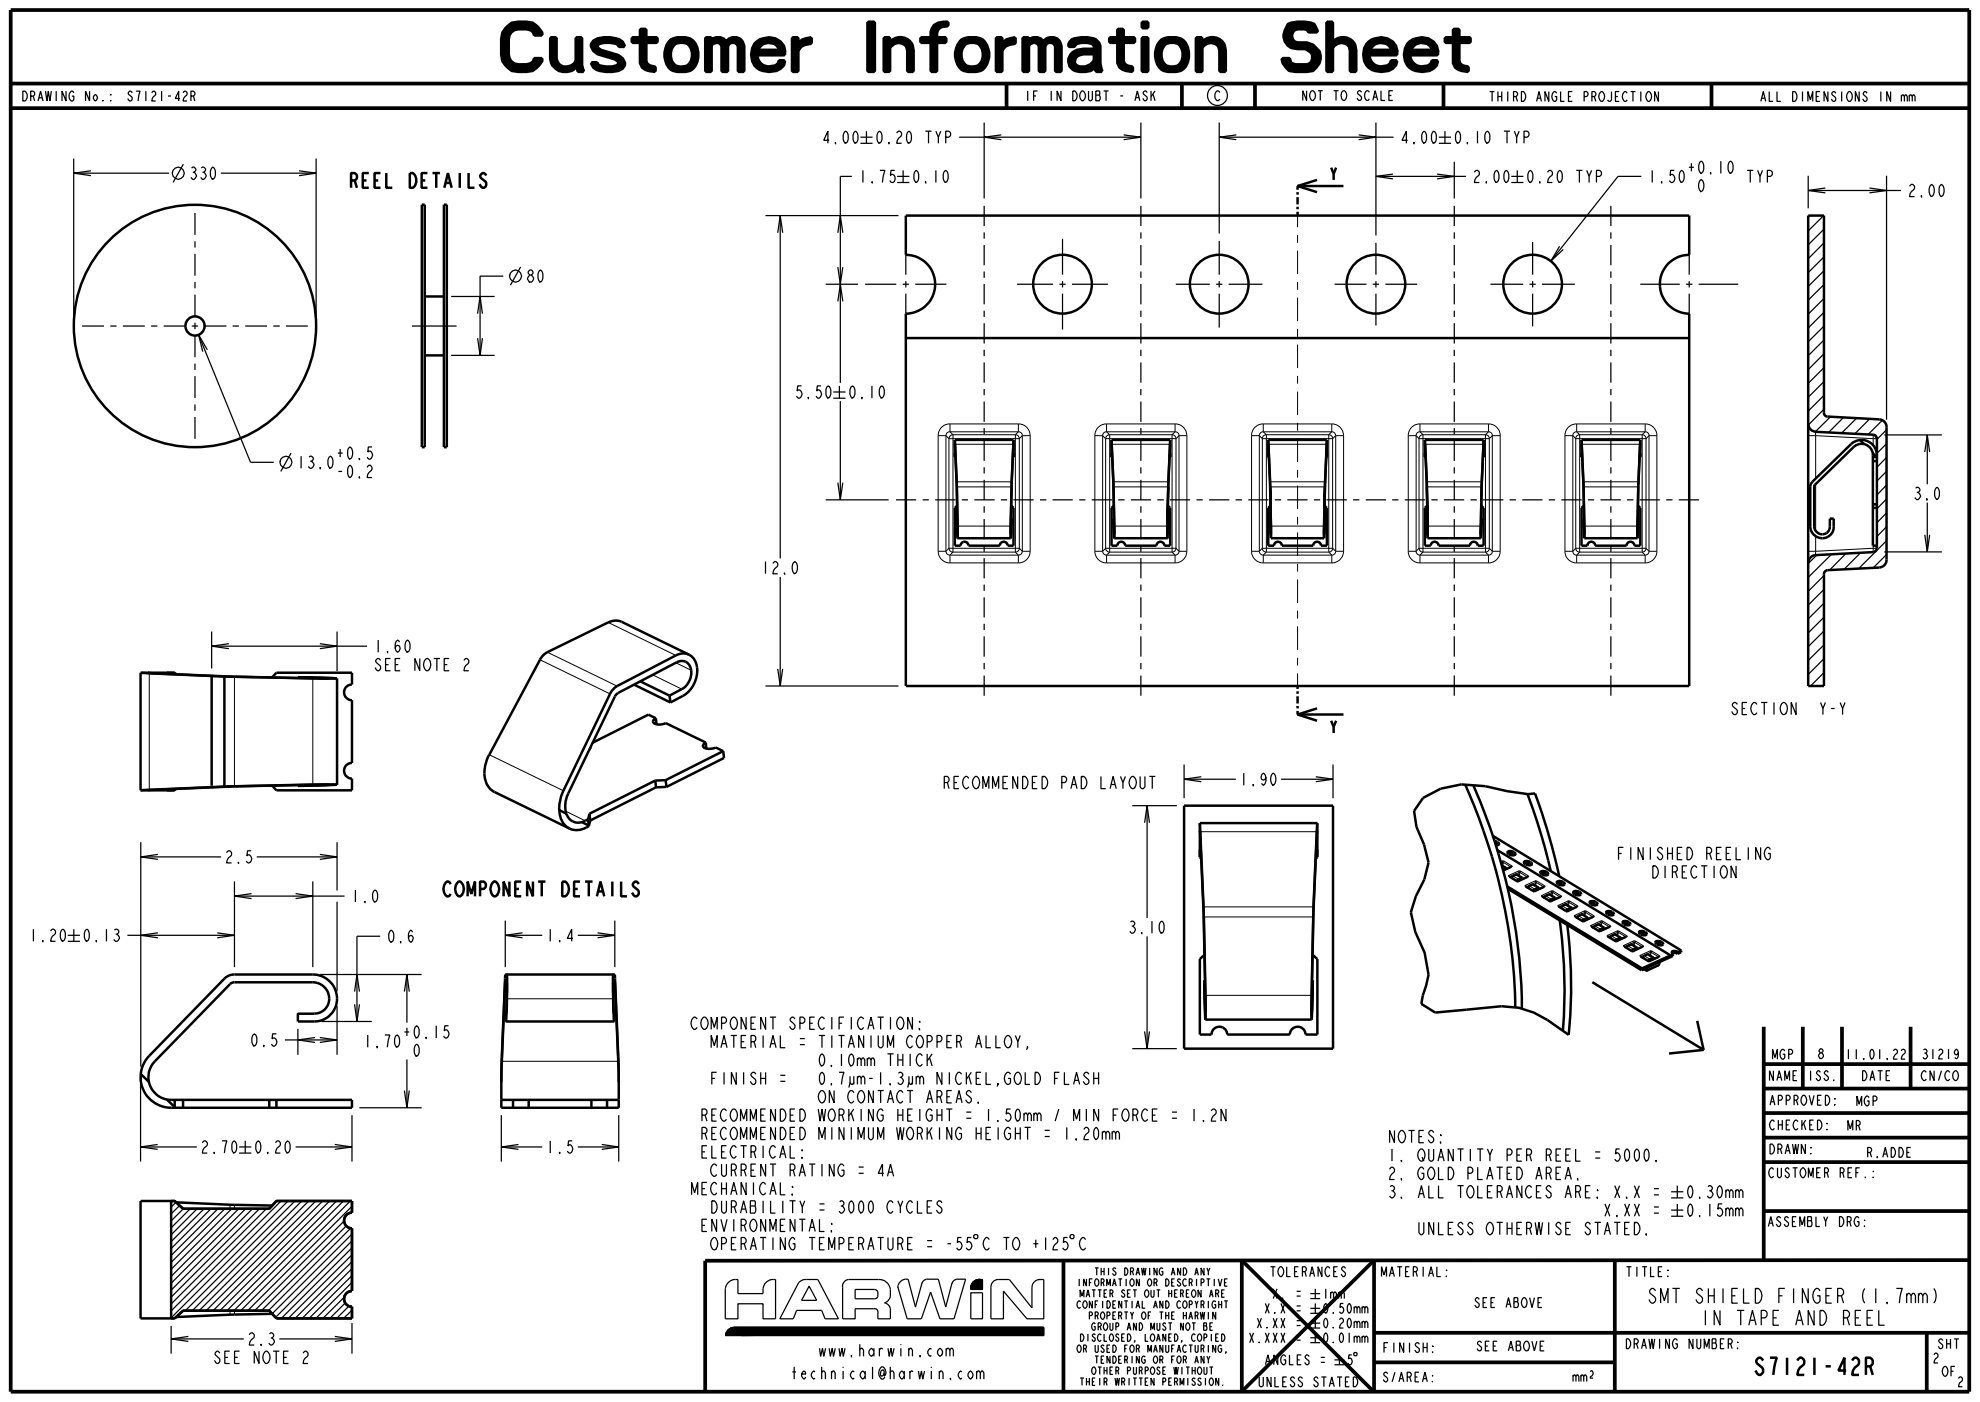
[picture p258: page 1]
