chiangr/bingbong/firmware/bingbong_pcb/_mech/maxim_90-0065E_TDFN8_2x2_landpattern.pdf

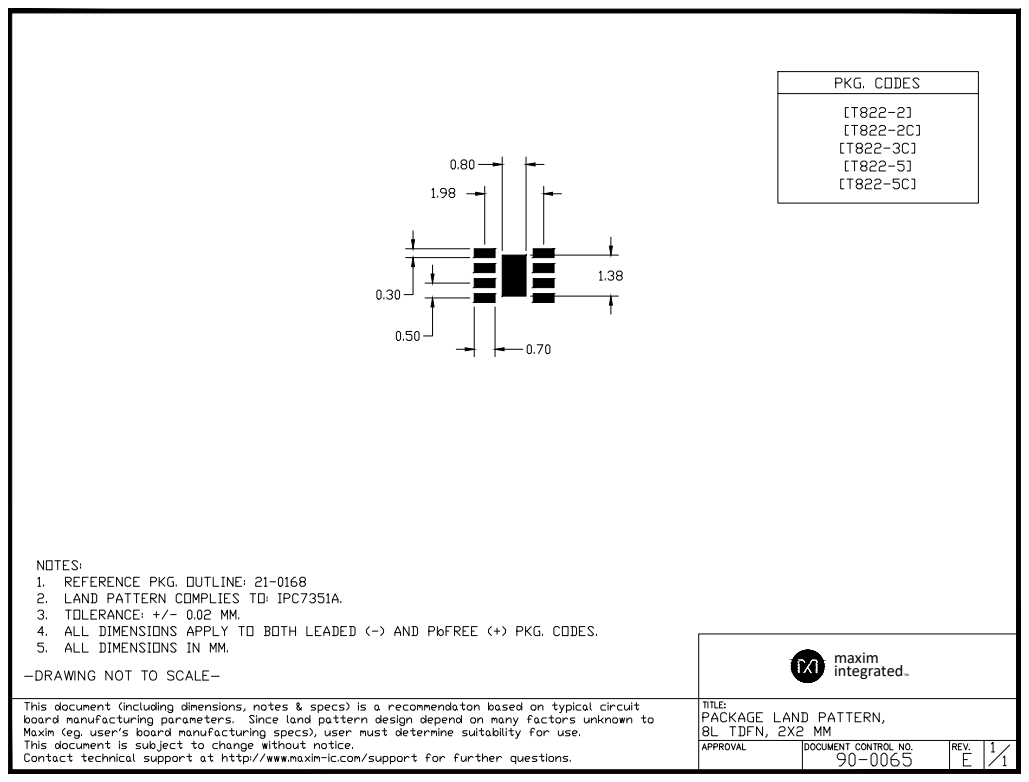
[picture p260: page 1]
maxim integratedTM
