chiangr/bingbong/cad-v3/bingbong/display.kicad_sch

## KiCad design cad-v3/bingbong/display.kicad_sch (2026-09-28)

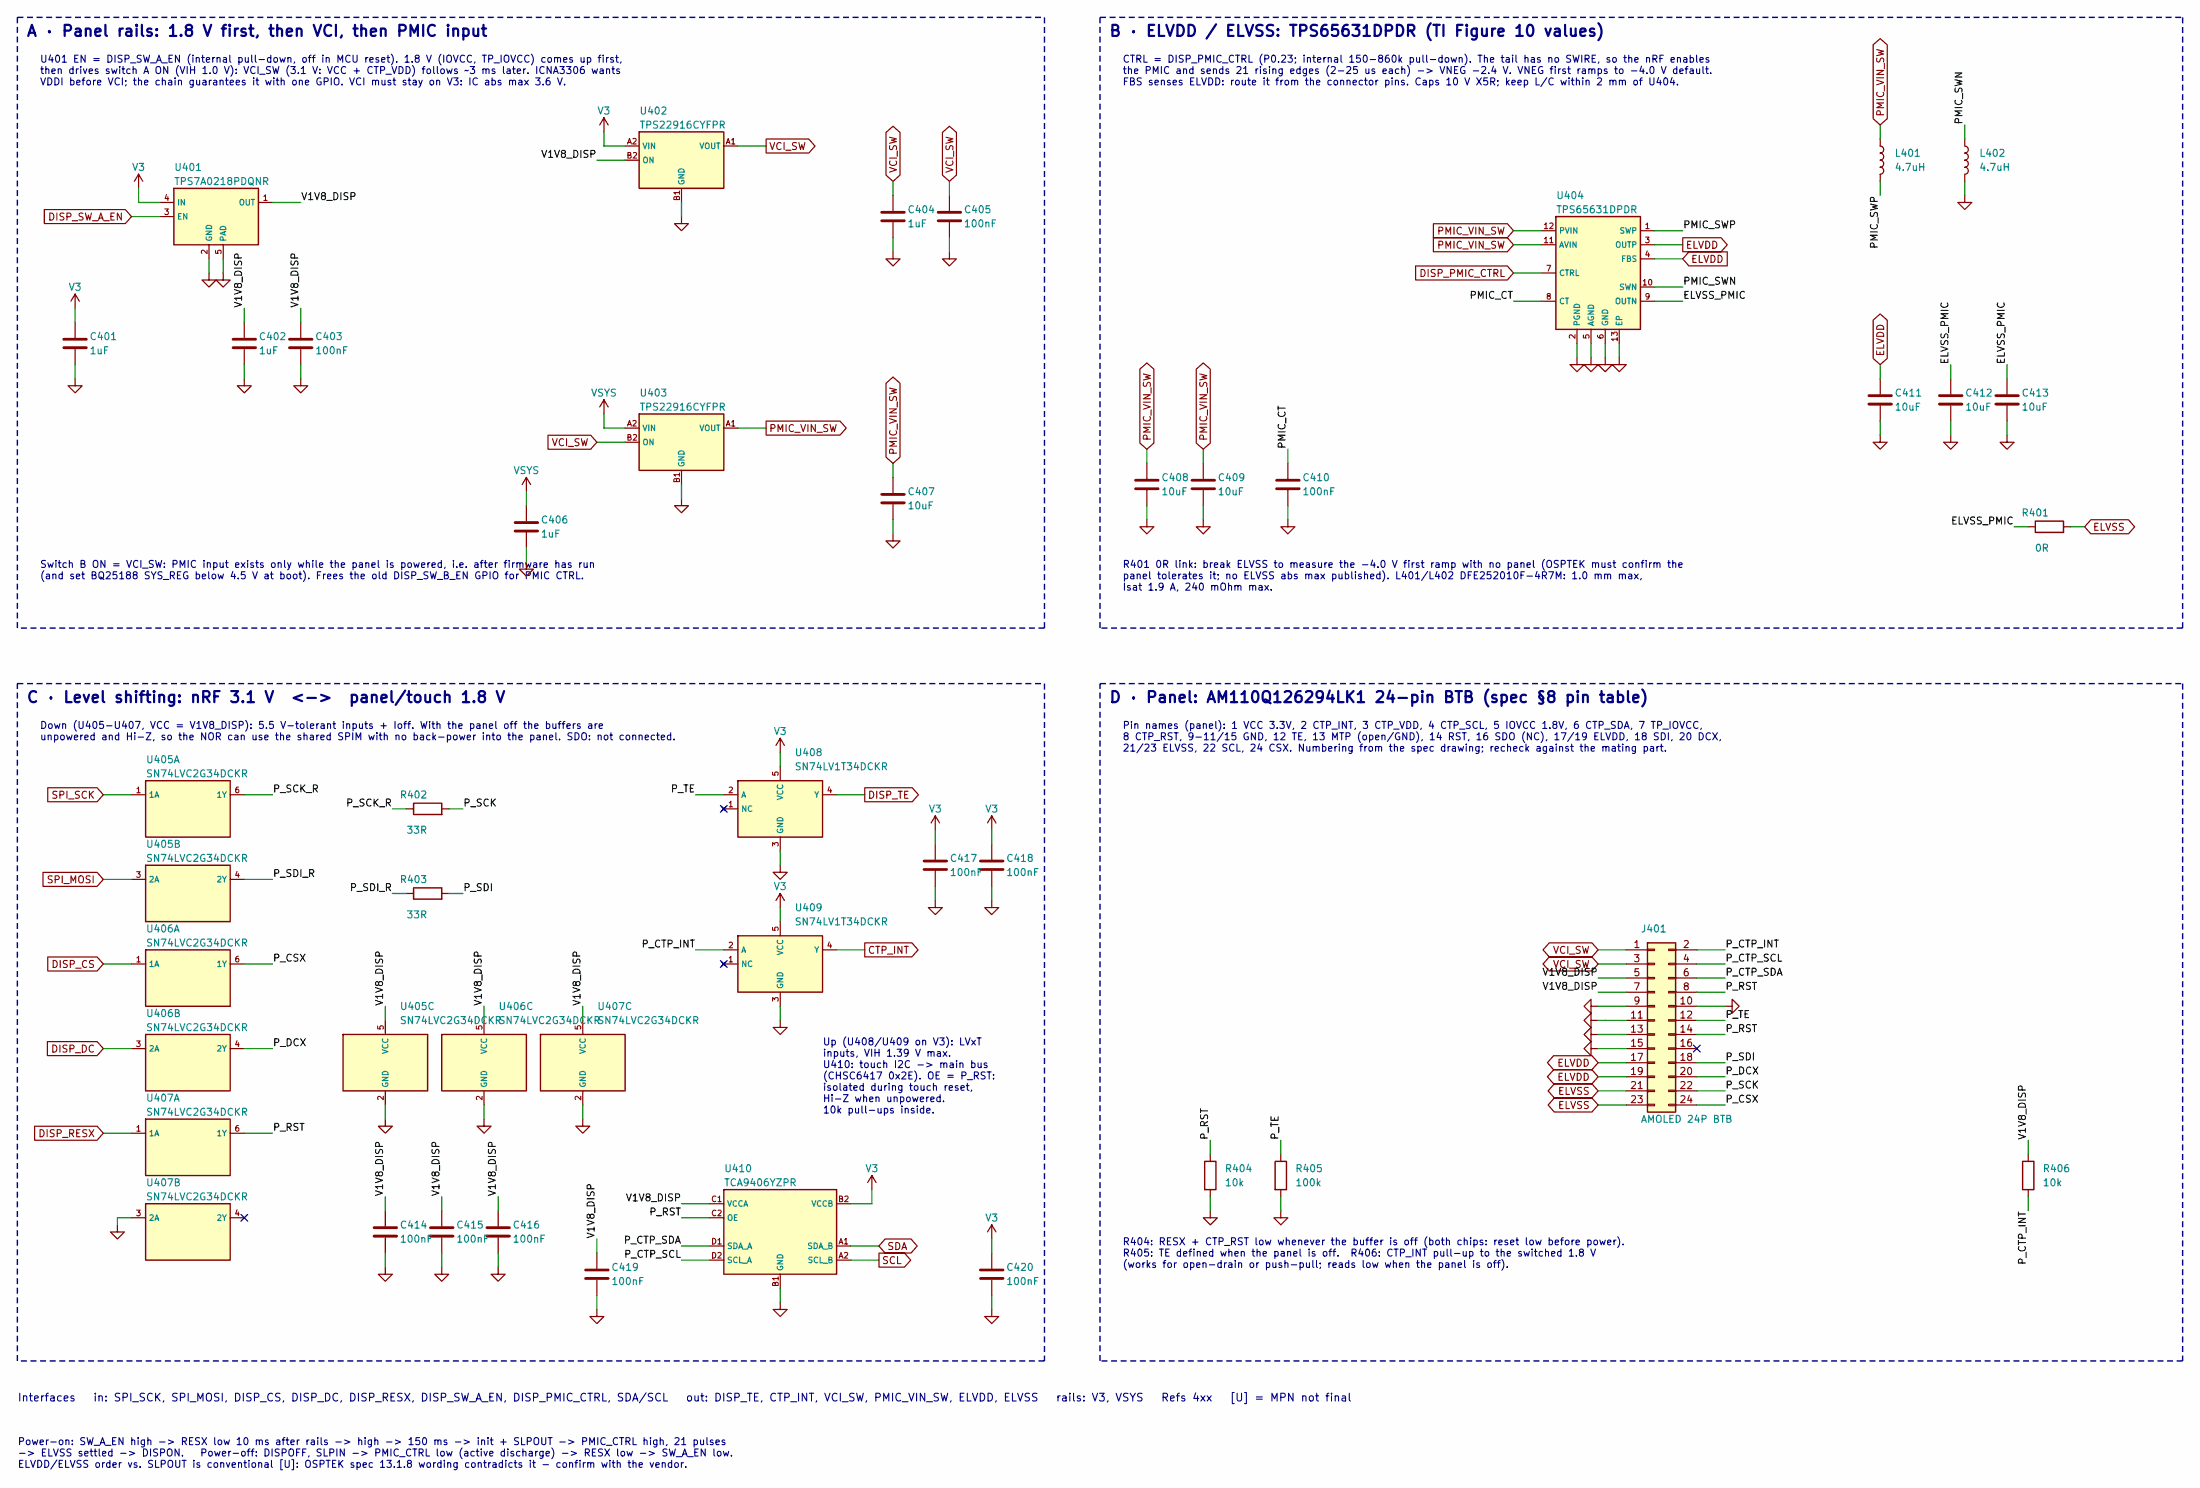
[picture p265: schematic display.kicad_sch]

Parts:
C401, C402, C404, C406: 1uF; C_0402_1005Metric
C403, C405, C410, C414, C415, C416, C417, C418, C419, C420: 100nF; C_0402_1005Metric
C407, C408, C409, C411, C412, C413: 10uF; C_0603_1608Metric
J401: AMOLED 24P BTB; BTB_2x12_OSPTEK_TBD; MPN receptacle mating OSPTEK WB2564024M, 2x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
L401, L402: 4.7uH; L_Murata_DFE252010F; MPN DFE252010F-4R7M=P2
R401: 0R; R_0402_1005Metric
R402, R403: 33R; R_0402_1005Metric
R404, R406: 10k; R_0402_1005Metric
R405: 100k; R_0402_1005Metric
U401: TPS7A0218PDQNR; TI_DQN0004A_X2SON-4_1x1; MPN TPS7A0218PDQNR
U402, U403: TPS22916CYFPR; TI_YFP0004_WCSP-4; MPN TPS22916CYFPR
U404: TPS65631DPDR; TI_DPD0012_WSON-12_3x3; MPN TPS65631DPDR
U405, U406, U407: SN74LVC2G34DCKR; TI_DCK0006A_SC70-6; MPN SN74LVC2G34DCKR
U408, U409: SN74LV1T34DCKR; TI_DCK0005A_SC70-5; MPN SN74LV1T34DCKR
U410: TCA9406YZPR; TI_YZP0008_DSBGA-8; MPN TCA9406YZPR

Connections:
CTP_INT: U409.4 (Y)
DISP_CS: U406.1 (1A)
DISP_DC: U406.3 (2A)
DISP_PMIC_CTRL: U404.7 (CTRL)
DISP_RESX: U407.1 (1A)
DISP_SW_A_EN: U401.3 (EN)
DISP_TE: U408.4 (Y)
ELVDD: C411.1, J401.17, J401.19, U404.3 (OUTP), U404.4 (FBS)
ELVSS: J401.21, J401.23, R401.2
ELVSS_PMIC: C412.1, C413.1, R401.1, U404.9 (OUTN)
GND: C401.2, C402.2, C403.2, C404.2, C405.2, C406.2, C407.2, C408.2, C409.2, C410.2, C411.2, C412.2, C413.2, C414.2, C415.2, C416.2, C417.2, C418.2, C419.2, C420.2, J401.9, J401.10, J401.11, J401.13, J401.15, L402.2, R404.2, R405.2, U401.2 (GND), U401.5 (PAD), U402.B1 (GND), U403.B1 (GND), U404.2 (PGND), U404.5 (AGND), U404.6 (GND), U404.13 (EP), U405.2 (GND), U406.2 (GND), U407.2 (GND), U407.3 (2A), U408.3 (GND), U409.3 (GND), U410.B1 (GND)
PMIC_CT: C410.1, U404.8 (CT)
PMIC_SWN: L402.1, U404.10 (SWN)
PMIC_SWP: L401.2, U404.1 (SWP)
PMIC_VIN_SW: C407.1, C408.1, C409.1, L401.1, U403.A1 (VOUT), U404.11 (AVIN), U404.12 (PVIN)
P_CSX: J401.24, U406.6 (1Y)
P_CTP_INT: J401.2, R406.2, U409.2 (A)
P_CTP_SCL: J401.4, U410.D2 (SCL_A)
P_CTP_SDA: J401.6, U410.D1 (SDA_A)
P_DCX: J401.20, U406.4 (2Y)
P_RST: J401.8, J401.14, R404.1, U407.6 (1Y), U410.C2 (OE)
P_SCK: J401.22, R402.2
P_SCK_R: R402.1, U405.6 (1Y)
P_SDI: J401.18, R403.2
P_SDI_R: R403.1, U405.4 (2Y)
P_TE: J401.12, R405.1, U408.2 (A)
SCL: U410.A2 (SCL_B)
SDA: U410.A1 (SDA_B)
SPI_MOSI: U405.3 (2A)
SPI_SCK: U405.1 (1A)
V1V8_DISP: C402.1, C403.1, C414.1, C415.1, C416.1, C419.1, J401.5, J401.7, R406.1, U401.1 (OUT), U402.B2 (ON), U405.5 (VCC), U406.5 (VCC), U407.5 (VCC), U410.C1 (VCCA)
V3: C401.1, C417.1, C418.1, C420.1, U401.4 (IN), U402.A2 (VIN), U408.5 (VCC), U409.5 (VCC), U410.B2 (VCCB)
VCI_SW: C404.1, C405.1, J401.1, J401.3, U402.A1 (VOUT), U403.B2 (ON)
VSYS: C406.1, U403.A2 (VIN)

Notes on the sheet:
A · Panel rails: 1.8 V first, then VCI, then PMIC input
U401 EN = DISP_SW_A_EN (internal pull-down, off in MCU reset). 1.8 V (IOVCC, TP_IOVCC) comes up first, then drives switch A ON (VIH 1.0 V): VCI_SW (3.1 V: VCC + CTP_VDD) follows ~3 ms later. ICNA3306 wants VDDI before VCI; the chain guarantees it with one GPIO. VCI must stay on V3: IC abs max 3.6 V.
Switch B ON = VCI_SW: PMIC input exists only while the panel is powered, i.e. after firmware has run (and set BQ25188 SYS_REG below 4.5 V at boot). Frees the old DISP_SW_B_EN GPIO for PMIC CTRL.
B · ELVDD / ELVSS: TPS65631DPDR (TI Figure 10 values)
CTRL = DISP_PMIC_CTRL (P0.23; internal 150-860k pull-down). The tail has no SWIRE, so the nRF enables the PMIC and sends 21 rising edges (2-25 us each) -> VNEG -2.4 V. VNEG first ramps to -4.0 V default. FBS senses ELVDD: route it from the connector pins. Caps 10 V X5R; keep L/C within 2 mm of U404.
R401 0R link: break ELVSS to measure the -4.0 V first ramp with no panel (OSPTEK must confirm the panel tolerates it; no ELVSS abs max published). L401/L402 DFE252010F-4R7M: 1.0 mm max, Isat 1.9 A, 240 mOhm max.
C · Level shifting: nRF 3.1 V <-> panel/touch 1.8 V
Down (U405-U407, VCC = V1V8_DISP): 5.5 V-tolerant inputs + Ioff. With the panel off the buffers are unpowered and Hi-Z, so the NOR can use the shared SPIM with no back-power into the panel. SDO: not connected.
Up (U408/U409 on V3): LVxT inputs, VIH 1.39 V max. U410: touch I2C -> main bus (CHSC6417 0x2E). OE = P_RST: isolated during touch reset, Hi-Z when unpowered. 10k pull-ups inside.
D · Panel: AM110Q126294LK1 24-pin BTB (spec §8 pin table)
Pin names (panel): 1 VCC 3.3V, 2 CTP_INT, 3 CTP_VDD, 4 CTP_SCL, 5 IOVCC 1.8V, 6 CTP_SDA, 7 TP_IOVCC, 8 CTP_RST, 9-11/15 GND, 12 TE, 13 MTP (open/GND), 14 RST, 16 SDO (NC), 17/19 ELVDD, 18 SDI, 20 DCX, 21/23 ELVSS, 22 SCL, 24 CSX. Numbering from the spec drawing; recheck against the mating part.
R404: RESX + CTP_RST low whenever the buffer is off (both chips: reset low before power). R405: TE defined when the panel is off. R406: CTP_INT pull-up to the switched 1.8 V (works for open-drain or push-pull; reads low when the panel is off).
Interfaces in: SPI_SCK, SPI_MOSI, DISP_CS, DISP_DC, DISP_RESX, DISP_SW_A_EN, DISP_PMIC_CTRL, SDA/SCL out: DISP_TE, CTP_INT, VCI_SW, PMIC_VIN_SW, ELVDD, ELVSS rails: V3, VSYS Refs 4xx [U] = MPN not final
Power-on: SW_A_EN high -> RESX low 10 ms after rails -> high -> 150 ms -> init + SLPOUT -> PMIC_CTRL high, 21 pulses -> ELVSS settled -> DISPON. Power-off: DISPOFF, SLPIN -> PMIC_CTRL low (active discharge) -> RESX low -> SW_A_EN low. ELVDD/ELVSS order vs. SLPOUT is conventional [U]: OSPTEK spec 13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
