chiangr/bingbong/cad-v3/bingbong/dock.kicad_sch

## KiCad design cad-v3/bingbong/dock.kicad_sch (2026-09-28)

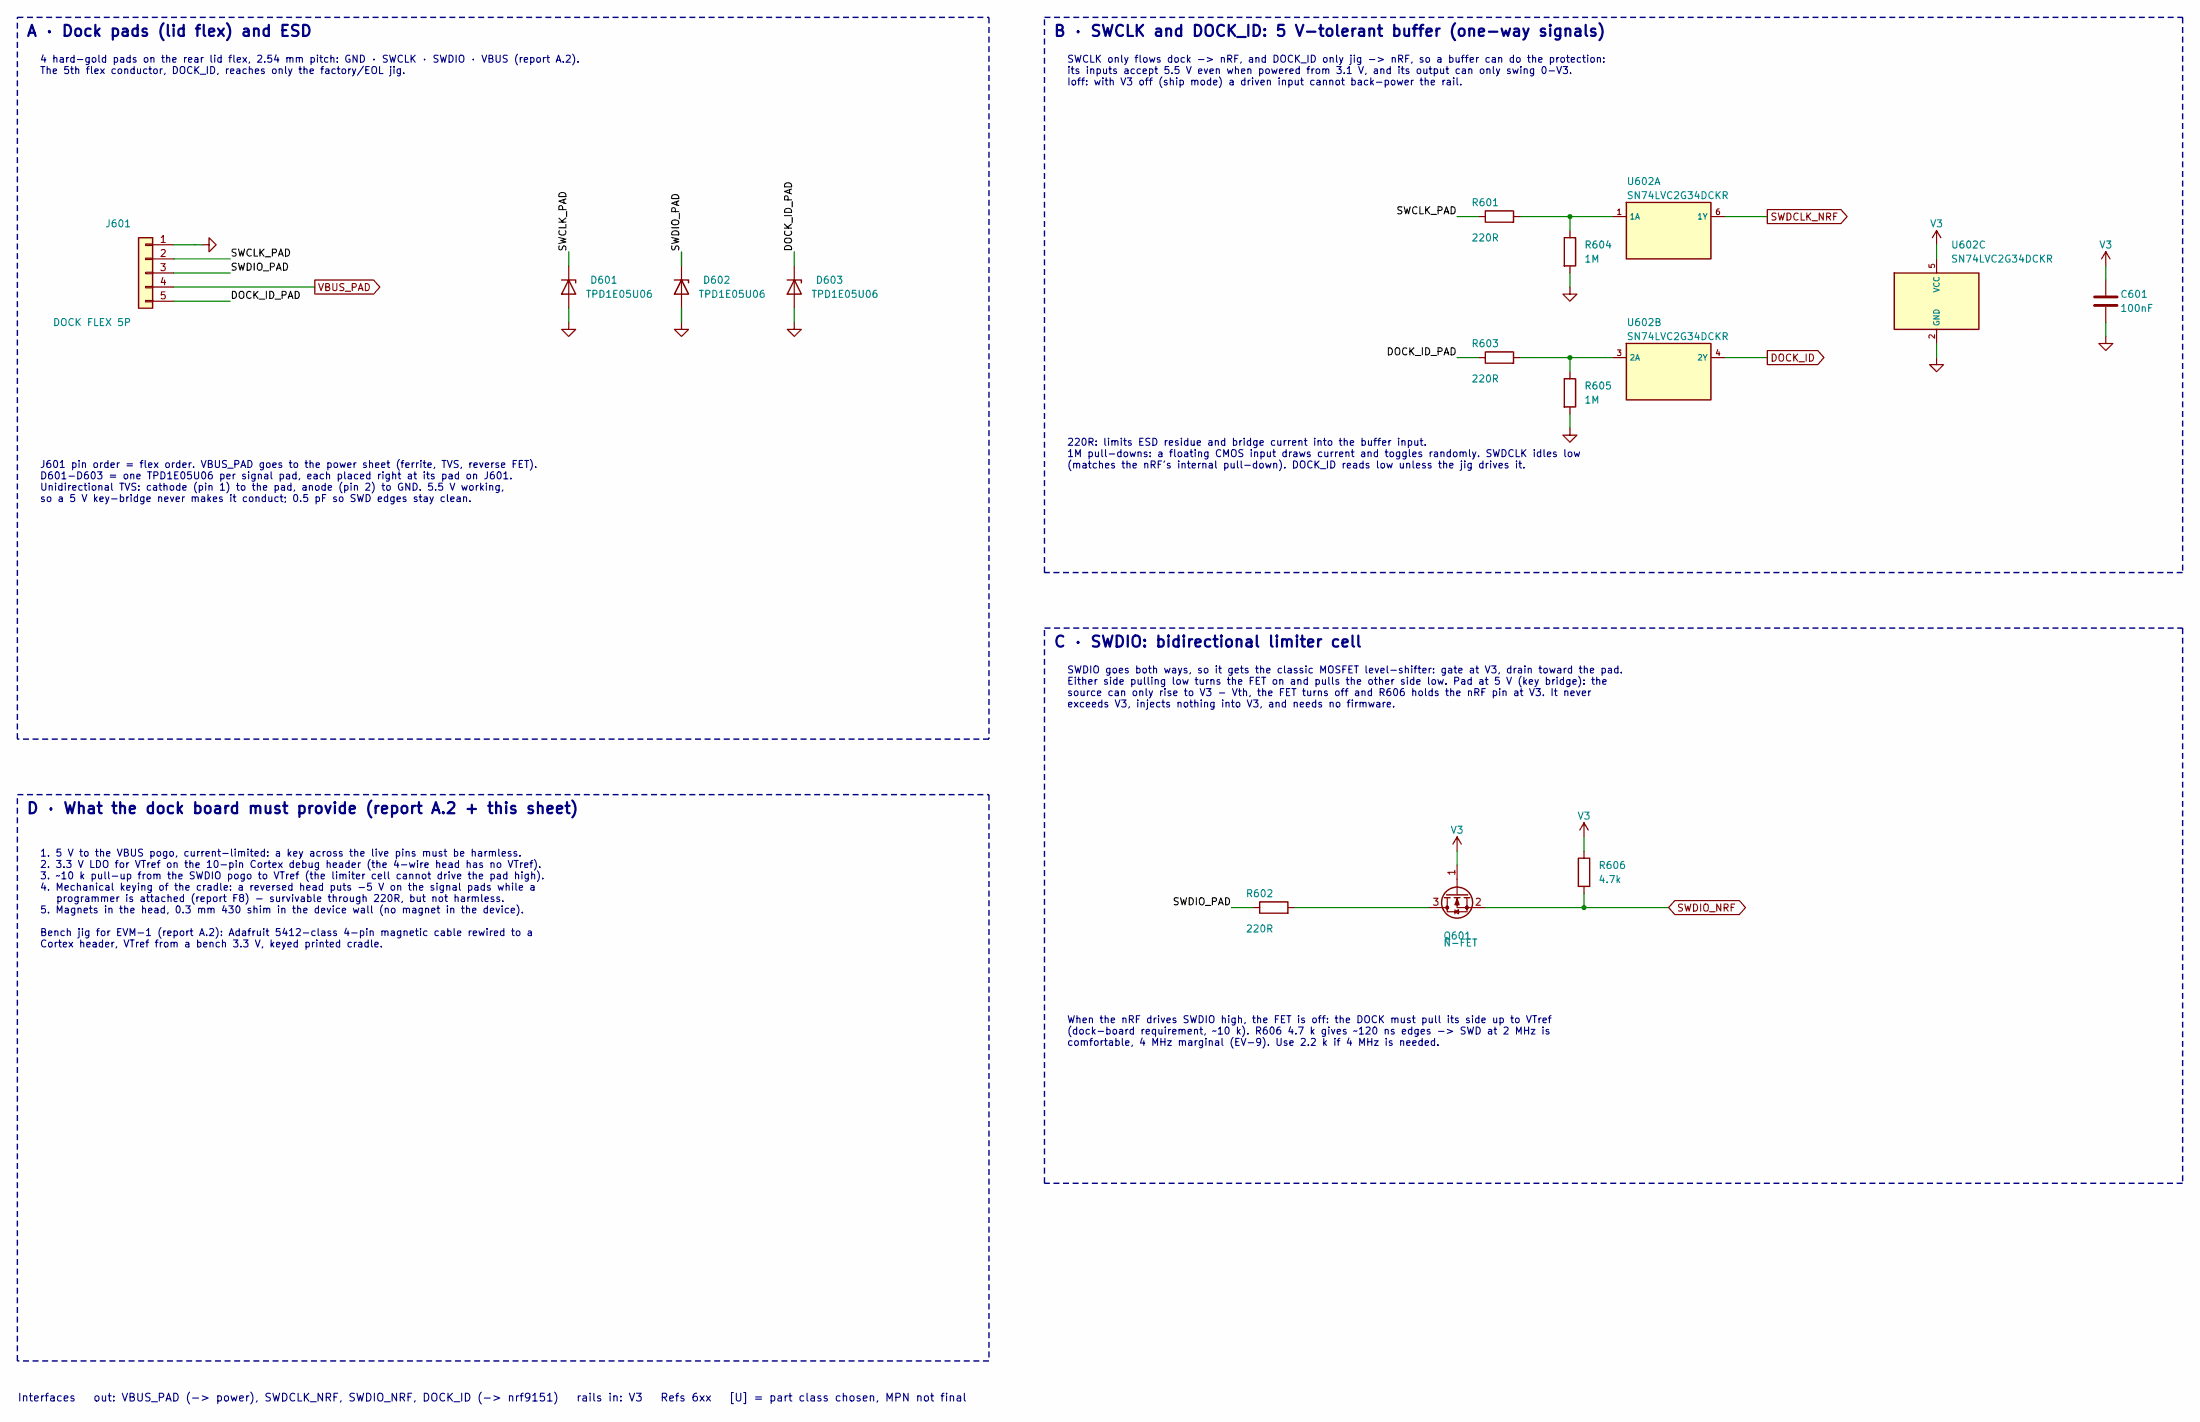
[picture p266: schematic dock.kicad_sch]

Parts:
C601: 100nF; C_0402_1005Metric
D601, D602, D603: TPD1E05U06; TI_DYA0002A_SOD-523; MPN TPD1E05U06DYAR
J601: DOCK FLEX 5P; B2B_0.4mm_5P_TBD; MPN 0.4 mm B2B 5-way to lid flex [U]
Q601: N-FET; SOT-523; MPN DMN26D0UT-7 (Vth 0.5-1.0 V, Ciss 14 pF)
R601, R602, R603: 220R; R_0402_1005Metric
R604, R605: 1M; R_0402_1005Metric
R606: 4.7k; R_0402_1005Metric
U602: SN74LVC2G34DCKR; TI_DCK0006A_SC70-6; MPN SN74LVC2G34DCKR

Connections:
DOCK_ID: U602.4 (2Y)
DOCK_ID_PAD: D603.1 (K), J601.5, R603.1
GND: C601.2, D601.2 (A), D602.2 (A), D603.2 (A), J601.1, R604.2, R605.2, U602.2 (GND)
unnamed: Q601.3 (D), R602.2
unnamed: R601.2, R604.1, U602.1 (1A)
unnamed: R603.2, R605.1, U602.3 (2A)
SWCLK_PAD: D601.1 (K), J601.2, R601.1
SWDCLK_NRF: U602.6 (1Y)
SWDIO_NRF: Q601.2 (S), R606.2
SWDIO_PAD: D602.1 (K), J601.3, R602.1
V3: C601.1, Q601.1 (G), R606.1, U602.5 (VCC)
VBUS_PAD: J601.4

Notes on the sheet:
A · Dock pads (lid flex) and ESD
4 hard-gold pads on the rear lid flex, 2.54 mm pitch: GND · SWCLK · SWDIO · VBUS (report A.2). The 5th flex conductor, DOCK_ID, reaches only the factory/EOL jig.
J601 pin order = flex order. VBUS_PAD goes to the power sheet (ferrite, TVS, reverse FET). D601-D603 = one TPD1E05U06 per signal pad, each placed right at its pad on J601. Unidirectional TVS: cathode (pin 1) to the pad, anode (pin 2) to GND. 5.5 V working, so a 5 V key-bridge never makes it conduct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
B · SWCLK and DOCK_ID: 5 V-tolerant buffer (one-way signals)
SWCLK only flows dock -> nRF, and DOCK_ID only jig -> nRF, so a buffer can do the protection: its inputs accept 5.5 V even when powered from 3.1 V, and its output can only swing 0-V3. Ioff: with V3 off (ship mode) a driven input cannot back-power the rail.
220R: limits ESD residue and bridge current into the buffer input. 1M pull-downs: a floating CMOS input draws current and toggles randomly. SWDCLK idles low (matches the nRF's internal pull-down). DOCK_ID reads low unless the jig drives it.
C · SWDIO: bidirectional limiter cell
SWDIO goes both ways, so it gets the classic MOSFET level-shifter: gate at V3, drain toward the pad. Either side pulling low turns the FET on and pulls the other side low. Pad at 5 V (key bridge): the source can only rise to V3 - Vth, the FET turns off and R606 holds the nRF pin at V3. It never exc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
When the nRF drives SWDIO high, the FET is off: the DOCK must pull its side up to VTref (dock-board requirement, ~10 k). R606 4.7 k gives ~120 ns edges -> SWD at 2 MHz is comfortable, 4 MHz marginal (EV-9). Use 2.2 k if 4 MHz is needed.
D · What the dock board must provide (report A.2 + this sheet)
1. 5 V to the VBUS pogo, current-limited: a key across the live pins must be harmless. 2. 3.3 V LDO for VTref on the 10-pin Cortex debug header (the 4-wire head has no VTref). 3. ~10 k pull-up from the SWDIO pogo to VTref (the limiter cell cannot drive the pad high). 4. Mechanical keying of the cra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
Interfaces out: VBUS_PAD (-> power), SWDCLK_NRF, SWDIO_NRF, DOCK_ID (-> nrf9151) rails in: V3 Refs 6xx [U] = part class chosen, MPN not final
