chiangr/bingbong/cad-v3/bingbong/nrf9151.kicad_sch

## KiCad design cad-v3/bingbong/nrf9151.kicad_sch (2026-09-28)

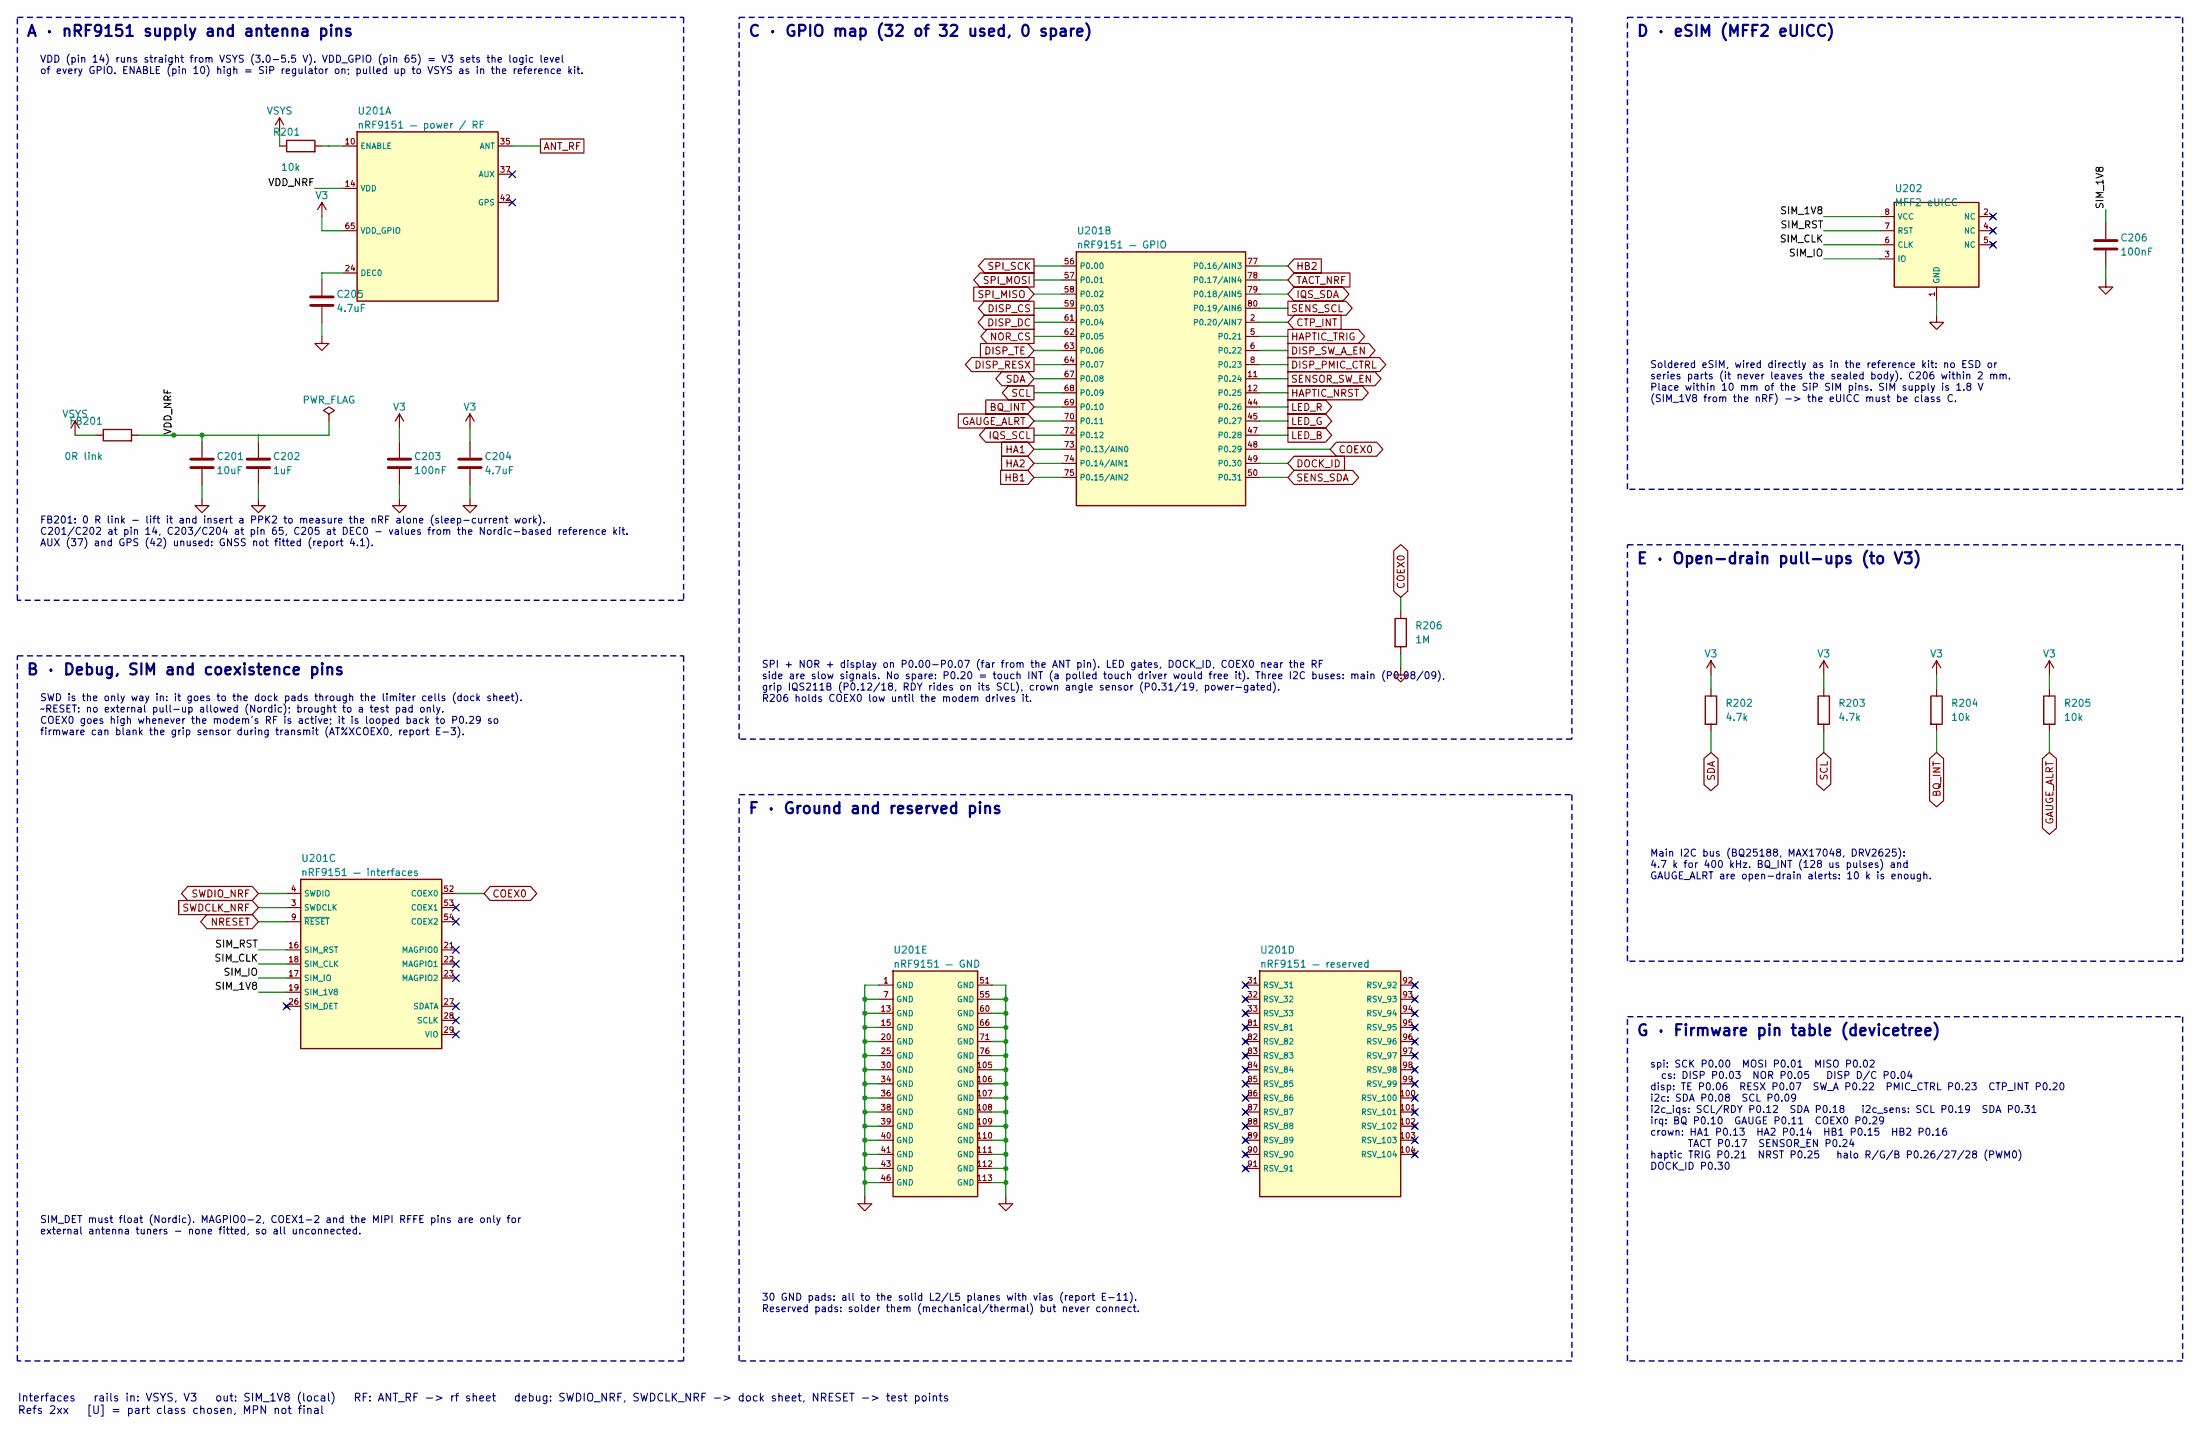
[picture p267: schematic nrf9151.kicad_sch]

Parts:
C201: 10uF; C_0603_1608Metric
C202: 1uF; C_0402_1005Metric
C203, C206: 100nF; C_0402_1005Metric
C204, C205: 4.7uF; C_0402_1005Metric
FB201: 0R link; R_0603_1608Metric; MPN 0 ohm 0603 (remove for PPK2 current mea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
R201, R204, R205: 10k; R_0402_1005Metric
R202, R203: 4.7k; R_0402_1005Metric
R206: 1M; R_0402_1005Metric
U201: nRF9151 — power / RF; Nordic_nRF9151_LGA-113_12.1x11.1; MPN NRF9151-LACA-R
U202: MFF2 eUICC; MFF2_DFN-8_5x6; MPN MFF2 eUICC, class C 1.8 V, SGP.32, supp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

Connections:
ANT_RF: U201.35 (ANT)
BQ_INT: R204.2, U201.69 (P0.10)
COEX0: R206.1, U201.48 (P0.29), U201.52 (COEX0)
CTP_INT: U201.2 (P0.20/AIN7)
DISP_CS: U201.59 (P0.03)
DISP_DC: U201.61 (P0.04)
DISP_PMIC_CTRL: U201.8 (P0.23)
DISP_RESX: U201.64 (P0.07)
DISP_SW_A_EN: U201.6 (P0.22)
DISP_TE: U201.63 (P0.06)
DOCK_ID: U201.49 (P0.30)
GAUGE_ALRT: R205.2, U201.70 (P0.11)
GND: C201.2, C202.2, C203.2, C204.2, C205.2, C206.2, R206.2, U201.1 (GND), U201.7 (GND), U201.13 (GND), U201.15 (GND), U201.20 (GND), U201.25 (GND), U201.30 (GND), U201.34 (GND), U201.36 (GND), U201.38 (GND), U201.39 (GND), U201.40 (GND), U201.41 (GND), U201.43 (GND), U201.46 (GND), U201.51 (GND), U201.55 (GND), U201.60 (GND), U201.66 (GND), U201.71 (GND), U201.76 (GND), U201.105 (GND), U201.106 (GND), U201.107 (GND), U201.108 (GND), U201.109 (GND), U201.110 (GND), U201.111 (GND), U201.112 (GND), U201.113 (GND), U202.1 (GND)
HA1: U201.73 (P0.13/AIN0)
HA2: U201.74 (P0.14/AIN1)
HAPTIC_NRST: U201.12 (P0.25)
HAPTIC_TRIG: U201.5 (P0.21)
HB1: U201.75 (P0.15/AIN2)
HB2: U201.77 (P0.16/AIN3)
IQS_SCL: U201.72 (P0.12)
IQS_SDA: U201.79 (P0.18/AIN5)
LED_B: U201.47 (P0.28)
LED_G: U201.45 (P0.27)
LED_R: U201.44 (P0.26)
NOR_CS: U201.62 (P0.05)
NRESET: U201.9 (~RESET)
unnamed: C205.1, U201.24 (DEC0)
unnamed: R201.2, U201.10 (ENABLE)
SCL: R203.2, U201.68 (P0.09)
SDA: R202.2, U201.67 (P0.08)
SENSOR_SW_EN: U201.11 (P0.24)
SENS_SCL: U201.80 (P0.19/AIN6)
SENS_SDA: U201.50 (P0.31)
SIM_1V8: C206.1, U201.19 (SIM_1V8), U202.8 (VCC)
SIM_CLK: U201.18 (SIM_CLK), U202.6 (CLK)
SIM_IO: U201.17 (SIM_IO), U202.3 (IO)
SIM_RST: U201.16 (SIM_RST), U202.7 (RST)
SPI_MISO: U201.58 (P0.02)
SPI_MOSI: U201.57 (P0.01)
SPI_SCK: U201.56 (P0.00)
SWDCLK_NRF: U201.3 (SWDCLK)
SWDIO_NRF: U201.4 (SWDIO)
TACT_NRF: U201.78 (P0.17/AIN4)
V3: C203.1, C204.1, R202.1, R203.1, R204.1, R205.1, U201.65 (VDD_GPIO)
VDD_NRF: C201.1, C202.1, FB201.2, U201.14 (VDD)
VSYS: FB201.1, R201.1

Notes on the sheet:
A · nRF9151 supply and antenna pins
VDD (pin 14) runs straight from VSYS (3.0-5.5 V). VDD_GPIO (pin 65) = V3 sets the logic level of every GPIO. ENABLE (pin 10) high = SiP regulator on; pulled up to VSYS as in the reference kit.
FB201: 0 R link - lift it and insert a PPK2 to measure the nRF alone (sleep-current work). C201/C202 at pin 14, C203/C204 at pin 65, C205 at DEC0 - values from the Nordic-based reference kit. AUX (37) and GPS (42) unused: GNSS not fitted (report 4.1).
B · Debug, SIM and coexistence pins
SWD is the only way in: it goes to the dock pads through the limiter cells (dock sheet). ~RESET: no external pull-up allowed (Nordic); brought to a test pad only. COEX0 goes high whenever the modem's RF is active; it is looped back to P0.29 so firmware can blank the grip sensor during transmit (AT%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
SIM_DET must float (Nordic). MAGPIO0-2, COEX1-2 and the MIPI RFFE pins are only for external antenna tuners - none fitted, so all unconnected.
C · GPIO map (32 of 32 used, 0 spare)
SPI + NOR + display on P0.00-P0.07 (far from the ANT pin). LED gates, DOCK_ID, COEX0 near the RF side are slow signals. No spare: P0.20 = touch INT (a polled touch driver would free it). Three I2C buses: main (P0.08/09), grip IQS211B (P0.12/18, RDY rides on its SCL), crown angle sensor (P0.31/19, p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
D · eSIM (MFF2 eUICC)
Soldered eSIM, wired directly as in the reference kit: no ESD or series parts (it never leaves the sealed body). C206 within 2 mm. Place within 10 mm of the SiP SIM pins. SIM supply is 1.8 V (SIM_1V8 from the nRF) -> the eUICC must be class C.
E · Open-drain pull-ups (to V3)
Main I2C bus (BQ25188, MAX17048, DRV2625): 4.7 k for 400 kHz. BQ_INT (128 us pulses) and GAUGE_ALRT are open-drain alerts: 10 k is enough.
F · Ground and reserved pins
30 GND pads: all to the solid L2/L5 planes with vias (report E-11). Reserved pads: solder them (mechanical/thermal) but never connect.
G · Firmware pin table (devicetree)
spi: SCK P0.00 MOSI P0.01 MISO P0.02 cs: DISP P0.03 NOR P0.05 DISP D/C P0.04 disp: TE P0.06 RESX P0.07 SW_A P0.22 PMIC_CTRL P0.23 CTP_INT P0.20 i2c: SDA P0.08 SCL P0.09 i2c_iqs: SCL/RDY P0.12 SDA P0.18 i2c_sens: SCL P0.19 SDA P0.31 irq: BQ P0.10 GAUGE P0.11 COEX0 P0.29 crown: HA1 P0.13 HA2 P0.14 HB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
Interfaces rails in: VSYS, V3 out: SIM_1V8 (local) RF: ANT_RF -> rf sheet debug: SWDIO_NRF, SWDCLK_NRF -> dock sheet, NRESET -> test points Refs 2xx [U] = part class chosen, MPN not final
