chiangr/bingbong/cad-v3/bingbong/power.kicad_sch

## KiCad design cad-v3/bingbong/power.kicad_sch (2026-09-28)

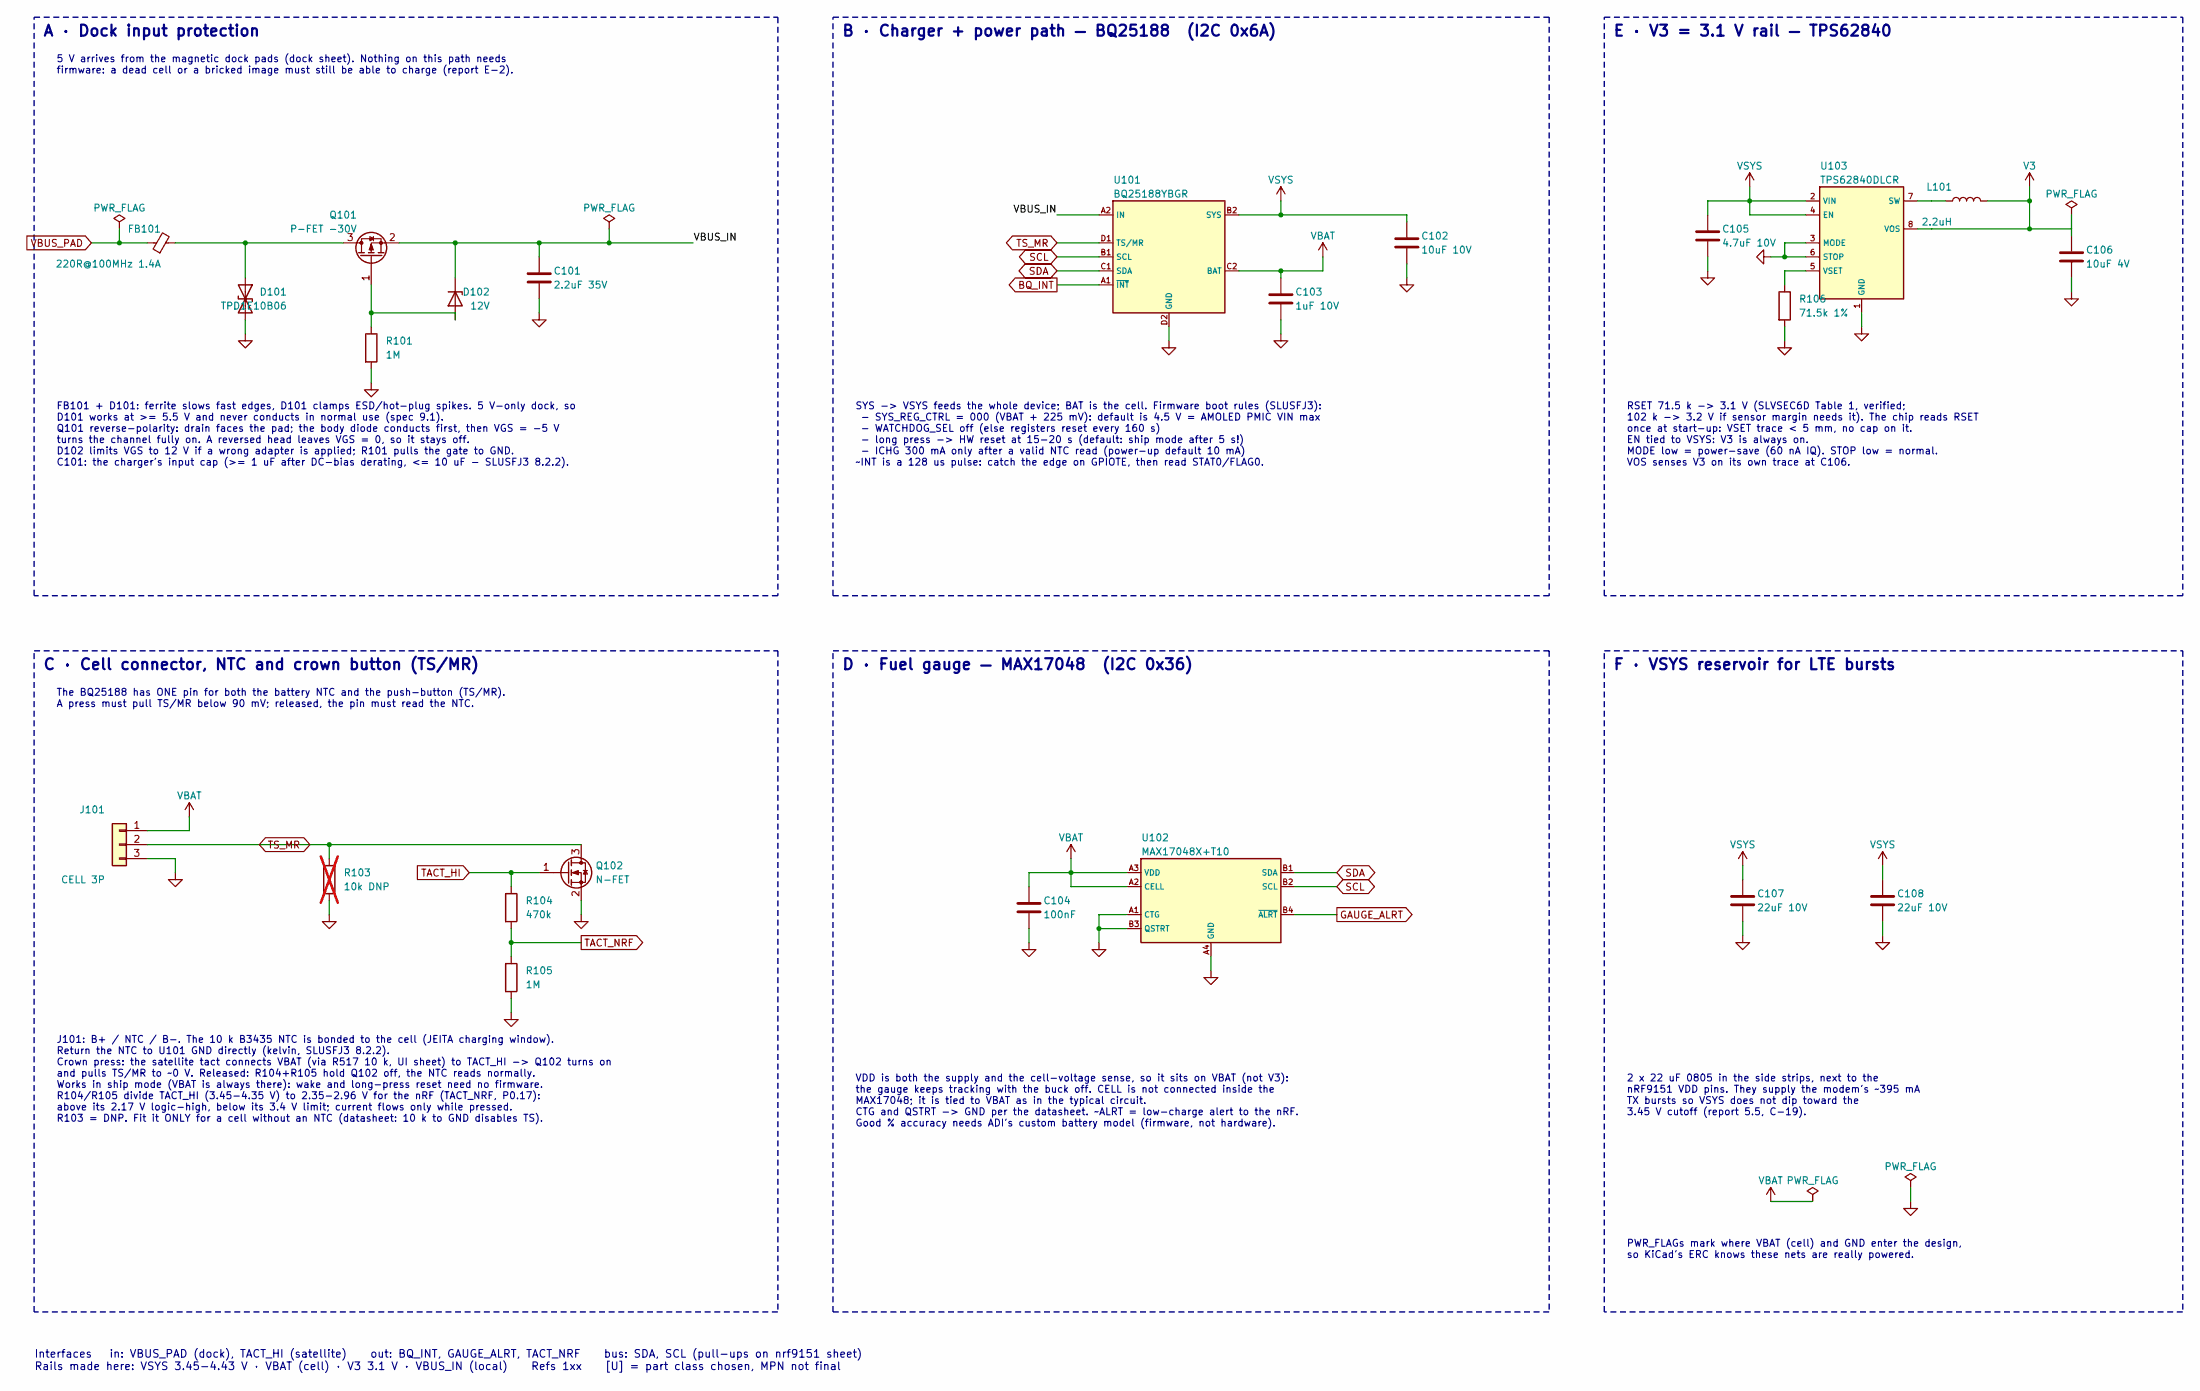
[picture p268: schematic power.kicad_sch]

Parts:
C101: 2.2uF 35V; C_0603_1608Metric; MPN >=1 uF effective at 5 V, 35 V X5R
C102: 10uF 10V; C_0603_1608Metric
C103: 1uF 10V; C_0402_1005Metric
C104: 100nF; C_0402_1005Metric
C105: 4.7uF 10V; C_0402_1005Metric; MPN GRM155R61A475MEAA
C106: 10uF 4V; C_0402_1005Metric; MPN GRM155R60G106ME44
C107, C108: 22uF 10V; C_0805_2012Metric
D101: TPD1E10B06; TI_DYA0002A_SOD-523; MPN TPD1E10B06DYAR
D102: 12V; Nexperia_SOD523; MPN Nexperia BZX585-C12
FB101: 220R@100MHz 1.4A; Murata_BLM18P_0603; MPN Murata BLM18PG221SN1D
J101: CELL 3P; CELL_B2B_3P_TBD; MPN cell 3-way B2B, pinout per cell vendor 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
L101: 2.2uH; L_Murata_DFE201210U; MPN DFE201210U-2R2M=P2
Q101: P-FET -30V; Diodes_SOT-23; MPN DMP3099L-7
Q102: N-FET; SOT-523; MPN DMG1012T-7 (IDSS 100 nA max, VGS +/-6 V)
R101, R105: 1M; R_0402_1005Metric
R103: 10k DNP; R_0402_1005Metric; not fitted
R104: 470k; R_0402_1005Metric
R106: 71.5k 1%; R_0402_1005Metric; MPN E96 1%, <=200 ppm/C
U101: BQ25188YBGR; TI_YBG0008_DSBGA-8; MPN BQ25188YBGR
U102: MAX17048X+T10; MAX_WLP-8_0.9x1.7; MPN MAX17048X+T10
U103: TPS62840DLCR; TI_DLC0008_SON-8_1.5x2; MPN TPS62840DLCR

Connections:
BQ_INT: U101.A1 (~INT)
GAUGE_ALRT: U102.B4 (~ALRT)
GND: C101.2, C102.2, C103.2, C104.2, C105.2, C106.2, C107.2, C108.2, D101.2 (A2), J101.3, Q102.2 (S), R101.2, R103.2, R105.2, R106.2, U101.D2 (GND), U102.A1 (CTG), U102.A4 (GND), U102.B3 (QSTRT), U103.1 (GND), U103.3 (MODE), U103.6 (STOP)
unnamed: D101.1 (A1), FB101.2, Q101.3 (D)
unnamed: D102.2 (A), Q101.1 (G), R101.1
unnamed: L101.1, U103.7 (SW)
unnamed: R106.1, U103.5 (VSET)
SCL: U101.B1 (SCL), U102.B2 (SCL)
SDA: U101.C1 (SDA), U102.B1 (SDA)
TACT_HI: Q102.1 (G), R104.1
TACT_NRF: R104.2, R105.1
TS_MR: J101.2, Q102.3 (D), R103.1, U101.D1 (TS/MR)
V3: C106.1, L101.2, U103.8 (VOS)
VBAT: C103.1, C104.1, J101.1, U101.C2 (BAT), U102.A2 (CELL), U102.A3 (VDD)
VBUS_IN: C101.1, D102.1 (K), Q101.2 (S), U101.A2 (IN)
VBUS_PAD: FB101.1
VSYS: C102.1, C105.1, C107.1, C108.1, U101.B2 (SYS), U103.2 (VIN), U103.4 (EN)

Notes on the sheet:
A · Dock input protection
5 V arrives from the magnetic dock pads (dock sheet). Nothing on this path needs firmware: a dead cell or a bricked image must still be able to charge (report E-2).
FB101 + D101: ferrite slows fast edges, D101 clamps ESD/hot-plug spikes. 5 V-only dock, so D101 works at >= 5.5 V and never conducts in normal use (spec 9.1). Q101 reverse-polarity: drain faces the pad; the body diode conducts first, then VGS = -5 V turns the channel fully on. A reversed head leave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
B · Charger + power path — BQ25188 (I2C 0x6A)
SYS -> VSYS feeds the whole device; BAT is the cell. Firmware boot rules (SLUSFJ3): - SYS_REG_CTRL = 000 (VBAT + 225 mV): default is 4.5 V = AMOLED PMIC VIN max - WATCHDOG_SEL off (else registers reset every 160 s) - long press -> HW reset at 15-20 s (default: ship mode after 5 s!) - ICHG 300 mA on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
E · V3 = 3.1 V rail — TPS62840
RSET 71.5 k -> 3.1 V (SLVSEC6D Table 1, verified; 102 k -> 3.2 V if sensor margin needs it). The chip reads RSET once at start-up: VSET trace < 5 mm, no cap on it. EN tied to VSYS: V3 is always on. MODE low = power-save (60 nA IQ). STOP low = normal. VOS senses V3 on its own trace at C106.
C · Cell connector, NTC and crown button (TS/MR)
The BQ25188 has ONE pin for both the battery NTC and the push-button (TS/MR). A press must pull TS/MR below 90 mV; released, the pin must read the NTC.
J101: B+ / NTC / B-. The 10 k B3435 NTC is bonded to the cell (JEITA charging window). Return the NTC to U101 GND directly (kelvin, SLUSFJ3 8.2.2). Crown press: the satellite tact connects VBAT (via R517 10 k, UI sheet) to TACT_HI -> Q102 turns on and pulls TS/MR to ~0 V. Released: R104+R105 hold Q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
D · Fuel gauge — MAX17048 (I2C 0x36)
VDD is both the supply and the cell-voltage sense, so it sits on VBAT (not V3): the gauge keeps tracking with the buck off. CELL is not connected inside the MAX17048; it is tied to VBAT as in the typical circuit. CTG and QSTRT -> GND per the datasheet. ~ALRT = low-charge alert to the nRF. Good % ac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
F · VSYS reservoir for LTE bursts
PWR_FLAGs mark where VBAT (cell) and GND enter the design, so KiCad's ERC knows these nets are really powered.
2 x 22 uF 0805 in the side strips, next to the nRF9151 VDD pins. They supply the modem's ~395 mA TX bursts so VSYS does not dip toward the 3.45 V cutoff (report 5.5, C-19).
Interfaces in: VBUS_PAD (dock), TACT_HI (satellite) out: BQ_INT, GAUGE_ALRT, TACT_NRF bus: SDA, SCL (pull-ups on nrf9151 sheet) Rails made here: VSYS 3.45-4.43 V · VBAT (cell) · V3 3.1 V · VBUS_IN (local) Refs 1xx [U] = part class chosen, MPN not final
