chiangr/bingbong/cad-v3/bingbong/rf.kicad_sch

## KiCad design cad-v3/bingbong/rf.kicad_sch (2026-09-28)

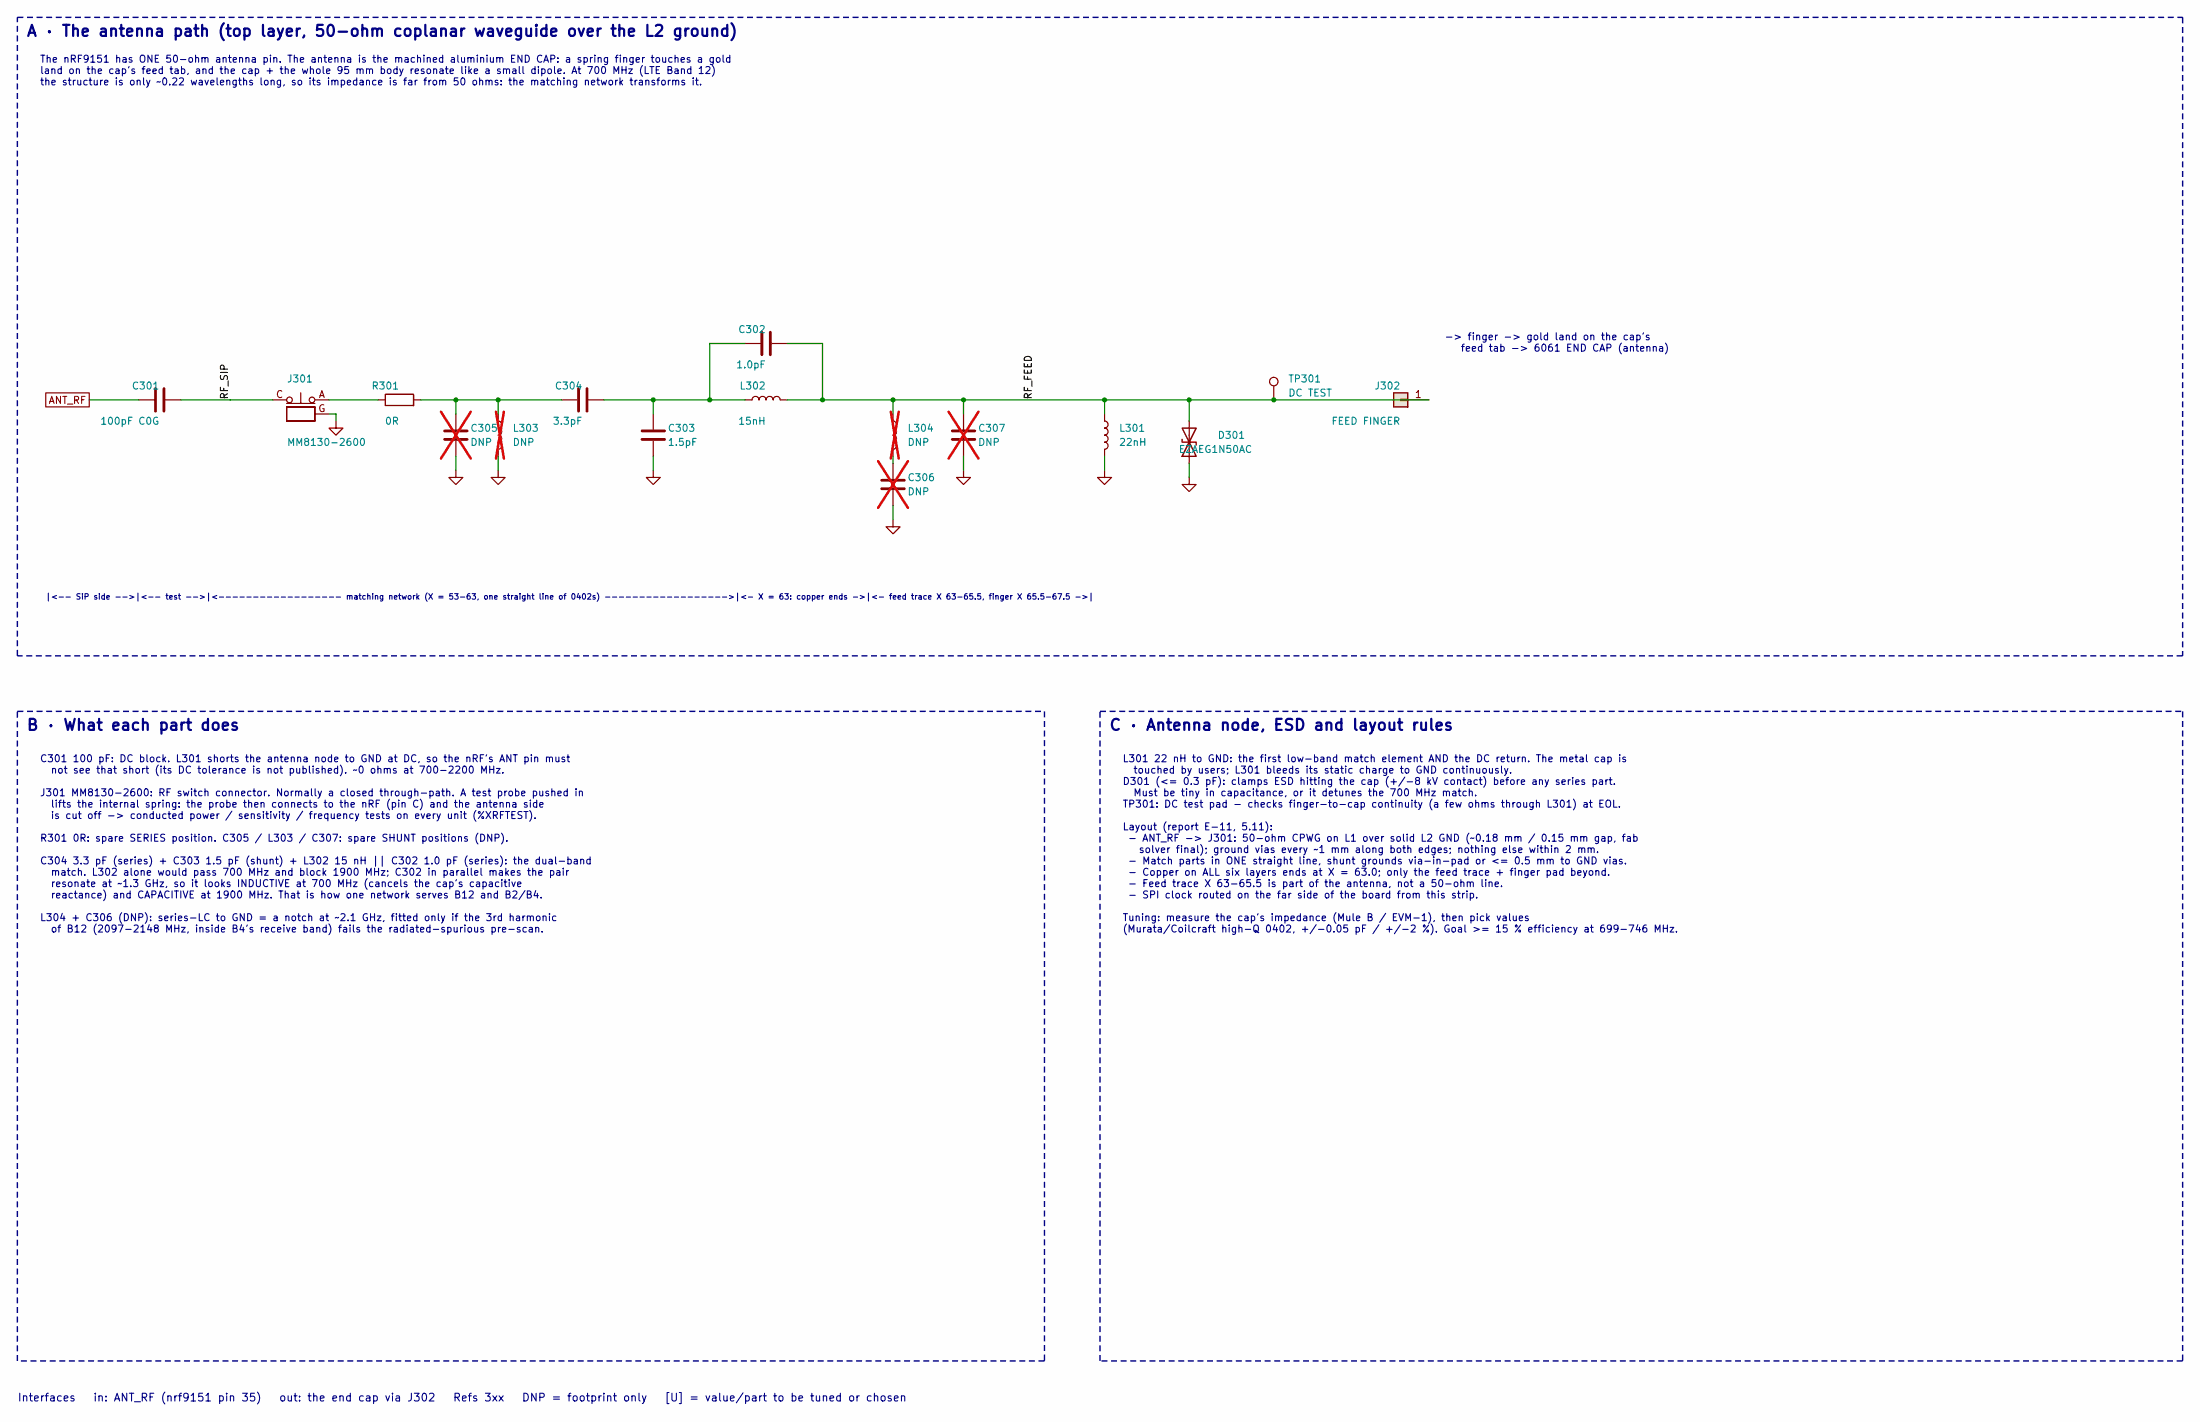
[picture p269: schematic rf.kicad_sch]

Parts:
C301: 100pF C0G; C_0402_1005Metric; MPN GJM1555C1H101 class
C302: 1.0pF; C_0402_1005Metric; MPN GJM1555C1H1R0WB01 class
C303: 1.5pF; C_0402_1005Metric; MPN GJM1555C1H1R5WB01 class
C304: 3.3pF; C_0402_1005Metric; MPN GJM1555C1H3R3WB01 class
C305: DNP; C_0402_1005Metric; MPN shunt trim C3 (high band); not fitted
C306: DNP; C_0402_1005Metric; MPN 2.1 GHz trap C; not fitted
C307: DNP; C_0402_1005Metric; MPN shunt spare; not fitted
D301: EZAEG1N50AC; Panasonic_EZAEG1N_0201; MPN Panasonic EZAEG1N50AC (0.04 pF, 30 V)
J301: MM8130-2600; Murata_MM8130-2600; MPN Murata MM8130-2600RA2
J302: FEED FINGER; Harwin_S7141-45R; MPN Harwin S7141-45R (2.5 mm free, 1.4-1.9 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
L301: 22nH; L_0402_1005Metric; MPN LQW15AN22NG class, rated for ESD residue
L302: 15nH; L_0402_1005Metric; MPN LQW15AN15NG class
L303: DNP; L_0402_1005Metric; MPN shunt trim L3 (alt.); not fitted
L304: DNP; L_0402_1005Metric; MPN 2.1 GHz trap L (fit only if spurious fa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; not fitted
R301: 0R; R_0402_1005Metric; MPN series spare: 0R now, L or C when tuning
TP301: DC TEST; TestPoint_Pad_D1.0mm

Connections:
ANT_RF: C301.1
GND: C303.2, C305.2, C306.2, C307.2, D301.1 (A1), J301.G, L301.2, L303.2
unnamed: C302.1, C303.1, C304.2, L302.1
unnamed: C304.1, C305.1, L303.1, R301.2
unnamed: C306.1, L304.2
unnamed: J301.A, R301.1
RF_FEED: C302.2, C307.1, D301.2 (A2), J302.1, L301.1, L302.2, L304.1, TP301.1
RF_SIP: C301.2, J301.C

Notes on the sheet:
A · The antenna path (top layer, 50-ohm coplanar waveguide over the L2 ground)
The nRF9151 has ONE 50-ohm antenna pin. The antenna is the machined aluminium END CAP: a spring finger touches a gold land on the cap's feed tab, and the cap + the whole 95 mm body resonate like a small dipole. At 700 MHz (LTE Band 12) the structure is only ~0.22 wavelengths long, so its impedance 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
-> finger -> gold land on the cap's feed tab -> 6061 END CAP (antenna)
|<-- SiP side -->|<-- test -->|<------------------ matching network (X = 53-63, one straight line of 0402s) ------------------>|<- X = 63: copper ends ->|<- feed trace X 63-65.5, finger X 65.5-67.5 ->|
B · What each part does
C301 100 pF: DC block. L301 shorts the antenna node to GND at DC, so the nRF's ANT pin must not see that short (its DC tolerance is not published). ~0 ohms at 700-2200 MHz. J301 MM8130-2600: RF switch connector. Normally a closed through-path. A test probe pushed in lifts the internal spring: the p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
C · Antenna node, ESD and layout rules
L301 22 nH to GND: the first low-band match element AND the DC return. The metal cap is touched by users; L301 bleeds its static charge to GND continuously. D301 (<= 0.3 pF): clamps ESD hitting the cap (+/-8 kV contact) before any series part. Must be tiny in capacitance, or it detunes the 700 MHz 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
Interfaces in: ANT_RF (nrf9151 pin 35) out: the end cap via J302 Refs 3xx DNP = footprint only [U] = value/part to be tuned or chosen
