chiangr/bingbong/cad-v3/bingbong/testpoints.kicad_sch

## KiCad design cad-v3/bingbong/testpoints.kicad_sch (2026-09-28)

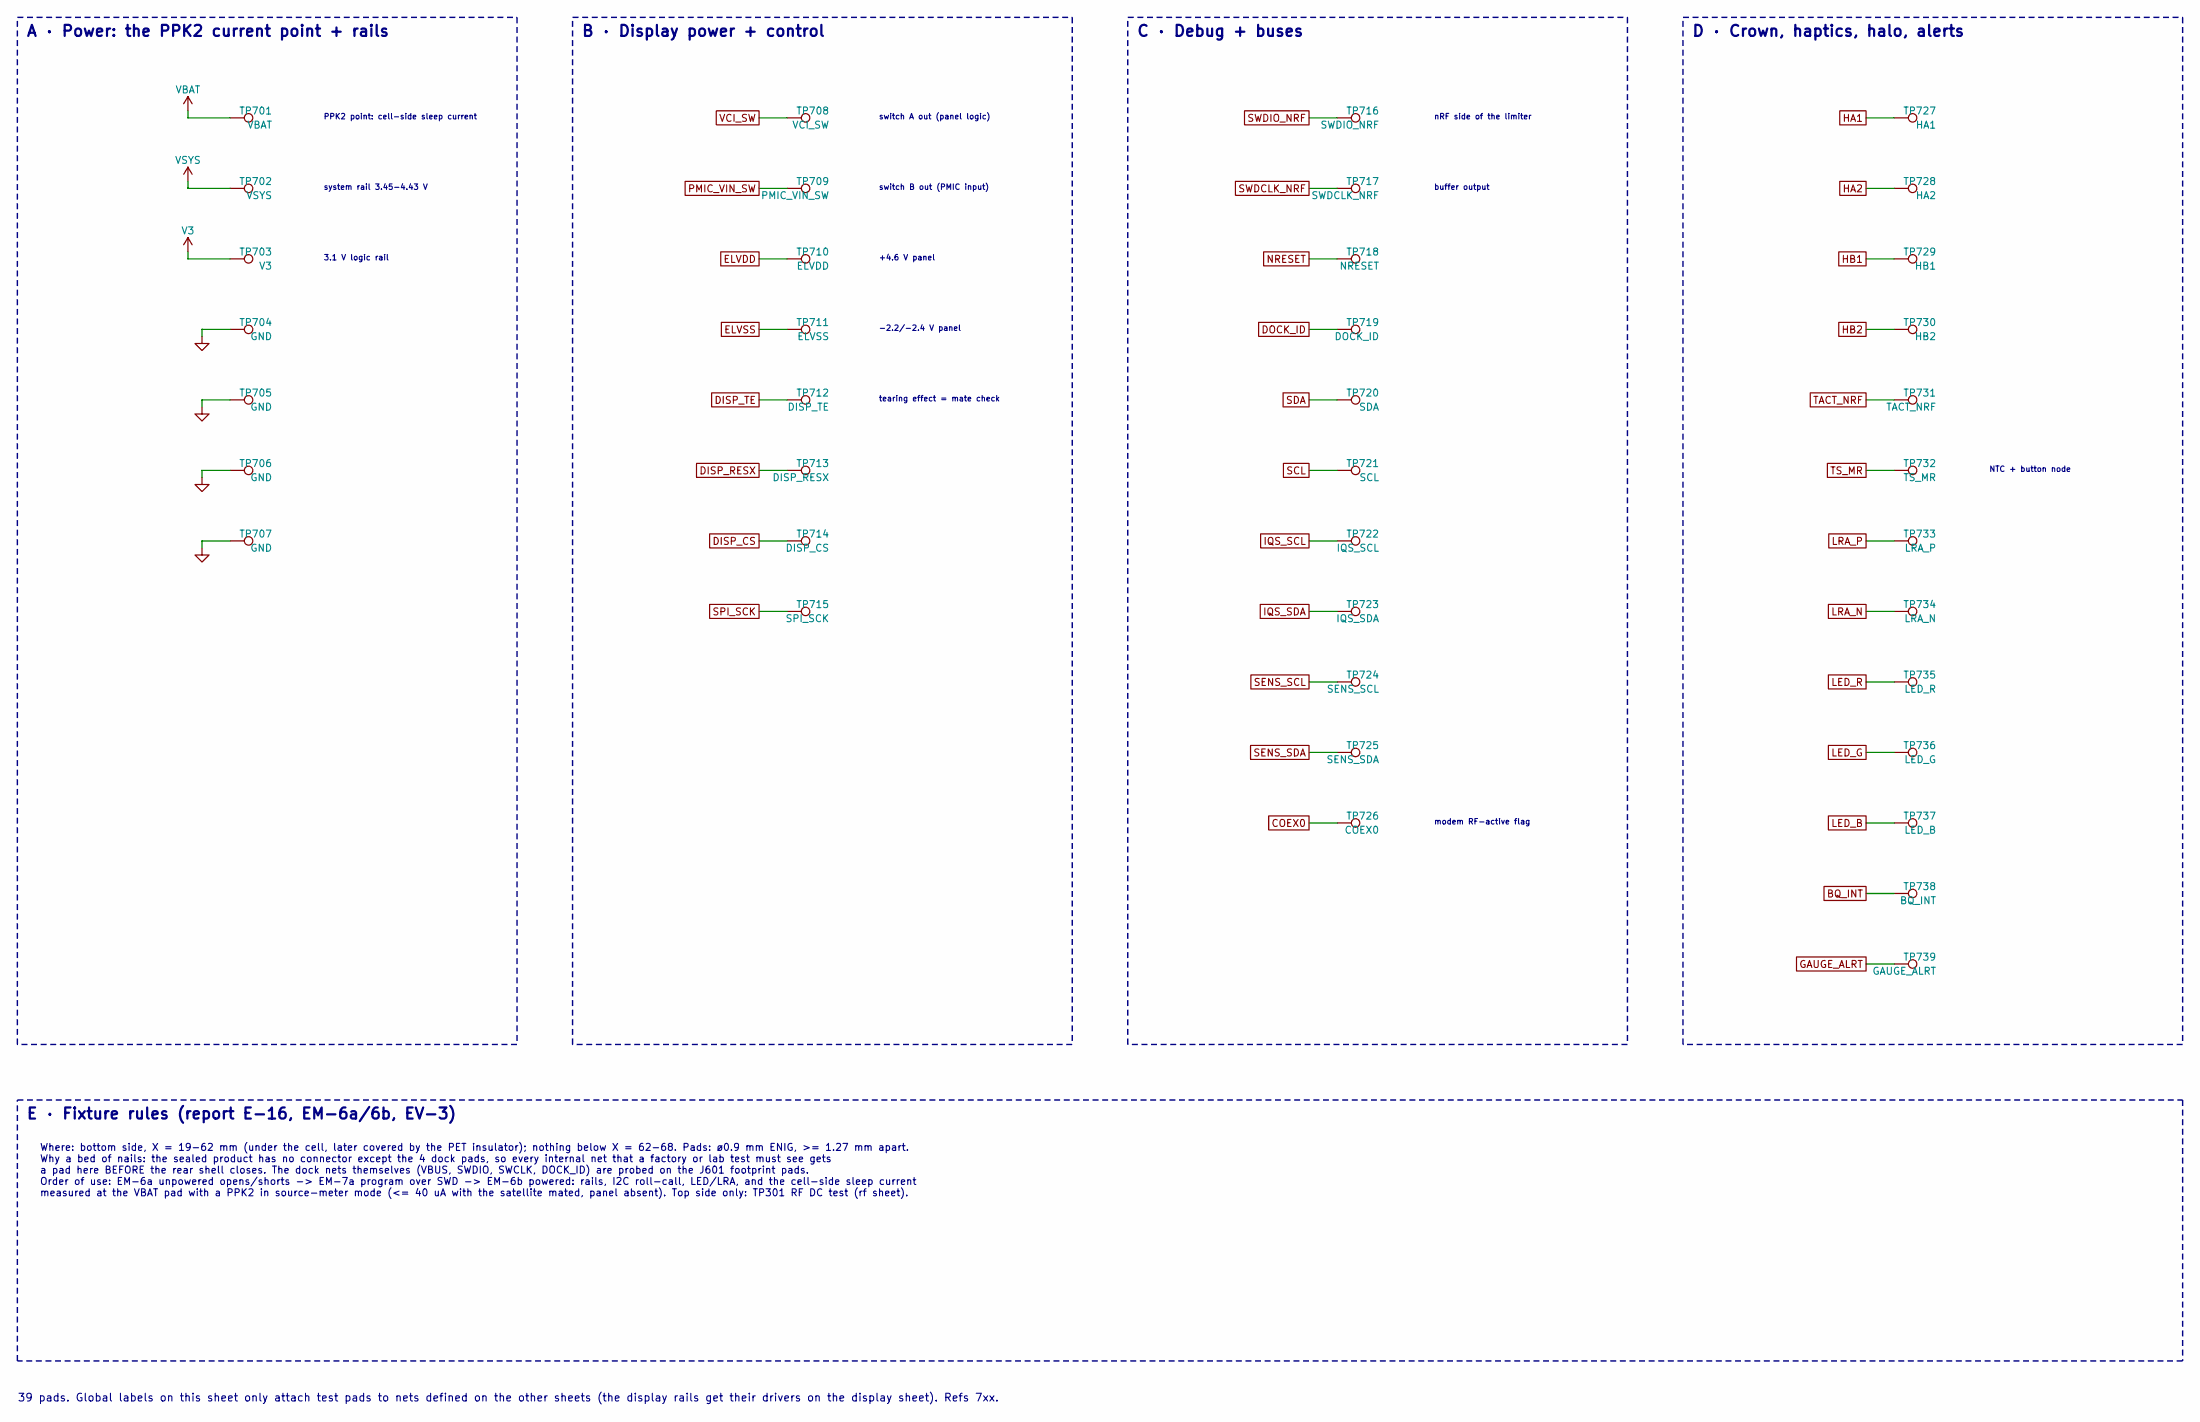
[picture p270: schematic testpoints.kicad_sch]

Parts:
TP701: VBAT; TestPoint_Pad_D0.9mm_ENIG
TP702: VSYS; TestPoint_Pad_D0.9mm_ENIG
TP703: V3; TestPoint_Pad_D0.9mm_ENIG
TP704, TP705, TP706, TP707: GND; TestPoint_Pad_D0.9mm_ENIG
TP708: VCI_SW; TestPoint_Pad_D0.9mm_ENIG
TP709: PMIC_VIN_SW; TestPoint_Pad_D0.9mm_ENIG
TP710: ELVDD; TestPoint_Pad_D0.9mm_ENIG
TP711: ELVSS; TestPoint_Pad_D0.9mm_ENIG
TP712: DISP_TE; TestPoint_Pad_D0.9mm_ENIG
TP713: DISP_RESX; TestPoint_Pad_D0.9mm_ENIG
TP714: DISP_CS; TestPoint_Pad_D0.9mm_ENIG
TP715: SPI_SCK; TestPoint_Pad_D0.9mm_ENIG
TP716: SWDIO_NRF; TestPoint_Pad_D0.9mm_ENIG
TP717: SWDCLK_NRF; TestPoint_Pad_D0.9mm_ENIG
TP718: NRESET; TestPoint_Pad_D0.9mm_ENIG
TP719: DOCK_ID; TestPoint_Pad_D0.9mm_ENIG
TP720: SDA; TestPoint_Pad_D0.9mm_ENIG
TP721: SCL; TestPoint_Pad_D0.9mm_ENIG
TP722: IQS_SCL; TestPoint_Pad_D0.9mm_ENIG
TP723: IQS_SDA; TestPoint_Pad_D0.9mm_ENIG
TP724: SENS_SCL; TestPoint_Pad_D0.9mm_ENIG
TP725: SENS_SDA; TestPoint_Pad_D0.9mm_ENIG
TP726: COEX0; TestPoint_Pad_D0.9mm_ENIG
TP727: HA1; TestPoint_Pad_D0.9mm_ENIG
TP728: HA2; TestPoint_Pad_D0.9mm_ENIG
TP729: HB1; TestPoint_Pad_D0.9mm_ENIG
TP730: HB2; TestPoint_Pad_D0.9mm_ENIG
TP731: TACT_NRF; TestPoint_Pad_D0.9mm_ENIG
TP732: TS_MR; TestPoint_Pad_D0.9mm_ENIG
TP733: LRA_P; TestPoint_Pad_D0.9mm_ENIG
TP734: LRA_N; TestPoint_Pad_D0.9mm_ENIG
TP735: LED_R; TestPoint_Pad_D0.9mm_ENIG
TP736: LED_G; TestPoint_Pad_D0.9mm_ENIG
TP737: LED_B; TestPoint_Pad_D0.9mm_ENIG
TP738: BQ_INT; TestPoint_Pad_D0.9mm_ENIG
TP739: GAUGE_ALRT; TestPoint_Pad_D0.9mm_ENIG

Connections:
BQ_INT: TP738.1
COEX0: TP726.1
DISP_CS: TP714.1
DISP_RESX: TP713.1
DISP_TE: TP712.1
DOCK_ID: TP719.1
ELVDD: TP710.1
ELVSS: TP711.1
GAUGE_ALRT: TP739.1
GND: TP704.1, TP705.1, TP706.1, TP707.1
HA1: TP727.1
HA2: TP728.1
HB1: TP729.1
HB2: TP730.1
IQS_SCL: TP722.1
IQS_SDA: TP723.1
LED_B: TP737.1
LED_G: TP736.1
LED_R: TP735.1
LRA_N: TP734.1
LRA_P: TP733.1
NRESET: TP718.1
PMIC_VIN_SW: TP709.1
SCL: TP721.1
SDA: TP720.1
SENS_SCL: TP724.1
SENS_SDA: TP725.1
SPI_SCK: TP715.1
SWDCLK_NRF: TP717.1
SWDIO_NRF: TP716.1
TACT_NRF: TP731.1
TS_MR: TP732.1
V3: TP703.1
VBAT: TP701.1
VCI_SW: TP708.1
VSYS: TP702.1

Notes on the sheet:
A · Power: the PPK2 current point + rails
PPK2 point: cell-side sleep current
system rail 3.45-4.43 V
3.1 V logic rail
B · Display power + control
switch A out (panel logic)
switch B out (PMIC input)
+4.6 V panel
-2.2/-2.4 V panel
tearing effect = mate check
C · Debug + buses
nRF side of the limiter
buffer output
modem RF-active flag
D · Crown, haptics, halo, alerts
NTC + button node
E · Fixture rules (report E-16, EM-6a/6b, EV-3)
Where: bottom side, X = 19-62 mm (under the cell, later covered by the PET insulator); nothing below X = 62-68. Pads: ø0.9 mm ENIG, >= 1.27 mm apart. Why a bed of nails: the sealed product has no connector except the 4 dock pads, so every internal net that a factory or lab test must see gets a pad 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
39 pads. Global labels on this sheet only attach test pads to nets defined on the other sheets (the display rails get their drivers on the display sheet). Refs 7xx.
