chiangr/bingbong/cad-v3/bingbong/ui.kicad_sch

## KiCad design cad-v3/bingbong/ui.kicad_sch (2026-10-02)

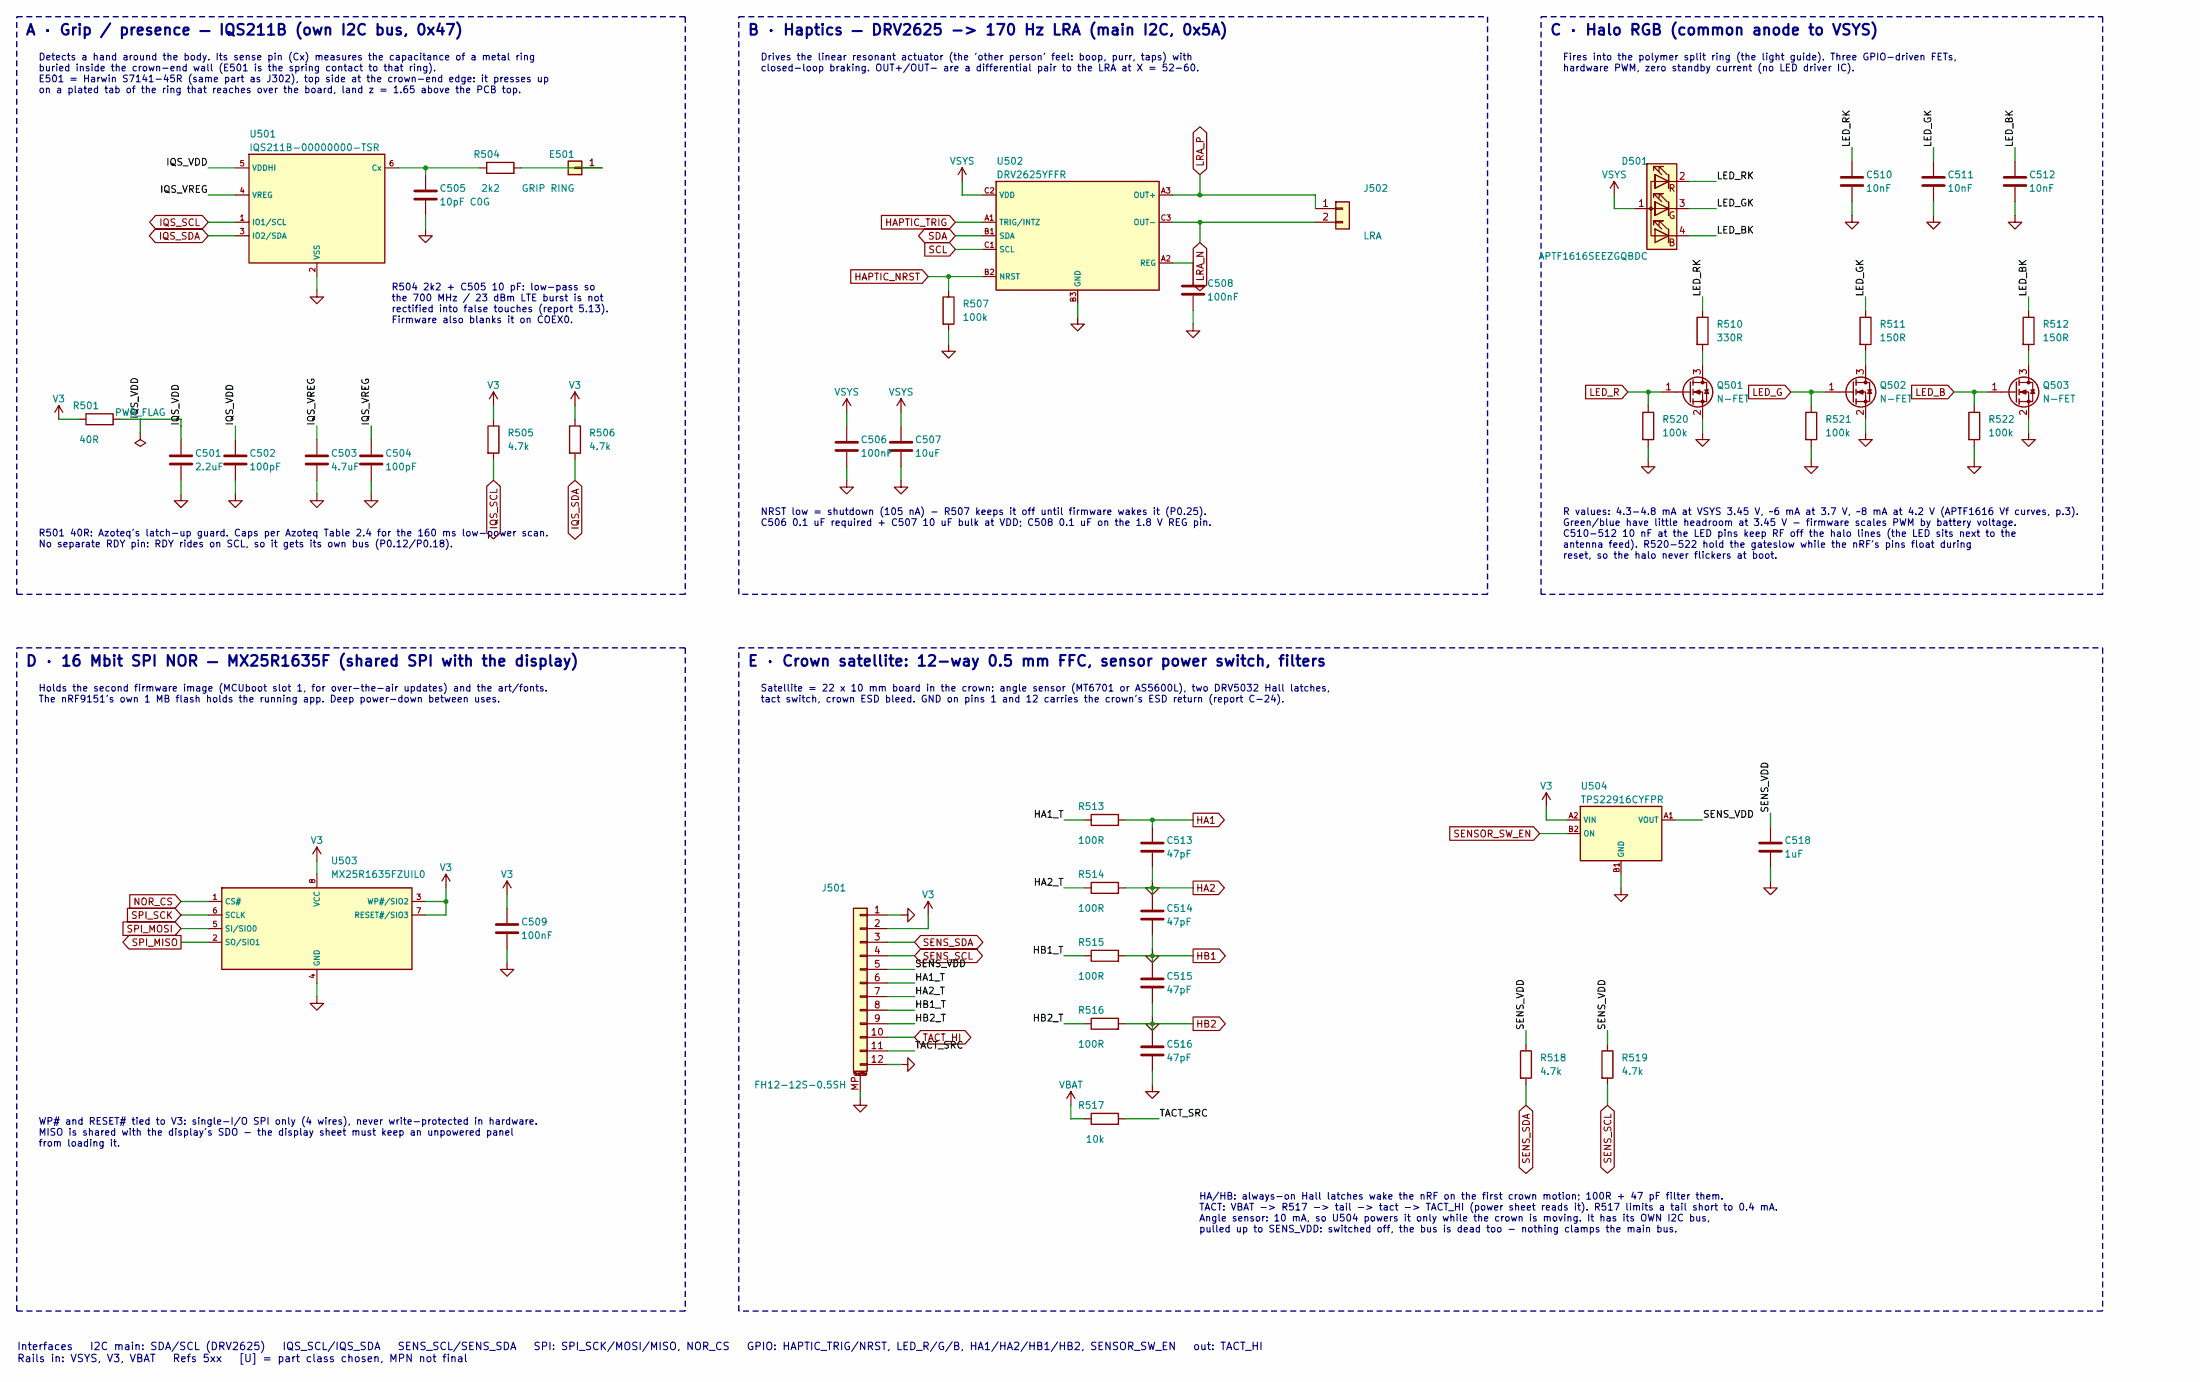
[picture p271: schematic ui.kicad_sch]

Parts:
C501: 2.2uF; C_0402_1005Metric
C502, C504: 100pF; C_0402_1005Metric
C503: 4.7uF; C_0402_1005Metric
C505: 10pF C0G; C_0402_1005Metric
C506, C508, C509: 100nF; C_0402_1005Metric
C507: 10uF; C_0603_1608Metric
C510, C511, C512: 10nF; C_0402_1005Metric
C513, C514, C515, C516: 47pF; C_0402_1005Metric
C518: 1uF; C_0402_1005Metric
D501: APTF1616SEEZGQBDC; LED_Kingbright_APTF1616; MPN Kingbright APTF1616SEEZGQBDC
E501: GRIP RING; Harwin_S7141-45R; MPN Harwin S7141-45R
J501: FH12-12S-0.5SH; Hirose_FH12-12S-0.5SH_1x12-1MP_P0.50mm_Horizontal; MPN Hirose FH12-12S-0.5SH(55)
J502: LRA; LRA_pads_TBD; MPN Vybronics VG0840001D leads
Q501, Q502, Q503: N-FET; SOT-523; MPN DMN26D0UT-7
R501: 40R; R_0402_1005Metric
R504: 2k2; R_0402_1005Metric
R505, R506, R518, R519: 4.7k; R_0402_1005Metric
R507, R520, R521, R522: 100k; R_0402_1005Metric
R510: 330R; R_0402_1005Metric
R511, R512: 150R; R_0402_1005Metric
R513, R514, R515, R516: 100R; R_0402_1005Metric
R517: 10k; R_0402_1005Metric
U501: IQS211B-00000000-TSR; TSOT-23-6; MPN IQS211B-00000000-TSR
U502: DRV2625YFFR; TI_YFF0009_DSBGA-9; MPN DRV2625YFFR
U503: MX25R1635FZUIL0; Macronix_USON-8_2x3; MPN MX25R1635FZUIL0
U504: TPS22916CYFPR; TI_YFP0004_WCSP-4; MPN TPS22916CYFPR

Connections:
GND: C501.2, C502.2, C503.2, C504.2, C505.2, C506.2, C507.2, C508.2, C509.2, C510.2, C511.2, C512.2, C513.2, C514.2, C515.2, C516.2, C518.2, J501.1, J501.12, J501.MP (MountPin), Q501.2 (S), Q502.2 (S), Q503.2 (S), R507.2, R520.2, R521.2, R522.2, U501.2 (VSS), U502.B3 (GND), U503.4 (GND), U504.B1 (GND)
HA1: C513.1, R513.2
HA1_T: J501.6, R513.1
HA2: C514.1, R514.2
HA2_T: J501.7, R514.1
HAPTIC_NRST: R507.1, U502.B2 (NRST)
HAPTIC_TRIG: U502.A1 (TRIG/INTZ)
HB1: C515.1, R515.2
HB1_T: J501.8, R515.1
HB2: C516.1, R516.2
HB2_T: J501.9, R516.1
IQS_SCL: R505.2, U501.1 (IO1/SCL)
IQS_SDA: R506.2, U501.3 (IO2/SDA)
IQS_VDD: C501.1, C502.1, R501.2, U501.5 (VDDHI)
IQS_VREG: C503.1, C504.1, U501.4 (VREG)
LED_B: Q503.1 (G), R522.1
LED_BK: C512.1, D501.4 (BK), R512.1
LED_G: Q502.1 (G), R521.1
LED_GK: C511.1, D501.3 (GK), R511.1
LED_R: Q501.1 (G), R520.1
LED_RK: C510.1, D501.2 (RK), R510.1
LRA_N: J502.2, U502.C3 (OUT-)
LRA_P: J502.1, U502.A3 (OUT+)
NOR_CS: U503.1 (CS#)
unnamed: C505.1, R504.1, U501.6 (Cx)
unnamed: C508.1, U502.A2 (REG)
unnamed: E501.1, R504.2
unnamed: Q501.3 (D), R510.2
unnamed: Q502.3 (D), R511.2
unnamed: Q503.3 (D), R512.2
SCL: U502.C1 (SCL)
SDA: U502.B1 (SDA)
SENSOR_SW_EN: U504.B2 (ON)
SENS_SCL: J501.4, R519.2
SENS_SDA: J501.3, R518.2
SENS_VDD: C518.1, J501.5, R518.1, R519.1, U504.A1 (VOUT)
SPI_MISO: U503.2 (SO/SIO1)
SPI_MOSI: U503.5 (SI/SIO0)
SPI_SCK: U503.6 (SCLK)
TACT_HI: J501.10
TACT_SRC: J501.11, R517.2
V3: C509.1, J501.2, R501.1, R505.1, R506.1, U503.3 (WP#/SIO2), U503.7 (RESET#/SIO3), U503.8 (VCC), U504.A2 (VIN)
VBAT: R517.1
VSYS: C506.1, C507.1, D501.1 (A), U502.C2 (VDD)

Notes on the sheet:
A · Grip / presence — IQS211B (own I2C bus, 0x47)
Detects a hand around the body. Its sense pin (Cx) measures the capacitance of a metal ring buried inside the crown-end wall (E501 is the spring contact to that ring). E501 = Harwin S7141-45R (same part as J302), top side at the crown-end edge: it presses up on a plated tab of the ring that reaches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
R504 2k2 + C505 10 pF: low-pass so the 700 MHz / 23 dBm LTE burst is not rectified into false touches (report 5.13). Firmware also blanks it on COEX0.
R501 40R: Azoteq's latch-up guard. Caps per Azoteq Table 2.4 for the 160 ms low-power scan. No separate RDY pin: RDY rides on SCL, so it gets its own bus (P0.12/P0.18).
B · Haptics — DRV2625 -> 170 Hz LRA (main I2C, 0x5A)
Drives the linear resonant actuator (the 'other person' feel: boop, purr, taps) with closed-loop braking. OUT+/OUT- are a differential pair to the LRA at X = 52-60.
NRST low = shutdown (105 nA) - R507 keeps it off until firmware wakes it (P0.25). C506 0.1 uF required + C507 10 uF bulk at VDD; C508 0.1 uF on the 1.8 V REG pin.
C · Halo RGB (common anode to VSYS)
Fires into the polymer split ring (the light guide). Three GPIO-driven FETs, hardware PWM, zero standby current (no LED driver IC).
R values: 4.3-4.8 mA at VSYS 3.45 V, ~6 mA at 3.7 V, ~8 mA at 4.2 V (APTF1616 Vf curves, p.3). Green/blue have little headroom at 3.45 V - firmware scales PWM by battery voltage. C510-512 10 nF at the LED pins keep RF off the halo lines (the LED sits next to the antenna feed). R520-522 hold the gat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
D · 16 Mbit SPI NOR — MX25R1635F (shared SPI with the display)
Holds the second firmware image (MCUboot slot 1, for over-the-air updates) and the art/fonts. The nRF9151's own 1 MB flash holds the running app. Deep power-down between uses.
WP# and RESET# tied to V3: single-I/O SPI only (4 wires), never write-protected in hardware. MISO is shared with the display's SDO - the display sheet must keep an unpowered panel from loading it.
E · Crown satellite: 12-way 0.5 mm FFC, sensor power switch, filters
Satellite = 22 x 10 mm board in the crown: angle sensor (MT6701 or AS5600L), two DRV5032 Hall latches, tact switch, crown ESD bleed. GND on pins 1 and 12 carries the crown's ESD return (report C-24).
HA/HB: always-on Hall latches wake the nRF on the first crown motion; 100R + 47 pF filter them. TACT: VBAT -> R517 -> tail -> tact -> TACT_HI (power sheet reads it). R517 limits a tail short to 0.4 mA. Angle sensor: 10 mA, so U504 powers it only while the crown is moving. It has its OWN I2C bus, pu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
Interfaces I2C main: SDA/SCL (DRV2625) IQS_SCL/IQS_SDA SENS_SCL/SENS_SDA SPI: SPI_SCK/MOSI/MISO, NOR_CS GPIO: HAPTIC_TRIG/NRST, LED_R/G/B, HA1/HA2/HB1/HB2, SENSOR_SW_EN out: TACT_HI Rails in: VSYS, V3, VBAT Refs 5xx [U] = part class chosen, MPN not final
