chiangr/bingbong/cad-v3/satellite/satellite.kicad_sch

## KiCad design cad-v3/satellite/satellite.kicad_sch (2026-09-28)

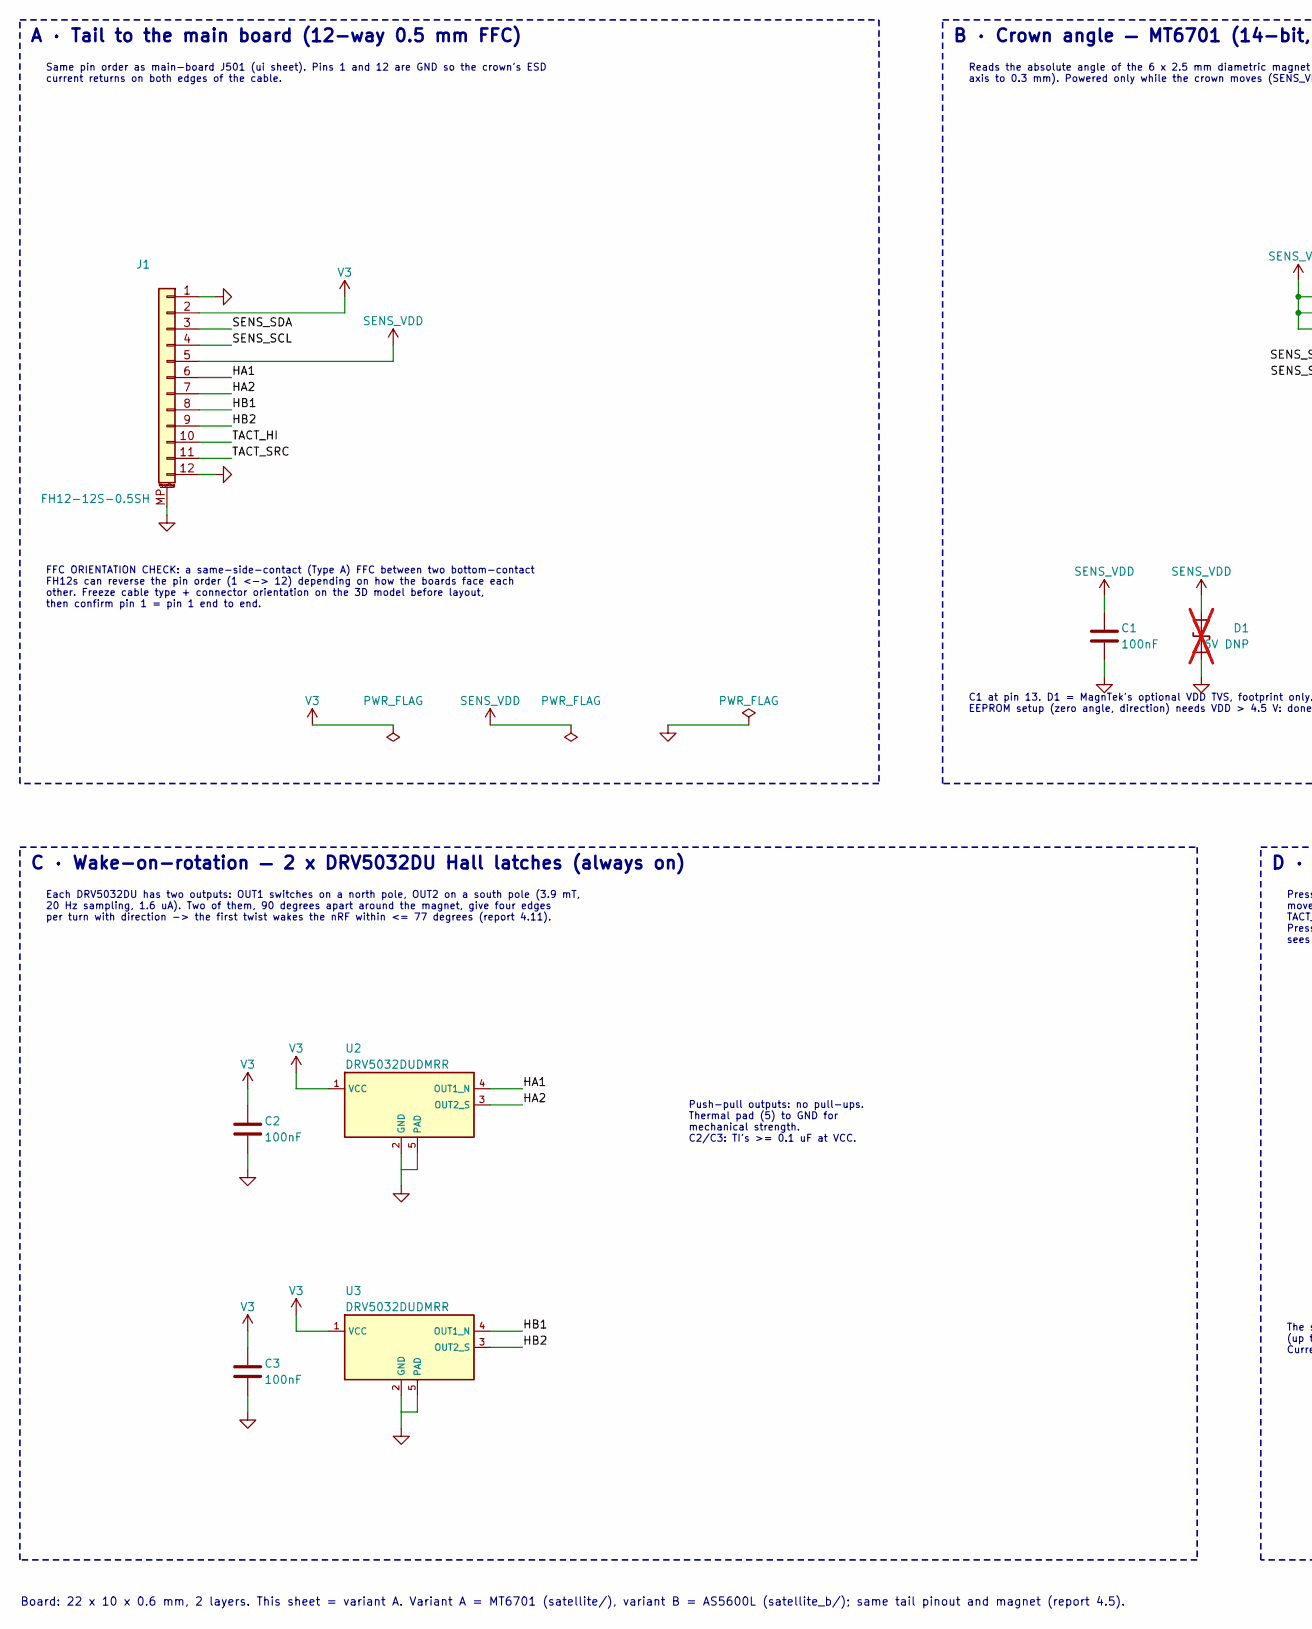
[picture p272: schematic satellite.kicad_sch, part in row 1, column 1]

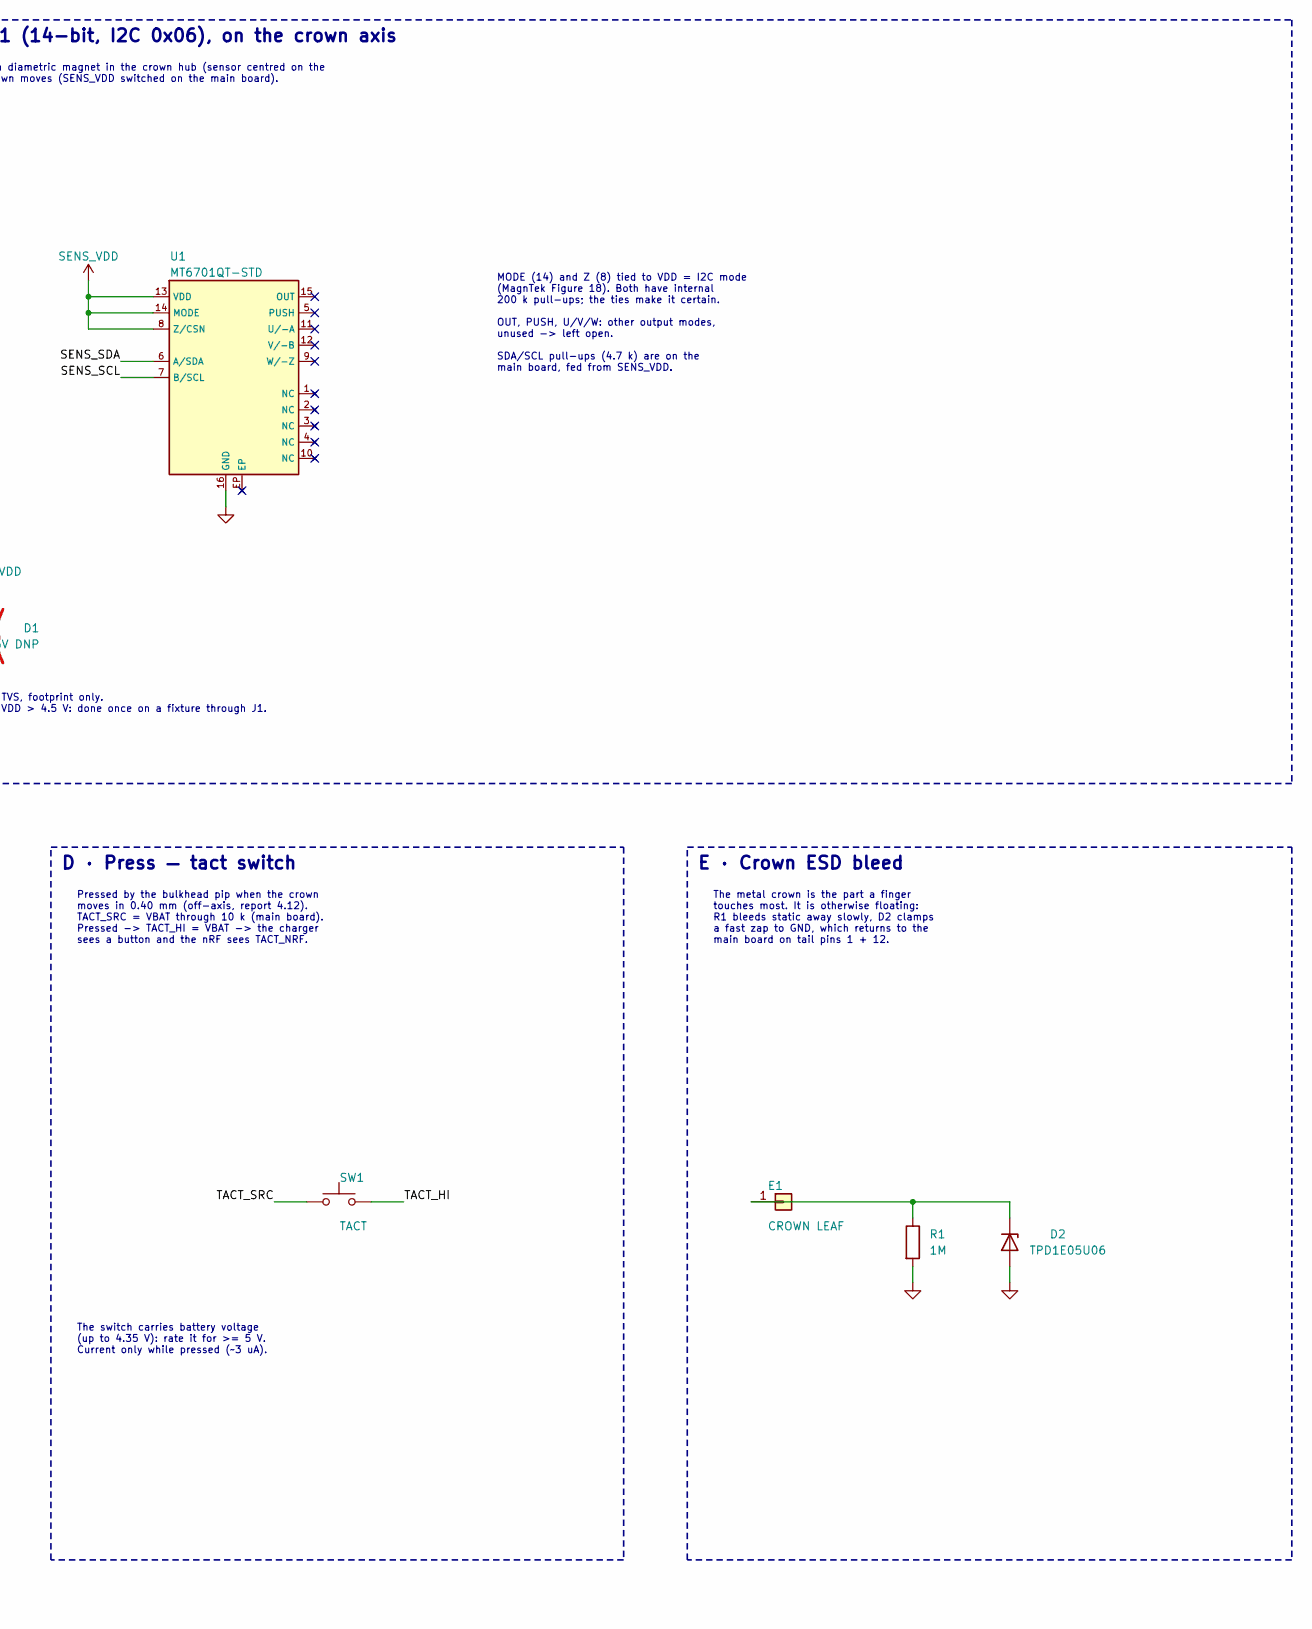
[picture p273: schematic satellite.kicad_sch, part in row 1, column 2]

Parts:
C1, C2, C3: 100nF; C_0402_1005Metric
D1: 6V DNP; D_SOD-523; MPN 6 V TVS, MagnTek 'recommended' [U]; not fitted
D2: TPD1E05U06; TI_DYA0002A_SOD-523; MPN TPD1E05U06DYAR
E1: CROWN LEAF; BeCu_leaf_pad_TBD; MPN BeCu leaf in the sleeve, touches the cr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
J1: FH12-12S-0.5SH; Hirose_FH12-12S-0.5SH_1x12-1MP_P0.50mm_Horizontal; MPN Hirose FH12-12S-0.5SH(55)
R1: 1M; R_0402_1005Metric
SW1: TACT; SW_Panasonic_EVPBB_TBD; MPN SMD tact >= 1.6 N, >= 300k cycles [U]
U1: MT6701QT-STD; QFN-16_3x3_MT6701; MPN MT6701QT-STD
U2, U3: DRV5032DUDMRR; TI_DMR0004_X2SON-4; MPN DRV5032DUDMRR

Connections:
GND: C1.2, C2.2, C3.2, D1.1 (A1), D2.2 (A), J1.1, J1.12, J1.MP (MountPin), R1.2, U1.16 (GND), U2.2 (GND), U2.5 (PAD), U3.2 (GND), U3.5 (PAD)
HA1: J1.6, U2.4 (OUT1_N)
HA2: J1.7, U2.3 (OUT2_S)
HB1: J1.8, U3.4 (OUT1_N)
HB2: J1.9, U3.3 (OUT2_S)
unnamed: D2.1 (K), E1.1, R1.1
SENS_SCL: J1.4, U1.7 (B/SCL)
SENS_SDA: J1.3, U1.6 (A/SDA)
SENS_VDD: C1.1, D1.2 (A2), J1.5, U1.8 (Z/CSN), U1.13 (VDD), U1.14 (MODE)
TACT_HI: J1.10, SW1.2
TACT_SRC: J1.11, SW1.1
V3: C2.1, C3.1, J1.2, U2.1 (VCC), U3.1 (VCC)

Notes on the sheet:
A · Tail to the main board (12-way 0.5 mm FFC)
Same pin order as main-board J501 (ui sheet). Pins 1 and 12 are GND so the crown's ESD current returns on both edges of the cable.
FFC ORIENTATION CHECK: a same-side-contact (Type A) FFC between two bottom-contact FH12s can reverse the pin order (1 <-> 12) depending on how the boards face each other. Freeze cable type + connector orientation on the 3D model before layout, then confirm pin 1 = pin 1 end to end.
B · Crown angle — MT6701 (14-bit, I2C 0x06), on the crown axis
Reads the absolute angle of the 6 x 2.5 mm diametric magnet in the crown hub (sensor centred on the axis to 0.3 mm). Powered only while the crown moves (SENS_VDD switched on the main board).
MODE (14) and Z (8) tied to VDD = I2C mode (MagnTek Figure 18). Both have internal 200 k pull-ups; the ties make it certain. OUT, PUSH, U/V/W: other output modes, unused -> left open. SDA/SCL pull-ups (4.7 k) are on the main board, fed from SENS_VDD.
C1 at pin 13. D1 = MagnTek's optional VDD TVS, footprint only. EEPROM setup (zero angle, direction) needs VDD > 4.5 V: done once on a fixture through J1.
C · Wake-on-rotation — 2 x DRV5032DU Hall latches (always on)
Each DRV5032DU has two outputs: OUT1 switches on a north pole, OUT2 on a south pole (3.9 mT, 20 Hz sampling, 1.6 uA). Two of them, 90 degrees apart around the magnet, give four edges per turn with direction -> the first twist wakes the nRF within <= 77 degrees (report 4.11).
Push-pull outputs: no pull-ups. Thermal pad (5) to GND for mechanical strength. C2/C3: TI's >= 0.1 uF at VCC.
D · Press — tact switch
Pressed by the bulkhead pip when the crown moves in 0.40 mm (off-axis, report 4.12). TACT_SRC = VBAT through 10 k (main board). Pressed -> TACT_HI = VBAT -> the charger sees a button and the nRF sees TACT_NRF.
The switch carries battery voltage (up to 4.35 V): rate it for >= 5 V. Current only while pressed (~3 uA).
E · Crown ESD bleed
The metal crown is the part a finger touches most. It is otherwise floating: R1 bleeds static away slowly, D2 clamps a fast zap to GND, which returns to the main board on tail pins 1 + 12.
Board: 22 x 10 x 0.6 mm, 2 layers. This sheet = variant A. Variant A = MT6701 (satellite/), variant B = AS5600L (satellite_b/); same tail pinout and magnet (report 4.5).
